amertner/cardcascade/CATALOGUE.md

# Card Cascade catalogue

Every Card Cascade there is, at release **8.0**: 26 designs, each in an
unsleeved and a sleeved version. This page is generated from the CAD
(`make_catalogue.py`), so the sizes and capacities are the ones the parts are
built to.

A Card Cascade is a 3D-printed **store-and-play** box for a card game. Closed,
it is a labelled box on a shelf. Open, its sliding card holders rise in a
staircase so that every pile shows its top card, ready to play, with the big
piles in front pockets. Each cascade is a complete Bambu Studio project: box
and pushers, lid with the game's logo, sliding holders, an optional token
holder, and slide-in labels as a separate project.

## Does one fit your game?

The cascades were designed for four card sizes, one family each. A cascade
fits a game it was never designed for when:

1. **The card is no bigger than the family's card.** The slots are cut for the
   card sizes below (the slot is 3 mm wider than the card, so a card up to
   about 1 mm wider still slides). Cards may be smaller; they just sit lower
   in the slot.
2. **The cards are no thicker.** Capacities are counted at the thickness
   below. Thicker cards mean fewer per slot, not a jam: a slot holding 10
   cards at 0.38 mm holds about 7 at 0.55 mm.
3. **The pile count fits the slots.** One pile per slot, a big pile per front
   pocket: pick a cascade with at least as many slots as you have piles.
4. **It fits your printer.** Every project is laid out for a named bed; a
   cascade for a 256 mm bed prints on anything larger.

## Families by card size

| Family | Unsleeved card, up to | Sleeved card, up to | Card thickness the capacities assume | Box height | Designed for | Files |
|---|---|---|---|---|---|---|
| **Dominion** | 60 x 89 mm | 62 x 92 mm | 0.38 mm unsleeved, 0.60 mm sleeved | 105 mm | Dominion and every expansion; any game with the same 59 x 91 mm card | [MakerWorld](https://makerworld.com/en/models/2957494-card-cascade-dominion-store-play-system) |
| **Food Chain Magnate** | 60 x 89 mm | 62 x 92 mm | 0.38 mm unsleeved, 0.60 mm sleeved | 105 mm | Food Chain Magnate and The Ketchup Mechanism; any game with a 58 x 88 mm card | [MakerWorld](https://makerworld.com/en/models/3053860-food-chain-magnate-card-cascade-system) |
| **Innovation** | 64 x 89 mm | 66 x 92 mm | 0.40 mm unsleeved, 0.65 mm sleeved | 105 mm | Innovation (Ultimate edition and the older ones); any game with a 63 x 88 mm card | [MakerWorld](https://makerworld.com/en/models/3192197-card-cascade-for-innovation-ultimate) |
| **Compile** | 65 x 89 mm | 67 x 92 mm | 0.40 mm unsleeved, 0.80 mm sleeved | 105 mm | Compile: Main 1 and its expansions; any game with a 65 x 92 mm card | [MakerWorld](https://makerworld.com/en/models/3042334-compile-main-aux-system-card-cascade) |

## Dominion

The original family, one cascade per expansion. Kingdom cards go ten to a sliding slot and the front pockets take the big piles (Copper, Curses, Estates). Some boxes merge two front pockets for player mats and every box takes a removable token holder.

| Cascade | Cards | Slots (across x deep) | Cards per slot (pocket / sliding) | Unsleeved: W x D x H mm | Model | Sleeved: W x D x H mm | Model | Printer | Made for | Print profile |
|---|---|---|---|---|---|---|---|---|---|---|
| **168 Card** | 168 | 3 x 5 | 16 / 10 | 208 x 43.6 x 107 | `S4.16.10.32-Un` | 214 x 55.9 x 107 | `S4.16.10.32-Sl` | 256 mm bed (Bambu P1/X1/A1 or similar) | Alchemy, Cornucopia, Guilds | [unsleeved](https://makerworld.com/en/models/2957494-card-cascade-dominion-store-play-system#profileId-3338100) / [sleeved](https://makerworld.com/en/models/2957494-card-cascade-dominion-store-play-system#profileId-3319634) |
| **202 Card (Mat)** | 202 | 4 x 5 | 21 / 10 | 271 x 45.5 x 107 | `M4.21.10.32-M-Un` | 279 x 58.9 x 107 | `M4.21.10.45-M-Sl` | 256 mm bed (Bambu P1/X1/A1 or similar) | Half of a mat expansion, with the mat slot (pairs with a 244 Card) | [unsleeved](https://makerworld.com/en/models/2957494-card-cascade-dominion-store-play-system#profileId-3408201) / [sleeved](https://makerworld.com/en/models/2957494-card-cascade-dominion-store-play-system#profileId-3408188) |
| **244 Card** | 244 | 4 x 5 | 21 / 10 | 271 x 45.5 x 107 | `M4.21.10.32-Un` | 279 x 58.9 x 107 | `M4.21.10.45-Sl` | 256 mm bed (Bambu P1/X1/A1 or similar) | Half of Adventures, Nocturne or Plunder on a 256 mm bed | [unsleeved](https://makerworld.com/en/models/2957494-card-cascade-dominion-store-play-system#profileId-3339013) / [sleeved](https://makerworld.com/en/models/2957494-card-cascade-dominion-store-play-system#profileId-3319882) |
| **246 Card** | 246 | 3 x 3 | 40 / 12/30 | 208 x 48.7 x 107 | `S2.40.12-30.32-Un` | 214 x 66.7 x 107 | `S2.40.12-30.45-Sl` | 256 mm bed (Bambu P1/X1/A1 or similar) | Just the bulky Base Set cards | [unsleeved](https://makerworld.com/en/models/2957494-card-cascade-dominion-store-play-system#profileId-3408409) / [sleeved](https://makerworld.com/en/models/2957494-card-cascade-dominion-store-play-system#profileId-3378738) |
| **290 Card (Mat)** | 290 | 4 x 7 | 21 / 10/12 | 271 x 58.7 x 107 | `M6.21.10-12.45-M-Un` | 279 x 76.9 x 107 | `M6.21.10-12.62-M-Sl` | 256 mm bed (Bambu P1/X1/A1 or similar) | Speculation, with a mat slot | [unsleeved](https://makerworld.com/en/models/2957494-card-cascade-dominion-store-play-system#profileId-3758638) / [sleeved](https://makerworld.com/en/models/2957494-card-cascade-dominion-store-play-system#profileId-3758631) |
| **300 Card** | 300 | 3 x 6 | 40 / 12 | 208 x 62.7 x 107 | `S5.40.12.45-Un` | 214 x 84.7 x 107 | `S5.40.12.62-Sl` | 256 mm bed (Bambu P1/X1/A1 or similar) | Half of the Base Set on a 256 mm bed | [unsleeved](https://makerworld.com/en/models/2957494-card-cascade-dominion-store-play-system#profileId-3338707) / [sleeved](https://makerworld.com/en/models/2957494-card-cascade-dominion-store-play-system#profileId-3338690) |
| **324 Card** | 324 | 4 x 7 | 21 / 10 | 271 x 57.9 x 107 | `M6.21.10.45-Un` | 279 x 75.7 x 107 | `M6.21.10.62-Sl` | 256 mm bed (Bambu P1/X1/A1 or similar) | Intrigue, Seaside, Prosperity, Hinterlands, Empires, Rising Sun | [unsleeved](https://makerworld.com/en/models/2957494-card-cascade-dominion-store-play-system#profileId-3338033) / [sleeved](https://makerworld.com/en/models/2957494-card-cascade-dominion-store-play-system#profileId-3319592) |
| **333 Card** | 333 | 3 x 10 | 21 / 10 | 208 x 76.5 x 107 | `S9.21.10.62-Un` | 214 x 100.9 x 107 | `S9.21.10.62-Sl` | 256 mm bed (Bambu P1/X1/A1 or similar) | A 324-size expansion in a narrower, deeper box for small printers | [unsleeved](https://makerworld.com/en/models/2957494-card-cascade-dominion-store-play-system#profileId-3431683) / [sleeved](https://makerworld.com/en/models/2957494-card-cascade-dominion-store-play-system#profileId-3431676) |
| **400 Card (Mat)** | 400 | 4 x 9 | 40 / 10 | 271 x 77.5 x 107 | `M8.40.10.62-M-Un` | 279 x 103.9 x 107 | `M8.40.10.62-M-Sl` | 256 mm bed unsleeved; 325 x 320 mm bed sleeved | Adventures, Renaissance, Menagerie, Allies | [unsleeved](https://makerworld.com/en/models/2957494-card-cascade-dominion-store-play-system#profileId-3339141) / [sleeved](https://makerworld.com/en/models/2957494-card-cascade-dominion-store-play-system#profileId-3319830) |
| **472 Card** | 472 | 4 x 3 | 60 / 18/40 | 271 x 62.4 x 107 | `M2.60.18-40.45-Un` | 279 x 88.3 x 107 | `M2.60.18-40.62-Sl` | 256 mm bed unsleeved; 325 x 320 mm bed sleeved | Base cards for six players | [unsleeved](https://makerworld.com/en/models/2957494-card-cascade-dominion-store-play-system#profileId-3460482) / [sleeved](https://makerworld.com/en/models/2957494-card-cascade-dominion-store-play-system#profileId-3460478) |
| **560 Card** | 560 | 5 x 7 | 40 / 12 | 334 x 69.7 x 107 | `L6.40.12.45-Un` | 344 x 94.3 x 107 | `L6.40.12.62-Sl` | 325 x 320 mm bed (Bambu H2 series or similar) | Base game | [unsleeved](https://makerworld.com/en/models/2957494-card-cascade-dominion-store-play-system#profileId-3337942) / [sleeved](https://makerworld.com/en/models/2957494-card-cascade-dominion-store-play-system#profileId-3314508) |
| **650 Card** | 650 | 5 x 9 | 50 / 10 | 334 x 81.3 x 107 | `L8.50.10.62-Un` | 344 x 109.9 x 107 | `L8.50.10.62-Sl` | 325 x 320 mm bed (Bambu H2 series or similar) | Dark Ages, Nocturne, Plunder | [unsleeved](https://makerworld.com/en/models/2957494-card-cascade-dominion-store-play-system#profileId-3337884) / [sleeved](https://makerworld.com/en/models/2957494-card-cascade-dominion-store-play-system#profileId-3319758) |

## Food Chain Magnate

Sized for FCM's employee cards: shallow slots (six cards) for the many small piles, and the Milestones box is a separate cascade. The slot is the same width as Dominion's, so any 58-60 mm card fits.

| Cascade | Cards | Slots (across x deep) | Cards per slot (pocket / sliding) | Unsleeved: W x D x H mm | Model | Sleeved: W x D x H mm | Model | Printer | Made for | Print profile |
|---|---|---|---|---|---|---|---|---|---|---|
| **144 Card (Milestones 1)** | 144 | 4 x 6 | 6 / 6 | 271 x 38.4 x 107 | `M5.6.6.20-Un` | 279 x 46.3 x 107 | `M5.6.6.32-Sl` | 256 mm bed (Bambu P1/X1/A1 or similar) | Milestones | [unsleeved](https://makerworld.com/en/models/3053860-food-chain-magnate-card-cascade-system#profileId-3595209) / [sleeved](https://makerworld.com/en/models/3053860-food-chain-magnate-card-cascade-system#profileId-3595208) |
| **180 Card (Occ 2)** | 180 | 5 x 4 | 18 / 6 | 334 x 33.6 x 107 | `L3.18.6.20-Un` | 344 x 41.5 x 107 | `L3.18.6.20-Sl` | 325 x 320 mm bed (Bambu H2 series or similar) | Occupations 2/2 | [unsleeved](https://makerworld.com/en/models/3053860-food-chain-magnate-card-cascade-system#profileId-3435829) / [sleeved](https://makerworld.com/en/models/3053860-food-chain-magnate-card-cascade-system#profileId-3435831) |
| **264 Card (Occ 1)** | 264 | 4 x 5 | 18 / 12 | 271 x 47.4 x 107 | `M4.18.12.32-Un` | 279 x 61.9 x 107 | `M4.18.12.45-Sl` | 256 mm bed (Bambu P1/X1/A1 or similar) | Occupations 1/2 | [unsleeved](https://makerworld.com/en/models/3053860-food-chain-magnate-card-cascade-system#profileId-3435810) / [sleeved](https://makerworld.com/en/models/3053860-food-chain-magnate-card-cascade-system#profileId-3435819) |
| **198 Card (Alt)** | 198 | 3 x 5 | 18 / 12 | 208 x 47.4 x 107 | `S4.18.12.32-Un` | 214 x 61.9 x 107 | `S4.18.12.45-Sl` | 256 mm bed (Bambu P1/X1/A1 or similar) | Occupations 3 | [unsleeved](https://makerworld.com/en/models/3053860-food-chain-magnate-card-cascade-system#profileId-3618240) / [sleeved](https://makerworld.com/en/models/3053860-food-chain-magnate-card-cascade-system#profileId-3580884) |

## Innovation

Ten or fifteen cards to a slot, one age per column. The Ultimate edition's six expansions split across several cascades in three different ways, and the Single Mini is a narrow box for one expansion that fits a 180 mm bed.

| Cascade | Cards | Slots (across x deep) | Cards per slot (pocket / sliding) | Unsleeved: W x D x H mm | Model | Sleeved: W x D x H mm | Model | Printer | Made for | Print profile |
|---|---|---|---|---|---|---|---|---|---|---|
| **3 Ages 5 Expansions** | 270 | 3 x 6 | 15 / 15 | 220 x 60.7 x 107 | `S5.15.15.45-Un` | 226 x 83.2 x 107 | `S5.15.15.62-Sl` | 256 mm bed (Bambu P1/X1/A1 or similar) | Ultimate edition across four boxes, three ages per box | [unsleeved](https://makerworld.com/en/models/3192197-card-cascade-for-innovation-ultimate#profileId-3611650) / [sleeved](https://makerworld.com/en/models/3192197-card-cascade-for-innovation-ultimate#profileId-3611649) |
| **4 Ages 5 Expansions** | 360 | 4 x 6 | 15 / 15 | 287 x 60.7 x 107 | `M5.15.15.45-Un` | 295 x 83.2 x 107 | `M5.15.15.62-Sl` | 256 mm bed unsleeved; 325 x 320 mm bed sleeved | Ultimate edition across three boxes, four ages per box | [unsleeved](https://makerworld.com/en/models/3192197-card-cascade-for-innovation-ultimate#profileId-3611651) / [sleeved](https://makerworld.com/en/models/3192197-card-cascade-for-innovation-ultimate#profileId-3611512) |
| **Single Set** | 135 | 3 x 4 | 15 / 10 | 220 x 37.9 x 107 | `S3.15.10.20-Un` | 226 x 49.2 x 107 | `S3.15.10.32-Sl` | 256 mm bed (Bambu P1/X1/A1 or similar) | The base set or one expansion | [unsleeved](https://makerworld.com/en/models/3192197-card-cascade-for-innovation-ultimate#profileId-3618751) / [sleeved](https://makerworld.com/en/models/3192197-card-cascade-for-innovation-ultimate#profileId-3618752) |
| **Single Mini** | 130 | 2 x 6 | 15 / 10 | 157 x 50.7 x 107 | `XS5.15.10.32-Un` | 157 x 67.0 x 107 | `XS5.15.10.45-Sl` | 180 mm bed (Bambu A1 mini or similar) | One expansion on a 180 mm bed; two boxes per project, used as a pair | [unsleeved](https://makerworld.com/en/models/3192197-card-cascade-for-innovation-ultimate#profileId-3637548) / [sleeved](https://makerworld.com/en/models/3192197-card-cascade-for-innovation-ultimate#profileId-3637543) |
| **3 Later Ages 5 Expansions** | 180 | 3 x 6 | 10 / 10 | 220 x 48.7 x 107 | `S5.10.10.32-Un` | 226 x 63.7 x 107 | `S5.10.10.45-Sl` | 256 mm bed (Bambu P1/X1/A1 or similar) | Ultimate edition across four boxes, ages 2-10 only (ten cards per slot) | [unsleeved](https://makerworld.com/en/models/3192197-card-cascade-for-innovation-ultimate#profileId-3670764) / [sleeved](https://makerworld.com/en/models/3192197-card-cascade-for-innovation-ultimate#profileId-3670763) |
| **4 Later Ages 5 Expansions** | 240 | 4 x 6 | 10 / 10 | 287 x 48.7 x 107 | `M5.10.10.32-Un` | 295 x 63.7 x 107 | `M5.10.10.45-Sl` | 256 mm bed (Bambu P1/X1/A1 or similar) | Ultimate edition across three boxes, ages 2-10 only (ten cards per slot) | [unsleeved](https://makerworld.com/en/models/3192197-card-cascade-for-innovation-ultimate#profileId-3670754) / [sleeved](https://makerworld.com/en/models/3192197-card-cascade-for-innovation-ultimate#profileId-3670745) |
| **Three Expansions** | 408 | 4 x 9 | 16 / 10/16 | 287 x 72.7 x 107 | `M8.16.10-16.45-Un` | 287 x 98.2 x 107 | `M8.16.10-16.62-Sl` | 256 mm bed unsleeved; 325 x 320 mm bed sleeved | Ultimate edition in two boxes that lie flat in the game box | [unsleeved](https://makerworld.com/en/models/3192197-card-cascade-for-innovation-ultimate#profileId-3758404) / [sleeved](https://makerworld.com/en/models/3192197-card-cascade-for-innovation-ultimate#profileId-3758401) |

## Compile

The widest slot in the system and the shallowest: seven cards per slot, one protocol per slot. Ships with a second box without label holders on its last plate.

| Cascade | Cards | Slots (across x deep) | Cards per slot (pocket / sliding) | Unsleeved: W x D x H mm | Model | Sleeved: W x D x H mm | Model | Printer | Made for | Print profile |
|---|---|---|---|---|---|---|---|---|---|---|
| **105 Card** | 105 | 3 x 5 | 7 / 7 | 223 x 36.3 x 107 | `S4.7.7.20-Un` | 229 x 50.3 x 107 | `S4.7.7.32-Sl` | 256 mm bed (Bambu P1/X1/A1 or similar) | Main and 1 extension | [unsleeved](https://makerworld.com/en/models/3042334-compile-main-aux-system-card-cascade#profileId-3445231) / [sleeved](https://makerworld.com/en/models/3042334-compile-main-aux-system-card-cascade#profileId-3445229) |
| **126 Card** | 126 | 3 x 6 | 7 / 7 | 223 x 41.5 x 107 | `S5.7.7.20-Un` | 229 x 58.3 x 107 | `S5.7.7.45-Sl` | 256 mm bed (Bambu P1/X1/A1 or similar) | Main 2, Aux 1 and 2 | [unsleeved](https://makerworld.com/en/models/3042334-compile-main-aux-system-card-cascade#profileId-3421380) / [sleeved](https://makerworld.com/en/models/3042334-compile-main-aux-system-card-cascade#profileId-3421257) |
| **210 Card** | 210 | 5 x 6 | 7 / 7 | 359 x 41.5 x 107 | `L5.7.7.20-Un` | 369 x 58.3 x 107 | `L5.7.7.45-Sl` | 325 x 320 mm bed (Bambu H2 series or similar) | 10 sets, all sets | [unsleeved](https://makerworld.com/en/models/3042334-compile-main-aux-system-card-cascade#profileId-3445251) / [sleeved](https://makerworld.com/en/models/3042334-compile-main-aux-system-card-cascade#profileId-3445246) |

## Dominion: which cascade for which expansion

Every Dominion expansion has a cascade, or a pair of cascades on a printer with
a 256 mm bed. Sleeved cards are thicker, so more sets split on a standard
printer.

### Unsleeved

| Expansion | Large printer | Standard printer |
|---|---|---|
| Base Set | 560 Card | 2 x 300 Card |
| Intrigue | 324 Card | 324 Card |
| Seaside | 324 Card | 324 Card |
| Alchemy | 168 Card | 168 Card |
| Prosperity | 324 Card | 324 Card |
| Cornucopia | 168 Card | 168 Card |
| Hinterlands | 324 Card | 324 Card |
| Dark Ages | 650 Card | 324 Card + 168 Card |
| Guilds | 168 Card | 168 Card |
| Adventures | 400 Card (Mat) | 400 Card (Mat) |
| Empires | 324 Card | 324 Card |
| Nocturne | 650 Card | 2 x 244 Card |
| Renaissance | 400 Card (Mat) | 400 Card (Mat) |
| Menagerie | 400 Card (Mat) | 400 Card (Mat) |
| Allies | 400 Card (Mat) | 400 Card (Mat) |
| Plunder | 650 Card | 324 Card + 244 Card |
| Rising Sun | 324 Card | 324 Card |

### Sleeved

| Expansion | Large printer | Standard printer |
|---|---|---|
| Base Set | 560 Card | 2 x 300 Card |
| Intrigue | 324 Card | 324 Card |
| Seaside | 324 Card | 324 Card |
| Alchemy | 168 Card | 168 Card |
| Prosperity | 324 Card | 324 Card |
| Cornucopia | 168 Card | 168 Card |
| Hinterlands | 324 Card | 324 Card |
| Dark Ages | 650 Card | 324 Card + 168 Card |
| Guilds | 168 Card | 168 Card |
| Adventures | 400 Card (Mat) | 202 Card (Mat) + 244 Card |
| Empires | 324 Card | 324 Card |
| Nocturne | 650 Card | 2 x 244 Card |
| Renaissance | 400 Card (Mat) | 202 Card (Mat) + 244 Card |
| Menagerie | 400 Card (Mat) | 202 Card (Mat) + 244 Card |
| Allies | 400 Card (Mat) | 202 Card (Mat) + 244 Card |
| Plunder | 650 Card | 324 Card + 244 Card |
| Rising Sun | 324 Card | 324 Card |

The Base Set has 60 Copper, and a front pocket takes 40: split the Copper
across two pockets. The 12-card sliding slots of the Base Set cascades are
for Duchy and Province (12 each) and for the 24 Estates across two slots.
Randomiser cards fit in every cascade.

## Reading a model code

`L8.50.10.62-Sl` says everything about a cascade:

| Part | Meaning |
|---|---|
| `L` | Width in slots across: `XS` 2, `S` 3, `M` 4, `L` 5 |
| `8` | Sliding card holders (rows behind the front pockets) |
| `50` | Cards per front pocket |
| `10` | Cards per sliding slot; `12-30` when the first row behind the pockets is deeper |
| `62` | Width of the side label, mm |
| `-M` | Two front pockets merged for player mats |
| `Sl` / `Un` | Sleeved or unsleeved cards |
| `86-` | A height-class prefix: the box is 86 mm tall instead of 105 |

The same code is on every part, engraved in the box floor and on the lid, so
boxes, lids, holders and pushers always match.

All the listings: the [Card Cascades collection](https://makerworld.com/en/collections/33559137-card-cascades) on
MakerWorld. Questions, requests for another game, and prints:
[r/cardcascade](https://www.reddit.com/r/cardcascade/). Source and CAD: [https://github.com/amertner/cardcascade](https://github.com/amertner/cardcascade).
