amertner/cardcascade/outreach/catalogue-reddit.md

# Will Card Cascade work with your game? Here’s how to check

I originally designed Card Cascade for Dominion and then expanded it to other games. There are now **52 configurations**, and many of those work just as well for games they were not designed for.

A Card Cascade is a free, 3D-printed store-and-play box: Open it and the card holders slide up into a staircase, keeping every card pile organised and visible. Collapse it back down and close it so it fits nicely on the shelf and stacks well. You can see the per-game [Card Cascade collection on MakerWorld](https://makerworld.com/en/collections/33559137-card-cascades) and a catalogue for matching with other games below.

To work out whether Card Cascade can be used for your game, you need to check three things:

1. **Card width.** The existing Cascades fit cards up to 60, 62, 64, 65, 66 or 67 mm wide, including sleeves if you use those. Narrower cards fit too, they just have a little more side-to-side play.
2. **Number and size of piles.** The catalogue shows how many front pockets and sliding slots each Cascade has, plus the depth available for each stack. The front pockets don't move up and down and sometimes are deeper than the sliding ones to accommodate bigger card sets.
3. **Card thickness.** The card counts are based on the cards each Cascade was designed for. Measure ten of your own cards together and the catalogue tells you how many will fit (see “Working out the needed slot depth” below).

Every Cascade takes cards that are **81 to 95.5 mm tall**, including sleeves. Shorter cards probably sit too low in the slot to be able to grip them. The Cascades were originally designed around cards that were 88–92 mm tall without sleeves.

On MakerWorld, most Cascades have a **“sleeved”** and an **“unsleeved”** variant. For other games, they simply represent different slot widths and depths. Use whichever dimensions fit your cards.

If none of the 52 configurations works, reply with your **game name, card width and height, the thickness of ten cards, and the number and size of the piles**. The design is parametric, so if a new configuration would be useful to several people, I’m happy to add it.

What game would *you* use Card Cascade for?

## How to read the catalogue

There is a table for each maximum card width. Start with the first heading your card fits under, then look for a row with enough slots and stack depth for the game. Some games may need multiple Cascades to fit all of the cards.

“Slots across x deep” gives the **number of pockets across** and the number of rows from front to back. The first row is the front pockets; the remaining rows are sliding slots. Outside dimensions are for the closed Cascade. The height is the same for every row in a table and is given above it. “Design thickness” is the thickness of ten of the cards each Cascade was designed around, and the capacity in brackets is how many of those cards it holds.

For example, if your game has 20 different sets of cards that are 62 mm wide, one of the "4 x 5" Cascade profiles could be right for you.

### Working out the needed slot depth

Each configuration has a **Front Pocket Depth** and a **Sliding Slot Depth**. To turn a depth into cards, measure ten of your cards together with a ruler or caliper (in sleeves, if you use them). Then use:

    cards per slot = slot depth in mm x 10 / thickness of ten cards in mm

Round down. For example, the Dominion 324 Card configuration under 62 mm has a 12.6 mm pocket, designed for cards that measure 6.0 mm per ten, so it holds 21. Cards measuring 7.5 mm per ten would fit 16 in the same pocket (12.6 x 10 / 7.5 = 16.8).

A stack a few tenths of a millimetre over may still fit because there is clearance in front for lifting it, but I wouldn’t rely on more than that.

### Printer sizes

The “3D Printer bed width / model” column gives the bed size the project is laid out for and the Bambu range that has it. “256/P1” prints on a Bambu P1, X1 or A1, or any other printer with a 256 mm bed. “325/H2” needs an H2-series printer or a bed of at least 325 x 320 mm. “180/A1 mini” fits the A1 mini’s 180 mm bed. A project laid out for a smaller bed will also print on a larger one.

### How to customize the print

The print profiles include a lid that contains the original game's logo, but also includes a lid without a logo. You can print the blank lid and add a sticker/label, or you can modify it before printing.

Most Cascades also have room for a front and a side label, and there are blank labels available for you to download, add some text to, and print.

Everything else is the same as for the standard games: You will need a box, 2 pushers, and the right combination of front, rear and default sliders to make up the whole Cascade.

## Complete configuration catalogue

### Cards up to 60 mm wide

The slot is 63 mm; designed for Dominion, Food Chain Magnate. All Cascades are 107 mm tall.

| Slots across x deep | Front pocket depth/mm | Sliding slot depth/mm | Closed W × D (mm) | 3D Printer bed width / model | Design thickness: mm/10 cards (capacity) | Cascade download link |
|---|---|---|---|---|---|---|
| 3 x 3 | 15.2 | 4.6 (11.4 first row) | 208 x 48.7 | 256/P1 | 3.8 (246 cards) | [Dominion 246 Card](https://makerworld.com/en/models/2957494-card-cascade-dominion-store-play-system#profileId-3408409) |
| 4 x 3 | 22.8 | 6.9 (15.2 first row) | 271 x 62.4 | 256/P1 | 3.8 (472 cards) | [Dominion 472 Card](https://makerworld.com/en/models/2957494-card-cascade-dominion-store-play-system#profileId-3460482) |
| 3 x 5 | 6.1 | 3.8 | 208 x 43.6 | 256/P1 | 3.8 (168 cards) | [Dominion 168 Card](https://makerworld.com/en/models/2957494-card-cascade-dominion-store-play-system#profileId-3338100) |
| 3 x 5 | 6.9 | 4.6 | 208 x 47.4 | 256/P1 | 3.8 (198 cards) | [Food Chain Magnate 198 Card (Alt)](https://makerworld.com/en/models/3053860-food-chain-magnate-card-cascade-system#profileId-3618240) |
| 3 x 6 | 15.2 | 4.6 | 208 x 62.7 | 256/P1 | 3.8 (300 cards) | [Dominion 300 Card](https://makerworld.com/en/models/2957494-card-cascade-dominion-store-play-system#profileId-3338707) |
| 5 x 4 | 6.9 | 2.3 | 334 x 33.6 | 325/H2 | 3.8 (180 cards) | [Food Chain Magnate 180 Card (Occ 2)](https://makerworld.com/en/models/3053860-food-chain-magnate-card-cascade-system#profileId-3435829) |
| 4 x 5 | 6.9 | 4.6 | 271 x 47.4 | 256/P1 | 3.8 (264 cards) | [Food Chain Magnate 264 Card (Occ 1)](https://makerworld.com/en/models/3053860-food-chain-magnate-card-cascade-system#profileId-3435810) |
| 4 x 5 | 8.0 | 3.8 | 271 x 45.5 | 256/P1 | 3.8 (202 cards) | [Dominion 202 Card (Mat)](https://makerworld.com/en/models/2957494-card-cascade-dominion-store-play-system#profileId-3408201) |
| 4 x 5 | 8.0 | 3.8 | 271 x 45.5 | 256/P1 | 3.8 (244 cards) | [Dominion 244 Card](https://makerworld.com/en/models/2957494-card-cascade-dominion-store-play-system#profileId-3339013) |
| 4 x 6 | 2.3 | 2.3 | 271 x 38.4 | 256/P1 | 3.8 (144 cards) | [Food Chain Magnate 144 Card (Milestones 1)](https://makerworld.com/en/models/3053860-food-chain-magnate-card-cascade-system#profileId-3595209) |
| 4 x 7 | 8.0 | 3.8 (4.6 first row) | 271 x 58.7 | 256/P1 | 3.8 (290 cards) | [Dominion 290 Card (Mat)](https://makerworld.com/en/models/2957494-card-cascade-dominion-store-play-system#profileId-3758638) |
| 4 x 7 | 8.0 | 3.8 | 271 x 57.9 | 256/P1 | 3.8 (324 cards) | [Dominion 324 Card](https://makerworld.com/en/models/2957494-card-cascade-dominion-store-play-system#profileId-3338033) |
| 3 x 10 | 8.0 | 3.8 | 208 x 76.5 | 256/P1 | 3.8 (333 cards) | [Dominion 333 Card](https://makerworld.com/en/models/2957494-card-cascade-dominion-store-play-system#profileId-3431683) |
| 5 x 7 | 15.2 | 4.6 | 334 x 69.7 | 325/H2 | 3.8 (560 cards) | [Dominion 560 Card](https://makerworld.com/en/models/2957494-card-cascade-dominion-store-play-system#profileId-3337942) |
| 4 x 9 | 15.2 | 3.8 | 271 x 77.5 | 256/P1 | 3.8 (400 cards) | [Dominion 400 Card (Mat)](https://makerworld.com/en/models/2957494-card-cascade-dominion-store-play-system#profileId-3339141) |
| 5 x 9 | 19.0 | 3.8 | 334 x 81.3 | 325/H2 | 3.8 (650 cards) | [Dominion 650 Card](https://makerworld.com/en/models/2957494-card-cascade-dominion-store-play-system#profileId-3337884) |

### Cards up to 62 mm wide

The slot is 65 mm; designed for Dominion, Food Chain Magnate. All Cascades are 107 mm tall.

| Slots across x deep | Front pocket depth/mm | Sliding slot depth/mm | Closed W × D (mm) | 3D Printer bed width / model | Design thickness: mm/10 cards (capacity) | Cascade download link |
|---|---|---|---|---|---|---|
| 3 x 3 | 24.0 | 7.2 (18.0 first row) | 214 x 66.7 | 256/P1 | 6.0 (246 cards) | [Dominion 246 Card](https://makerworld.com/en/models/2957494-card-cascade-dominion-store-play-system#profileId-3378738) |
| 4 x 3 | 36.0 | 10.8 (24.0 first row) | 279 x 88.3 | 325/H2 | 6.0 (472 cards) | [Dominion 472 Card](https://makerworld.com/en/models/2957494-card-cascade-dominion-store-play-system#profileId-3460478) |
| 3 x 5 | 9.6 | 6.0 | 214 x 55.9 | 256/P1 | 6.0 (168 cards) | [Dominion 168 Card](https://makerworld.com/en/models/2957494-card-cascade-dominion-store-play-system#profileId-3319634) |
| 3 x 5 | 10.8 | 7.2 | 214 x 61.9 | 256/P1 | 6.0 (198 cards) | [Food Chain Magnate 198 Card (Alt)](https://makerworld.com/en/models/3053860-food-chain-magnate-card-cascade-system#profileId-3580884) |
| 3 x 6 | 24.0 | 7.2 | 214 x 84.7 | 256/P1 | 6.0 (300 cards) | [Dominion 300 Card](https://makerworld.com/en/models/2957494-card-cascade-dominion-store-play-system#profileId-3338690) |
| 5 x 4 | 10.8 | 3.6 | 344 x 41.5 | 325/H2 | 6.0 (180 cards) | [Food Chain Magnate 180 Card (Occ 2)](https://makerworld.com/en/models/3053860-food-chain-magnate-card-cascade-system#profileId-3435831) |
| 4 x 5 | 10.8 | 7.2 | 279 x 61.9 | 256/P1 | 6.0 (264 cards) | [Food Chain Magnate 264 Card (Occ 1)](https://makerworld.com/en/models/3053860-food-chain-magnate-card-cascade-system#profileId-3435819) |
| 4 x 5 | 12.6 | 6.0 | 279 x 58.9 | 256/P1 | 6.0 (202 cards) | [Dominion 202 Card (Mat)](https://makerworld.com/en/models/2957494-card-cascade-dominion-store-play-system#profileId-3408188) |
| 4 x 5 | 12.6 | 6.0 | 279 x 58.9 | 256/P1 | 6.0 (244 cards) | [Dominion 244 Card](https://makerworld.com/en/models/2957494-card-cascade-dominion-store-play-system#profileId-3319882) |
| 4 x 6 | 3.6 | 3.6 | 279 x 46.3 | 256/P1 | 6.0 (144 cards) | [Food Chain Magnate 144 Card (Milestones 1)](https://makerworld.com/en/models/3053860-food-chain-magnate-card-cascade-system#profileId-3595208) |
| 4 x 7 | 12.6 | 6.0 (7.2 first row) | 279 x 76.9 | 256/P1 | 6.0 (290 cards) | [Dominion 290 Card (Mat)](https://makerworld.com/en/models/2957494-card-cascade-dominion-store-play-system#profileId-3758631) |
| 4 x 7 | 12.6 | 6.0 | 279 x 75.7 | 256/P1 | 6.0 (324 cards) | [Dominion 324 Card](https://makerworld.com/en/models/2957494-card-cascade-dominion-store-play-system#profileId-3319592) |
| 3 x 10 | 12.6 | 6.0 | 214 x 100.9 | 256/P1 | 6.0 (333 cards) | [Dominion 333 Card](https://makerworld.com/en/models/2957494-card-cascade-dominion-store-play-system#profileId-3431676) |
| 5 x 7 | 24.0 | 7.2 | 344 x 94.3 | 325/H2 | 6.0 (560 cards) | [Dominion 560 Card](https://makerworld.com/en/models/2957494-card-cascade-dominion-store-play-system#profileId-3314508) |
| 4 x 9 | 24.0 | 6.0 | 279 x 103.9 | 325/H2 | 6.0 (400 cards) | [Dominion 400 Card (Mat)](https://makerworld.com/en/models/2957494-card-cascade-dominion-store-play-system#profileId-3319830) |
| 5 x 9 | 30.0 | 6.0 | 344 x 109.9 | 325/H2 | 6.0 (650 cards) | [Dominion 650 Card](https://makerworld.com/en/models/2957494-card-cascade-dominion-store-play-system#profileId-3319758) |

### Cards up to 64 mm wide

The slot is 67 mm; designed for Innovation. All Cascades are 107 mm tall.

| Slots across x deep | Front pocket depth/mm | Sliding slot depth/mm | Closed W × D (mm) | 3D Printer bed width / model | Design thickness: mm/10 cards (capacity) | Cascade download link |
|---|---|---|---|---|---|---|
| 3 x 4 | 6.0 | 4.0 | 220 x 37.9 | 256/P1 | 4.0 (135 cards) | [Innovation Single Set](https://makerworld.com/en/models/3192197-card-cascade-for-innovation-ultimate#profileId-3618751) |
| 3 x 6 | 4.0 | 4.0 | 220 x 48.7 | 256/P1 | 4.0 (180 cards) | [Innovation 3 Later Ages 5 Expansions](https://makerworld.com/en/models/3192197-card-cascade-for-innovation-ultimate#profileId-3670764) |
| 3 x 6 | 6.0 | 6.0 | 220 x 60.7 | 256/P1 | 4.0 (270 cards) | [Innovation 3 Ages 5 Expansions](https://makerworld.com/en/models/3192197-card-cascade-for-innovation-ultimate#profileId-3611650) |
| 4 x 6 | 4.0 | 4.0 | 287 x 48.7 | 256/P1 | 4.0 (240 cards) | [Innovation 4 Later Ages 5 Expansions](https://makerworld.com/en/models/3192197-card-cascade-for-innovation-ultimate#profileId-3670754) |
| 4 x 6 | 6.0 | 6.0 | 287 x 60.7 | 256/P1 | 4.0 (360 cards) | [Innovation 4 Ages 5 Expansions](https://makerworld.com/en/models/3192197-card-cascade-for-innovation-ultimate#profileId-3611651) |
| 4 x 9 | 6.4 | 4.0 (6.4 first row) | 287 x 72.7 | 256/P1 | 4.0 (408 cards) | [Innovation Three Expansions](https://makerworld.com/en/models/3192197-card-cascade-for-innovation-ultimate#profileId-3758404) |
| 4 x 9 | 10.4 | 6.5 (10.4 first row) | 287 x 98.2 | 325/H2 | 6.5 (408 cards) | [Innovation Three Expansions](https://makerworld.com/en/models/3192197-card-cascade-for-innovation-ultimate#profileId-3758401) |

### Cards up to 65 mm wide

The slot is 68 mm; designed for Compile. All Cascades are 107 mm tall.

| Slots across x deep | Front pocket depth/mm | Sliding slot depth/mm | Closed W × D (mm) | 3D Printer bed width / model | Design thickness: mm/10 cards (capacity) | Cascade download link |
|---|---|---|---|---|---|---|
| 3 x 5 | 2.8 | 2.8 | 223 x 36.3 | 256/P1 | 4.0 (105 cards) | [Compile 105 Card](https://makerworld.com/en/models/3042334-compile-main-aux-system-card-cascade#profileId-3445231) |
| 3 x 6 | 2.8 | 2.8 | 223 x 41.5 | 256/P1 | 4.0 (126 cards) | [Compile 126 Card](https://makerworld.com/en/models/3042334-compile-main-aux-system-card-cascade#profileId-3421380) |
| 5 x 6 | 2.8 | 2.8 | 359 x 41.5 | 325/H2 | 4.0 (210 cards) | [Compile 210 Card](https://makerworld.com/en/models/3042334-compile-main-aux-system-card-cascade#profileId-3445251) |

### Cards up to 66 mm wide

The slot is 69 mm; designed for Innovation. All Cascades are 107 mm tall.

| Slots across x deep | Front pocket depth/mm | Sliding slot depth/mm | Closed W × D (mm) | 3D Printer bed width / model | Design thickness: mm/10 cards (capacity) | Cascade download link |
|---|---|---|---|---|---|---|
| 2 x 6 | 6.0 | 4.0 | 157 x 50.7 | 180/A1 mini | 4.0 (130 cards) | [Innovation Single Mini](https://makerworld.com/en/models/3192197-card-cascade-for-innovation-ultimate#profileId-3637548) |
| 3 x 4 | 9.8 | 6.5 | 226 x 49.2 | 256/P1 | 6.5 (135 cards) | [Innovation Single Set](https://makerworld.com/en/models/3192197-card-cascade-for-innovation-ultimate#profileId-3618752) |
| 2 x 6 | 9.8 | 6.5 | 157 x 67.0 | 180/A1 mini | 6.5 (130 cards) | [Innovation Single Mini](https://makerworld.com/en/models/3192197-card-cascade-for-innovation-ultimate#profileId-3637543) |
| 3 x 6 | 6.5 | 6.5 | 226 x 63.7 | 256/P1 | 6.5 (180 cards) | [Innovation 3 Later Ages 5 Expansions](https://makerworld.com/en/models/3192197-card-cascade-for-innovation-ultimate#profileId-3670763) |
| 3 x 6 | 9.8 | 9.8 | 226 x 83.2 | 256/P1 | 6.5 (270 cards) | [Innovation 3 Ages 5 Expansions](https://makerworld.com/en/models/3192197-card-cascade-for-innovation-ultimate#profileId-3611649) |
| 4 x 6 | 6.5 | 6.5 | 295 x 63.7 | 256/P1 | 6.5 (240 cards) | [Innovation 4 Later Ages 5 Expansions](https://makerworld.com/en/models/3192197-card-cascade-for-innovation-ultimate#profileId-3670745) |
| 4 x 6 | 9.8 | 9.8 | 295 x 83.2 | 325/H2 | 6.5 (360 cards) | [Innovation 4 Ages 5 Expansions](https://makerworld.com/en/models/3192197-card-cascade-for-innovation-ultimate#profileId-3611512) |

### Cards up to 67 mm wide

The slot is 70 mm; designed for Compile. All Cascades are 107 mm tall.

| Slots across x deep | Front pocket depth/mm | Sliding slot depth/mm | Closed W × D (mm) | 3D Printer bed width / model | Design thickness: mm/10 cards (capacity) | Cascade download link |
|---|---|---|---|---|---|---|
| 3 x 5 | 5.6 | 5.6 | 229 x 50.3 | 256/P1 | 8.0 (105 cards) | [Compile 105 Card](https://makerworld.com/en/models/3042334-compile-main-aux-system-card-cascade#profileId-3445229) |
| 3 x 6 | 5.6 | 5.6 | 229 x 58.3 | 256/P1 | 8.0 (126 cards) | [Compile 126 Card](https://makerworld.com/en/models/3042334-compile-main-aux-system-card-cascade#profileId-3421257) |
| 5 x 6 | 5.6 | 5.6 | 369 x 58.3 | 325/H2 | 8.0 (210 cards) | [Compile 210 Card](https://makerworld.com/en/models/3042334-compile-main-aux-system-card-cascade#profileId-3445246) |
