amertner/cardcascade/Cascade Sizes.docx

## Cascade Sizes

Just 8 different Cascade sizes cover all Dominion Expansions. Depending on what printer you have, you'll need to print a maximum of 6 different ones. In addition, some boxes that can be used if you don't organise your expansions by set will be added over time. This document describes Card Cascade v6.0, which adds standardised slide-in labels to every box.

Card Cascade | Used by | Large printer | Standard printer
168 Card | Alchemy, Cornucopia, Guilds, Dark Ages 2/2 | ✓ | ✓
244 Card | Adventures x2, Nocturne x2, Plunder 2/2 | | ✓
300 Card | Base Set across 2 boxes | | ✓
324 Card | Intrigue, Seaside, Prosperity, Hinterlands, Empires, Rising Sun, Dark Ages 1/2, Plunder 1/2 | ✓ | ✓
400 Card | Adventures, Renaissance, Menagerie, Allies | ✓ | ✓ (Unsleeved)
560 Card | Base Set | ✓
650 Card | Dark Ages, Nocturne, Plunder | ✓
246 Card | Just the bulky cards from the Base set | ✓ | ✓

## Choosing the right Cascades

Card Cascade is available in versions for both sleeved and unsleeved cards. Both versions hold the same number of cards, but the sleeved versions are physically larger to accommodate the thicker and wider cards.

If your printer has a standard 256 × 256 mm build area (for example a Bambu Lab P1S or X1C), the Base Set and some larger expansions are split across two Cascades instead.

If your printer has a larger build area of at least 325 × 320 mm (for example a Bambu Lab H2S, H2D or H2C), every Dominion expansion fits in a single Cascade.

Cascades are identified by their maximum card capacity (for example 324 Card or 650 Card). The exact model number is shown in brackets.

### Unsleeved cards

Unsleeved, all but the Base set and the largest expansions fit in a single Cascade:

Expansion | Larger printer | Standard printer
Base Set | 560 Card (L6.40.12.45-Un) | 2 × 300 Card (S5.40.12.45-Un)
Intrigue | 324 Card (M6.21.10.45-Un) | 324 Card (M6.21.10.45-Un)
Seaside | 324 Card (M6.21.10.45-Un) | 324 Card (M6.21.10.45-Un)
Alchemy | 168 Card (S4.16.10.32-Un) | 168 Card (S4.16.10.32-Un)
Prosperity | 324 Card (M6.21.10.45-Un) | 324 Card (M6.21.10.45-Un)
Cornucopia | 168 Card (S4.16.10.32-Un) | 168 Card (S4.16.10.32-Un)
Hinterlands | 324 Card (M6.21.10.45-Un) | 324 Card (M6.21.10.45-Un)
Dark Ages | 650 Card (L8.50.10.62-Un) | 324 + 168 Card (M6.21.10.45-Un + S4.16.10.32-Un)
Guilds | 168 Card (S4.16.10.32-Un) | 168 Card (S4.16.10.32-Un)
Adventures | 400 Card (M8.40.10.62-M-Un) | 400 Card (M8.40.10.62-M-Un)
Empires | 324 Card (M6.21.10.45-Un) | 324 Card (M6.21.10.45-Un)
Nocturne | 650 Card (L8.50.10.62-Un) | 2 × 244 Card (M4.21.10.32-Un)
Renaissance | 400 Card (M8.40.10.62-M-Un) | 400 Card (M8.40.10.62-M-Un)
Menagerie | 400 Card (M8.40.10.62-M-Un) | 400 Card (M8.40.10.62-M-Un)
Allies | 400 Card (M8.40.10.62-M-Un) | 400 Card (M8.40.10.62-M-Un)
Plunder | 650 Card (L8.50.10.62-Un) | 324 + 244 Card (M6.21.10.45-Un + M4.21.10.32-Un)
Rising Sun | 324 Card (M6.21.10.45-Un) | 324 Card (M6.21.10.45-Un)
Arcana | TBD | TBD

### Sleeved cards

The sleeved Cascades are physically larger to accommodate the thicker and wider cards, so more sets need to be split across two Cascades if you have a standard printer:

Expansion | Larger printer | Standard printer
Base Set | 560 Card (L6.40.12.62-Sl) | 2 × 300 Card (S5.40.12.62-Sl)
Intrigue | 324 Card (M6.21.10.62-Sl) | 324 Card (M6.21.10.62-Sl)
Seaside | 324 Card (M6.21.10.62-Sl) | 324 Card (M6.21.10.62-Sl)
Alchemy | 168 Card (S4.16.10.32-Sl) | 168 Card (S4.16.10.32-Sl)
Prosperity | 324 Card (M6.21.10.62-Sl) | 324 Card (M6.21.10.62-Sl)
Cornucopia | 168 Card (S4.16.10.32-Sl) | 168 Card (S4.16.10.32-Sl)
Hinterlands | 324 Card (M6.21.10.62-Sl) | 324 Card (M6.21.10.62-Sl)
Dark Ages | 650 Card (L8.50.10.62-Sl) | 324 + 168 Card (M6.21.10.62-Sl + S4.16.10.32-Sl)
Guilds | 168 Card (S4.16.10.32-Sl) | 168 Card (S4.16.10.32-Sl)
Adventures | 400 Card (M8.40.10.62-M-Sl) | 202 + 244 Card (M4.21.10.45-M-Sl + M4.21.10.45-Sl)
Empires | 324 Card (M6.21.10.62-Sl) | 324 Card (M6.21.10.62-Sl)
Nocturne | 650 Card (L8.50.10.62-Sl) | 2 × 244 Card (M4.21.10.45-Sl)
Renaissance | 400 Card (M8.40.10.62-M-Sl) | 202 + 244 Card (M4.21.10.45-M-Sl + M4.21.10.45-Sl)
Menagerie | 400 Card (M8.40.10.62-M-Sl) | 202 + 244 Card (M4.21.10.45-M-Sl + M4.21.10.45-Sl)
Allies | 400 Card (M8.40.10.62-M-Sl) | 202 + 244 Card (M4.21.10.45-M-Sl + M4.21.10.45-Sl)
Plunder | 650 Card (L8.50.10.62-Sl) | 324 + 244 Card (M6.21.10.62-Sl + M4.21.10.45-Sl)
Rising Sun | 324 Card (M6.21.10.62-Sl) | 324 Card (M6.21.10.62-Sl)
Arcana | TBD | TBD

### A note on the base set

There are 60 Copper, 40 Silver and 30 Gold in the base set, and the Cascade only makes room for 40 cards in the front pocket. You therefore need split the Copper across two pockets.

If you're printing the single-Cascade version, note that the card sliders have room for 12 cards each rather than the standard 10. This is to allow you to store Duchy and Province cards (12 each) in sliders, and to store the 24 Estate cards across two sliding slots.

### A note on Randomisers

There is room for the Randomizer cards in every Cascade. Personally I prefer to keep them unsleeved, as they undergo much less wear than the Kingdom cards and are less likely to be mixed into the game accidentally. Sleeved Randomizers should also fit, although I haven’t tested this.

### A note on Mats and Tokens

Some expansions include player mats and/or tokens. To accommodate this, some of the designs merge the two rightmost front pockets so they can be used for player mats. For all of the designs, I have included a removable token holder that can hold up to two types of token.

Renaissance is an interesting example as it includes both. Therefore, the 400-box design includes a half-depth token holder so you can slide the player mats and a half-depth token holder into the large right hand slot and have it all fit beautifully.

### A note on Labels

Each box has room for a slide-in label in front and on the side. The front label is the same size for all boxes, which makes it nice and easy.

As of v6.0, side labels come in a small number of standard widths – 32, 45 and 62 mm for Dominion – and every box takes one of these standard sizes. The label width is part of the box’s model number (the fourth number), so for example an M6.21.10.45-Un box takes the 45 mm side label.

Labels are available as a separate print profile for each expansion, named after the set (for example “Seaside Labels”). Each profile contains ready-to-print plates: labels for the single-Cascade version (unsleeved and sleeved), labels for the split two-Cascade versions where those exist, and a plate of spares. Every plate name spells out the set, the sleeving and the exact box model it fits, so simply print the plate that matches your box. The labels print in two colours – the base plate in one filament, the raised name and logo in another – with the filament assignments already set up in the profile.

v6.0 is backwards compatible with v5.1: the boxes have the same external dimensions and take the same lids, sliding card holders, pushers and token holders. There is no need to reprint anything you have already printed – blank side labels in the original v5.1 sizes (Small, Medium and Large boxes) remain available in the Blank Labels profile, so existing boxes can be labelled just as before. If you would like the new standard-width labels, simply reprint the box.

## Card Cascade model numbers

Every Cascade has a unique model designation like L8.50.10.62-Sl. This is what it means:

- L = Large width, i.e. 5 horizontal card slots. Medium is 4, Small is 3.
- 8 = Eight sliding card holders.
- 50 = Capacity of each front pocket
- 10 = Capacity of each holder slot, normally 10 for Kingdom cards.
- 62 = Width of the side label in mm.
  - If the capacity is variable (the first slot can be different), it is shown with an additional -30, as in the 246 Card box (S2.40.12-30).
- Sl = Sleeved cards (Un = Unsleeved)
- -M = When two front slots are merged to hold Player Mats instead of cards.

The same designation is used consistently throughout the system so that boxes, lids, pushers, holders and accessories can always be matched correctly.

Cascades are also identified by their maximum card capacity (for example 168 Cards or 650 Cards) to make them easier to distinguish at a glance. You will typically not fill them to capacity, as the front slots are calibrated to hold the biggest number needed, even if other card types have fewer cards.

## Printing Card Cascade

Each Cascade is supplied as a complete 3MF project with organized build plates:

1. Box and required pushers
2. Lid with Dominion logo
3. Sliding card holders
4. Optional token holder (Only needed for a few sets)

The plates are pre-arranged for printing and include colour changes where appropriate for logos. Labels are printed separately from the matching label profile – see “A note on Labels” above.

### Colour the sets differently

If possible, use a different colour lid for each set, and use that same colour on the labels. This makes each set visually distinct.

## Assembly

Print the required parts, then do the following:

1. Insert the front and side labels, making sure they are snug so they don't fall out.
2. Insert the sliding card holders in the box
3. Hang the pushers so they fall into their storage compartment at the back of the box
4. Add the cards to the box

Enjoy!
