amertner/cardcascade/cascades/Compile/Compile 105 Card Sleeved (S4.7.7.32-Sl).png

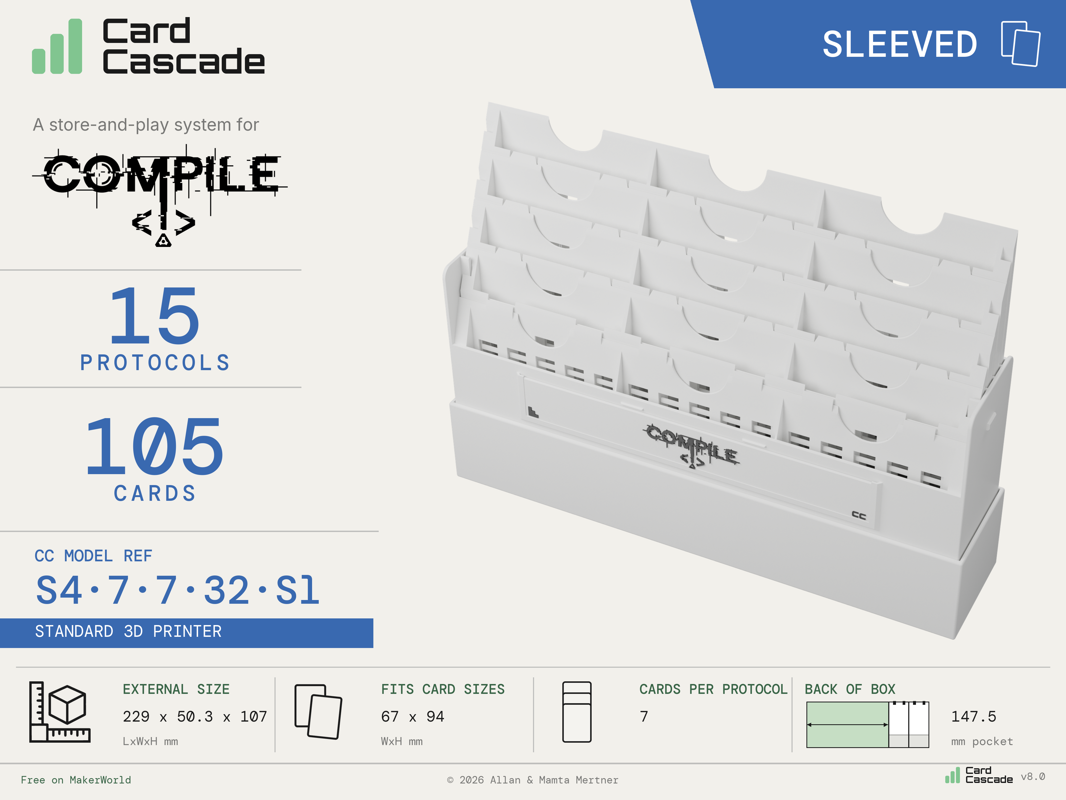
cascades/Compile/Compile 105 Card Sleeved (S4.7.7.32-Sl).png
