amertner/cardcascade/cascades/Compile/Compile 126 Card Sleeved (S5.7.7.45-Sl).png

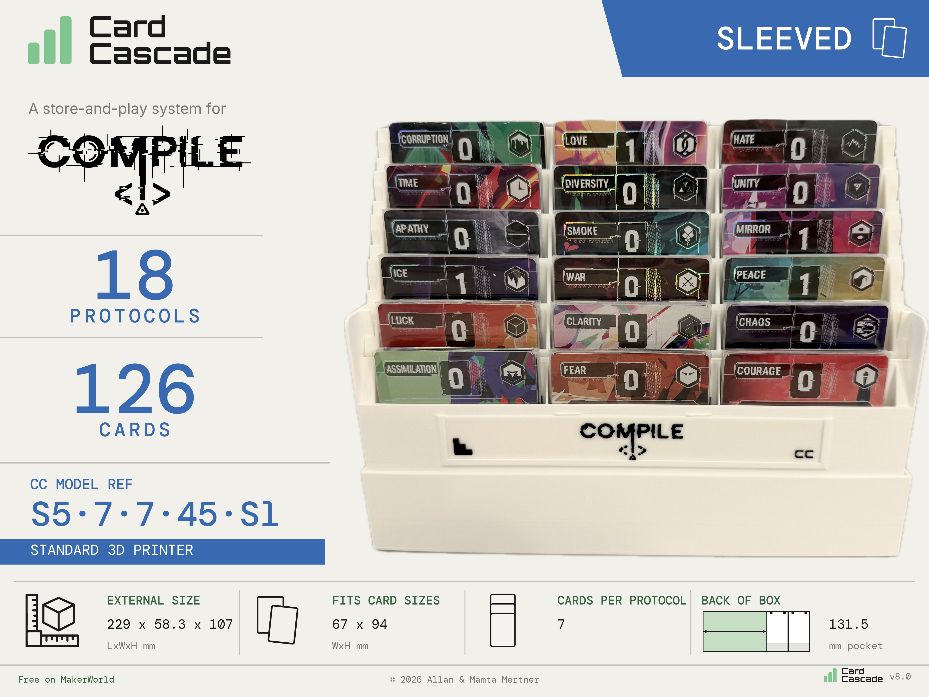
cascades/Compile/Compile 126 Card Sleeved (S5.7.7.45-Sl).png
