amertner/cardcascade/cascades/Compile/Compile 210 Card Sleeved (L5.7.7.45-Sl).png

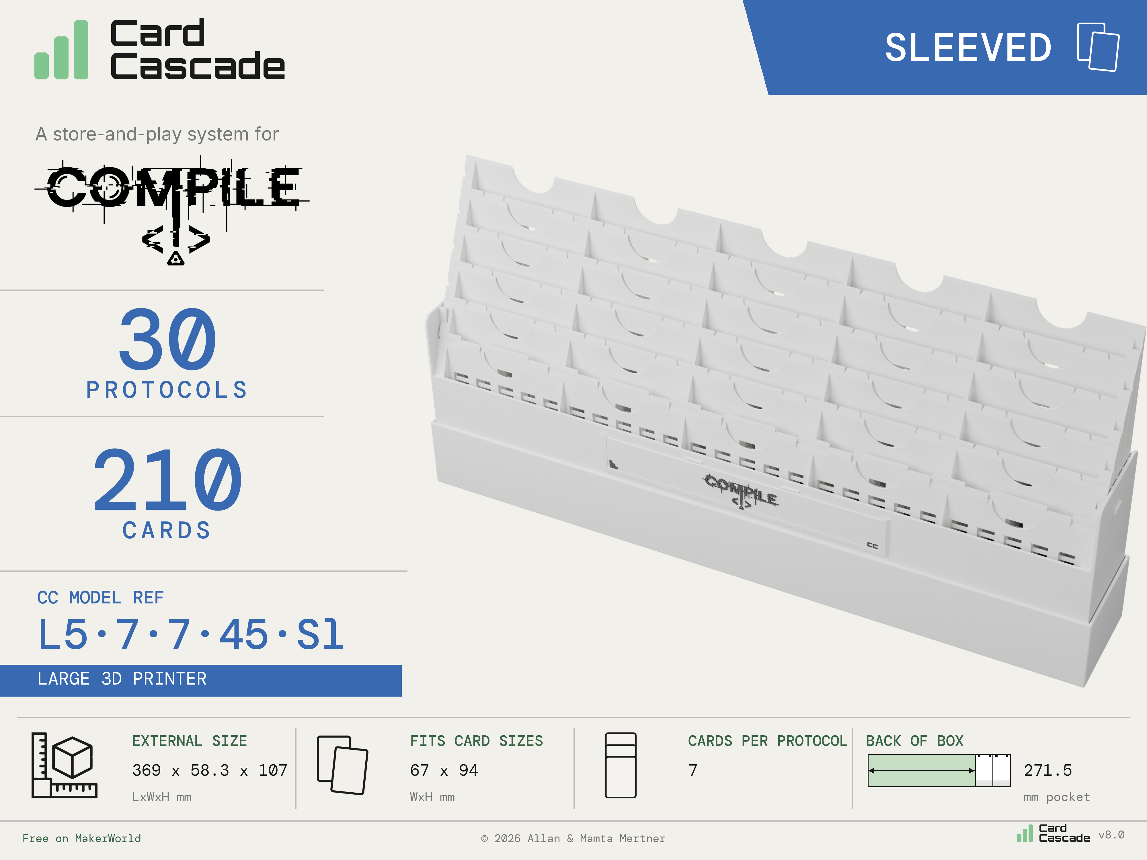
cascades/Compile/Compile 210 Card Sleeved (L5.7.7.45-Sl).png
