amertner/cardcascade/cascades/Compile/Compile Hero Landscape.png

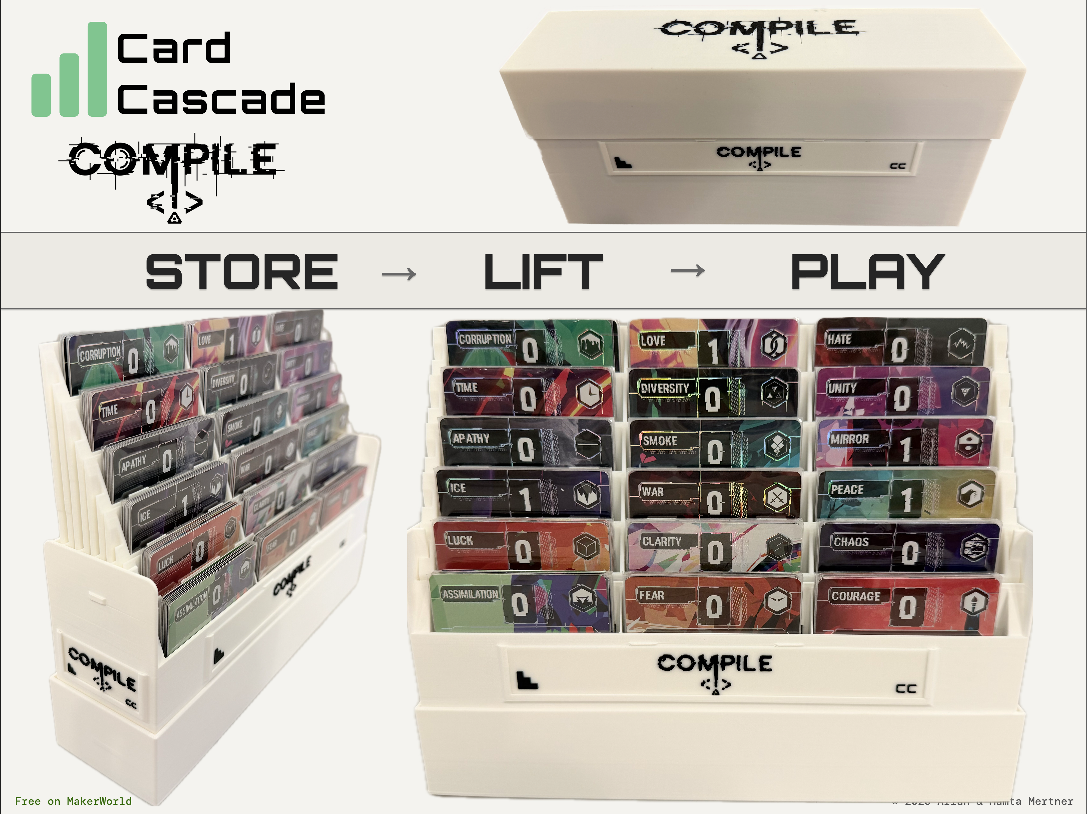
cascades/Compile/Compile Hero Landscape.png
