amertner/cardcascade/cascades/Compile/Compile Hero Portrait.png

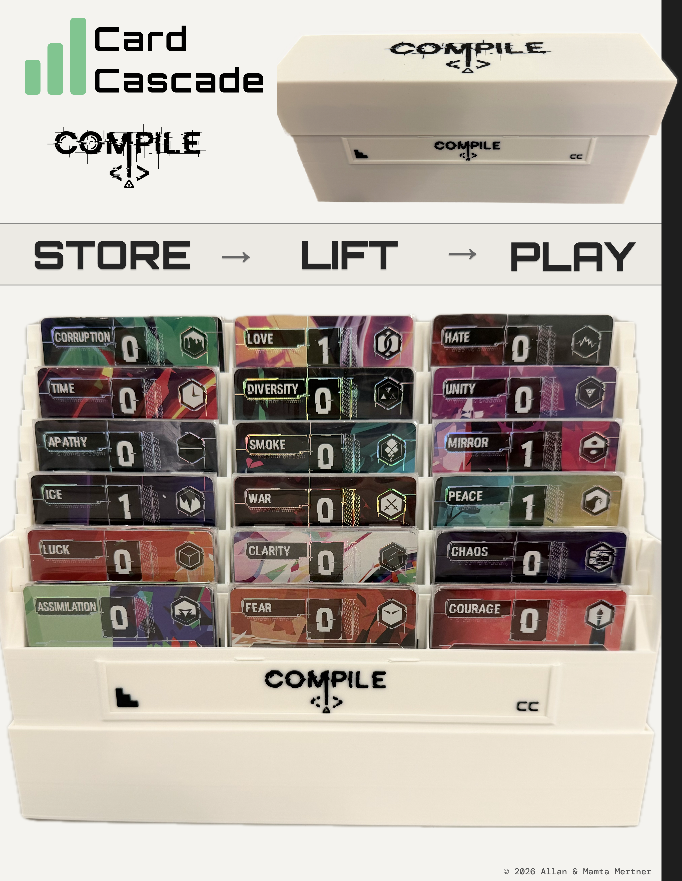
cascades/Compile/Compile Hero Portrait.png
