amertner/cardcascade/cascades/Compile/labels/Compile Labels.png

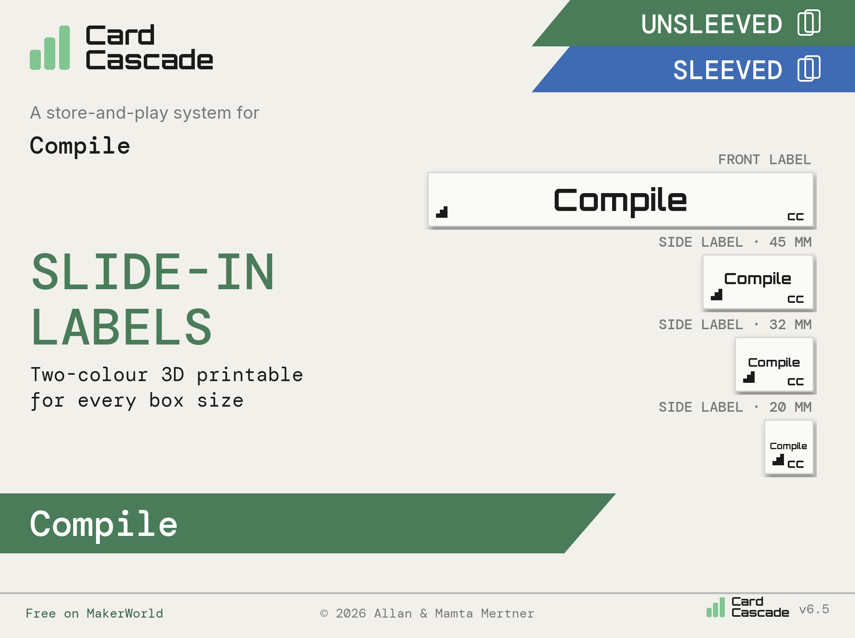
cascades/Compile/labels/Compile Labels.png
