amertner/cardcascade/cascades/Compile/Pictures/IMG_1465.jpeg

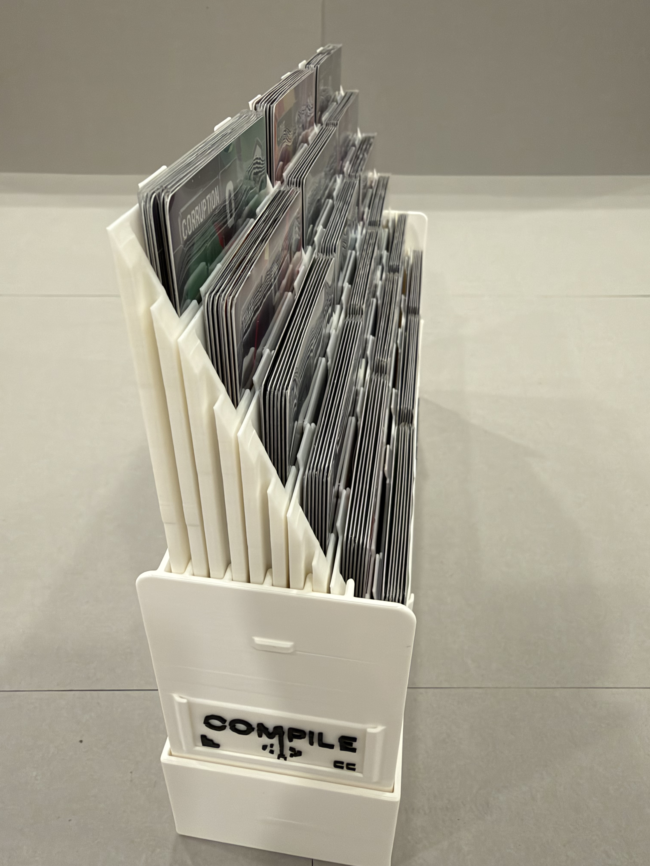
cascades/Compile/Pictures/IMG_1465.jpeg
