amertner/cardcascade/cascades/Compile/Pictures/IMG_1466.jpeg

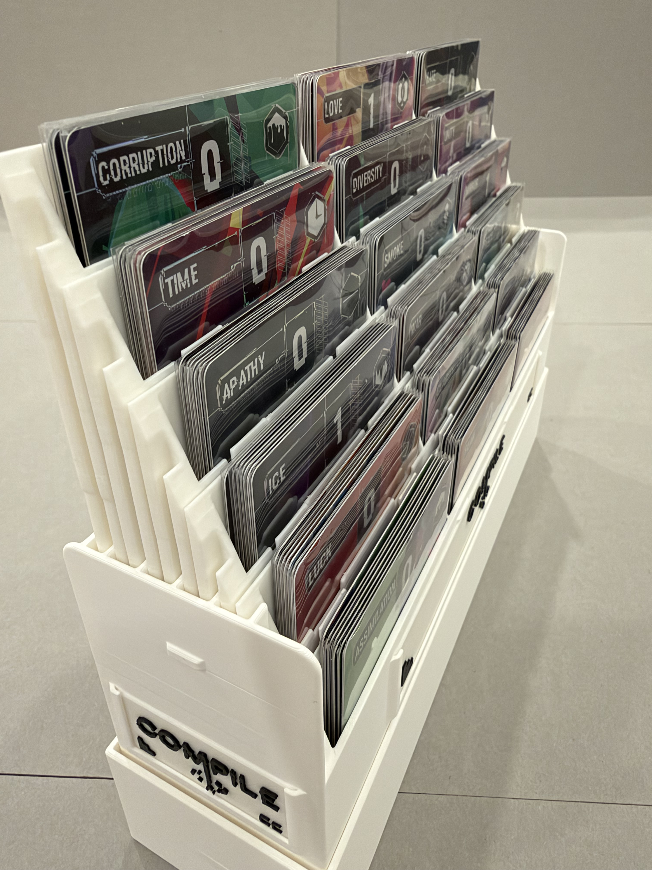
cascades/Compile/Pictures/IMG_1466.jpeg
