amertner/cardcascade/cascades/Compile/Pictures/IMG_1467.jpeg

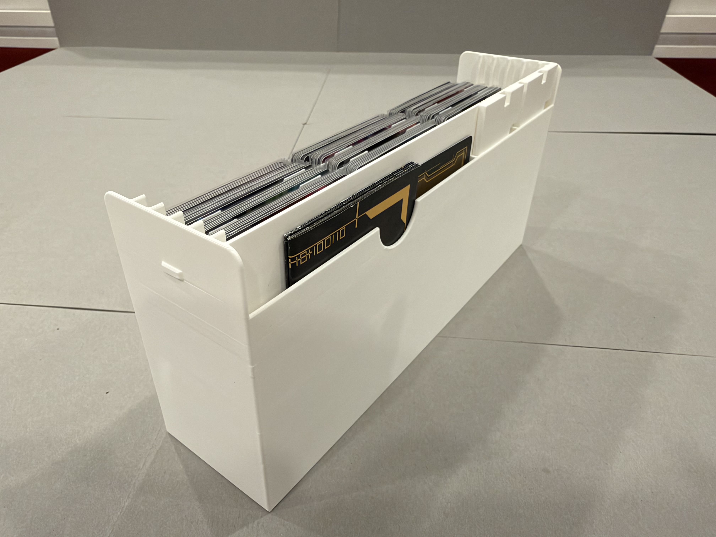
cascades/Compile/Pictures/IMG_1467.jpeg
