amertner/cardcascade/cascades/Compile/Pictures/IMG_1468.jpeg

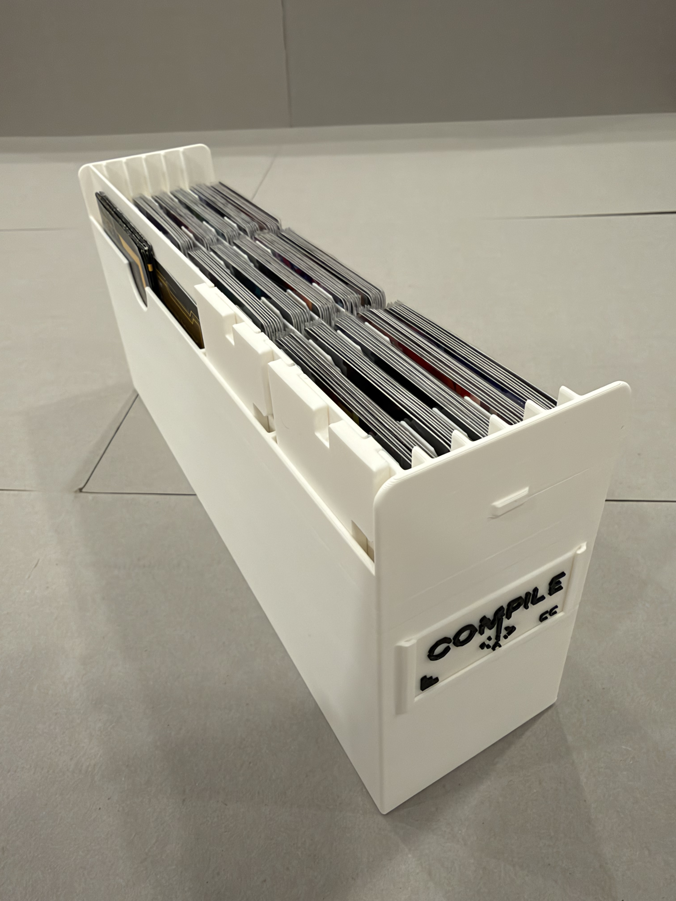
cascades/Compile/Pictures/IMG_1468.jpeg
