amertner/cardcascade/cascades/Compile/Pictures/IMG_1482.PNG

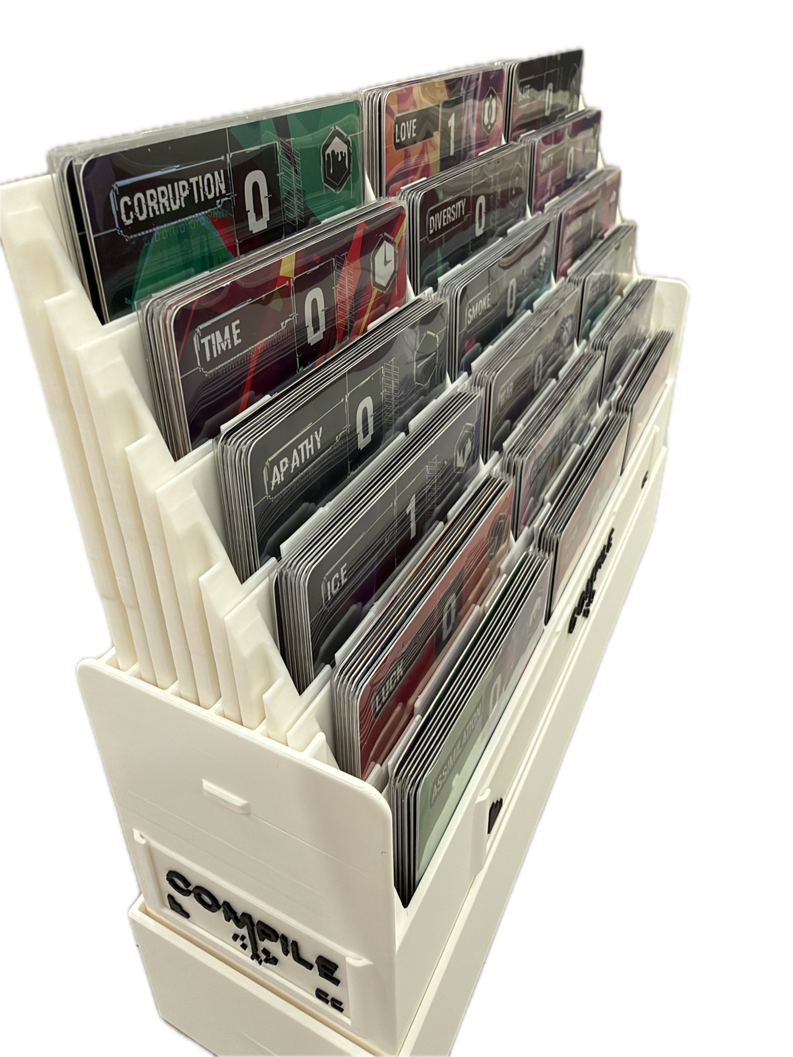
cascades/Compile/Pictures/IMG_1482.PNG
