amertner/cardcascade/cascades/Compile/Pictures/IMG_1572.jpeg

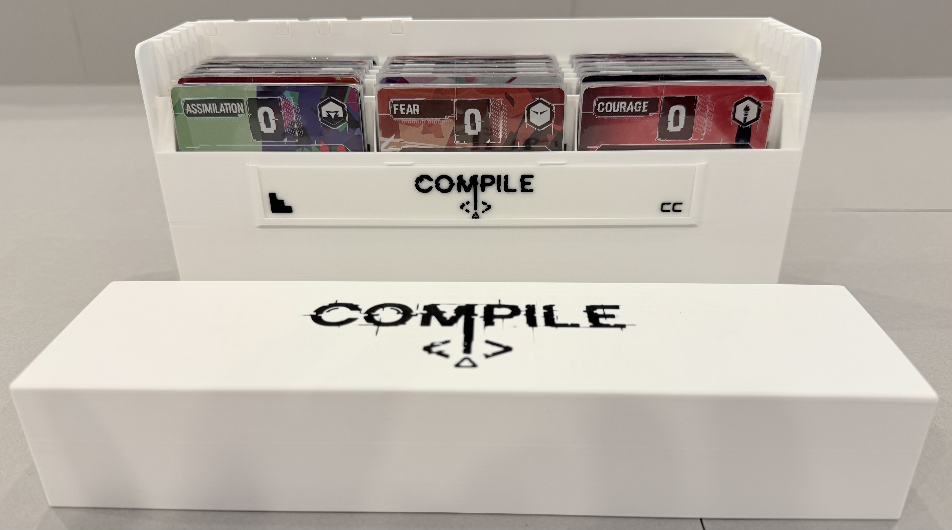
cascades/Compile/Pictures/IMG_1572.jpeg
