amertner/cardcascade/cascades/Compile/Pictures/IMG_1573.jpeg

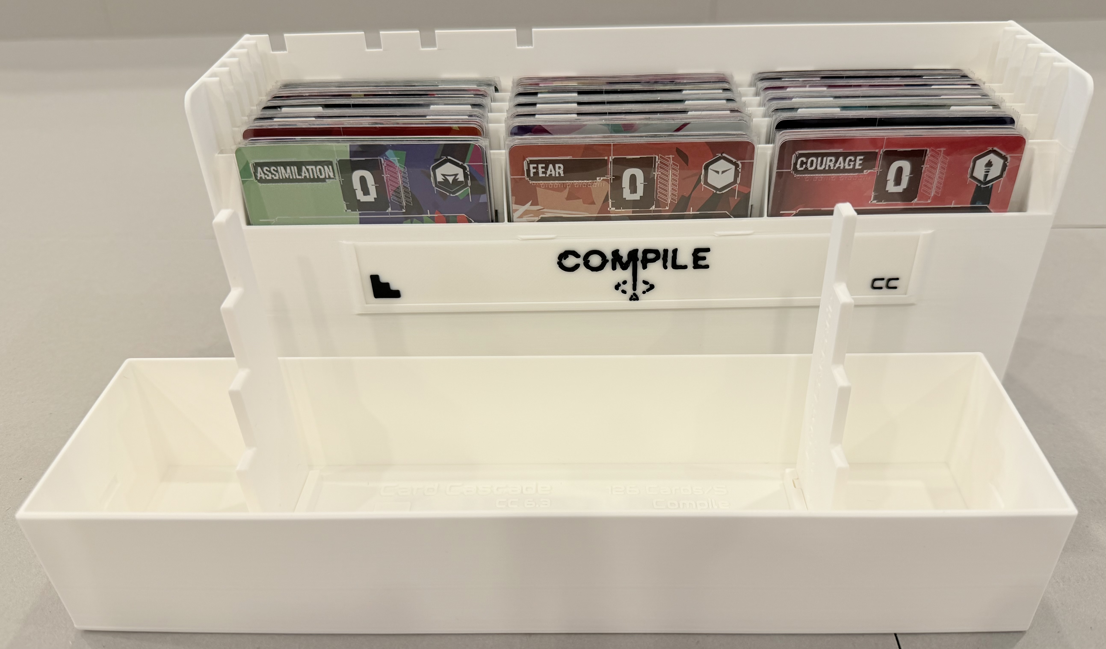
cascades/Compile/Pictures/IMG_1573.jpeg
