amertner/cardcascade/cascades/Compile/Pictures/IMG_1574.jpeg

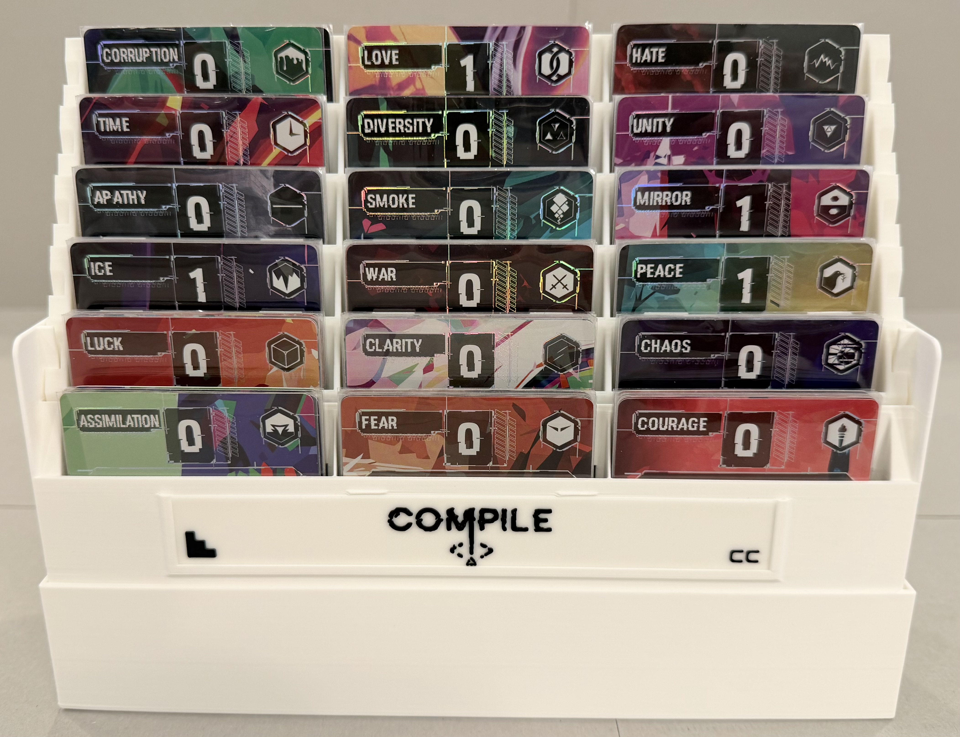
cascades/Compile/Pictures/IMG_1574.jpeg
