amertner/cardcascade/cascades/Compile/Pictures/IMG_1576.jpeg

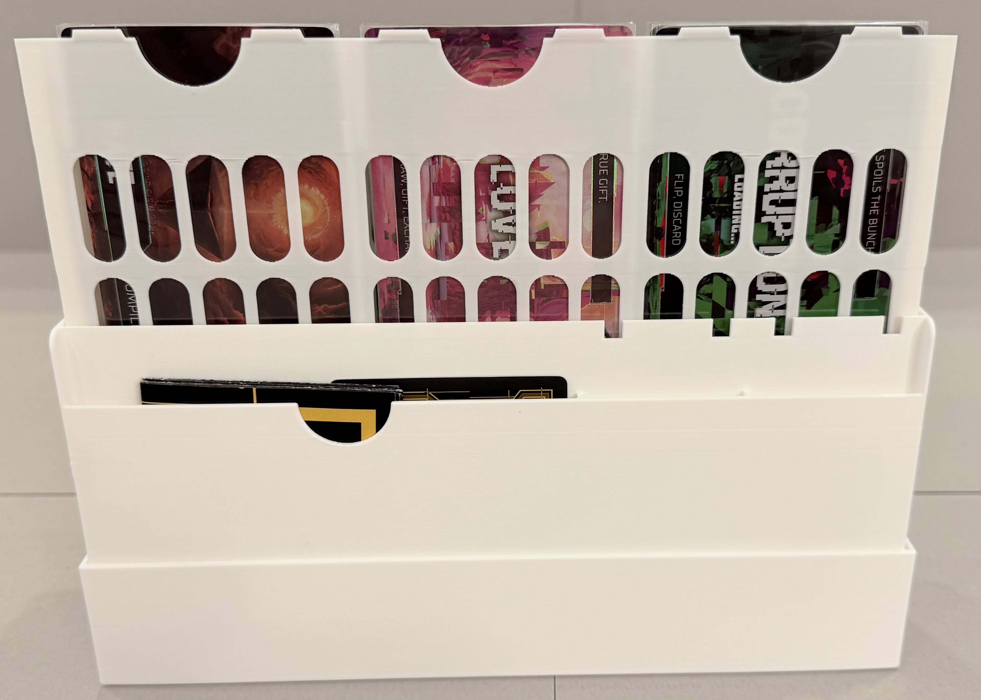
cascades/Compile/Pictures/IMG_1576.jpeg
