amertner/cardcascade/cascades/Dominion/Dominion 168 Card Sleeved (S4.16.10.32-Sl).png

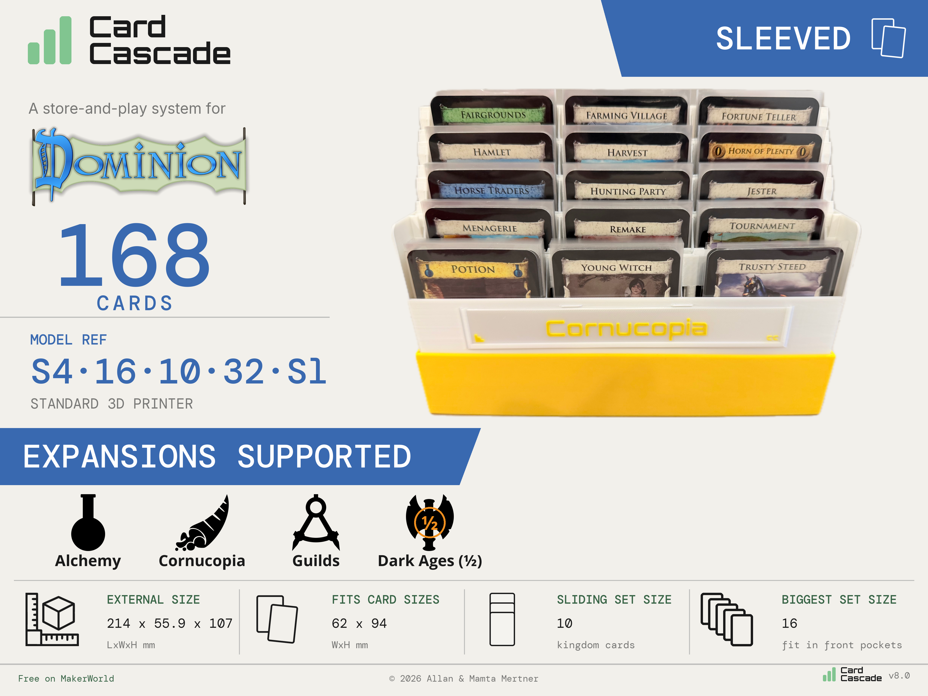
cascades/Dominion/Dominion 168 Card Sleeved (S4.16.10.32-Sl).png
