amertner/cardcascade/cascades/Dominion/Dominion 202 Card (Mat) Sleeved (M4.21.10.45-Sl).png

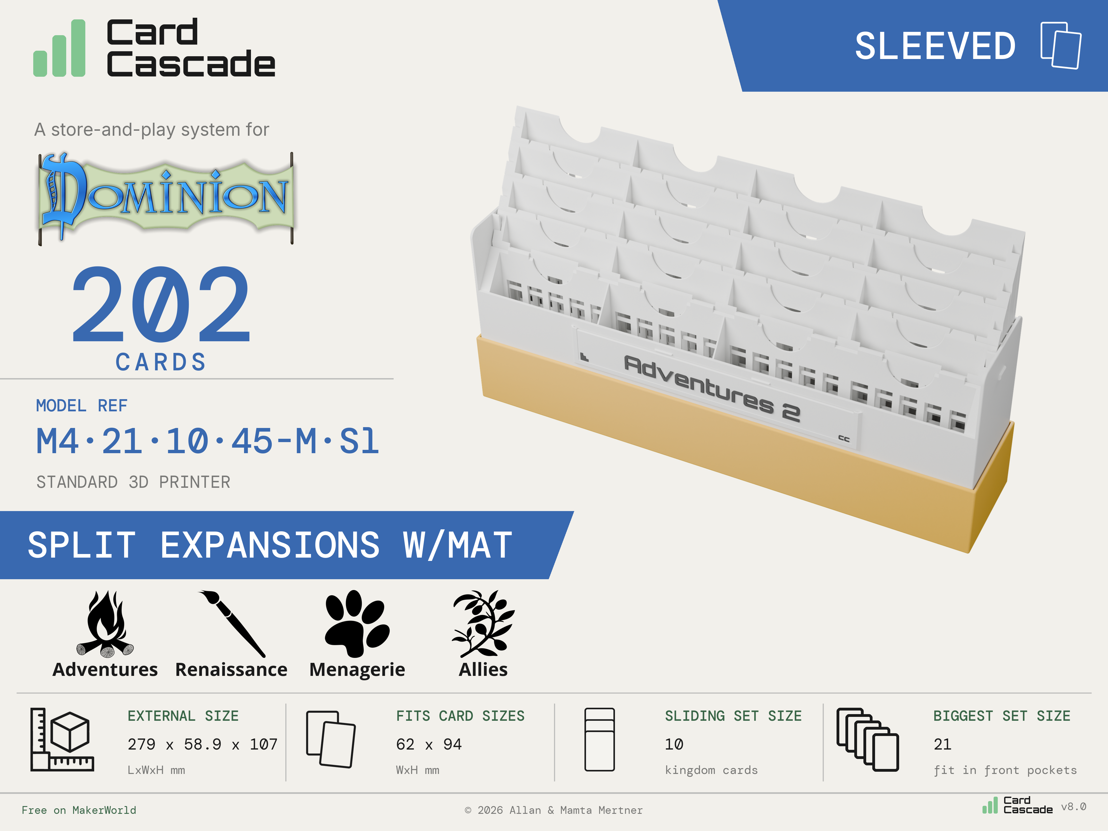
cascades/Dominion/Dominion 202 Card (Mat) Sleeved (M4.21.10.45-Sl).png
