amertner/cardcascade/cascades/Dominion/Dominion 244 Card Sleeved (M4.21.10.45-Sl).png

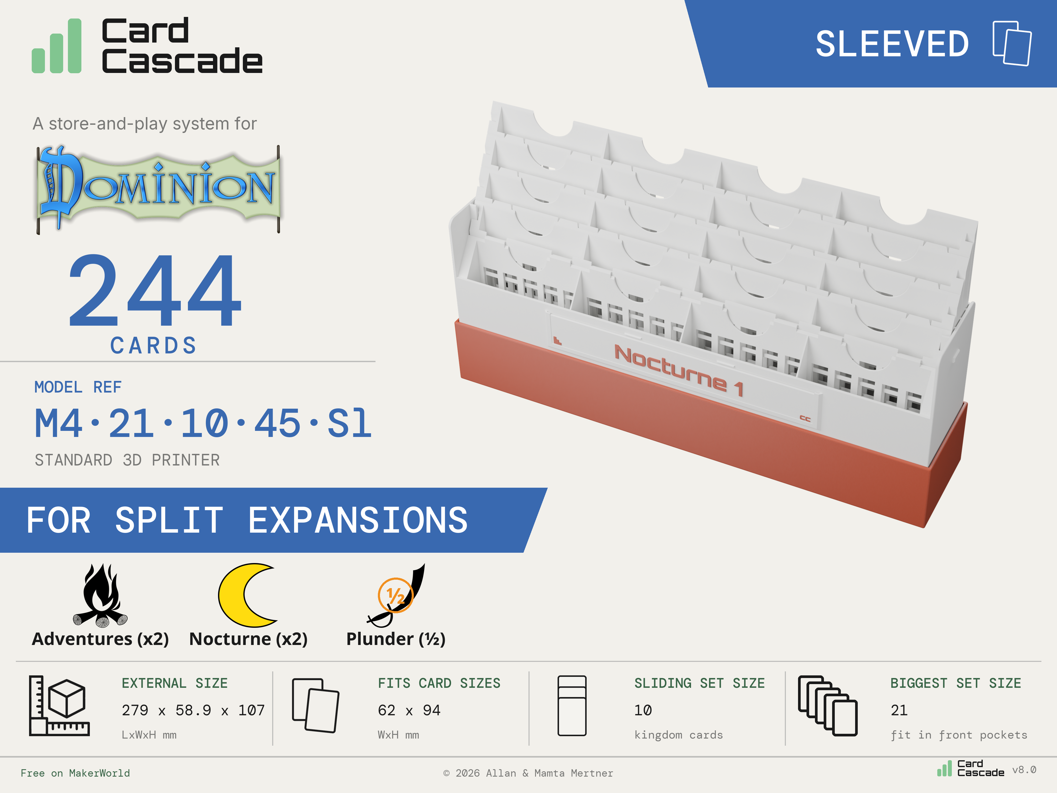
cascades/Dominion/Dominion 244 Card Sleeved (M4.21.10.45-Sl).png
