amertner/cardcascade/cascades/Dominion/Dominion 246 Card Sleeved (S2.40.12-30.45-Sl).png

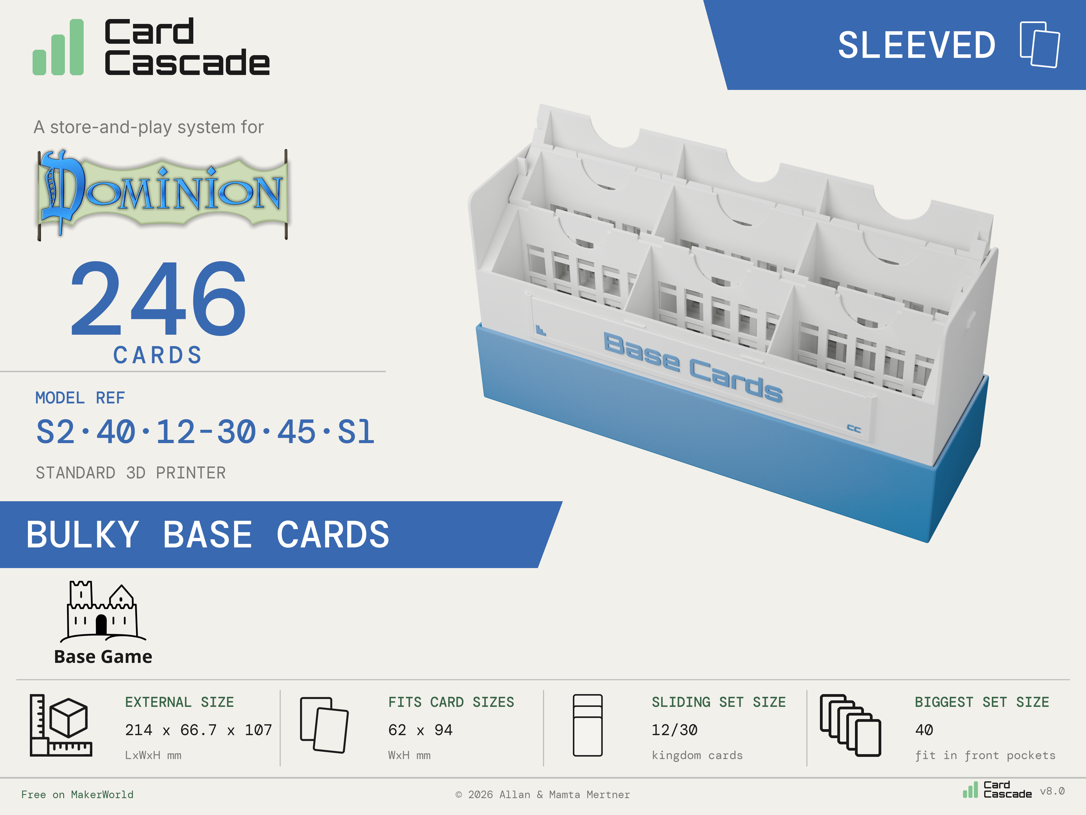
cascades/Dominion/Dominion 246 Card Sleeved (S2.40.12-30.45-Sl).png
