amertner/cardcascade/cascades/Dominion/Dominion 290 Card (Mat) Sleeved (M6.21.10-12.0-Sl).png

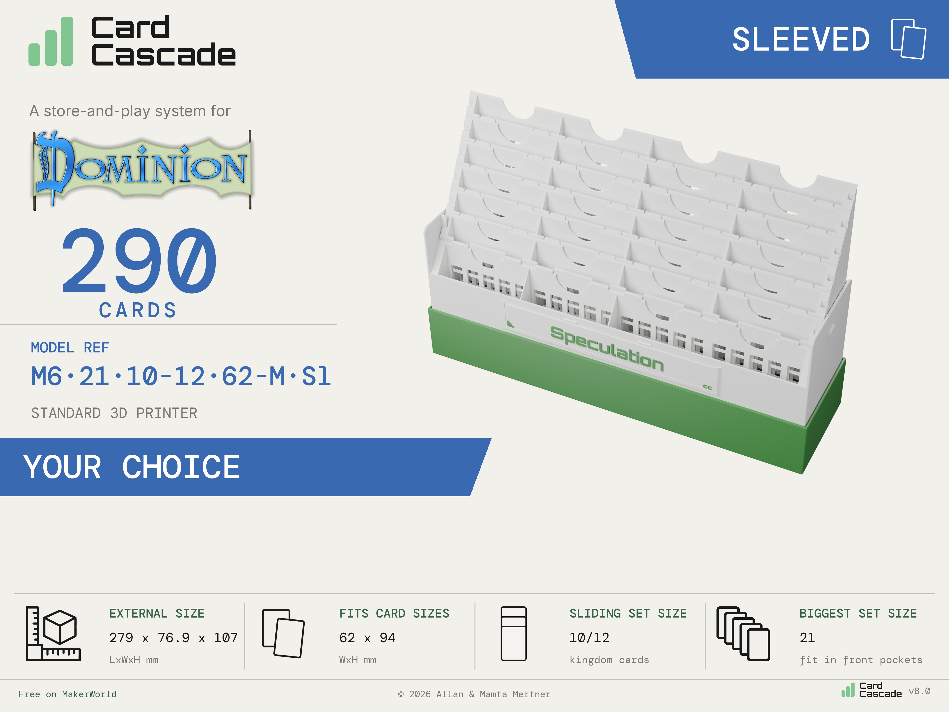
cascades/Dominion/Dominion 290 Card (Mat) Sleeved (M6.21.10-12.0-Sl).png
