amertner/cardcascade/cascades/Dominion/Dominion 300 Card Sleeved (S5.40.12.62-Sl).png

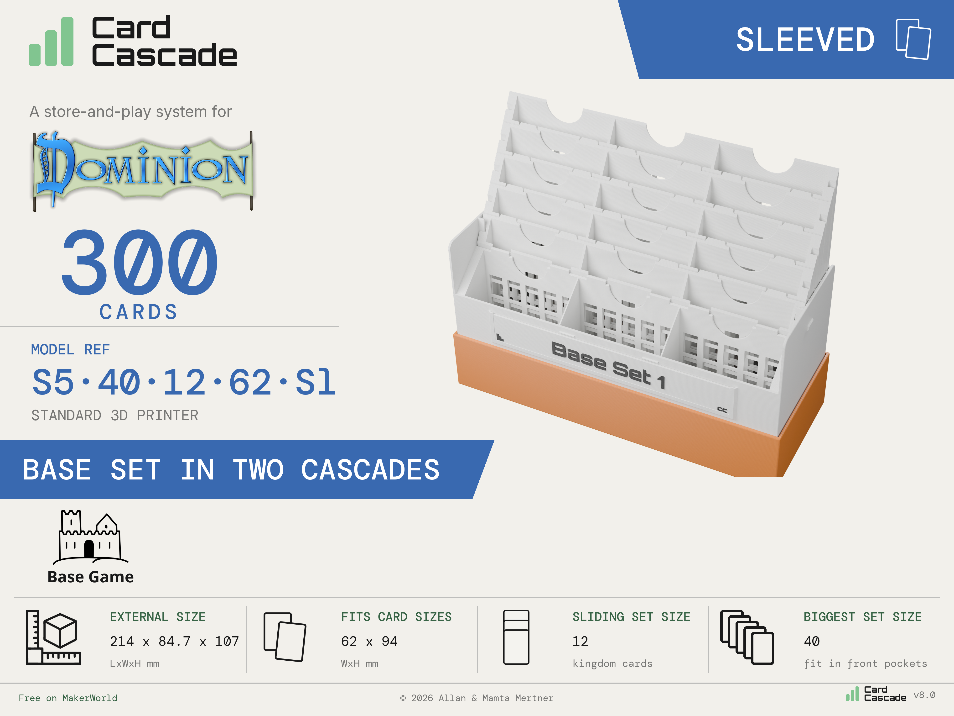
cascades/Dominion/Dominion 300 Card Sleeved (S5.40.12.62-Sl).png
