amertner/cardcascade/cascades/Dominion/Dominion 324 Card Sleeved (M6.21.10.62-Sl).png

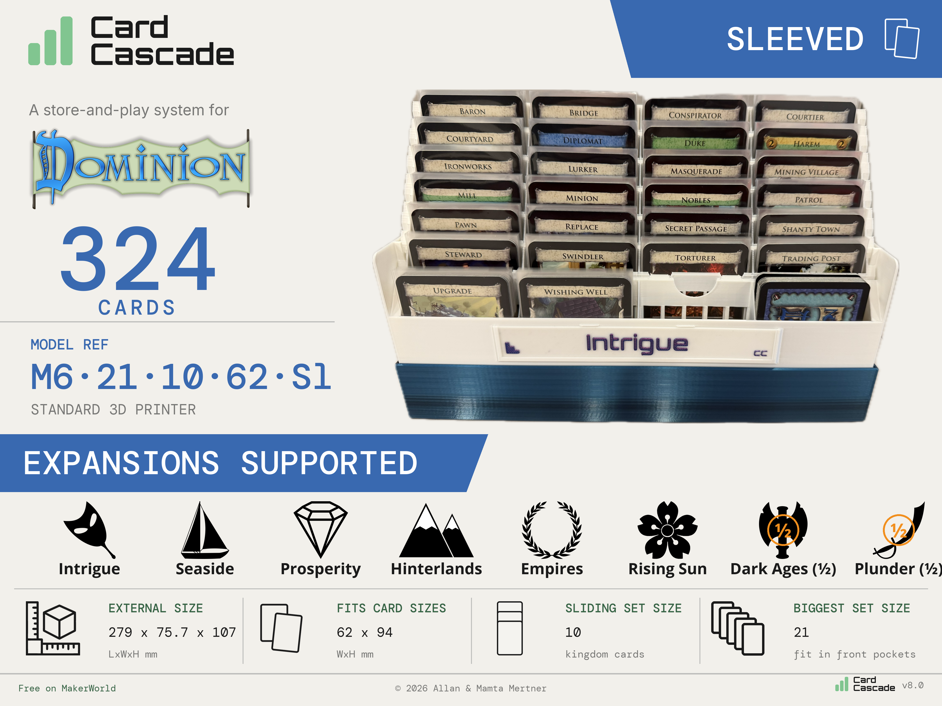
cascades/Dominion/Dominion 324 Card Sleeved (M6.21.10.62-Sl).png
