amertner/cardcascade/cascades/Dominion/Dominion 324 Card Unsleeved (M6.21.10.45-Un).png

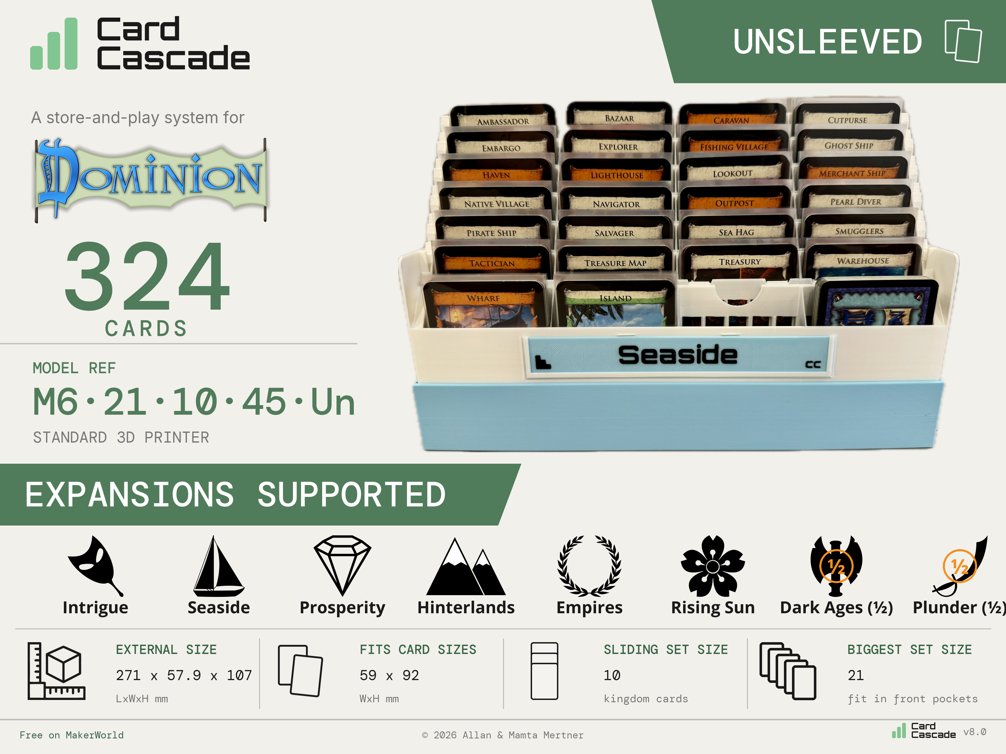
cascades/Dominion/Dominion 324 Card Unsleeved (M6.21.10.45-Un).png
