amertner/cardcascade/cascades/Dominion/Dominion 333 Card Sleeved (S9.21.10.62-Sl).png

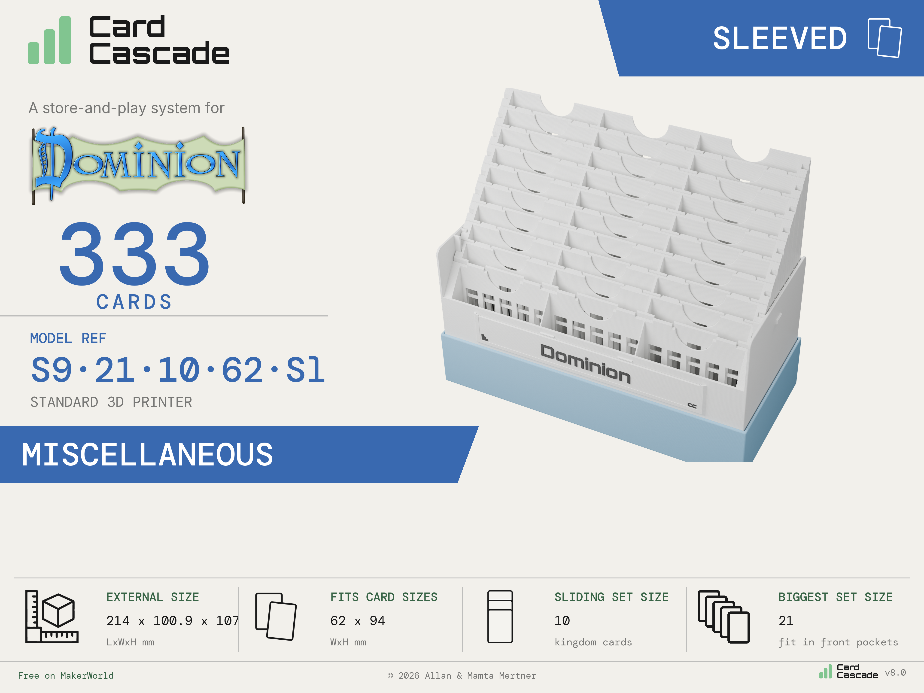
cascades/Dominion/Dominion 333 Card Sleeved (S9.21.10.62-Sl).png
