amertner/cardcascade/cascades/Dominion/Dominion 400 Card (Mat) Sleeved (M8.40.10.62-Sl).png

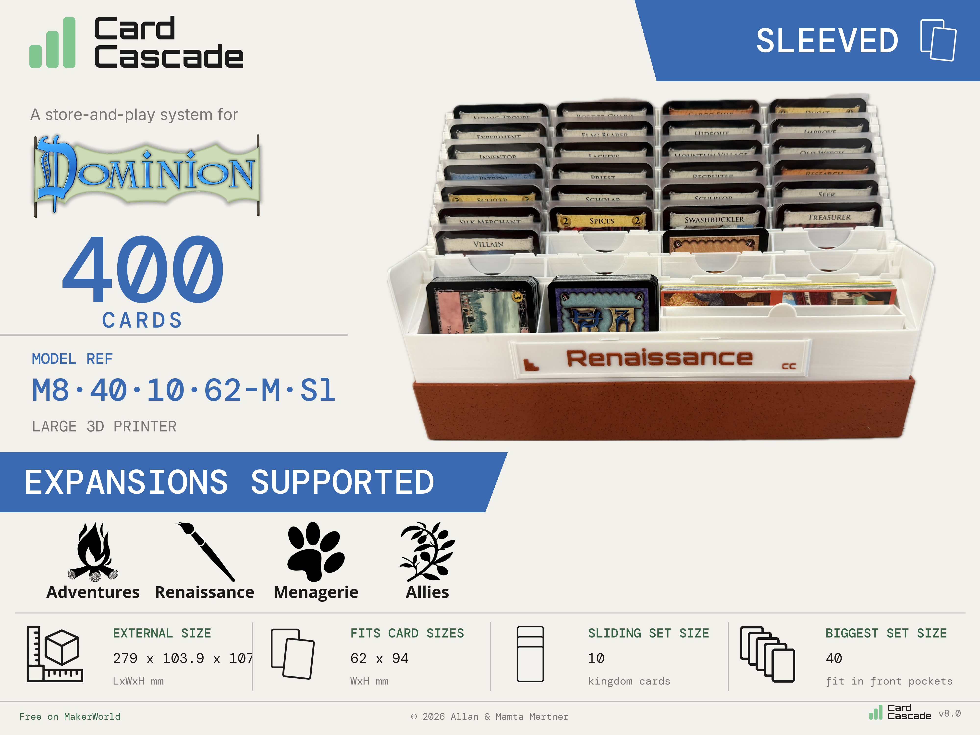
cascades/Dominion/Dominion 400 Card (Mat) Sleeved (M8.40.10.62-Sl).png
