amertner/cardcascade/cascades/Dominion/Dominion 472 Card Sleeved (M2.60.18-40.62-Sl).png

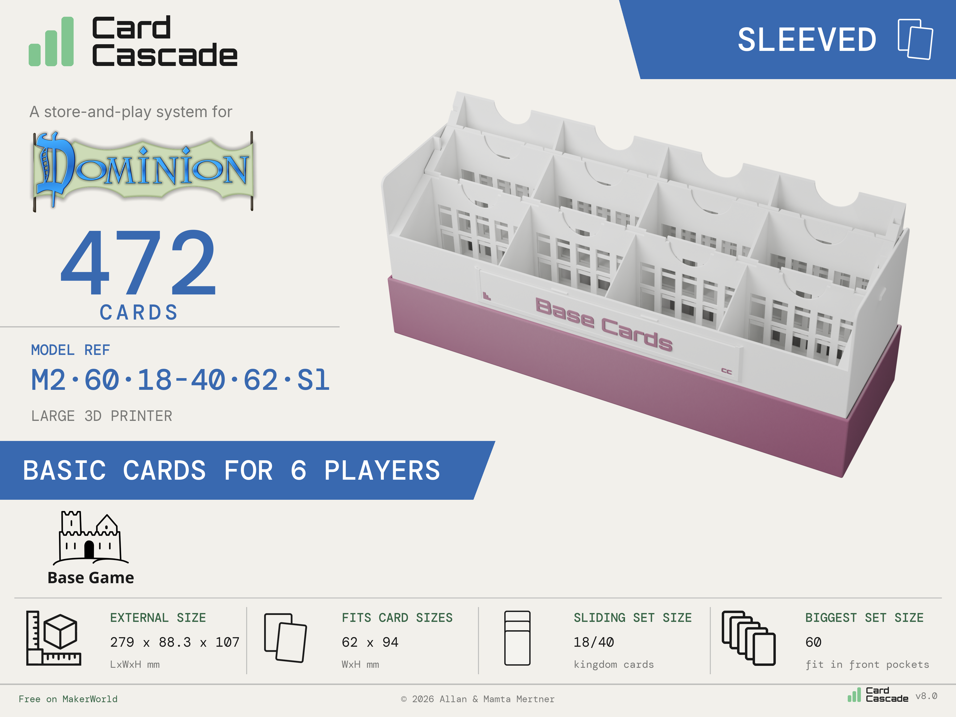
cascades/Dominion/Dominion 472 Card Sleeved (M2.60.18-40.62-Sl).png
