amertner/cardcascade/cascades/Dominion/Dominion 472 Card Unsleeved (M2.60.18-40.45-Un).png

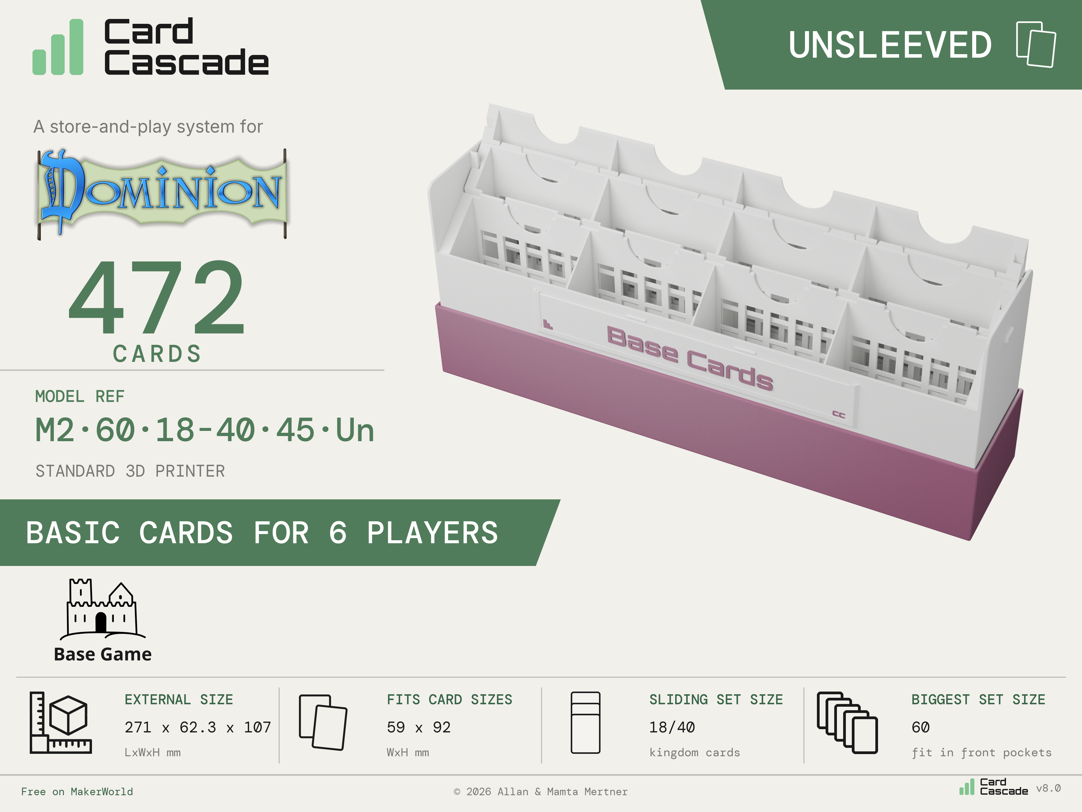
cascades/Dominion/Dominion 472 Card Unsleeved (M2.60.18-40.45-Un).png
