amertner/cardcascade/cascades/Dominion/Dominion 560 Card Unsleeved (L6.40.12.45-Un).png

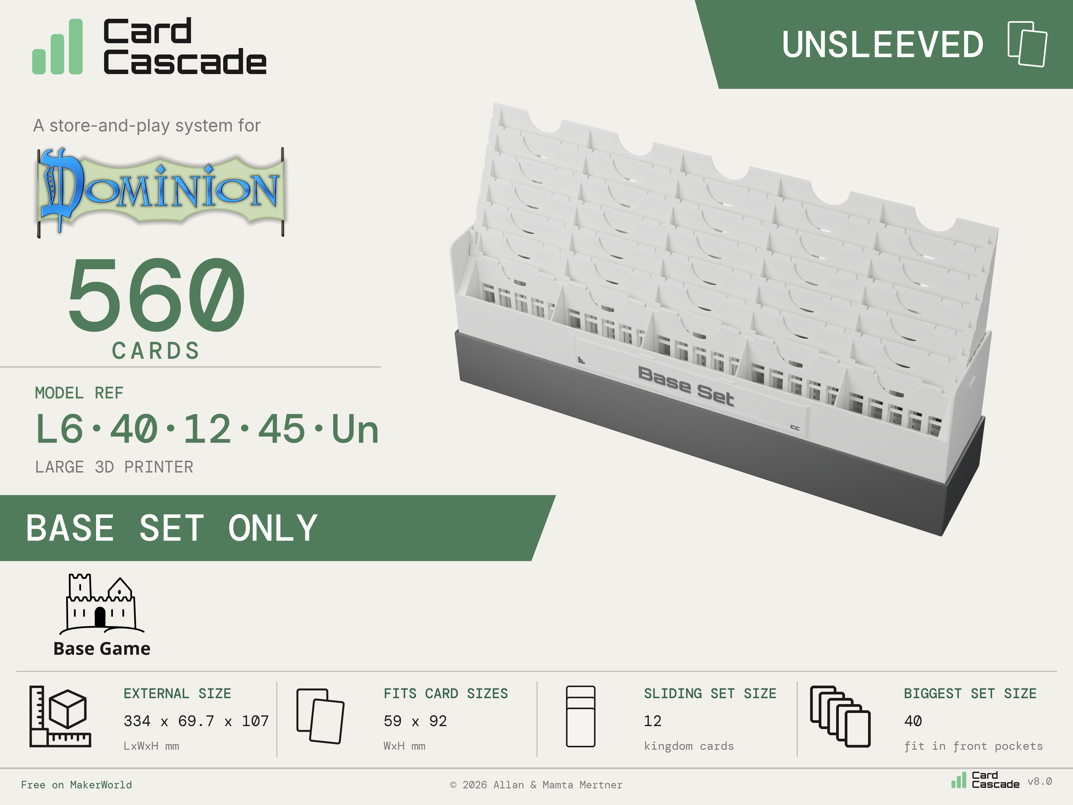
cascades/Dominion/Dominion 560 Card Unsleeved (L6.40.12.45-Un).png
