amertner/cardcascade/cascades/Dominion/Dominion 650 Card Sleeved (L8.50.10.62-Sl).png

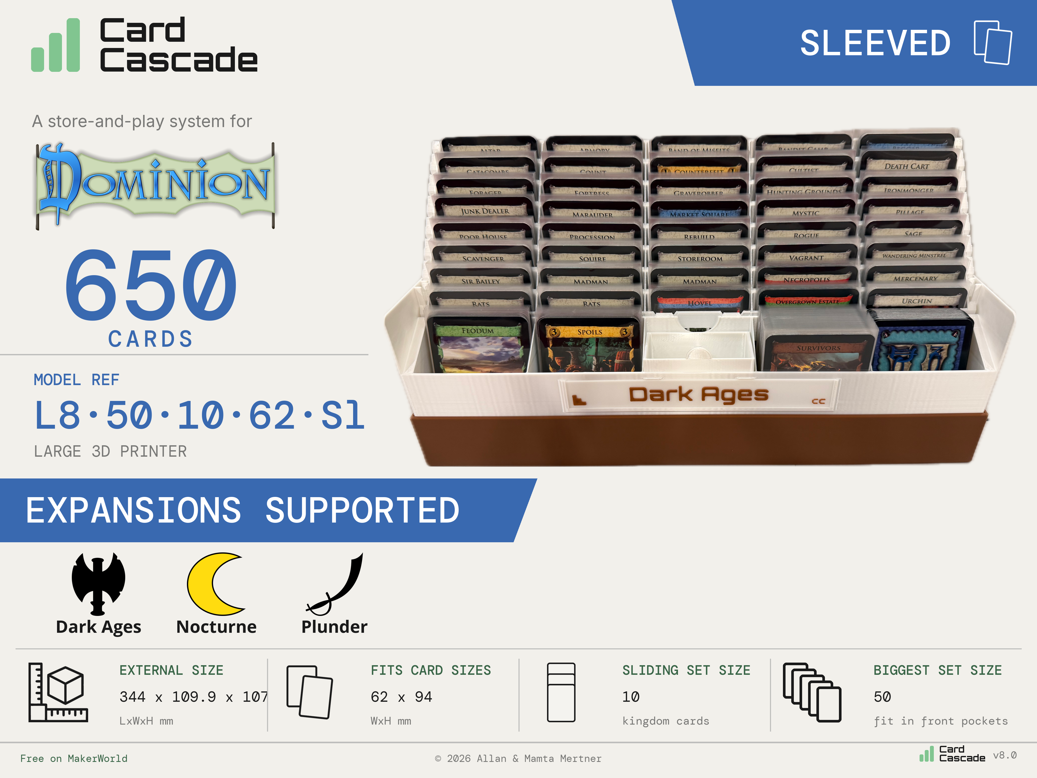
cascades/Dominion/Dominion 650 Card Sleeved (L8.50.10.62-Sl).png
