amertner/cardcascade/cascades/Dominion/labels/Adventures Labels.png

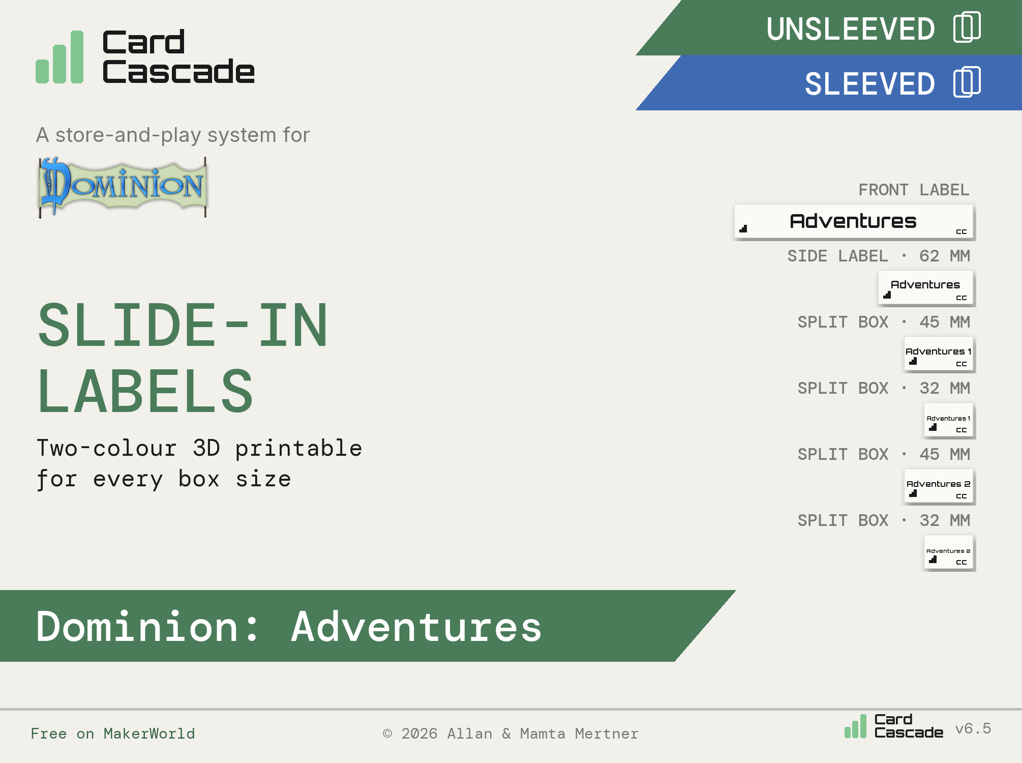
cascades/Dominion/labels/Adventures Labels.png
