amertner/cardcascade/cascades/Dominion/labels/Alchemy Labels.png

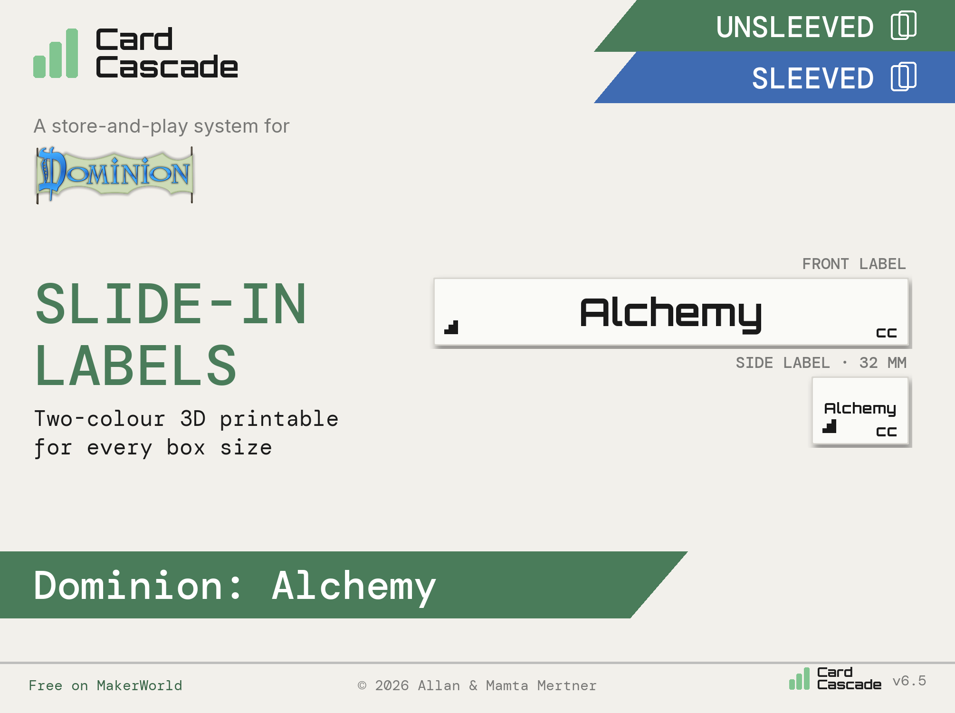
cascades/Dominion/labels/Alchemy Labels.png
