amertner/cardcascade/cascades/Dominion/labels/Blank Labels.png

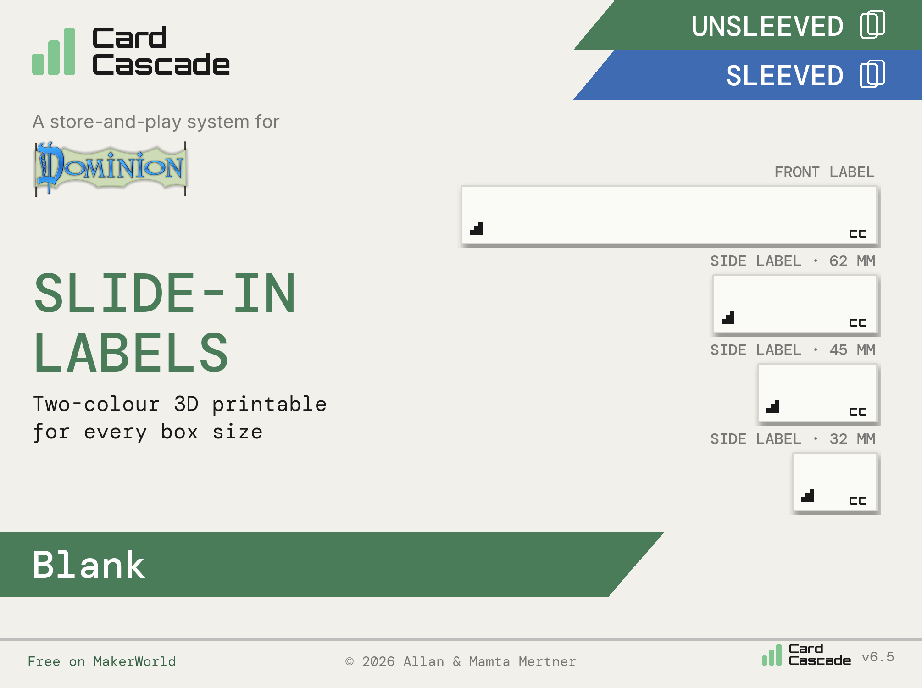
cascades/Dominion/labels/Blank Labels.png
