amertner/cardcascade/cascades/Dominion/labels/Bulky Base Cards Labels.png

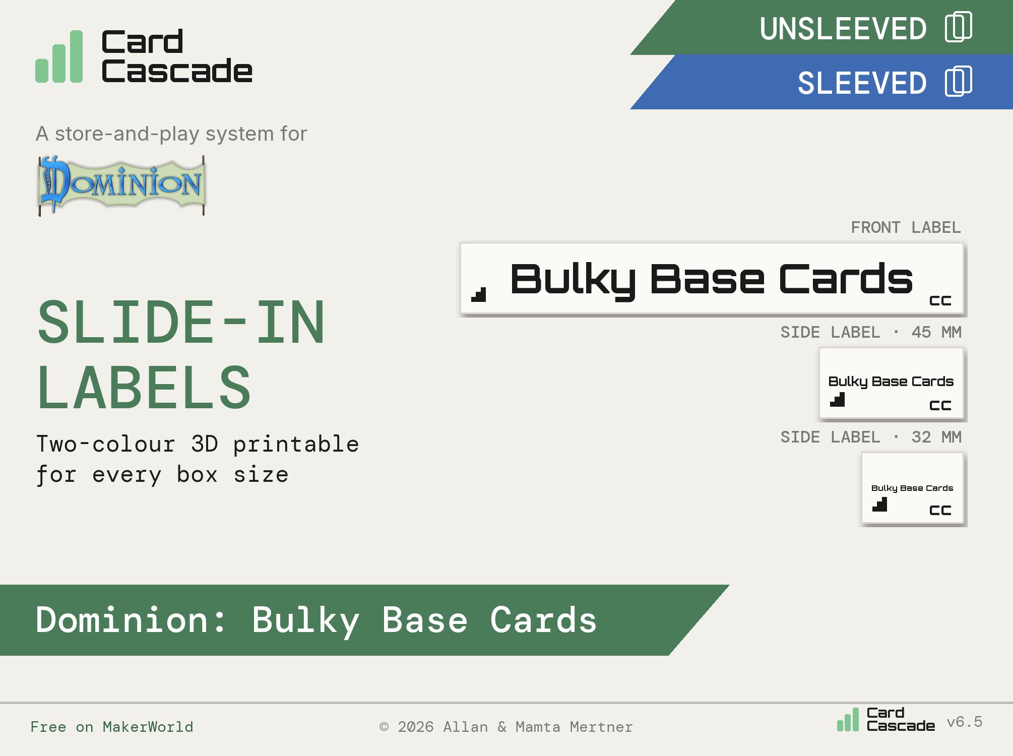
cascades/Dominion/labels/Bulky Base Cards Labels.png
