amertner/cardcascade/cascades/Dominion/labels/Empires Labels.png

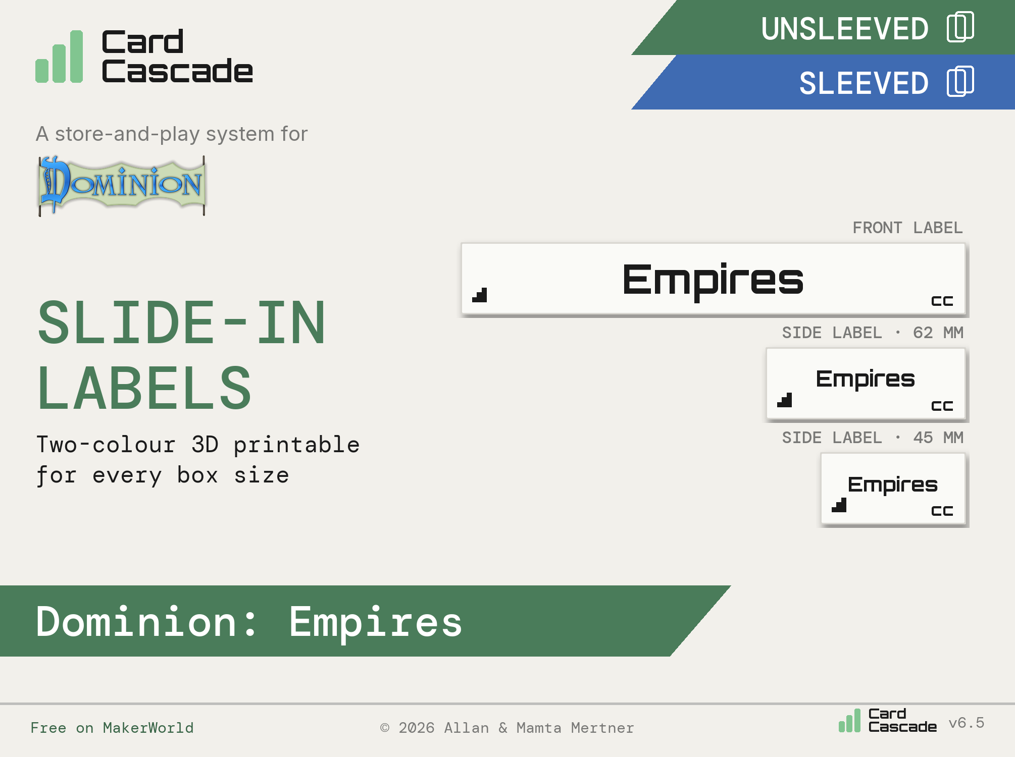
cascades/Dominion/labels/Empires Labels.png
