amertner/cardcascade/cascades/Dominion/labels/Hinterlands Labels.png

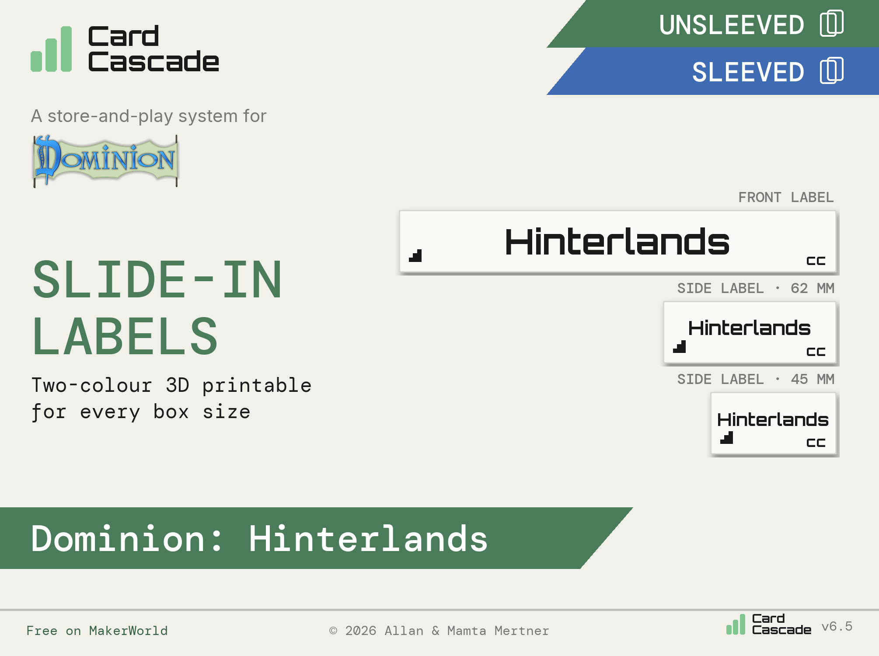
cascades/Dominion/labels/Hinterlands Labels.png
