amertner/cardcascade/cascades/Dominion/Pictures/400 Card (Mat) empty.png

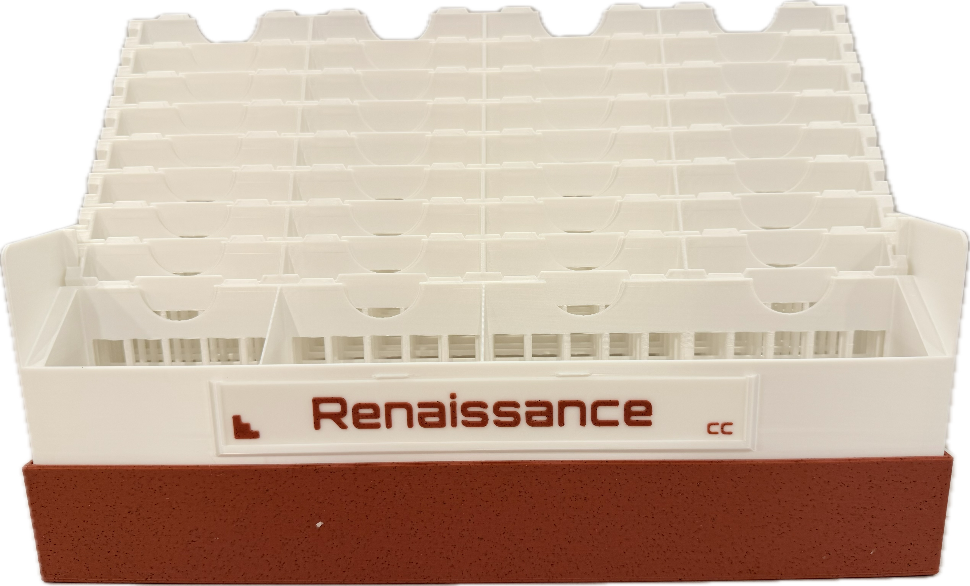
cascades/Dominion/Pictures/400 Card (Mat) empty.png
