amertner/cardcascade/cascades/Dominion/Pictures/IMG_1490.jpeg

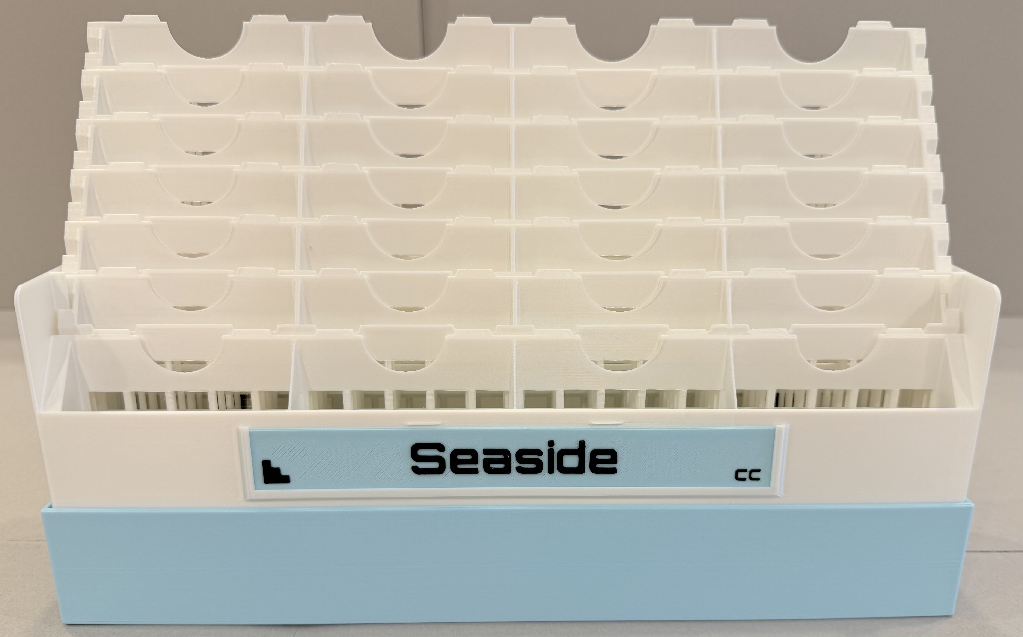
cascades/Dominion/Pictures/IMG_1490.jpeg
