amertner/cardcascade/cascades/Dominion/Pictures/IMG_1491.jpeg

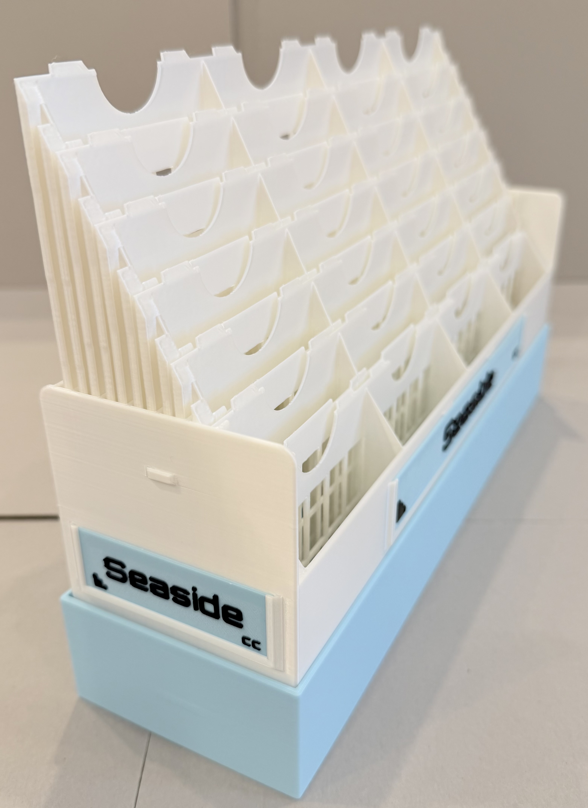
cascades/Dominion/Pictures/IMG_1491.jpeg
