amertner/cardcascade/cascades/Dominion/Pictures/IMG_1493.jpeg

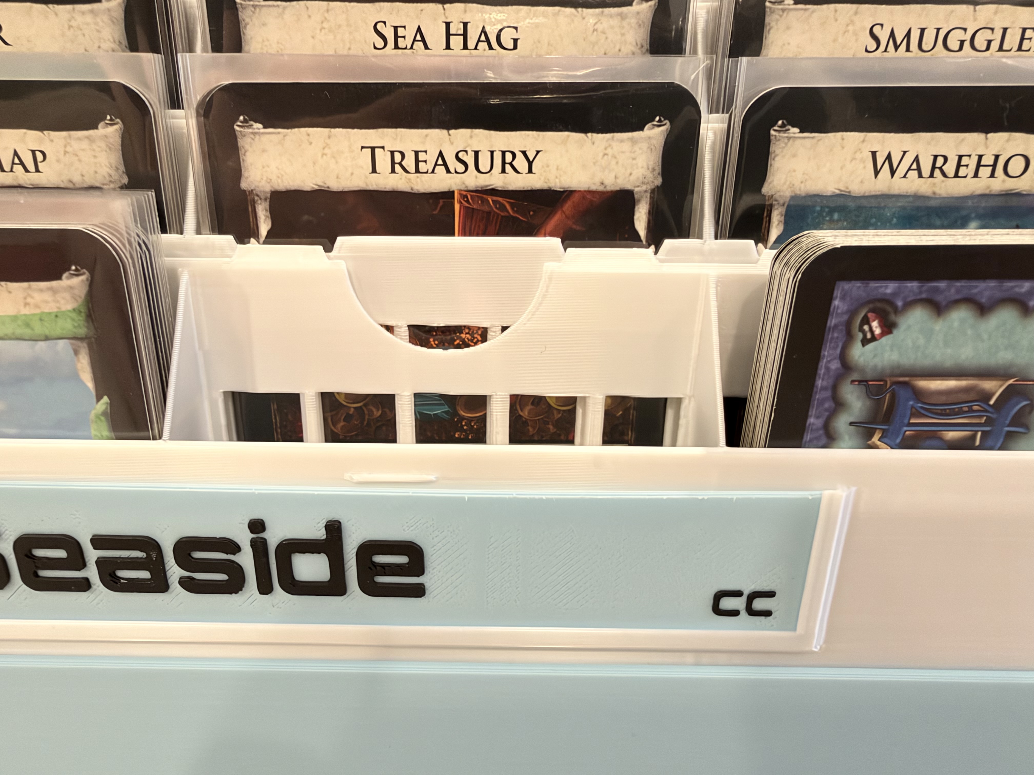
cascades/Dominion/Pictures/IMG_1493.jpeg
