amertner/cardcascade/cascades/Dominion/Pictures/IMG_1497.jpeg

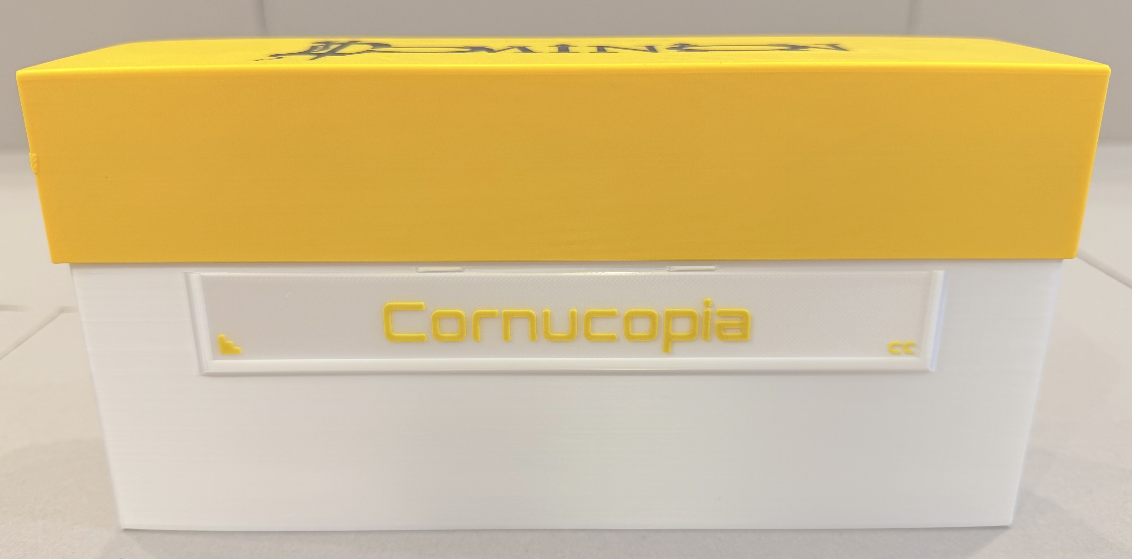
cascades/Dominion/Pictures/IMG_1497.jpeg
