amertner/cardcascade/cascades/Dominion/Pictures/IMG_1499.jpeg

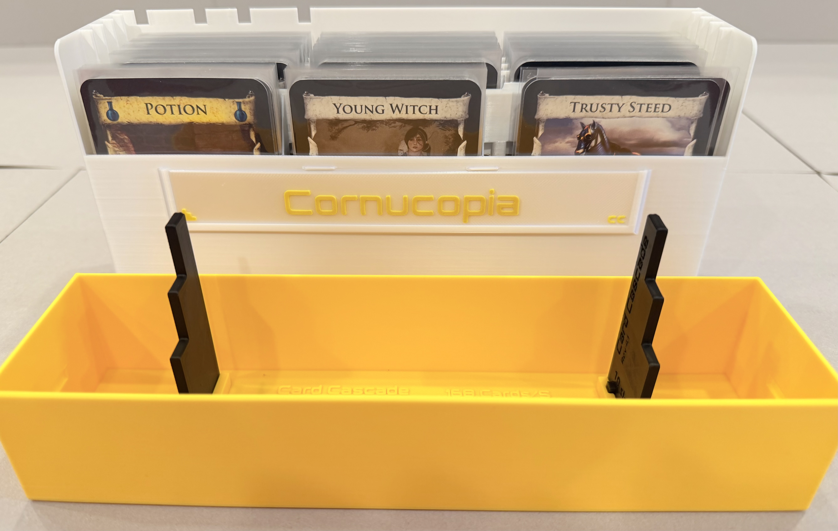
cascades/Dominion/Pictures/IMG_1499.jpeg
