amertner/cardcascade/cascades/Dominion/Pictures/IMG_1501.jpeg

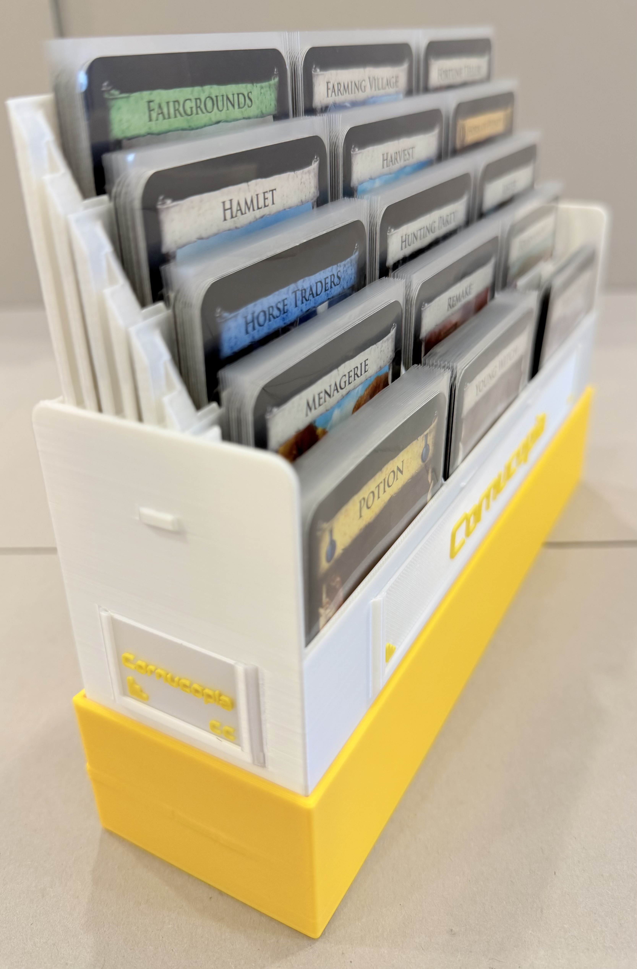
cascades/Dominion/Pictures/IMG_1501.jpeg
