amertner/cardcascade/cascades/FCM/FCM Alt S (198 Card S4-18-12-45-Sl).png

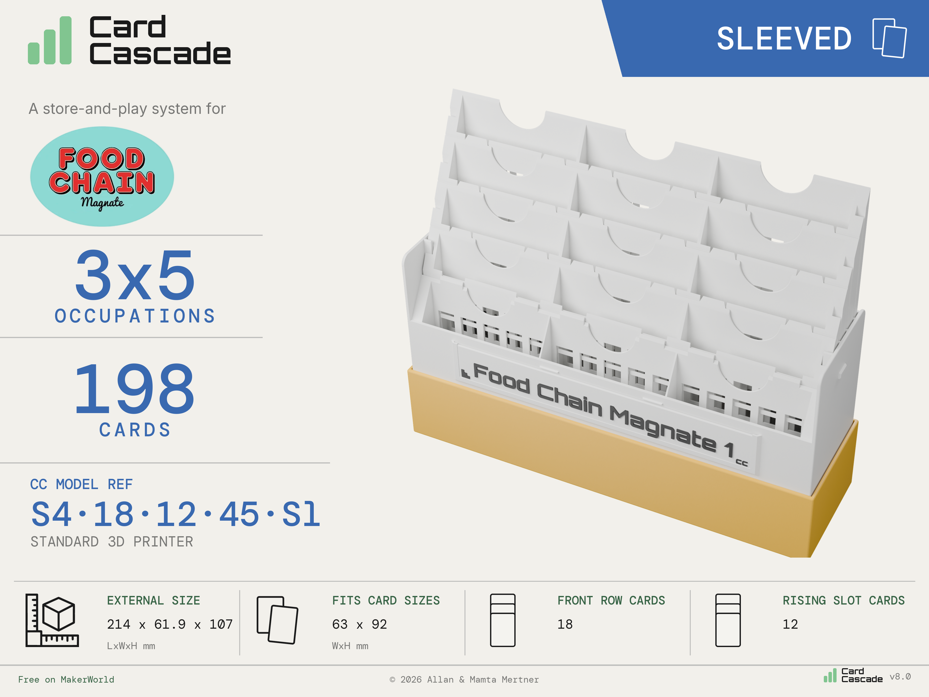
cascades/FCM/FCM Alt S (198 Card S4-18-12-45-Sl).png
