amertner/cardcascade/cascades/FCM/FCM Alt U (198 Card S4-18-12-32-Un).png

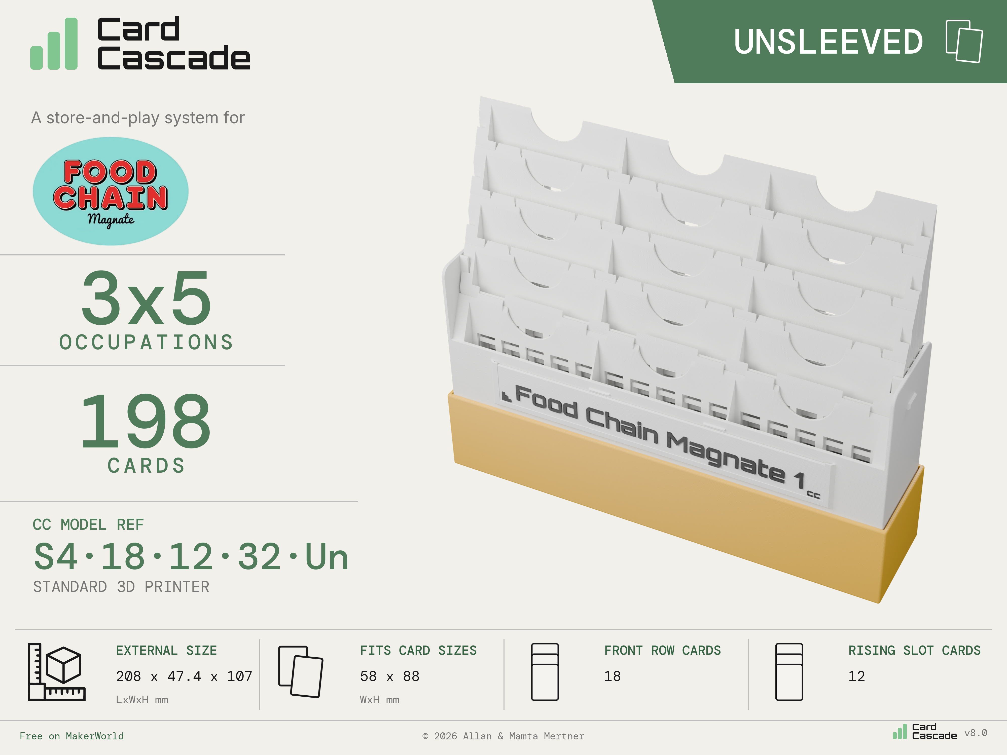
cascades/FCM/FCM Alt U (198 Card S4-18-12-32-Un).png
