amertner/cardcascade/cascades/FCM/FCM Milestones 1S (144 Card M5-6-6-32-Sl).png

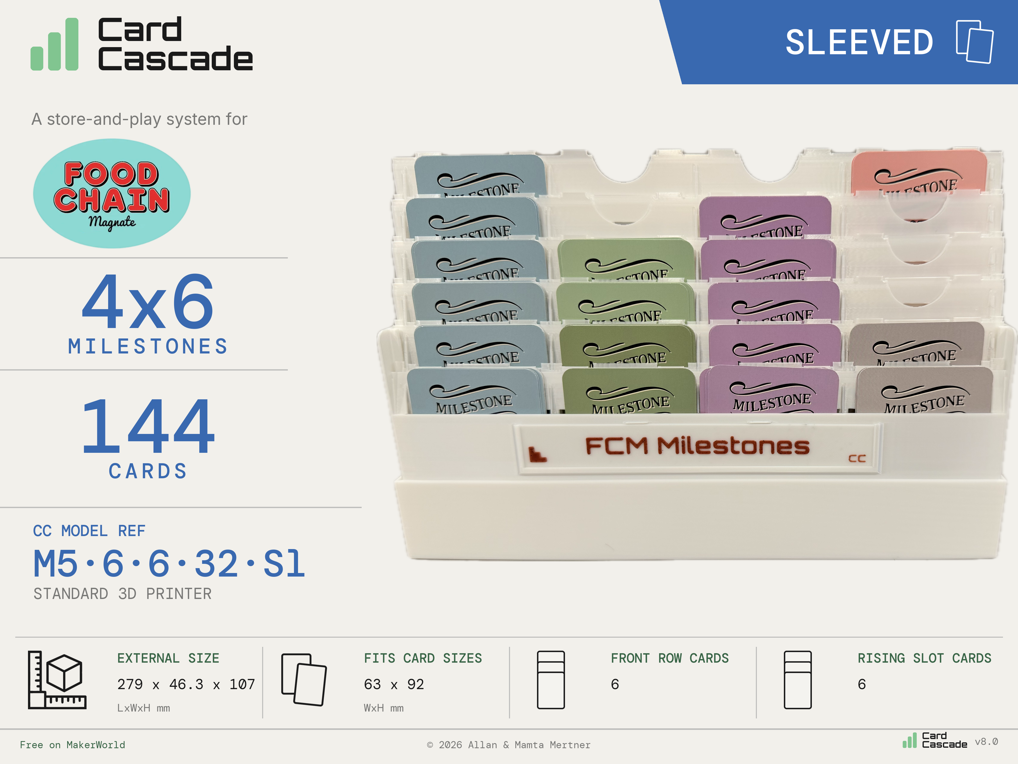
cascades/FCM/FCM Milestones 1S (144 Card M5-6-6-32-Sl).png
