amertner/cardcascade/cascades/FCM/FCM Occ 1S (264 Card M4-18-12-45-Sl).png

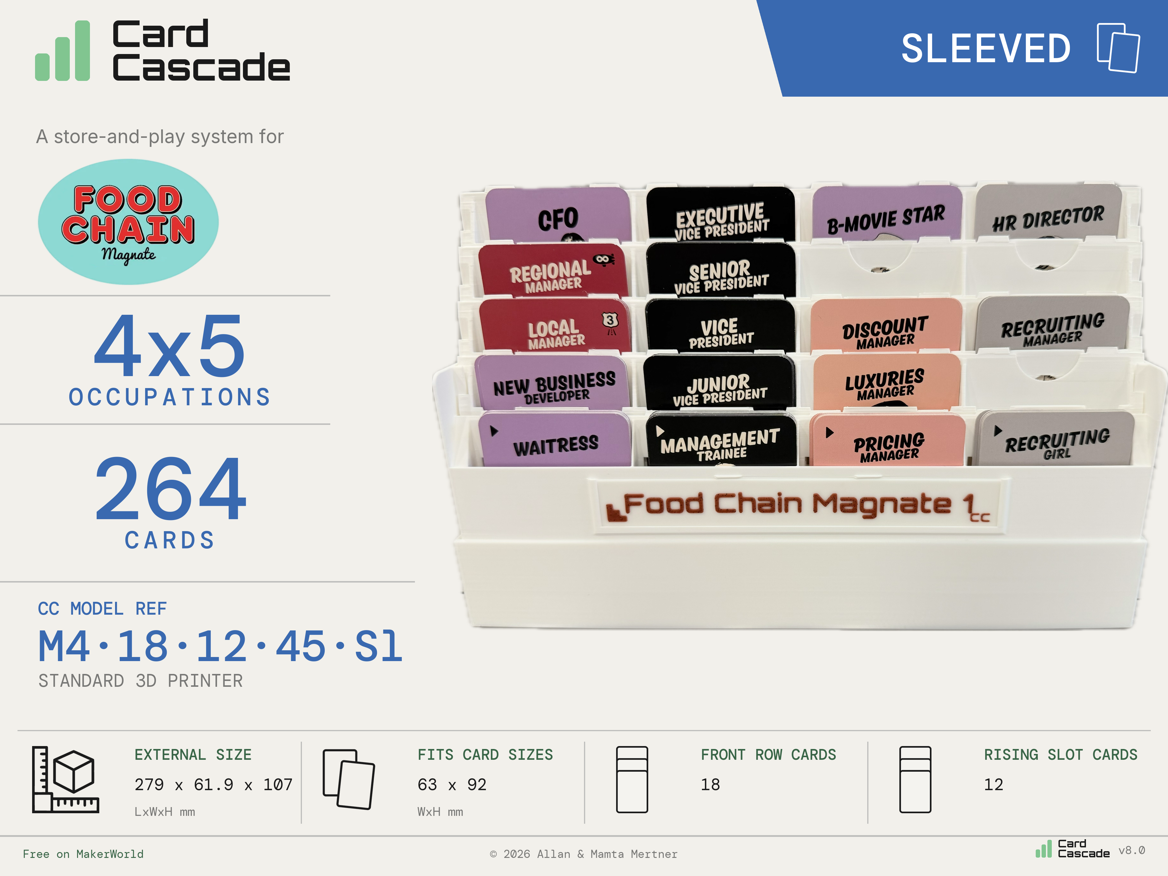
cascades/FCM/FCM Occ 1S (264 Card M4-18-12-45-Sl).png
