amertner/cardcascade/cascades/FCM/FCM Occ 1U (264 Card M4-18-12-32-Un).png

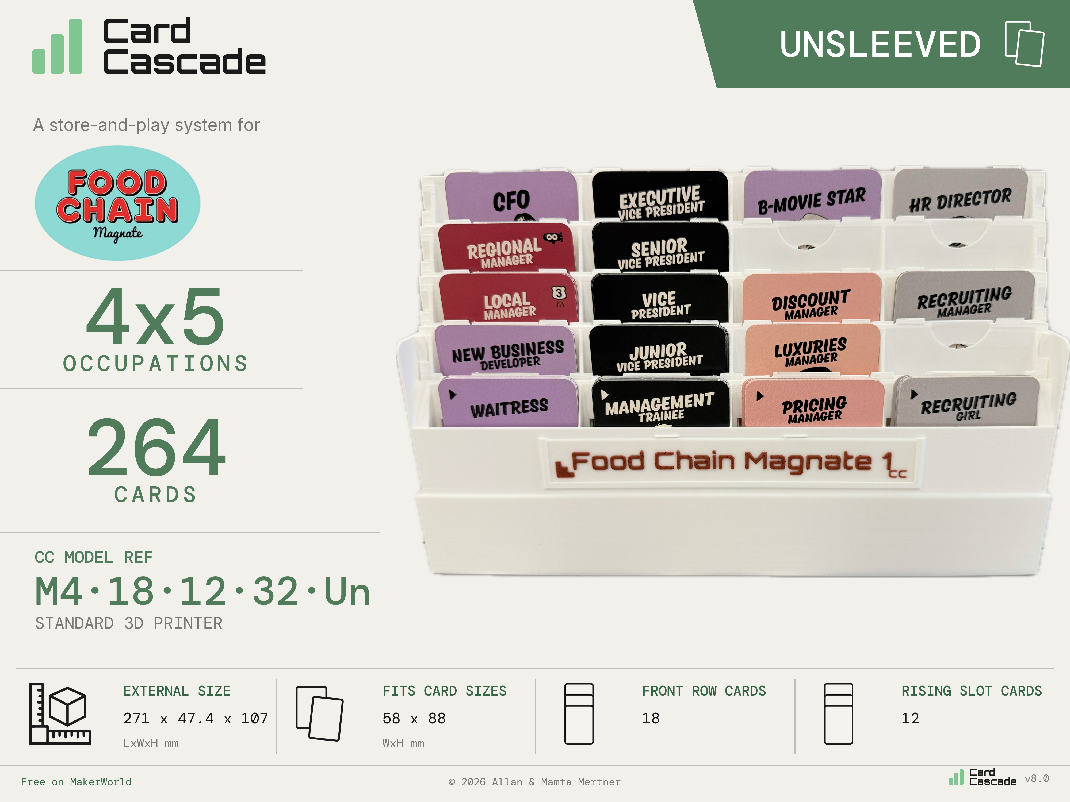
cascades/FCM/FCM Occ 1U (264 Card M4-18-12-32-Un).png
