amertner/cardcascade/cascades/FCM/FCM Occ 2S (180 Card L3-18-6-20-Sl).png

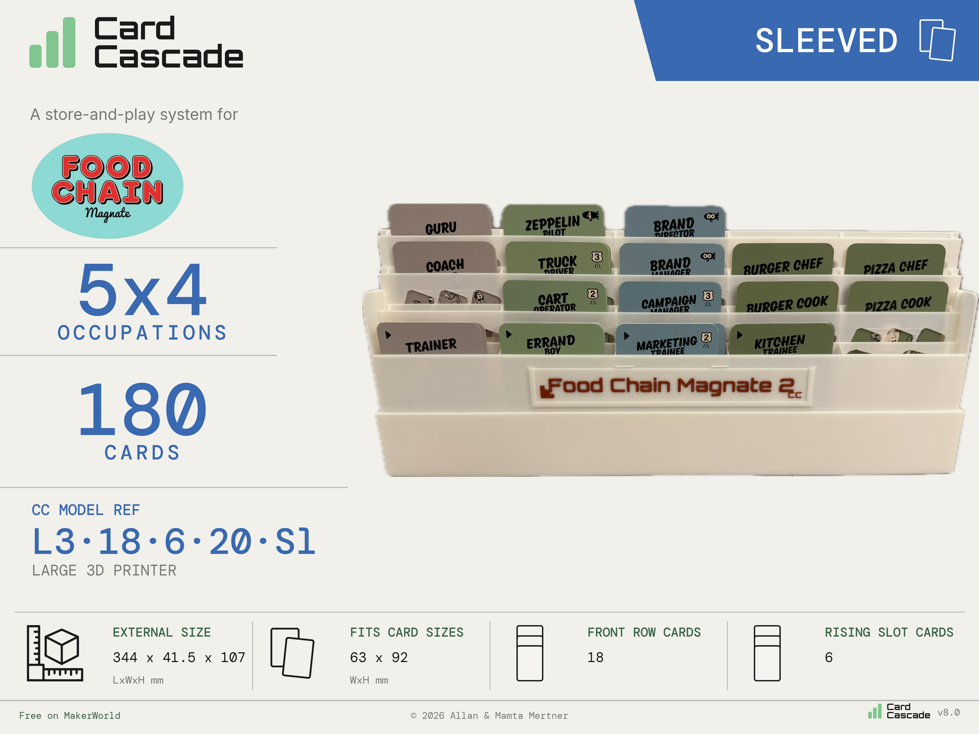
cascades/FCM/FCM Occ 2S (180 Card L3-18-6-20-Sl).png
