amertner/cardcascade/cascades/FCM/labels/Milestones Labels.png

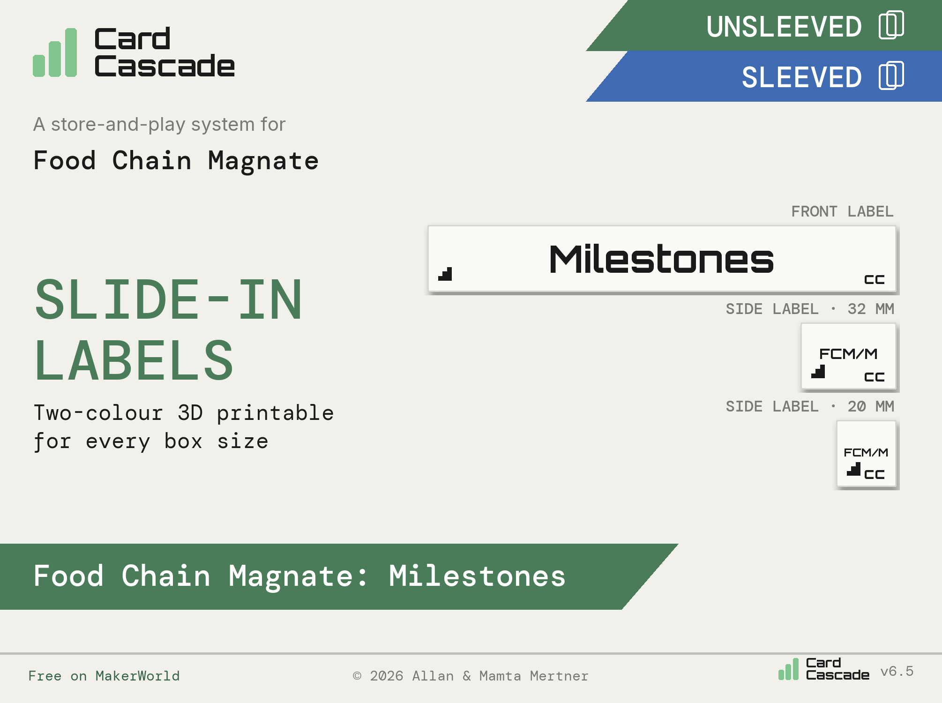
cascades/FCM/labels/Milestones Labels.png
