amertner/cardcascade/cascades/FCM/labels/Occupations Labels.png

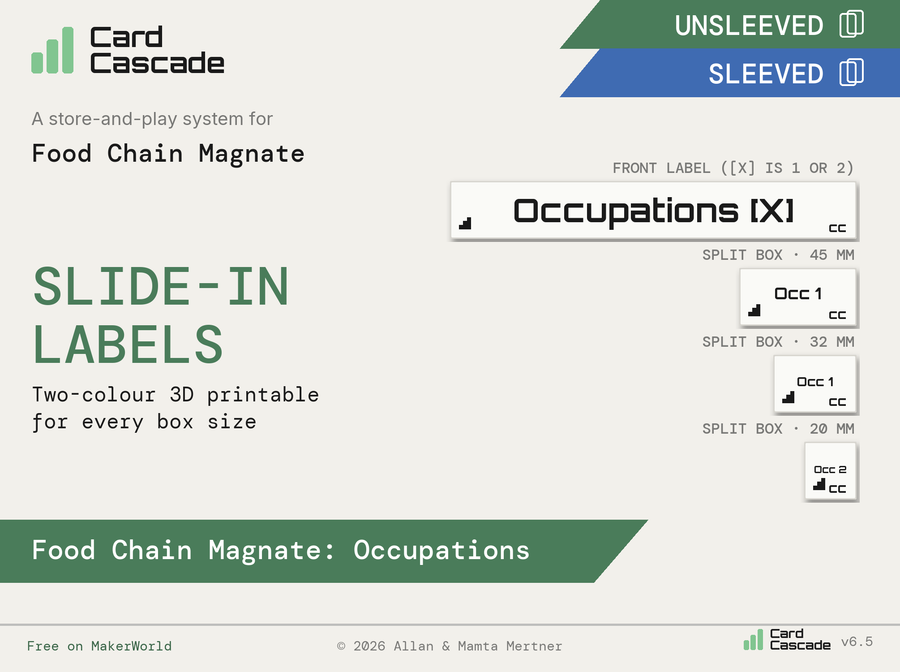
cascades/FCM/labels/Occupations Labels.png
