amertner/cardcascade/cascades/FCM/Pictures/IMG_1568.jpeg

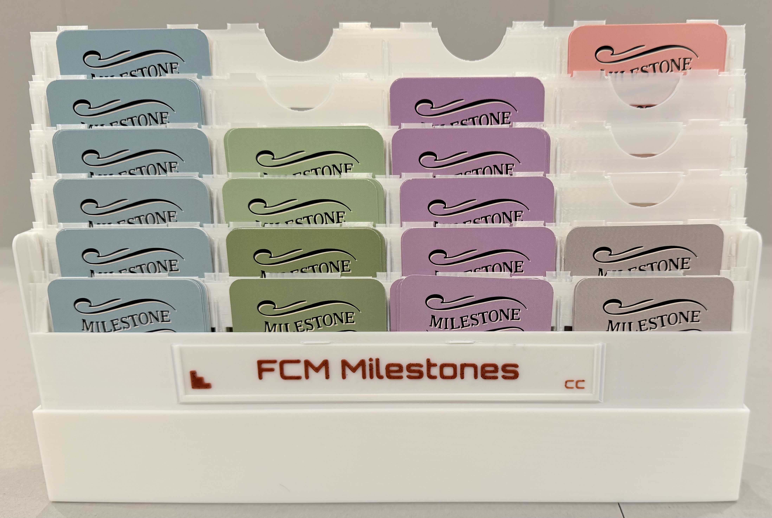
cascades/FCM/Pictures/IMG_1568.jpeg
