amertner/cardcascade/cascades/FCM/Pictures/IMG_1570.jpeg

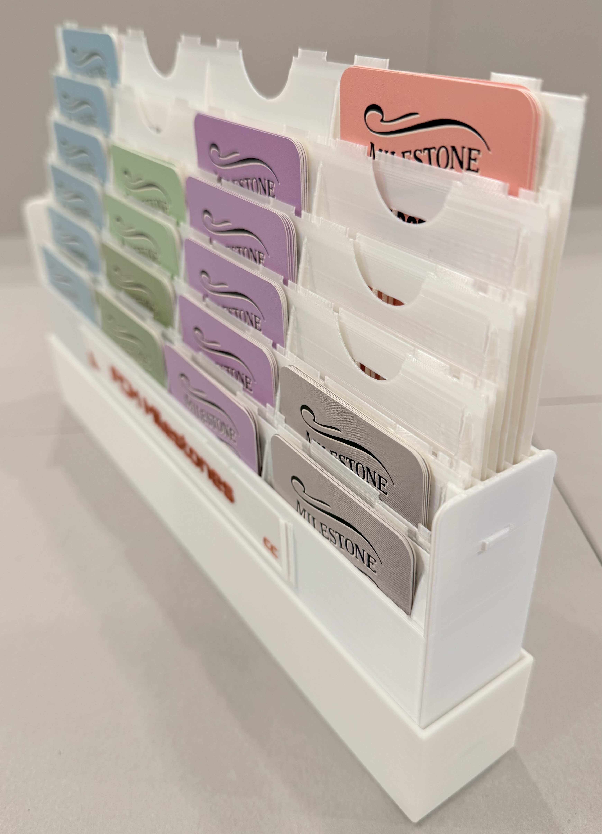
cascades/FCM/Pictures/IMG_1570.jpeg
