amertner/cardcascade/cascades/FCM/Pictures/IMG_1571.jpeg

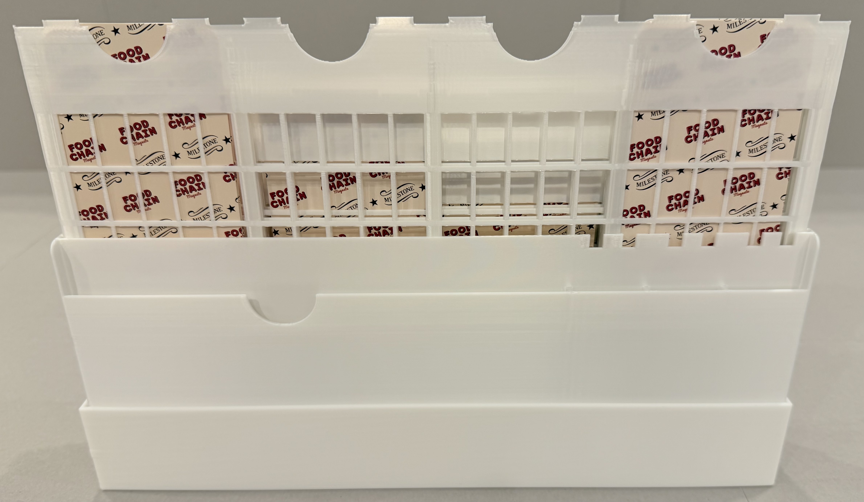
cascades/FCM/Pictures/IMG_1571.jpeg
