amertner/cardcascade/cascades/Innovation/Innovation 3 Ages 5 Expansions Sleeved (S5.15.15.62-Sl).png

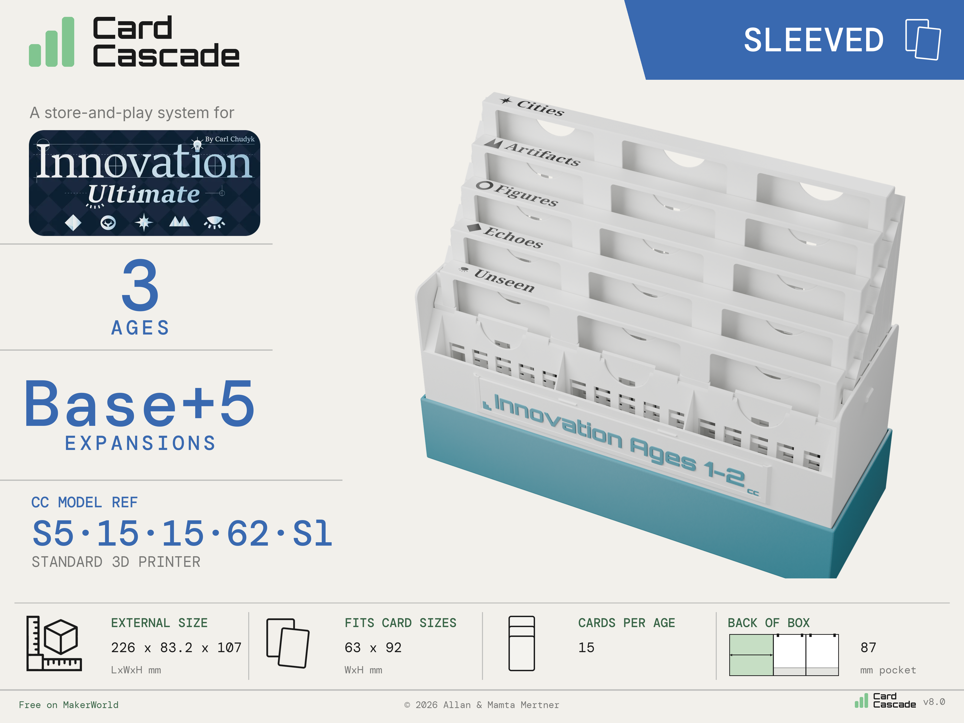
cascades/Innovation/Innovation 3 Ages 5 Expansions Sleeved (S5.15.15.62-Sl).png
