amertner/cardcascade/cascades/Innovation/Innovation 3 Ages 5 Expansions Unsleeved (S5.15.15.45-Un).png

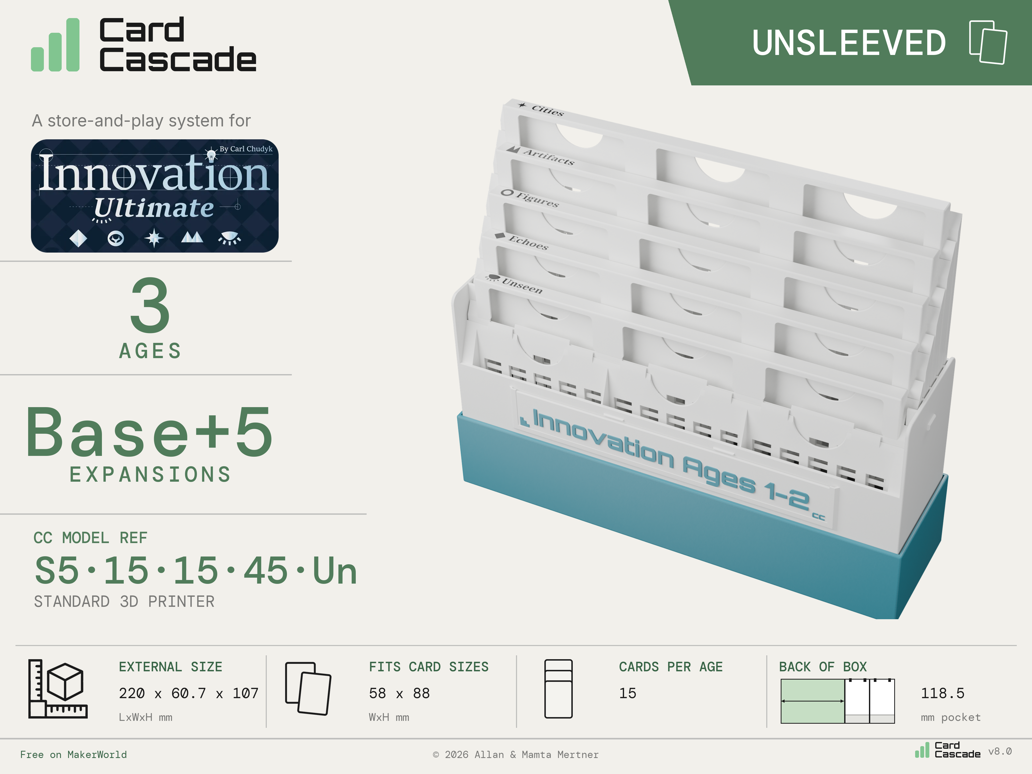
cascades/Innovation/Innovation 3 Ages 5 Expansions Unsleeved (S5.15.15.45-Un).png
