amertner/cardcascade/cascades/Innovation/Innovation 3 Later Ages 5 Expansions Sleeved (S5.10.10.45-Sl).png

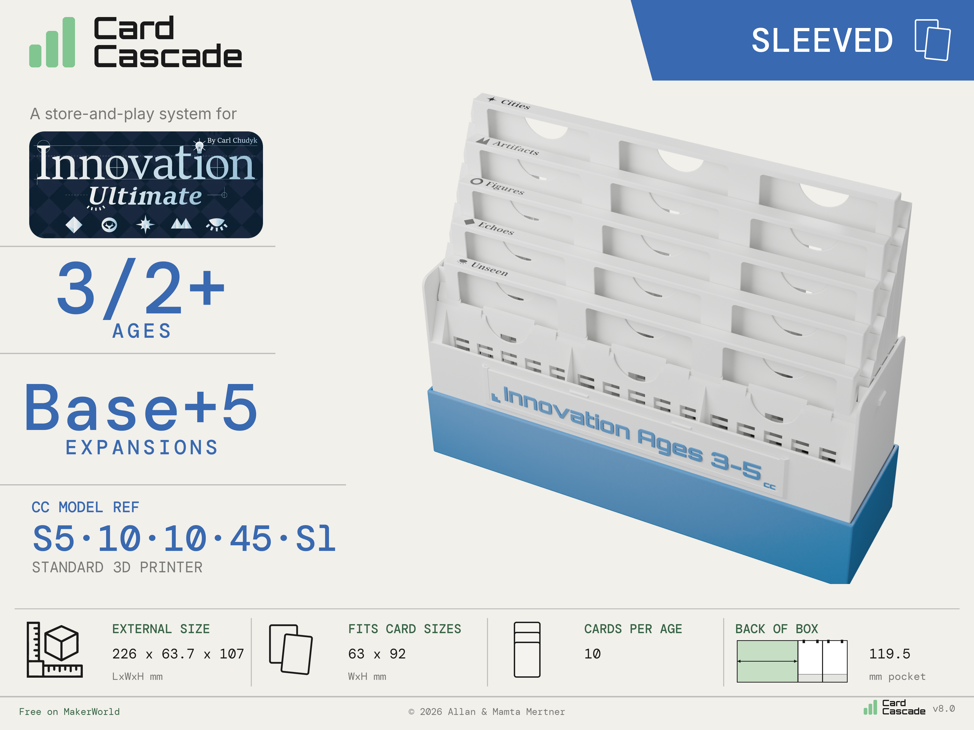
cascades/Innovation/Innovation 3 Later Ages 5 Expansions Sleeved (S5.10.10.45-Sl).png
