amertner/cardcascade/cascades/Innovation/Innovation 4 Ages 5 Expansions Sleeved (M5.15.15.62-Sl).png

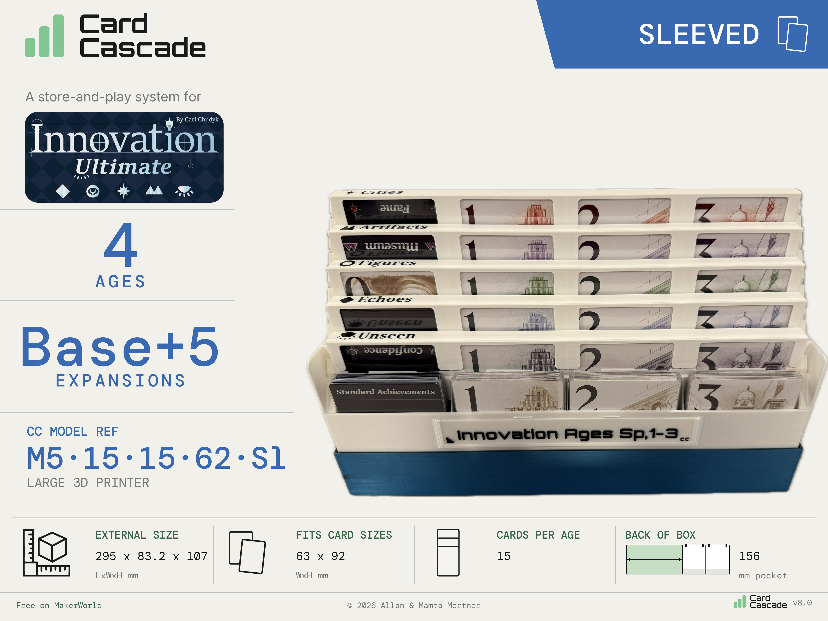
cascades/Innovation/Innovation 4 Ages 5 Expansions Sleeved (M5.15.15.62-Sl).png
