amertner/cardcascade/cascades/Innovation/Innovation 4 Later Ages 5 Expansions Sleeved (M5.10.10.45-Sl).png

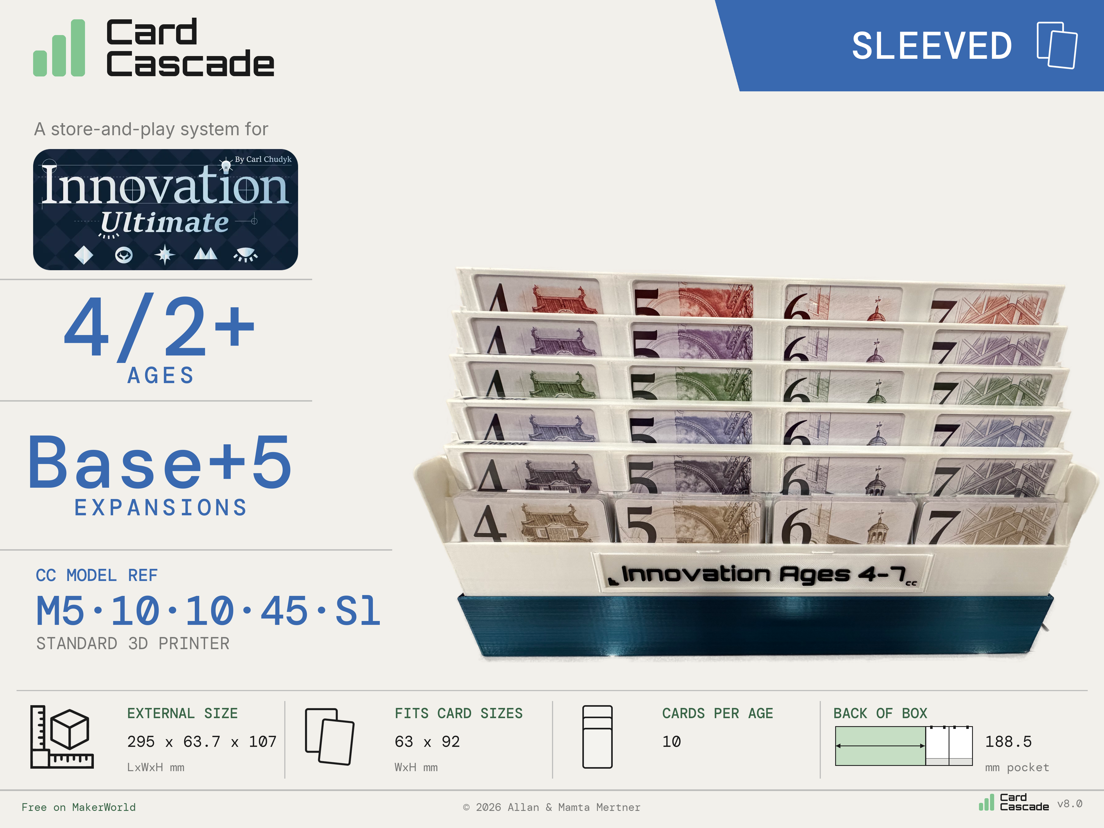
cascades/Innovation/Innovation 4 Later Ages 5 Expansions Sleeved (M5.10.10.45-Sl).png
