amertner/cardcascade/cascades/Innovation/Innovation Cascade.gif

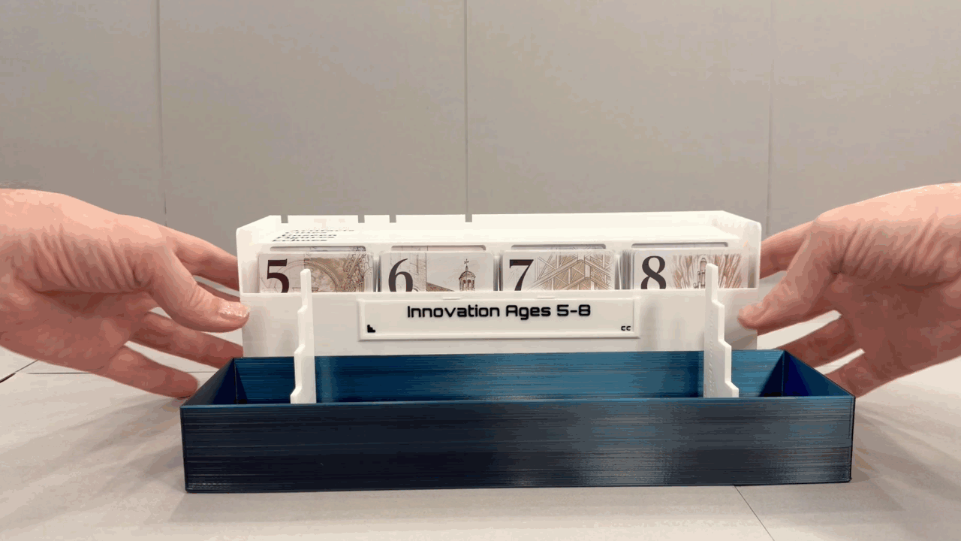
cascades/Innovation/Innovation Cascade.gif
