amertner/cardcascade/cascades/Innovation/Innovation Single Mini Sleeved (XS5.15.10.45-Sl).png

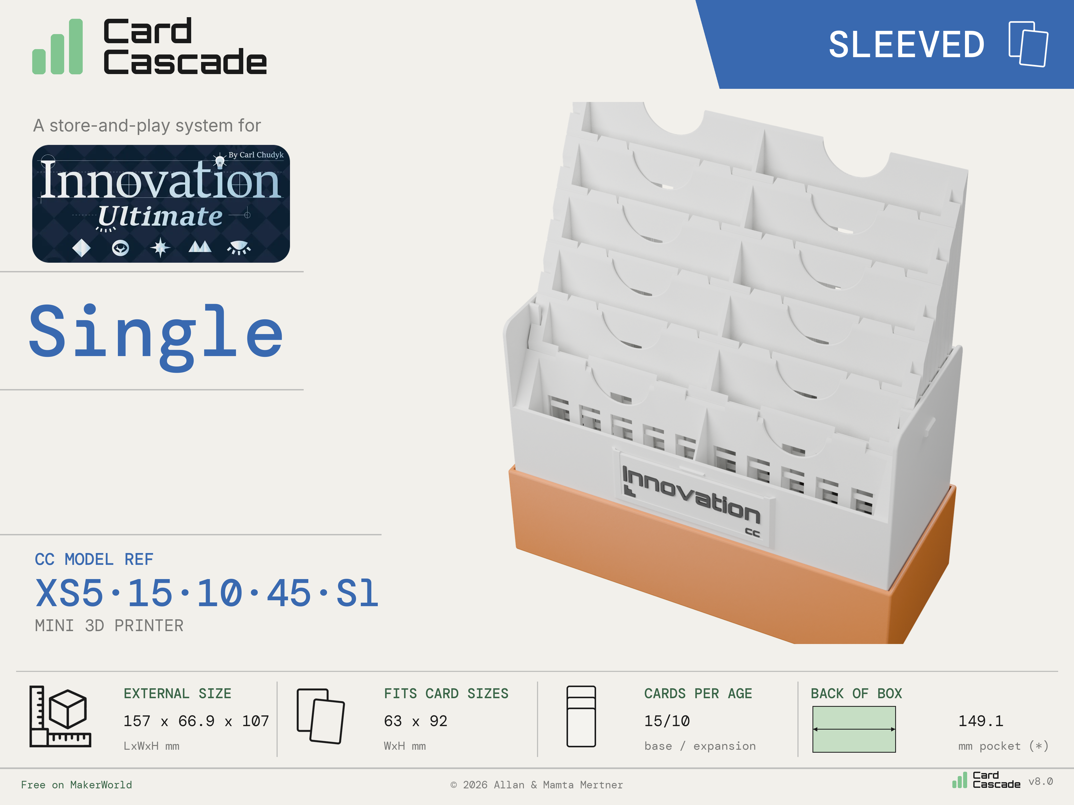
cascades/Innovation/Innovation Single Mini Sleeved (XS5.15.10.45-Sl).png
