amertner/cardcascade/cascades/Innovation/Innovation Single Mini Unsleeved (XS5.15.10.32-Un).png

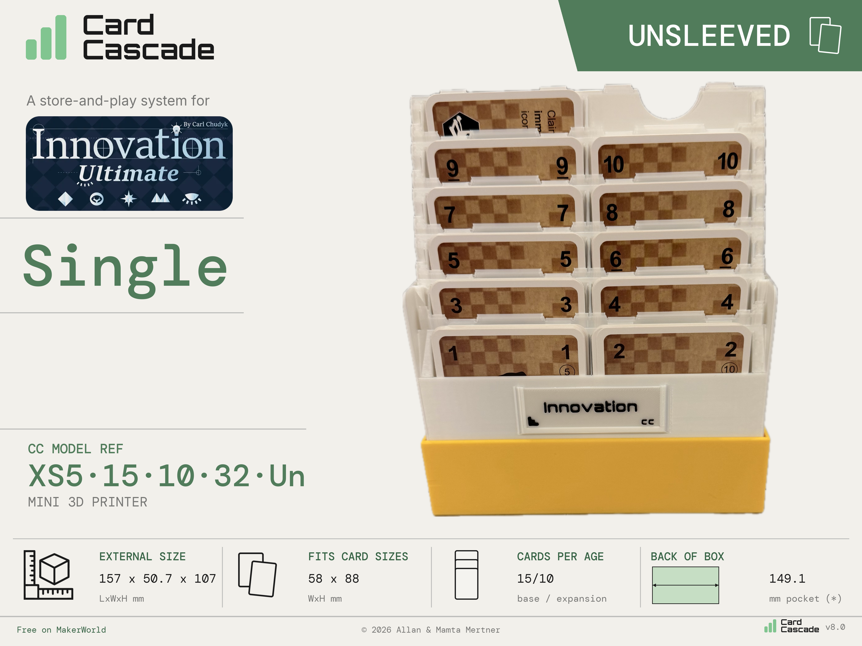
cascades/Innovation/Innovation Single Mini Unsleeved (XS5.15.10.32-Un).png
