amertner/cardcascade/cascades/Innovation/Innovation Single Set Sleeved (S3.15.10.32-Sl).png

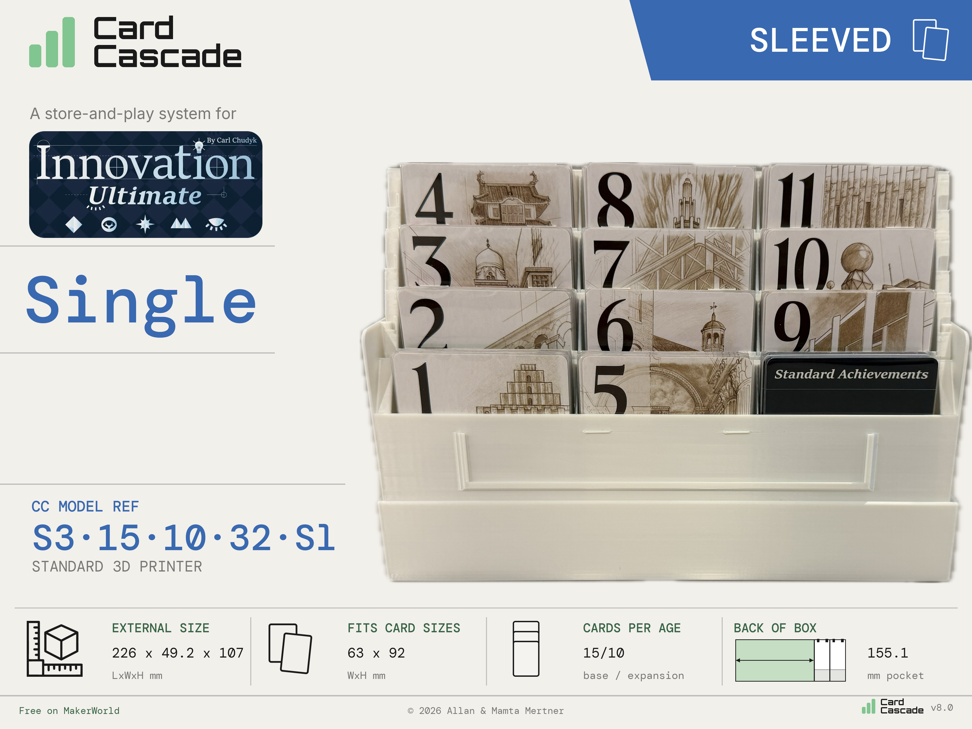
cascades/Innovation/Innovation Single Set Sleeved (S3.15.10.32-Sl).png
