amertner/cardcascade/cascades/Innovation/Innovation Three Expansions Sleeved (M8.16.10-16.62-Sl).png

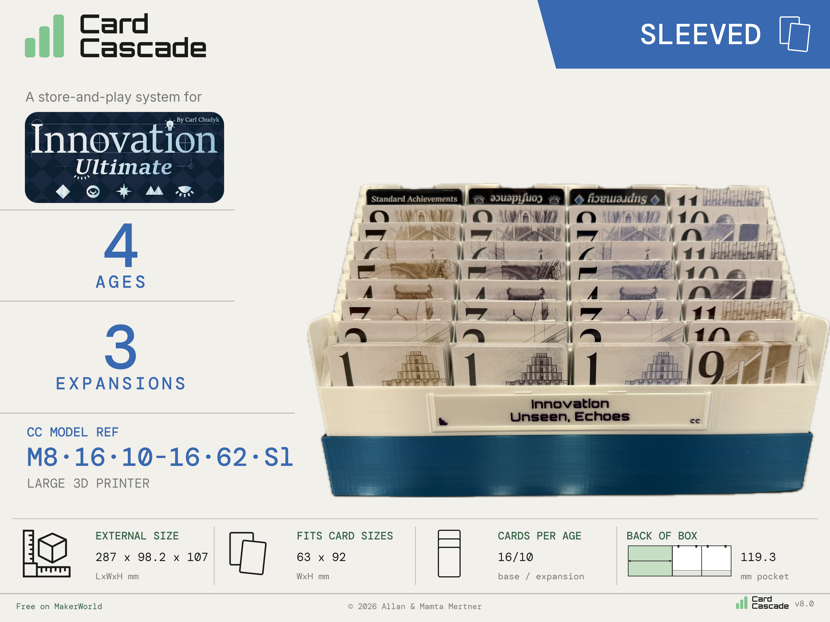
cascades/Innovation/Innovation Three Expansions Sleeved (M8.16.10-16.62-Sl).png
