amertner/cardcascade/cascades/Innovation/IU Hero Landscape.png

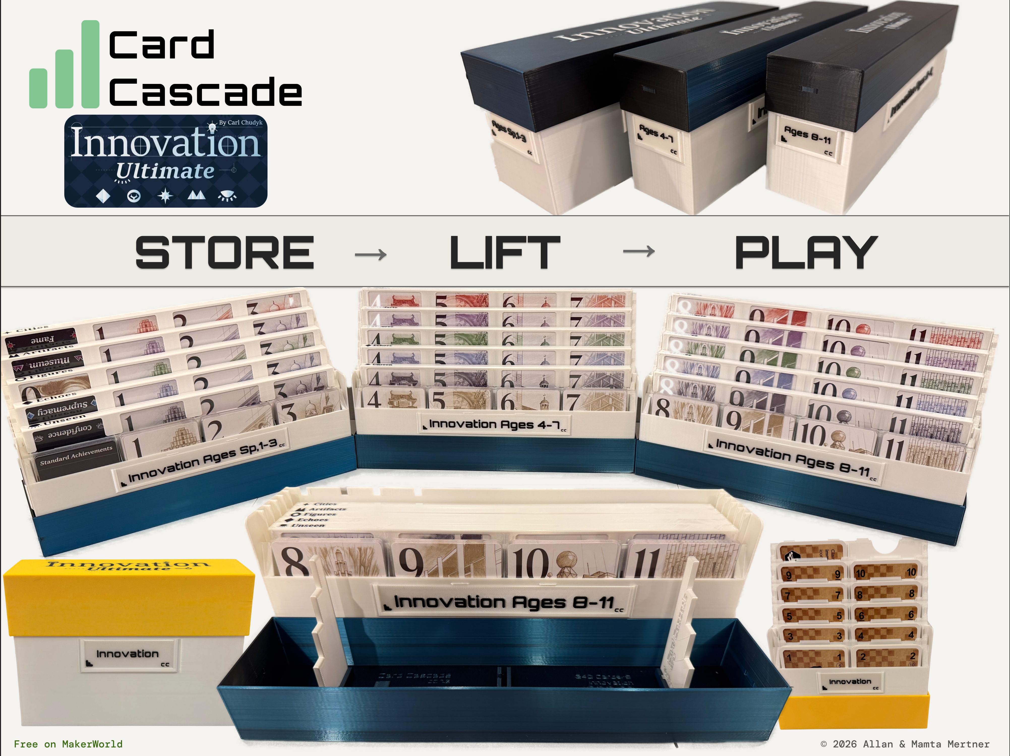
cascades/Innovation/IU Hero Landscape.png
