amertner/cardcascade/cascades/Innovation/IU Hero Portrait.png

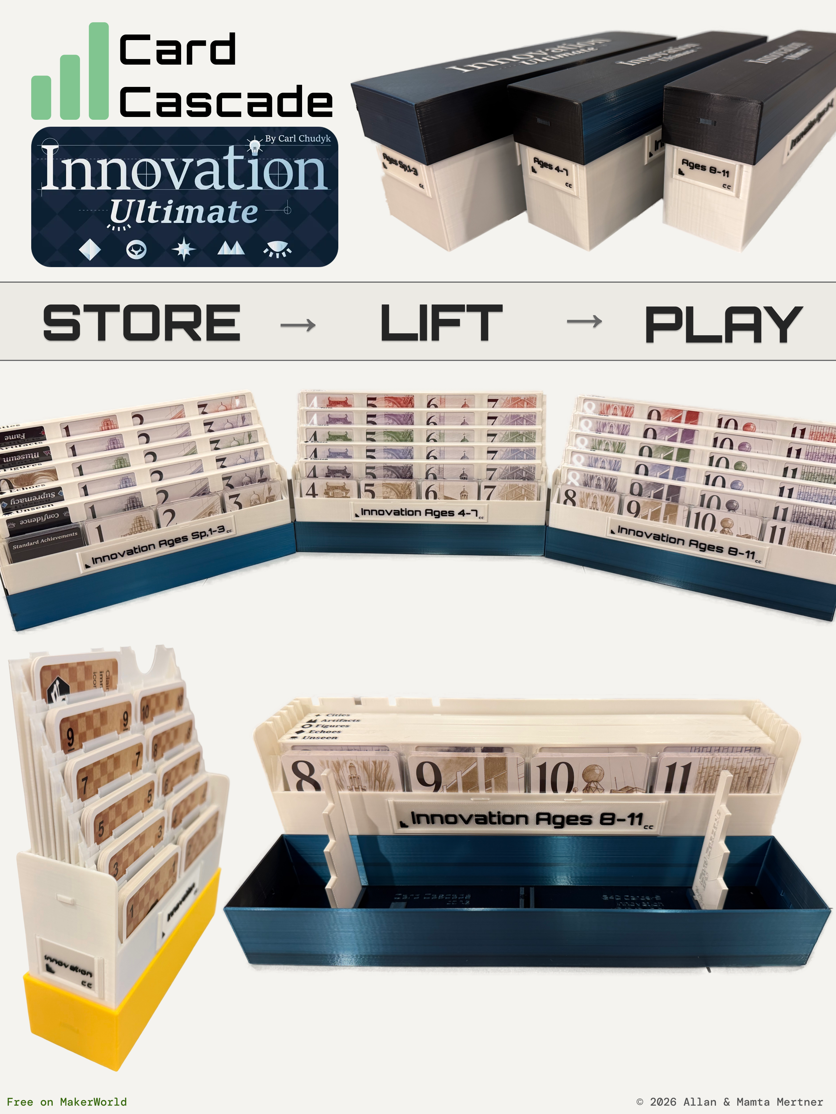
cascades/Innovation/IU Hero Portrait.png
