amertner/cardcascade/cascades/Innovation/labels/Innovation 3-Age Cascades Labels.png

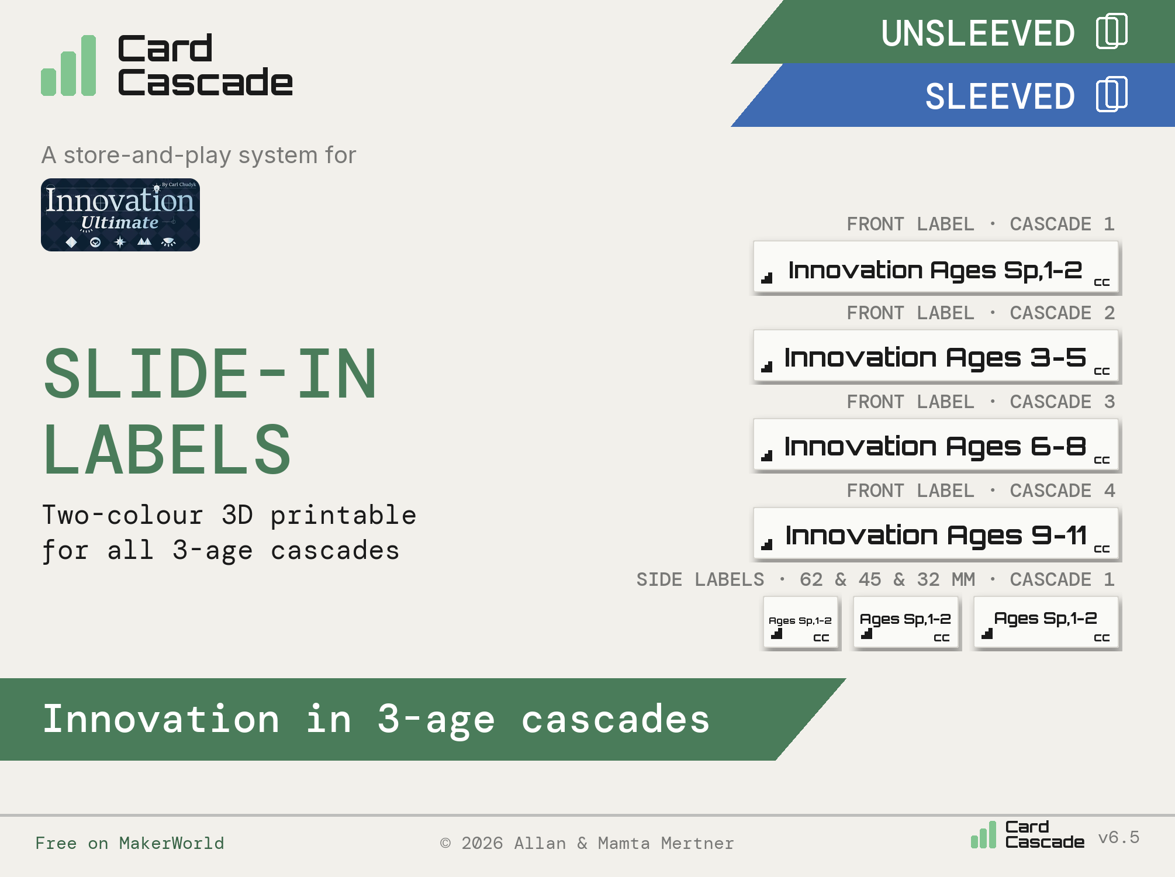
cascades/Innovation/labels/Innovation 3-Age Cascades Labels.png
