amertner/cardcascade/cascades/Innovation/labels/Innovation 3-Expansion Cascades Labels.png

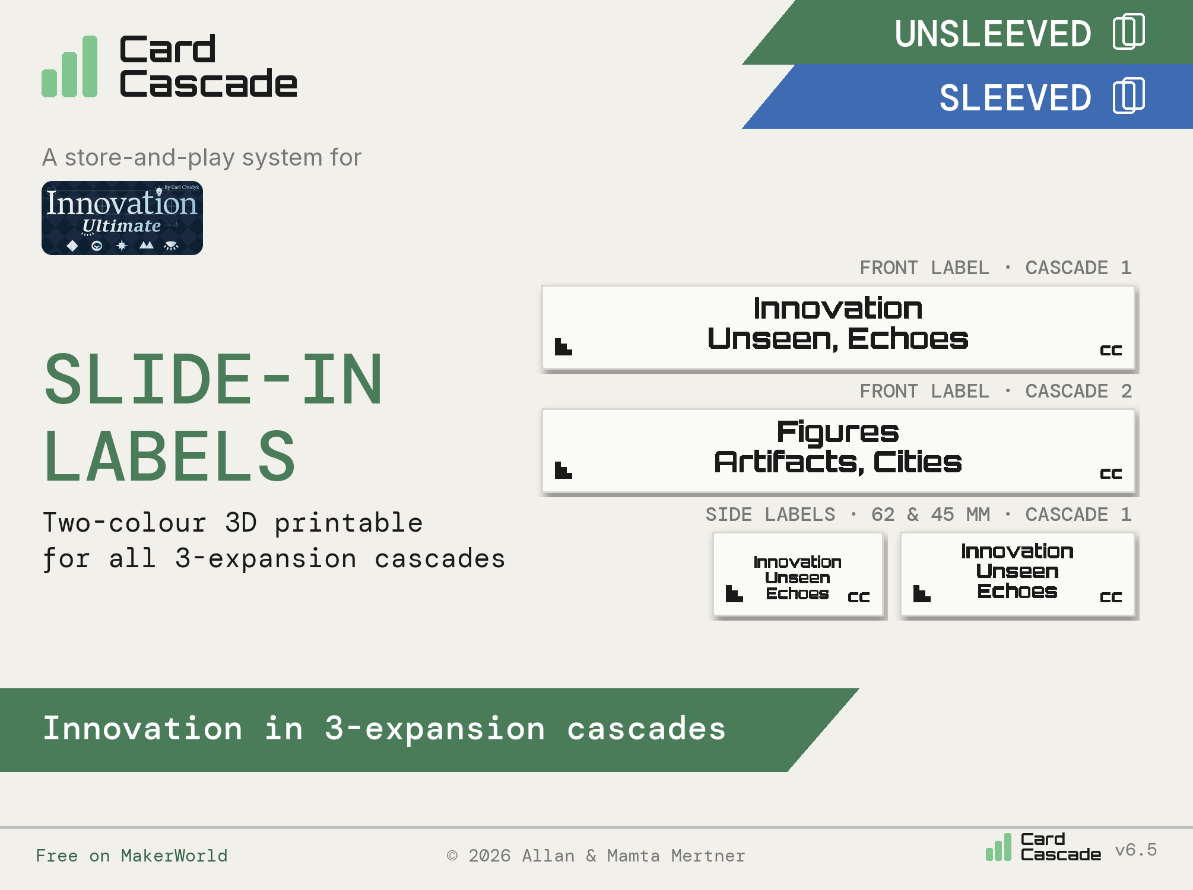
cascades/Innovation/labels/Innovation 3-Expansion Cascades Labels.png
