amertner/cardcascade/cascades/Innovation/labels/Single Set Labels.png

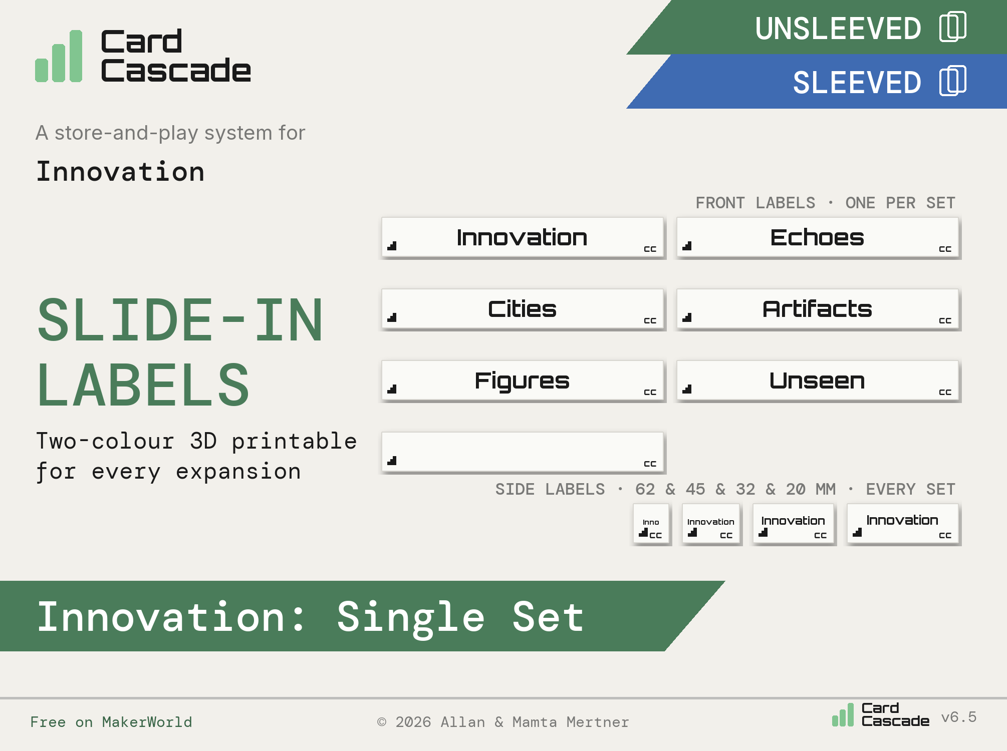
cascades/Innovation/labels/Single Set Labels.png
