amertner/cardcascade/cascades/Innovation/Photos/3 Cascaded display.png

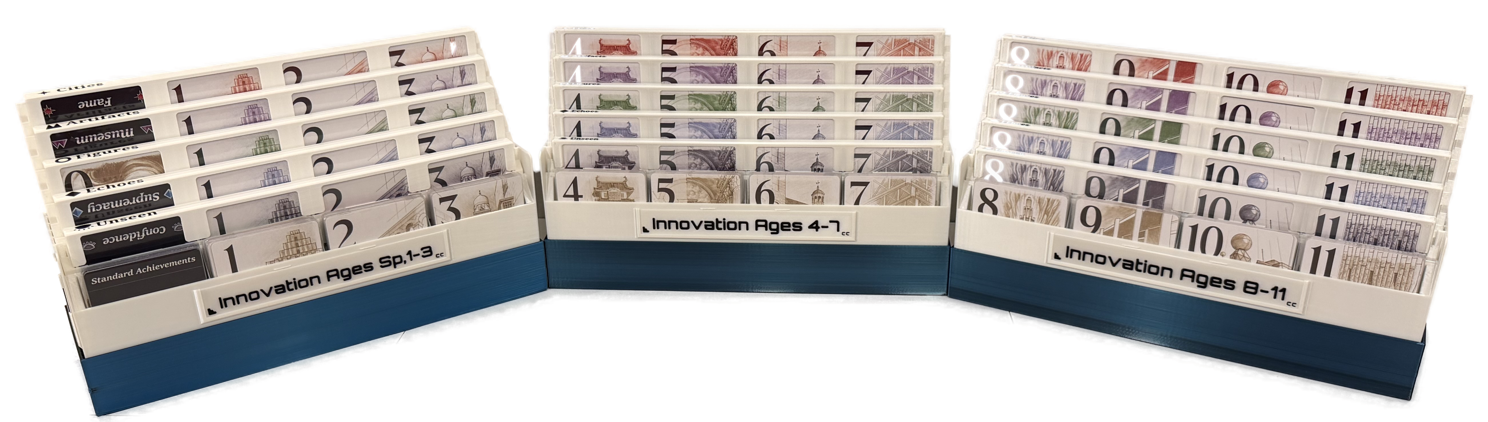
cascades/Innovation/Photos/3 Cascaded display.png
