amertner/cardcascade/cascades/Innovation/Photos/3 Closed Boxes.jpeg

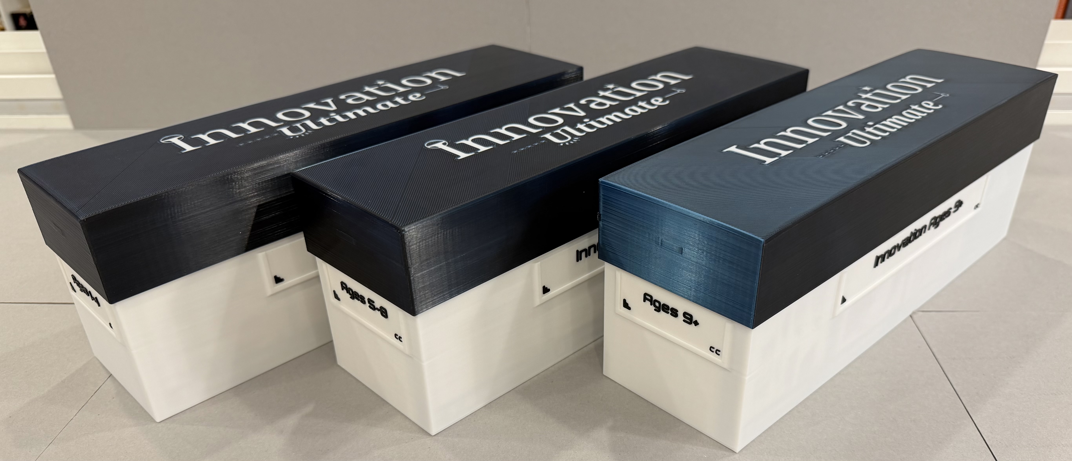
cascades/Innovation/Photos/3 Closed Boxes.jpeg
