amertner/cardcascade/cascades/Innovation/Photos/3 Open but uncascaded boxes.jpeg

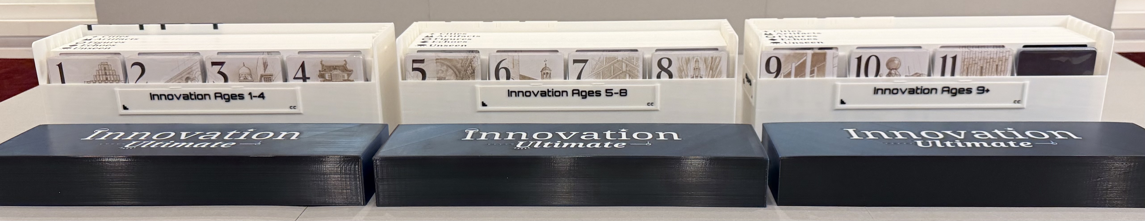
cascades/Innovation/Photos/3 Open but uncascaded boxes.jpeg
