amertner/cardcascade/cascades/Innovation/Photos/3 Open Cascades.jpeg

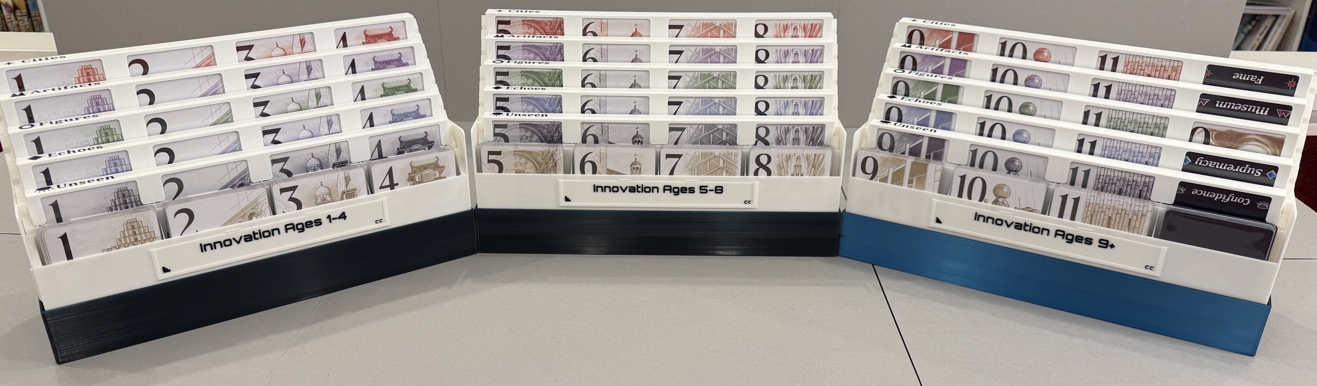
cascades/Innovation/Photos/3 Open Cascades.jpeg
