amertner/cardcascade/cascades/Innovation/Photos/All toppers.jpeg

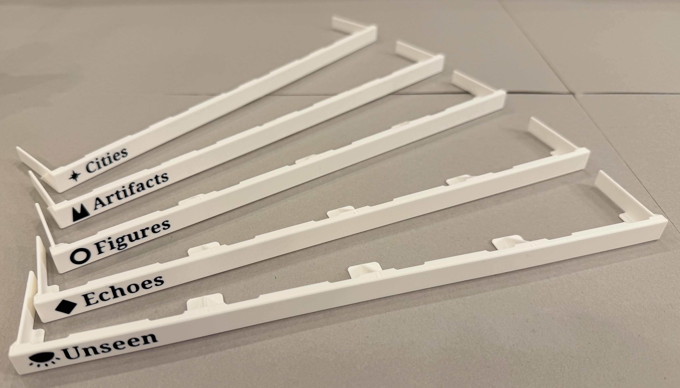
cascades/Innovation/Photos/All toppers.jpeg
