amertner/cardcascade/cascades/Innovation/Photos/Cascaded with Echoes topper removed.jpeg

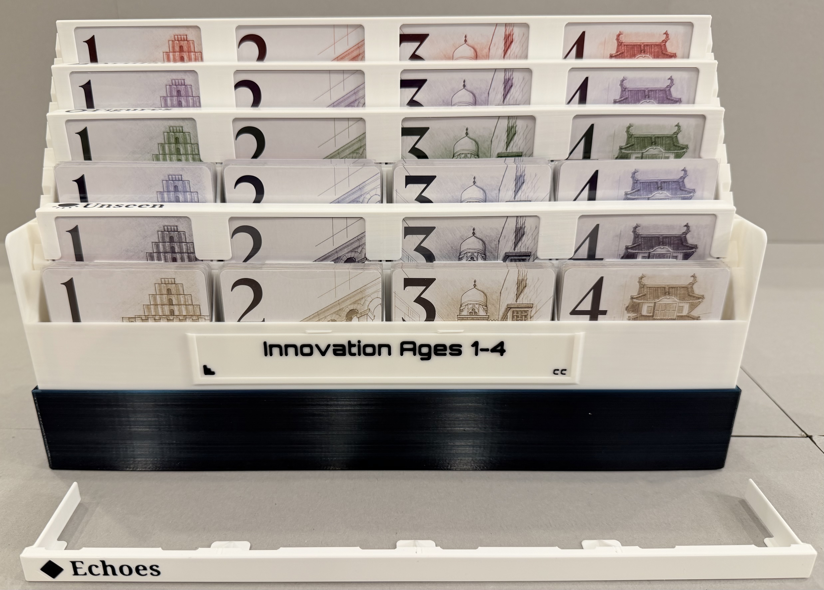
cascades/Innovation/Photos/Cascaded with Echoes topper removed.jpeg
