amertner/cardcascade/cascades/Innovation/Photos/Closeup top down of inno 1-4.jpeg

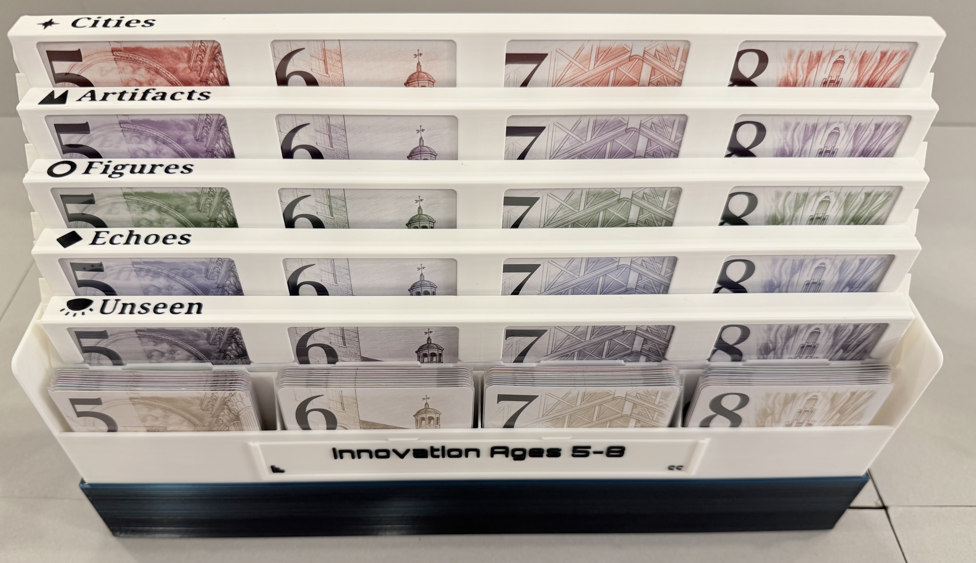
cascades/Innovation/Photos/Closeup top down of inno 1-4.jpeg
