amertner/cardcascade/cascades/Innovation/Photos/IMG_1413.png

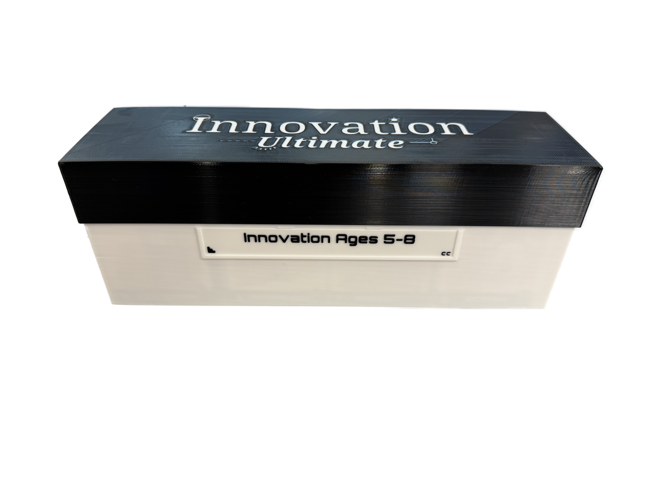
cascades/Innovation/Photos/IMG_1413.png
