amertner/cardcascade/cascades/Innovation/Photos/IU Box 1 Open Uncascaded.png

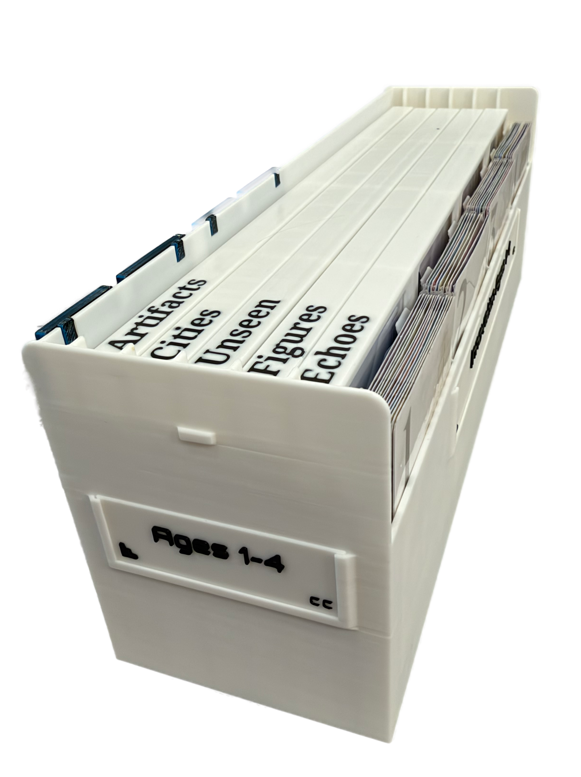
cascades/Innovation/Photos/IU Box 1 Open Uncascaded.png
