amertner/cardcascade/cascades/Innovation/Photos/IU Closed Top Angle.png

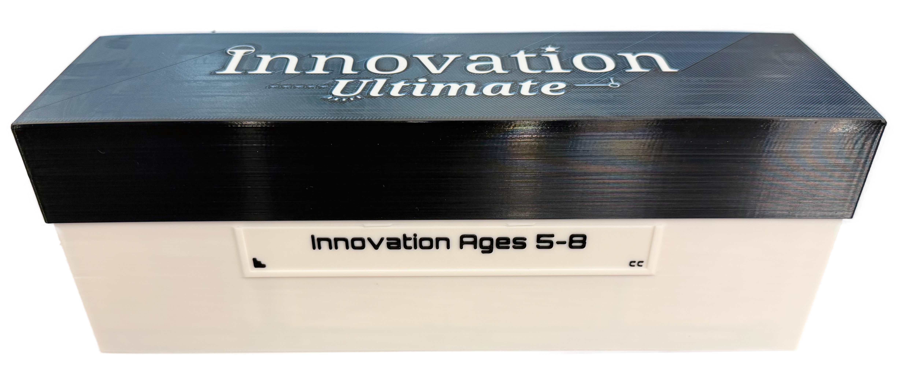
cascades/Innovation/Photos/IU Closed Top Angle.png
