amertner/cardcascade/cascades/Innovation/Photos/Single/Back.jpeg

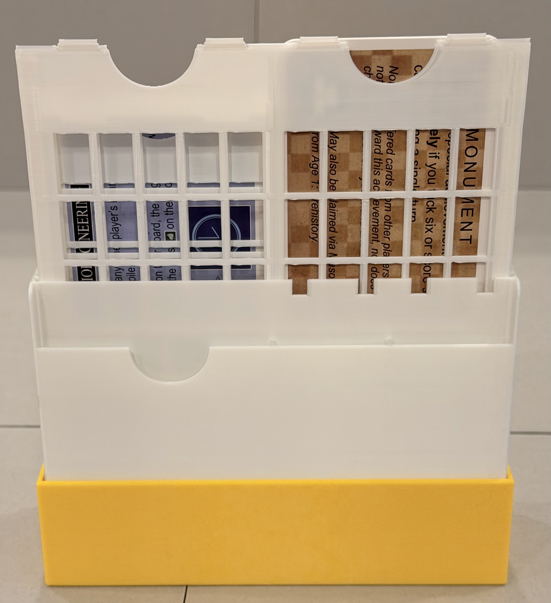
cascades/Innovation/Photos/Single/Back.jpeg
