amertner/cardcascade/cascades/Innovation/Photos/Single/Box closed.jpeg

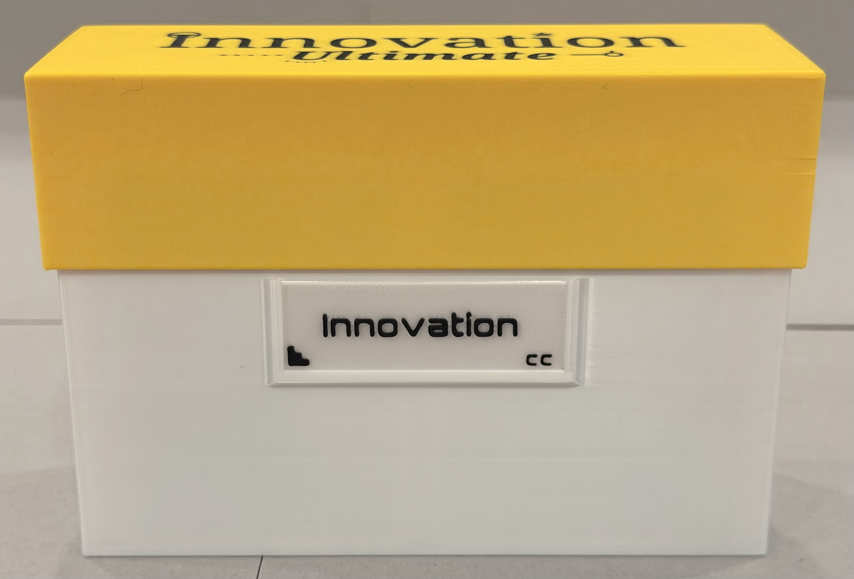
cascades/Innovation/Photos/Single/Box closed.jpeg
