amertner/cardcascade/cascades/Innovation/Photos/Single/Front angle cascaded.jpeg

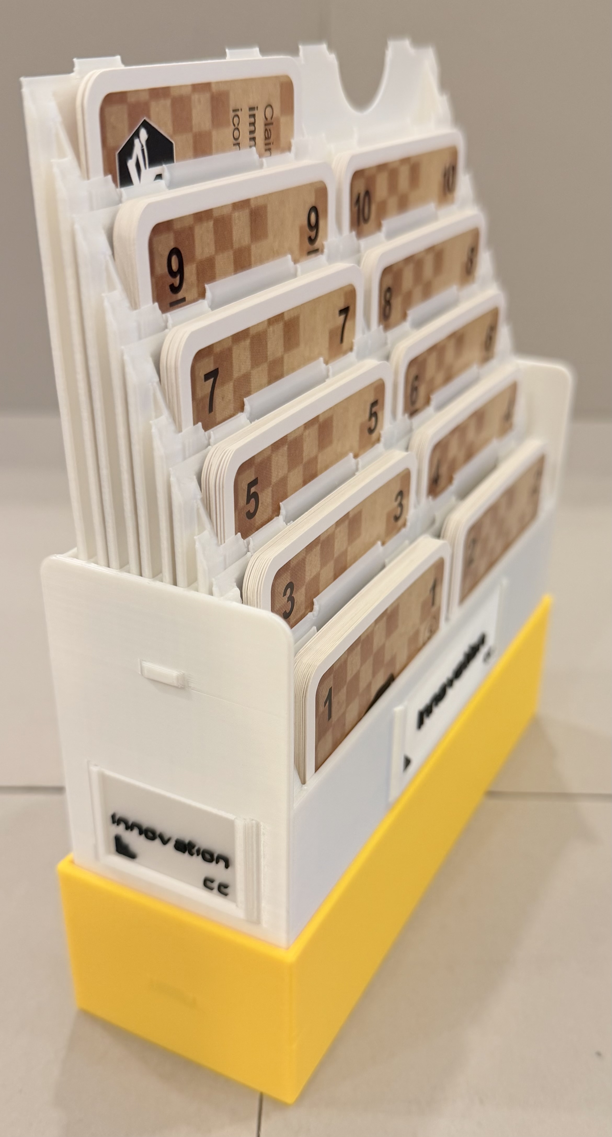
cascades/Innovation/Photos/Single/Front angle cascaded.jpeg
