amertner/cardcascade/cascades/Innovation/Photos/Single/Front Cascaded.jpeg

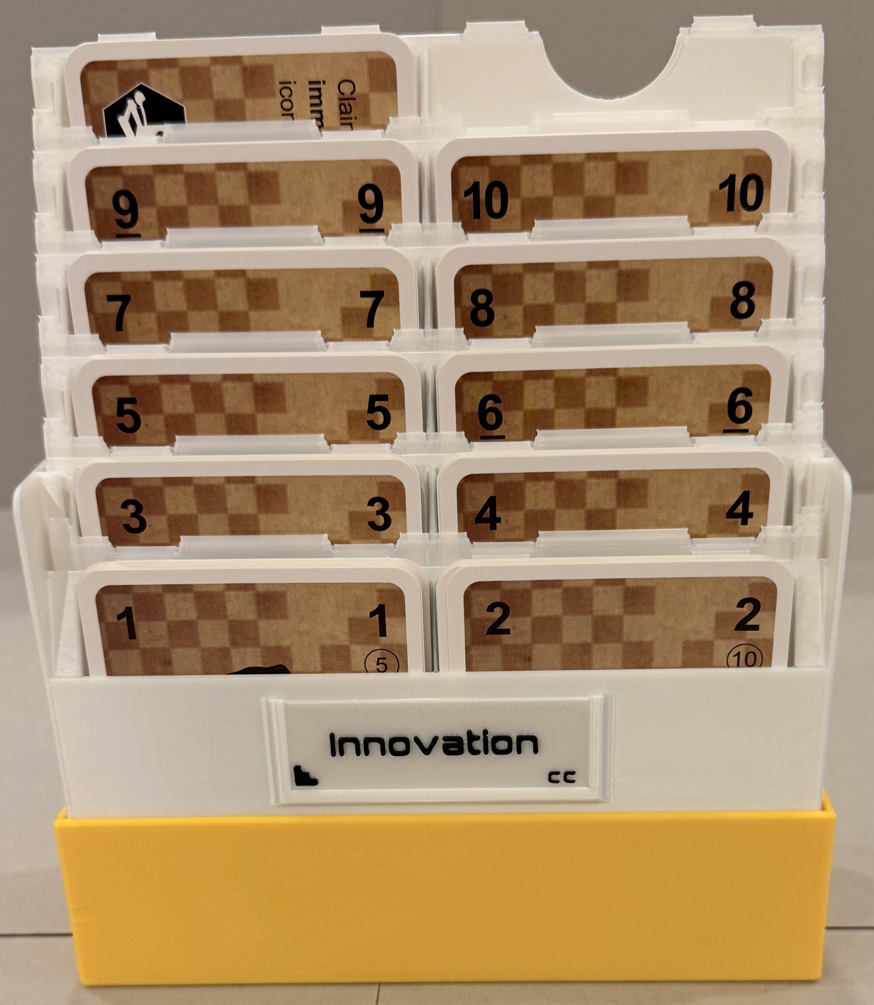
cascades/Innovation/Photos/Single/Front Cascaded.jpeg
