amertner/cardcascade/cascades/Innovation/Photos/Single/Side.jpeg

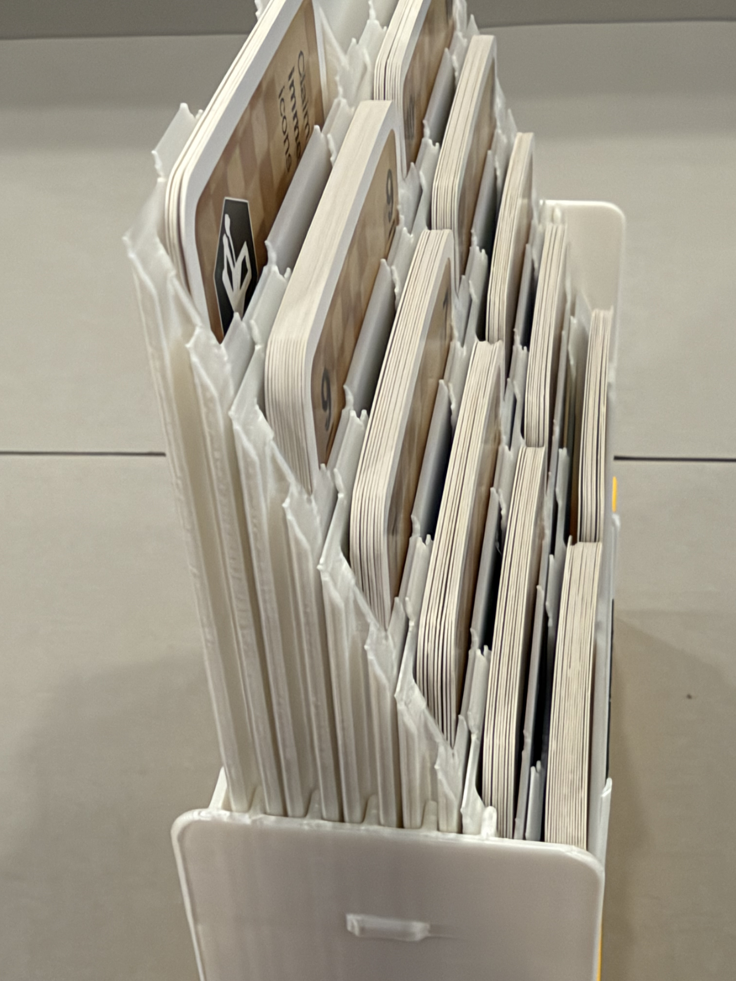
cascades/Innovation/Photos/Single/Side.jpeg
