amertner/cardcascade/cascades/Innovation/Photos/v7/3 Cascaded angled.png

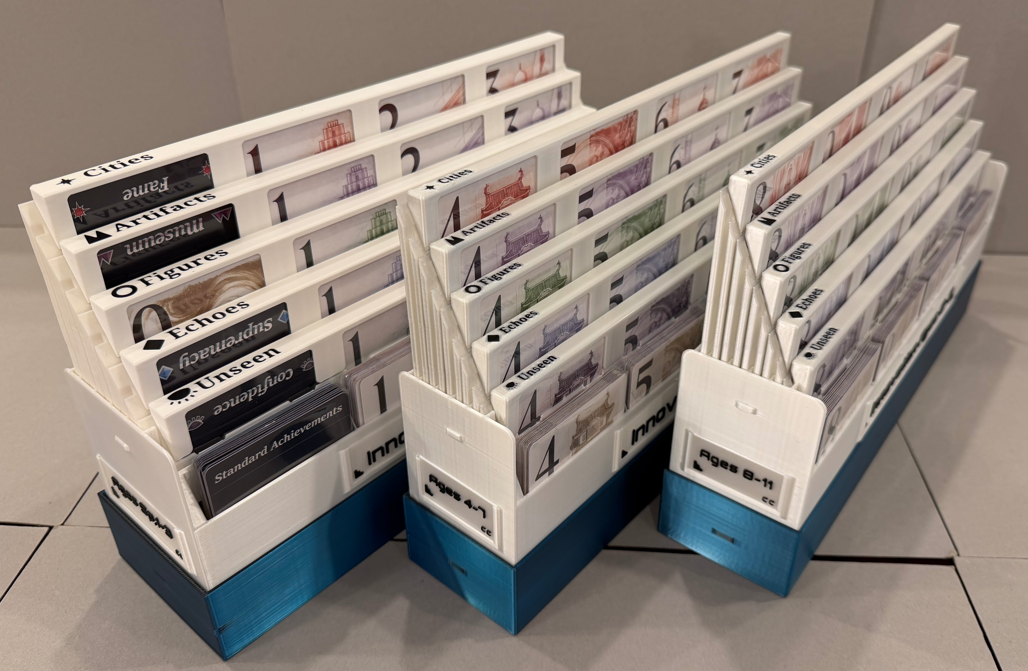
cascades/Innovation/Photos/v7/3 Cascaded angled.png
