amertner/cardcascade/cascades/Innovation/Photos/v7/3 Closed angled.png

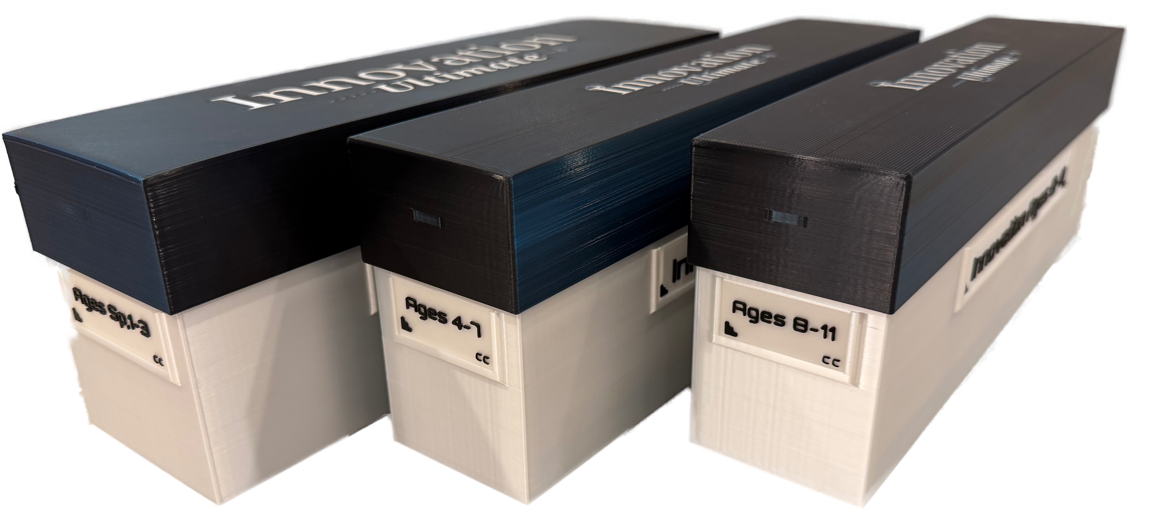
cascades/Innovation/Photos/v7/3 Closed angled.png
