amertner/cardcascade/cascades/Innovation/Photos/v7/Age 4-8 angled top Cascaded.png

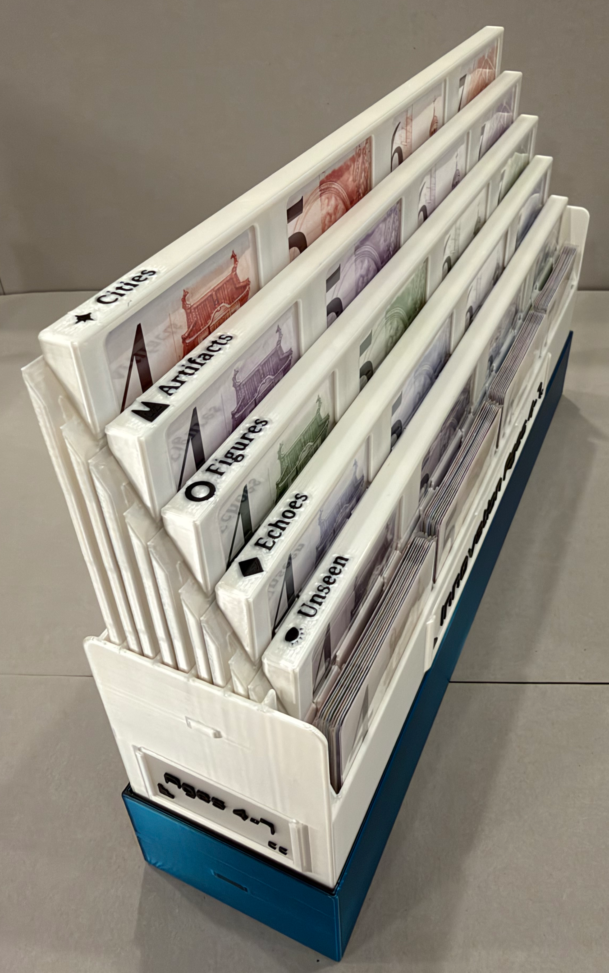
cascades/Innovation/Photos/v7/Age 4-8 angled top Cascaded.png
