amertner/cardcascade/cascades/Innovation/Photos/v7/Age 8-11 opened angled front.png

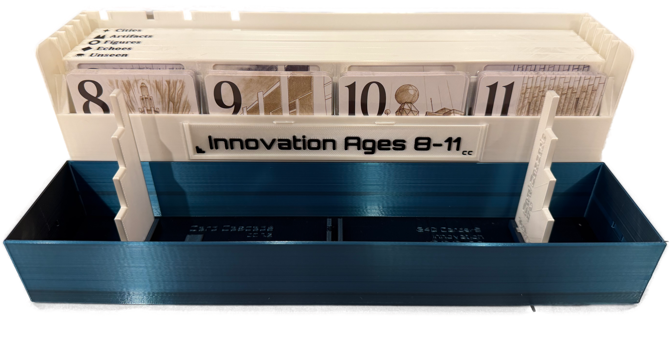
cascades/Innovation/Photos/v7/Age 8-11 opened angled front.png
