amertner/cardcascade/cascades/Innovation/Photos/v7/Age 8-11 opened top.png

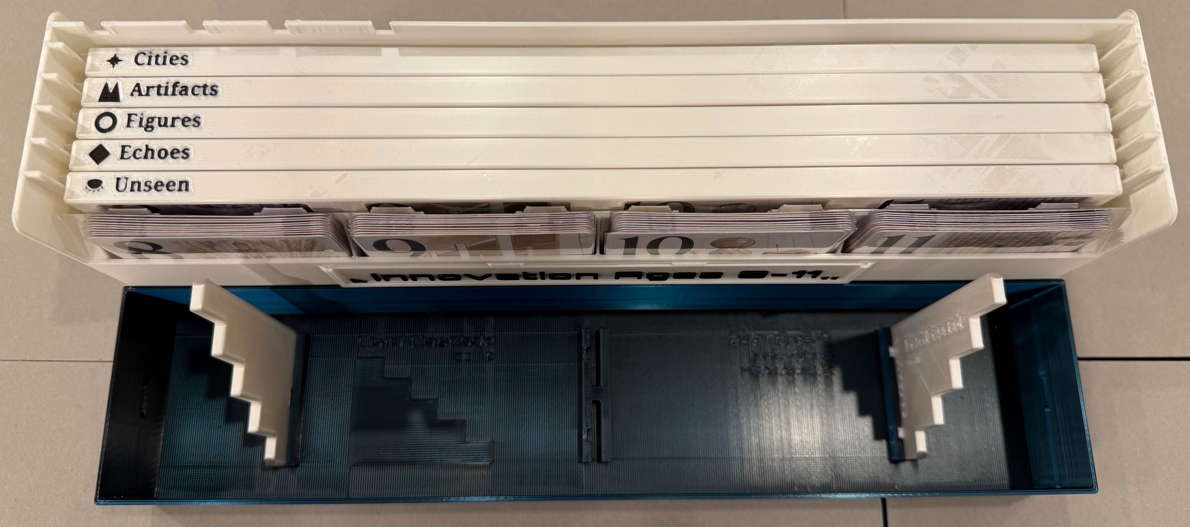
cascades/Innovation/Photos/v7/Age 8-11 opened top.png
