amertner/cardcascade/cascades/Innovation/Photos/v7/Box 1 angled top Cascaded.png

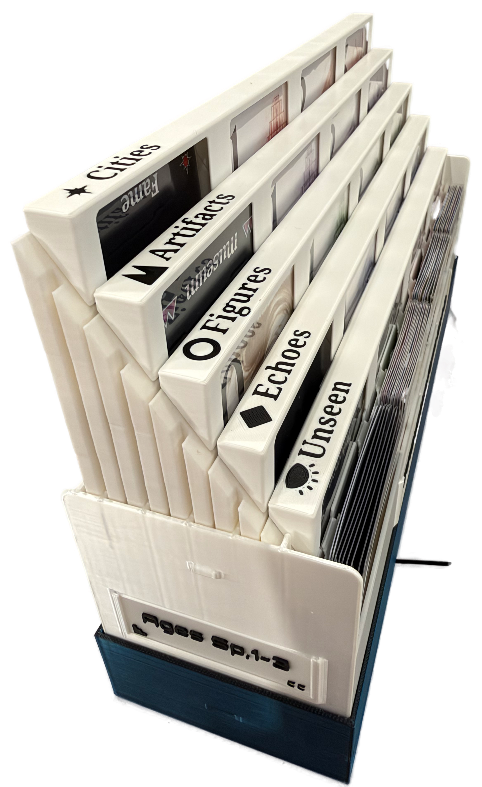
cascades/Innovation/Photos/v7/Box 1 angled top Cascaded.png
