amertner/cardcascade/cascades/Innovation/Photos/v7/Ready to play.png

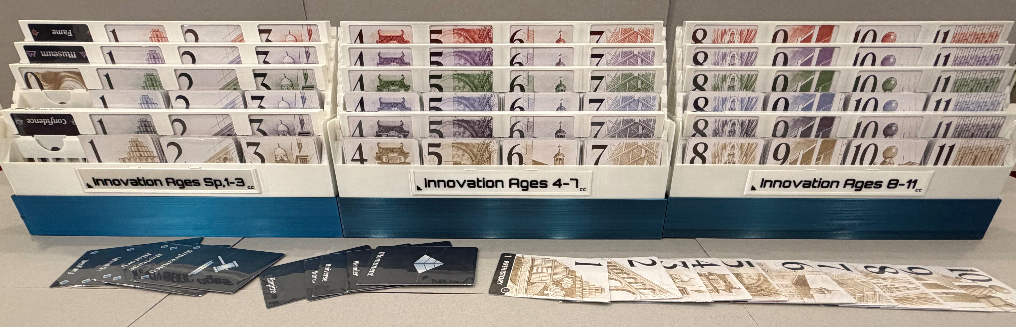
cascades/Innovation/Photos/v7/Ready to play.png
