amertner/cardcascade/cascades/MiniCards/labels/Blank Labels.png

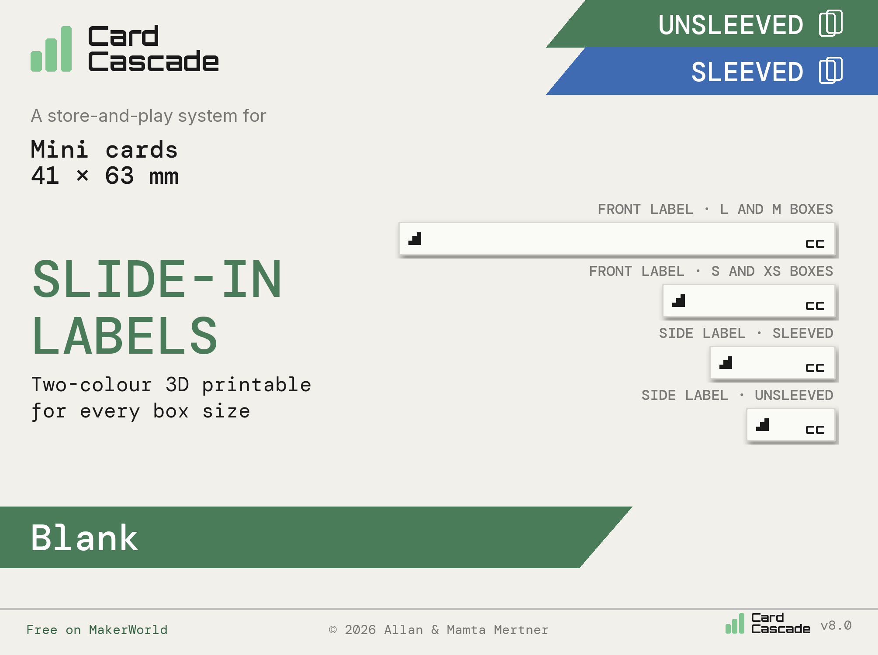
cascades/MiniCards/labels/Blank Labels.png
