amertner/cardcascade/cascades/MiniCards/Mini Cards 120 Card Sleeved (86-XS5.10.10.45-Sl).png

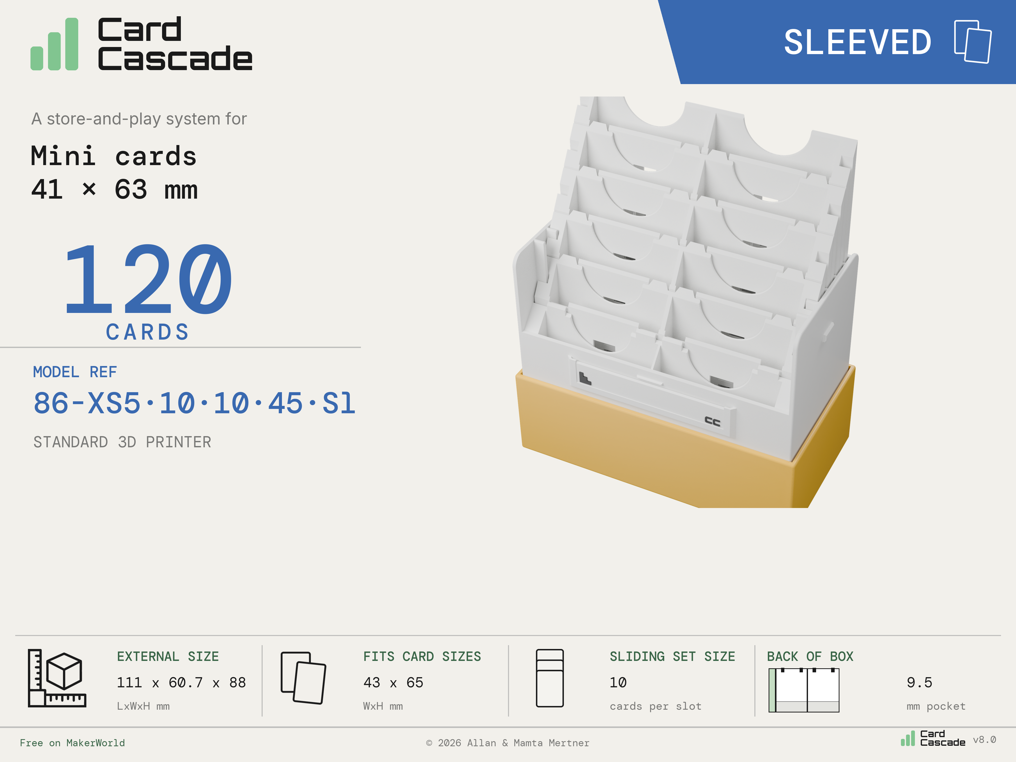
cascades/MiniCards/Mini Cards 120 Card Sleeved (86-XS5.10.10.45-Sl).png
