amertner/cardcascade/cascades/MiniCards/Mini Cards 216 Card Unsleeved (86-S5.12.12.32-Un).png

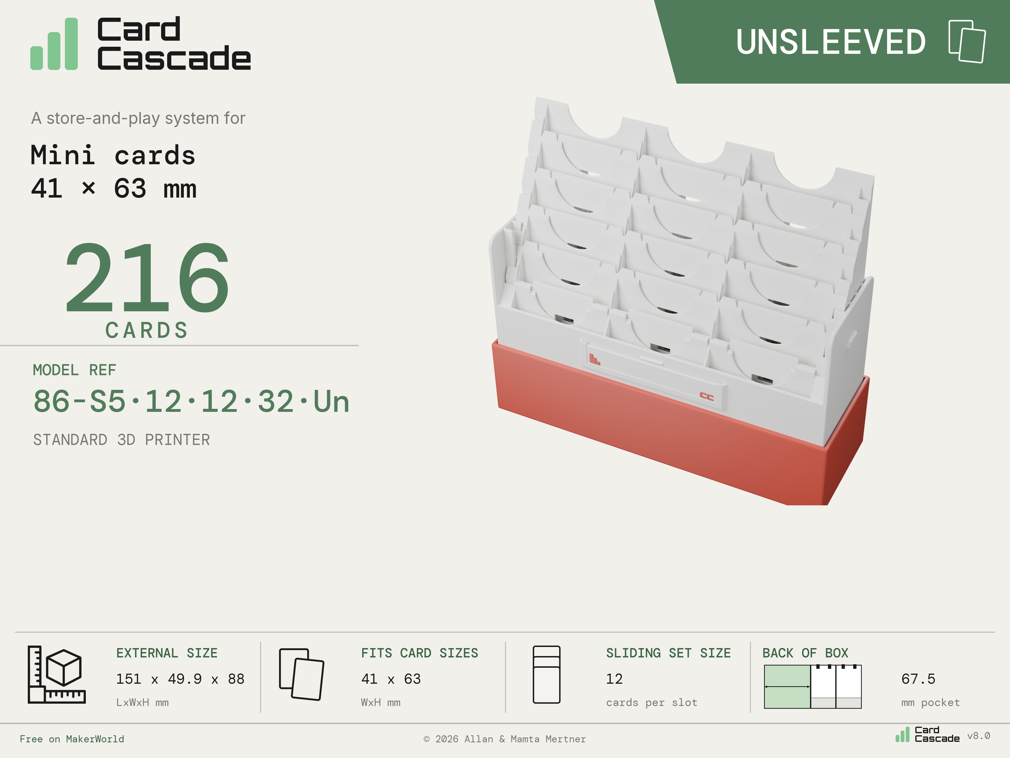
cascades/MiniCards/Mini Cards 216 Card Unsleeved (86-S5.12.12.32-Un).png
