amertner/cardcascade/cascades/MiniCards/Mini Cards 288 Card Sleeved (86-M5.12.12.45-Sl).png

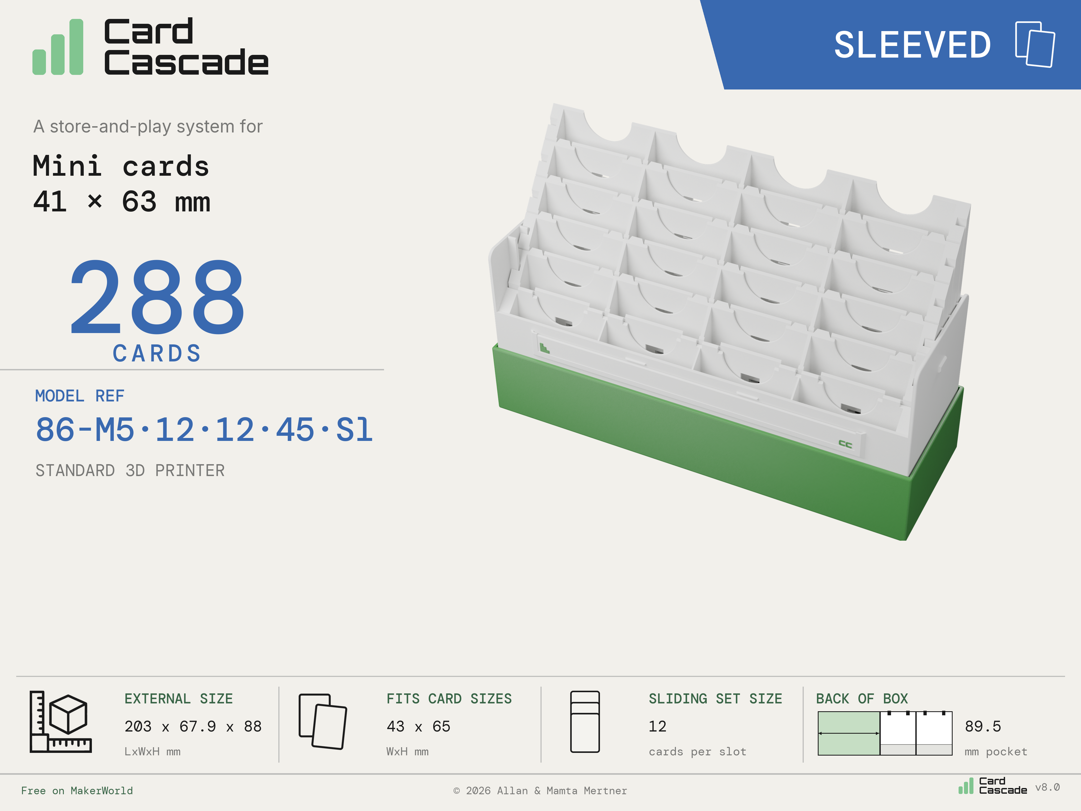
cascades/MiniCards/Mini Cards 288 Card Sleeved (86-M5.12.12.45-Sl).png
