amertner/cardcascade/cascades/MiniCards/Mini Cards 350 Card Sleeved (86-L6.10.10.45-Sl).png

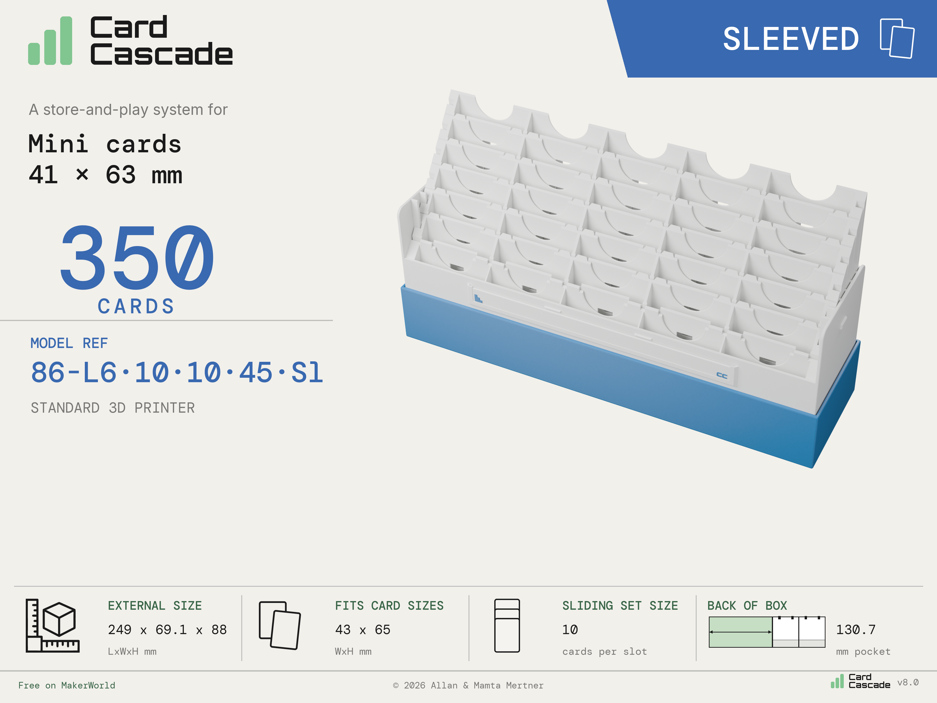
cascades/MiniCards/Mini Cards 350 Card Sleeved (86-L6.10.10.45-Sl).png
