amertner/cardcascade/cascades/Photos/IMG_1410.jpeg

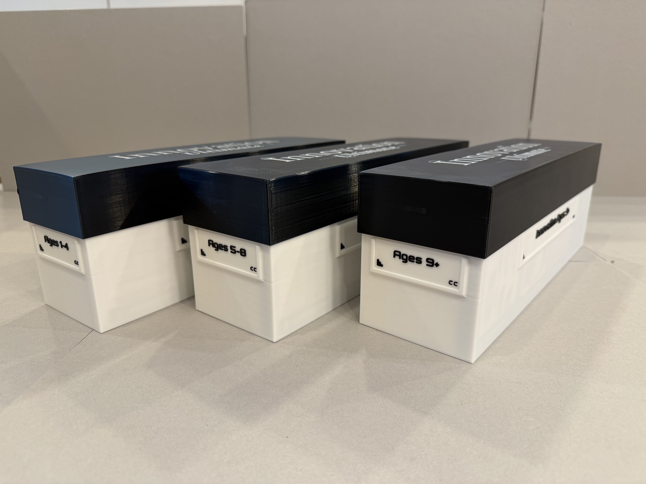
cascades/Photos/IMG_1410.jpeg
