amertner/cardcascade/cascades/Photos/IMG_1411.jpeg

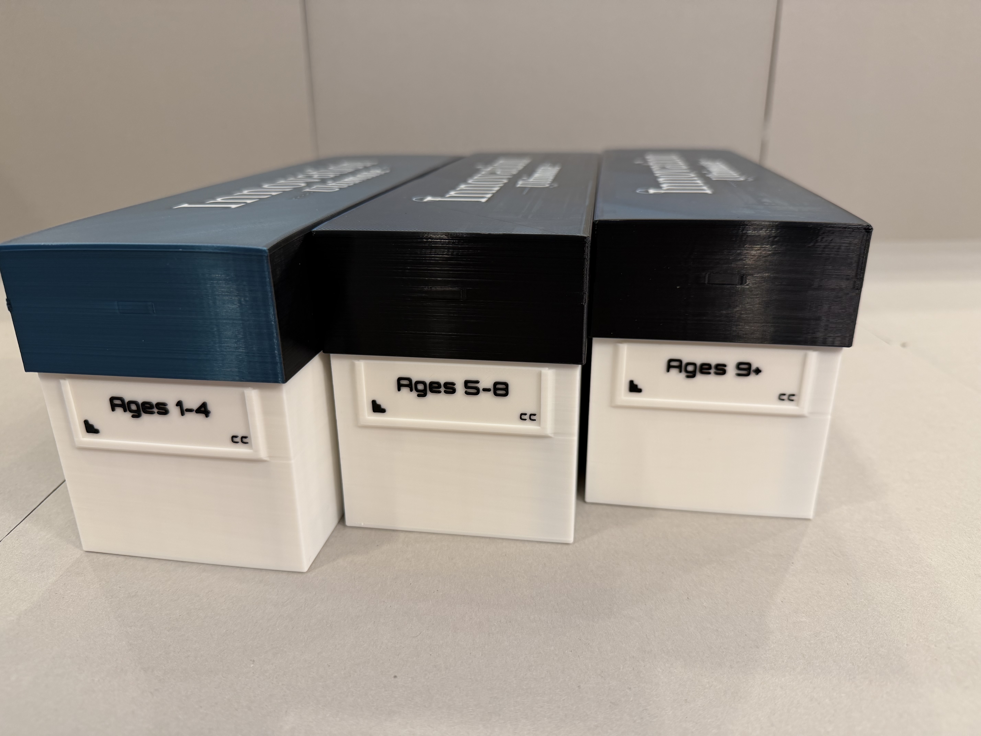
cascades/Photos/IMG_1411.jpeg
