amertner/cardcascade/cascades/Photos/IMG_1412.jpeg

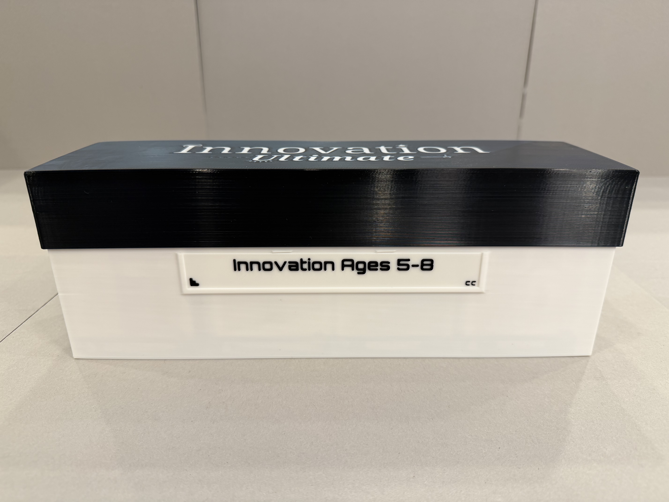
cascades/Photos/IMG_1412.jpeg
