amertner/cardcascade/cascades/Photos/IMG_1413.jpeg

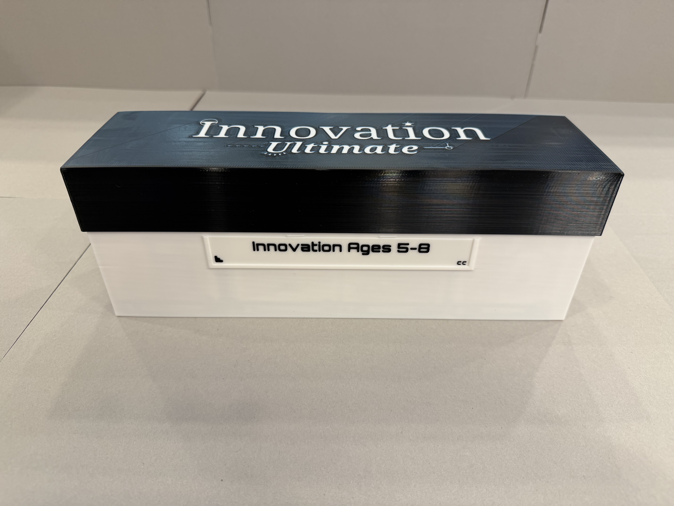
cascades/Photos/IMG_1413.jpeg
