amertner/cardcascade/cascades/Photos/IMG_1414.jpeg

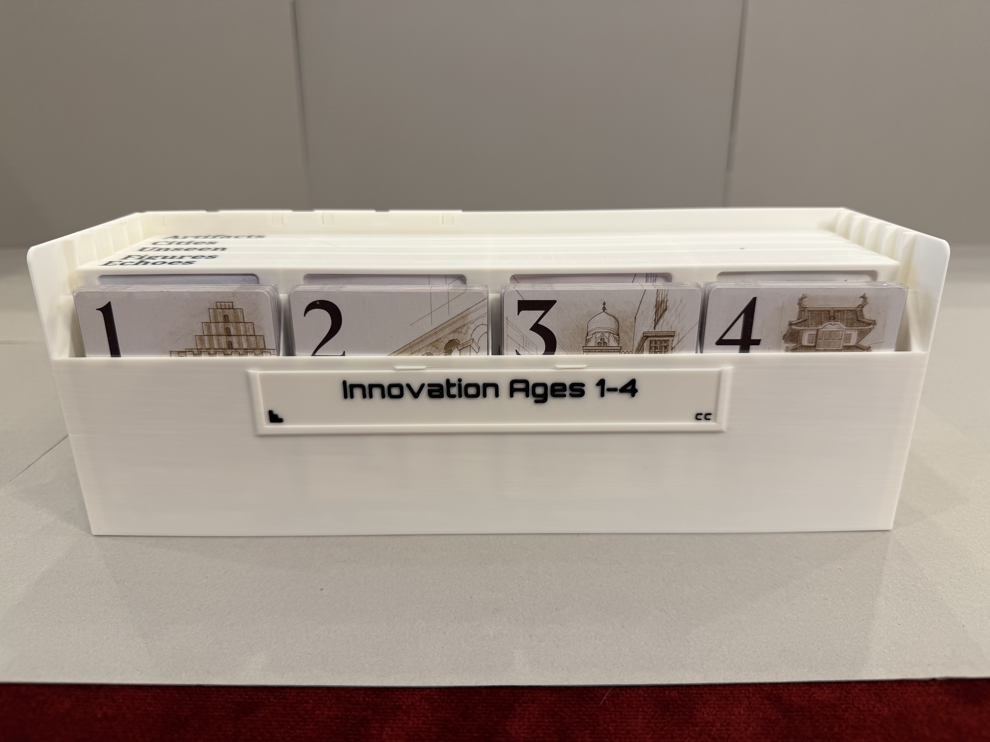
cascades/Photos/IMG_1414.jpeg
