amertner/cardcascade/cascades/Photos/IMG_1415.jpeg

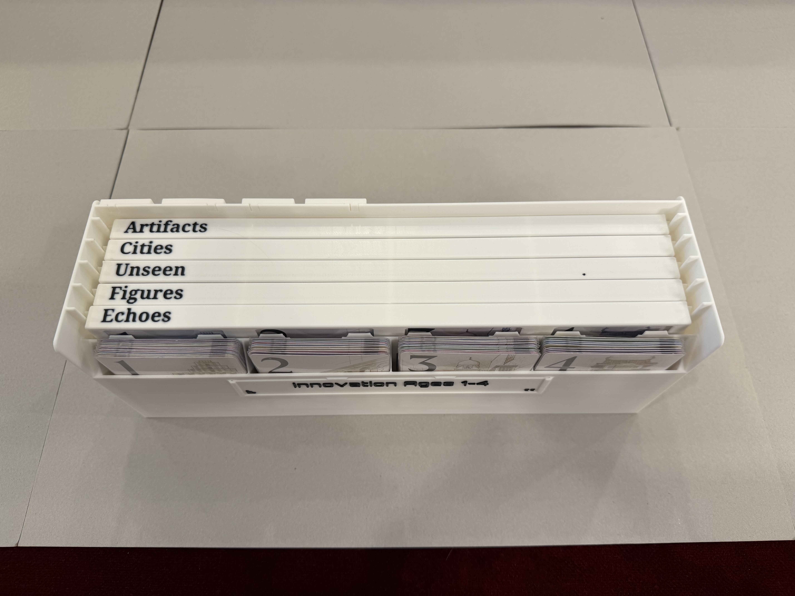
cascades/Photos/IMG_1415.jpeg
