amertner/cardcascade/cascades/Photos/IMG_1416.jpeg

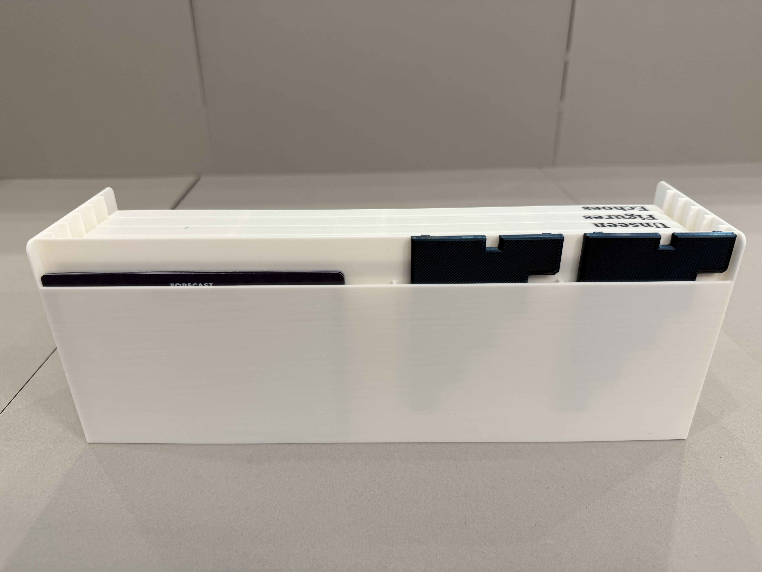
cascades/Photos/IMG_1416.jpeg
