amertner/cardcascade/cascades/Photos/IMG_1417.jpeg

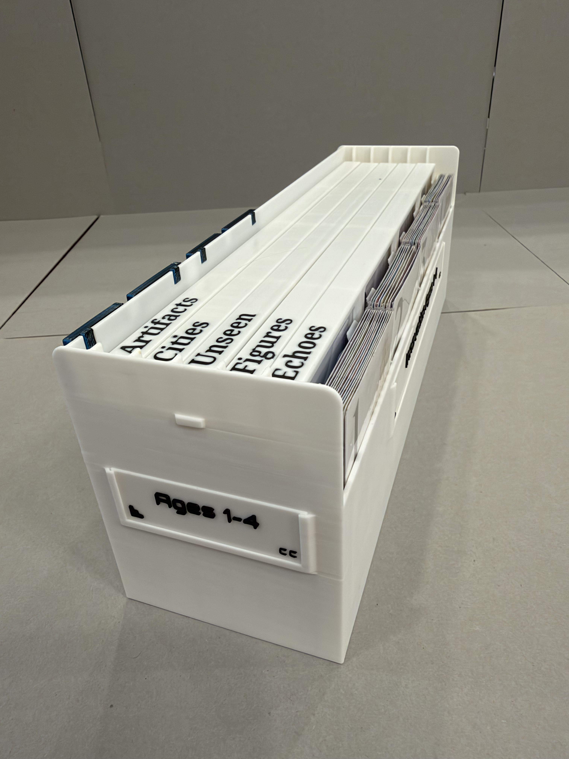
cascades/Photos/IMG_1417.jpeg
