amertner/cardcascade/cascades/Photos/IMG_1418.jpeg

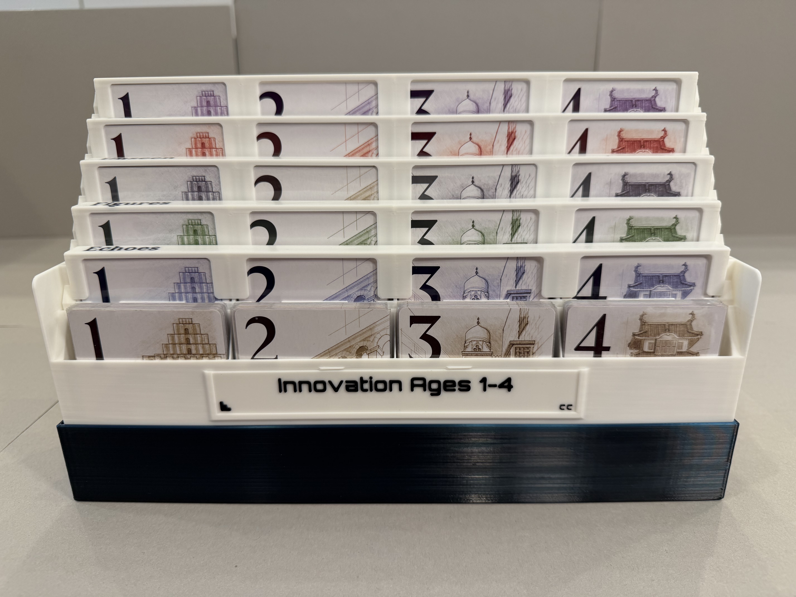
cascades/Photos/IMG_1418.jpeg
