amertner/cardcascade/cascades/Photos/IMG_1419.jpeg

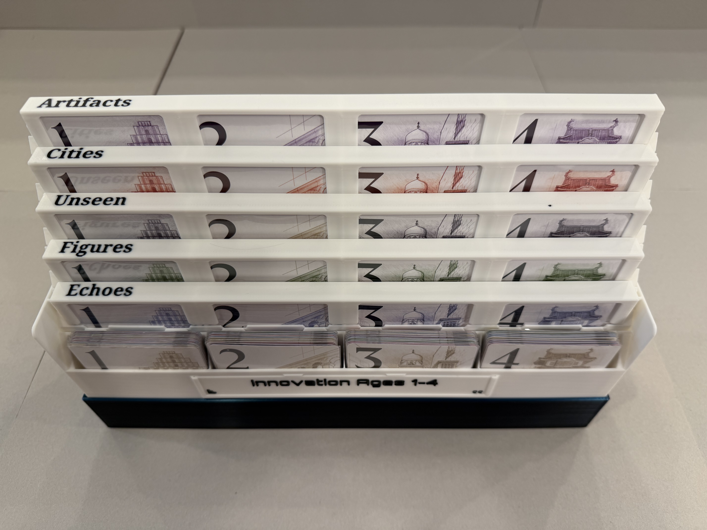
cascades/Photos/IMG_1419.jpeg
