amertner/cardcascade/cascades/Photos/IMG_1420.jpeg

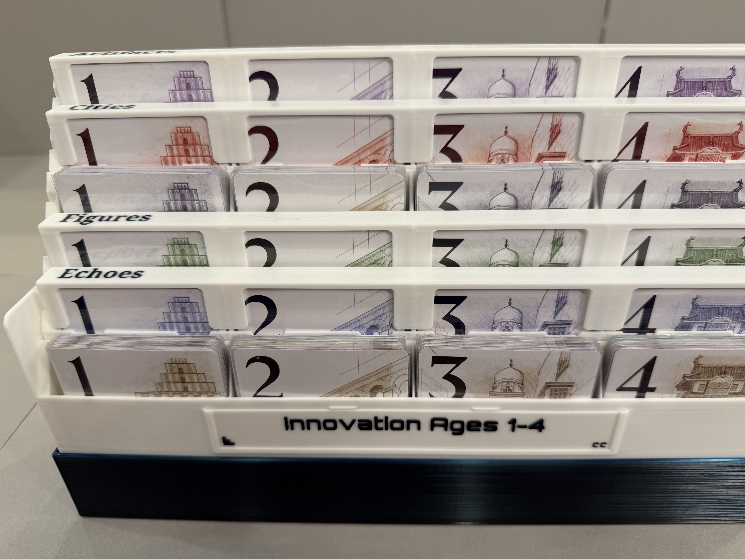
cascades/Photos/IMG_1420.jpeg
