amertner/cardcascade/cascades/Photos/IMG_1421.jpeg

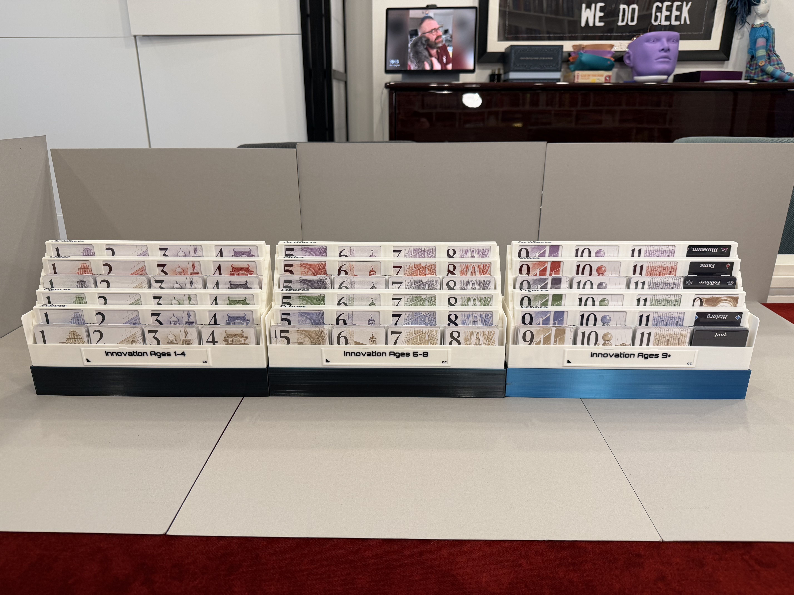
cascades/Photos/IMG_1421.jpeg
