amertner/cardcascade/cascades/Photos/IMG_1423.jpeg

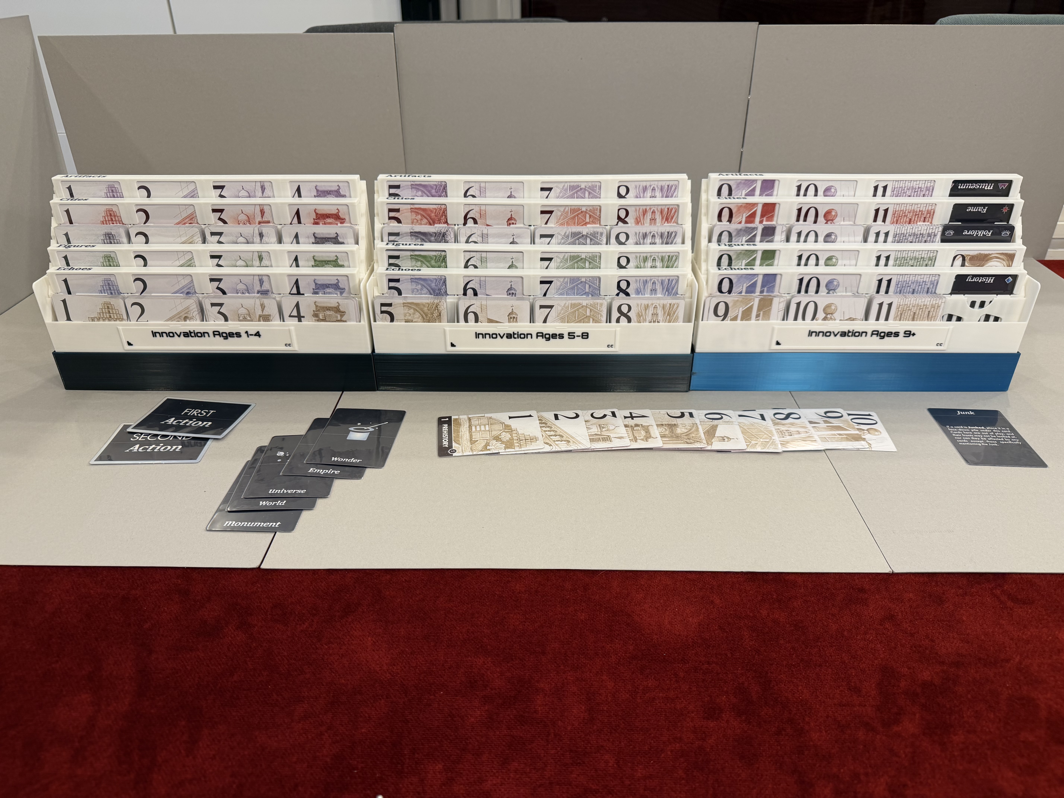
cascades/Photos/IMG_1423.jpeg
