amertner/cardcascade/cascades/Photos/IMG_1424.jpeg

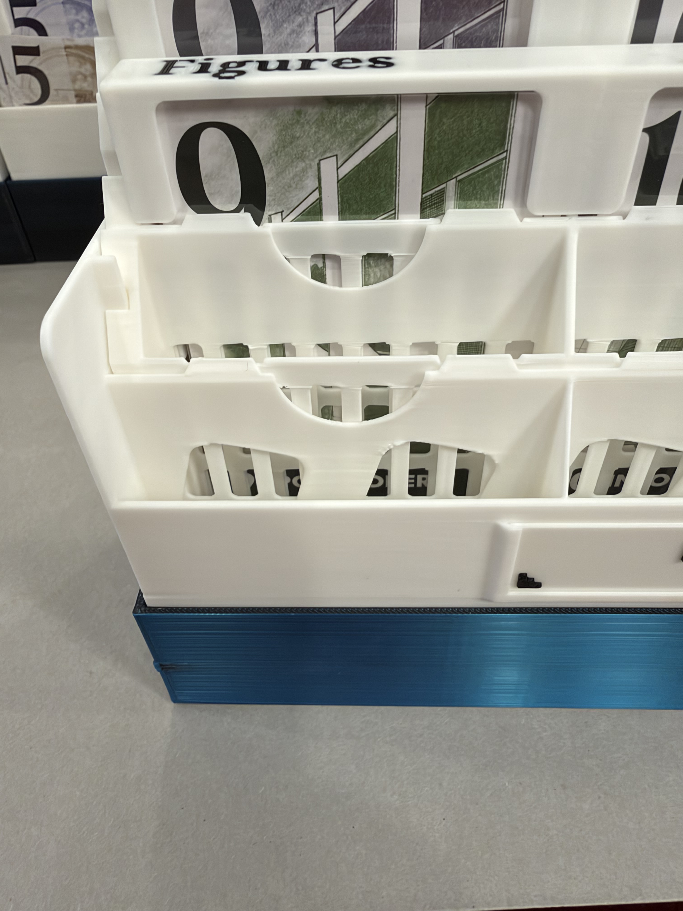
cascades/Photos/IMG_1424.jpeg
