amertner/cardcascade/cascades/Photos/IMG_1425.jpeg

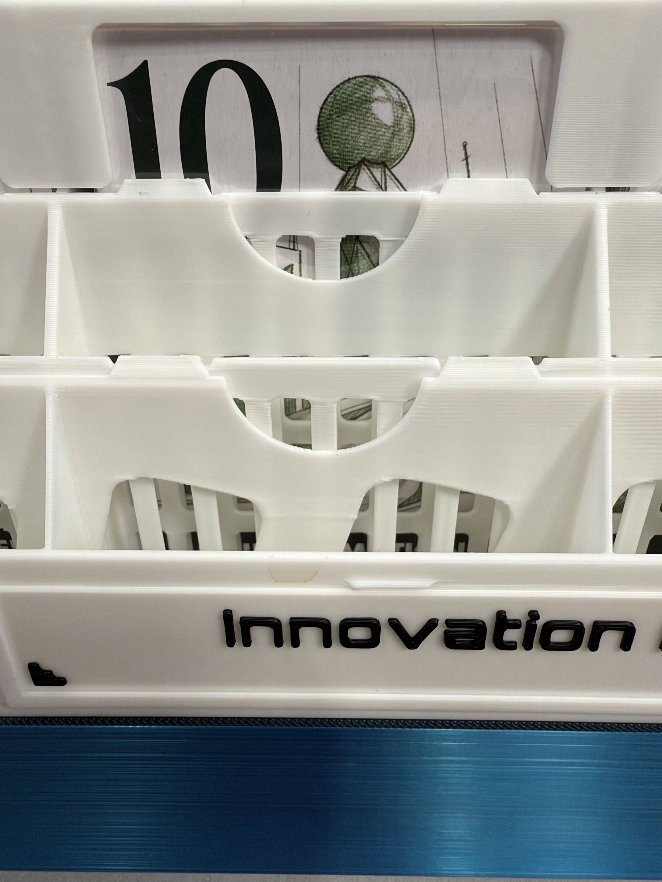
cascades/Photos/IMG_1425.jpeg
