amertner/cardcascade/cascades/Photos/IMG_1426.jpeg

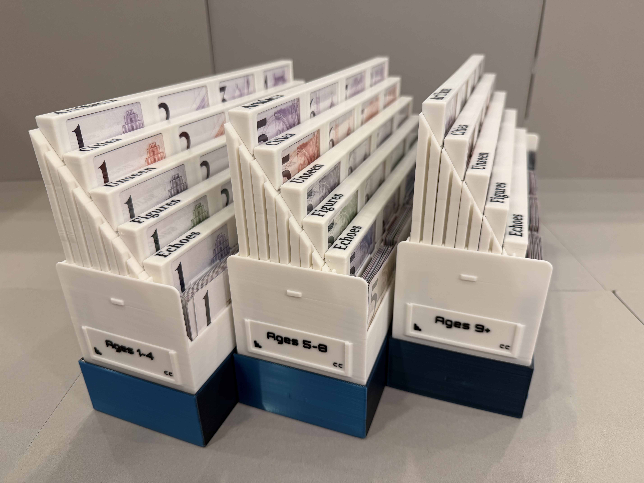
cascades/Photos/IMG_1426.jpeg
