amertner/cardcascade/cascades/Photos/IMG_1427.jpeg

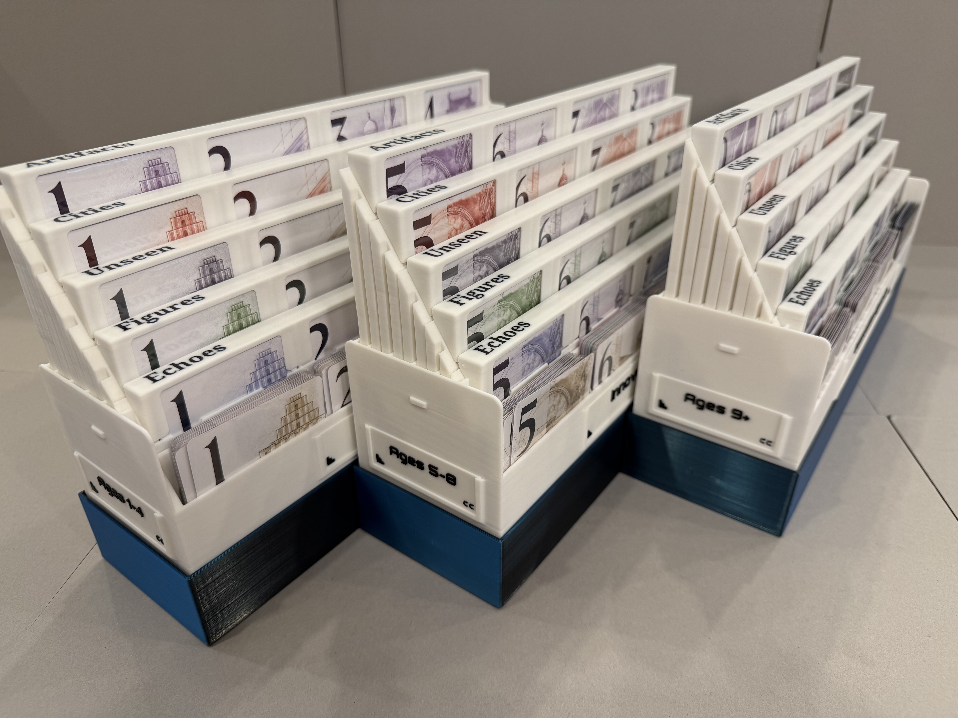
cascades/Photos/IMG_1427.jpeg
