amertner/cardcascade/cascades/Photos/IMG_1428.jpeg

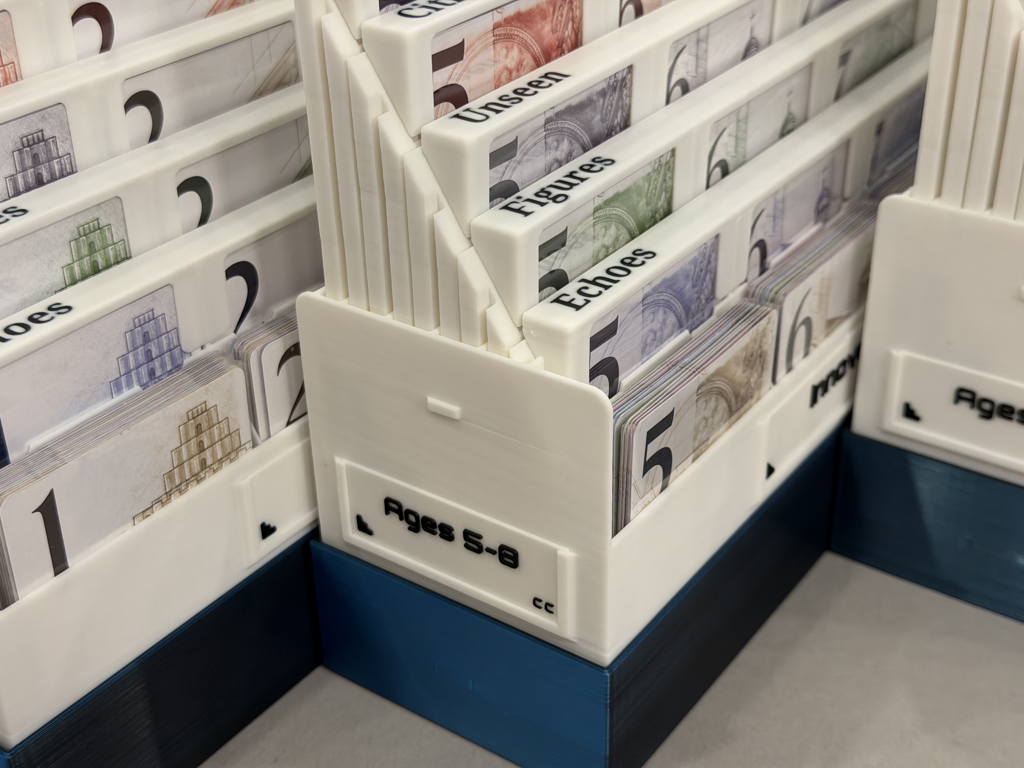
cascades/Photos/IMG_1428.jpeg
