amertner/cardcascade/photos/Compile/126 Card.png

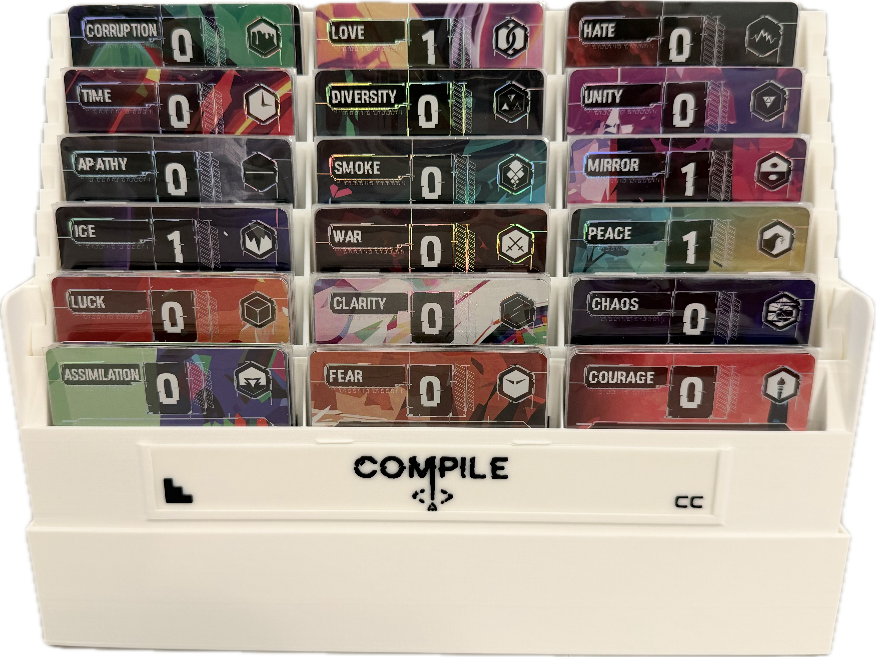
photos/Compile/126 Card.png
