amertner/cardcascade/photos/Dominion/168 Card.png

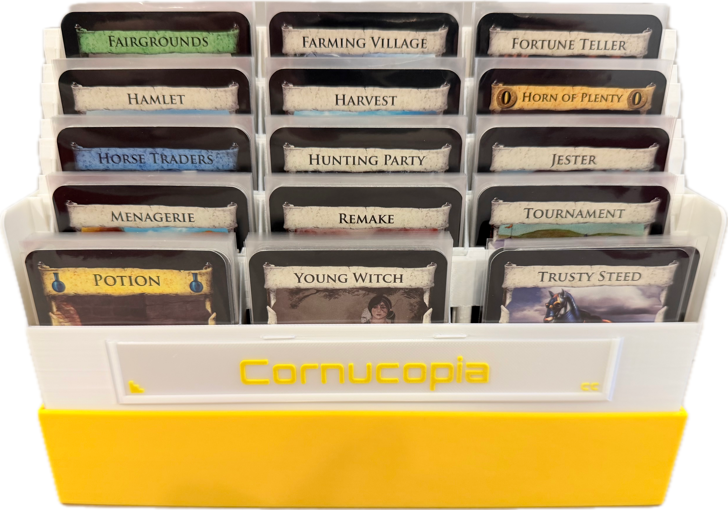
photos/Dominion/168 Card.png
