amertner/cardcascade/photos/Dominion/324 Card Sleeved.png

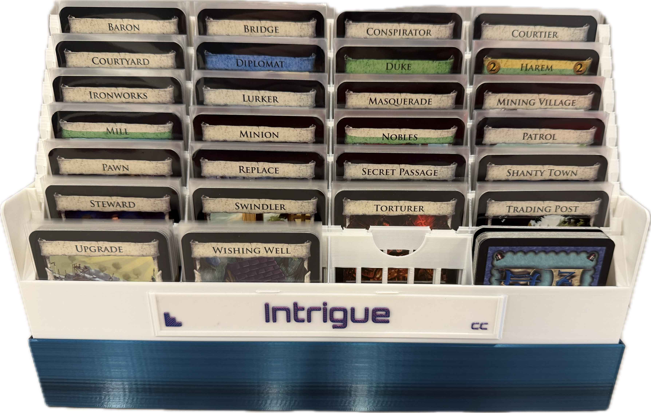
photos/Dominion/324 Card Sleeved.png
