amertner/cardcascade/photos/Dominion/324 Card.png

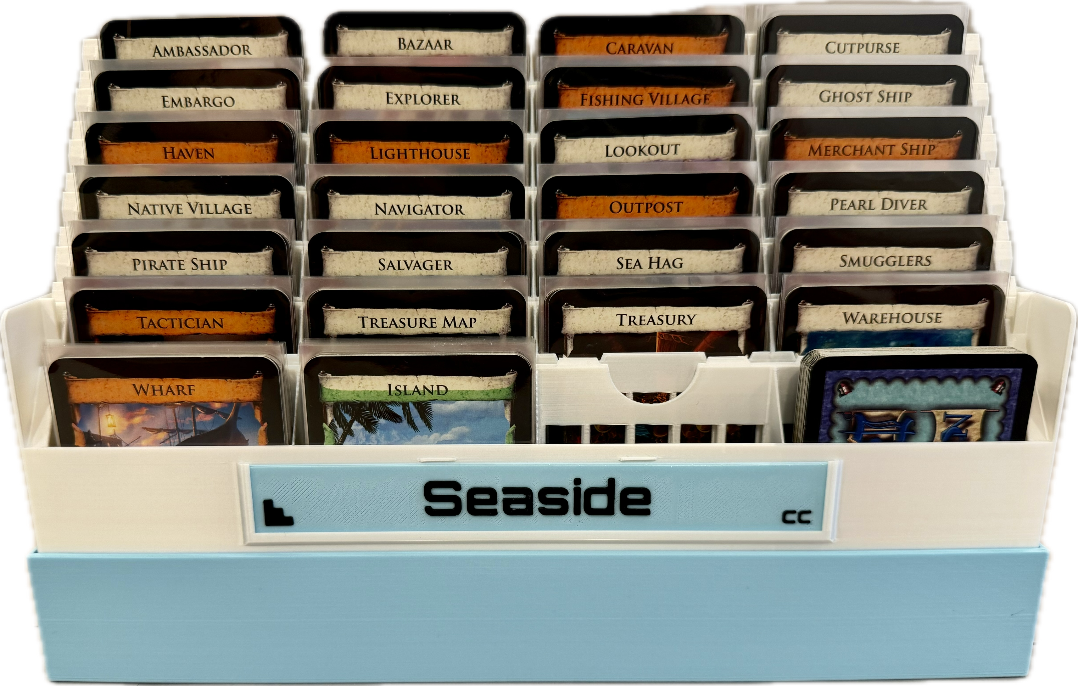
photos/Dominion/324 Card.png
