amertner/cardcascade/photos/Dominion/400 Card (Mat).png

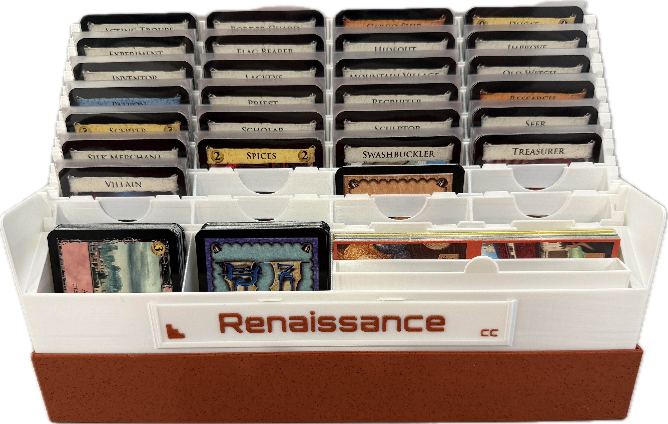
photos/Dominion/400 Card (Mat).png
