amertner/cardcascade/photos/Dominion/650 Card.png

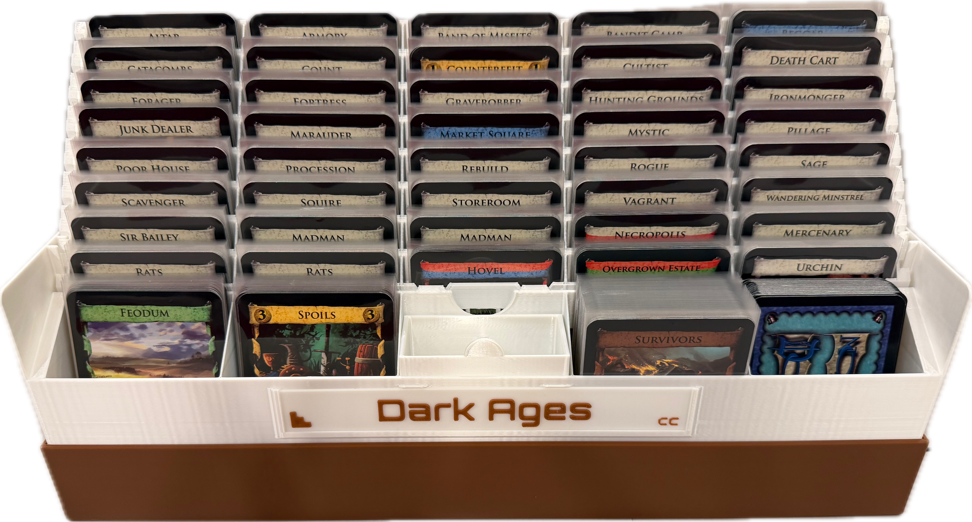
photos/Dominion/650 Card.png
