amertner/cardcascade/photos/FCM/Milestones 1.png

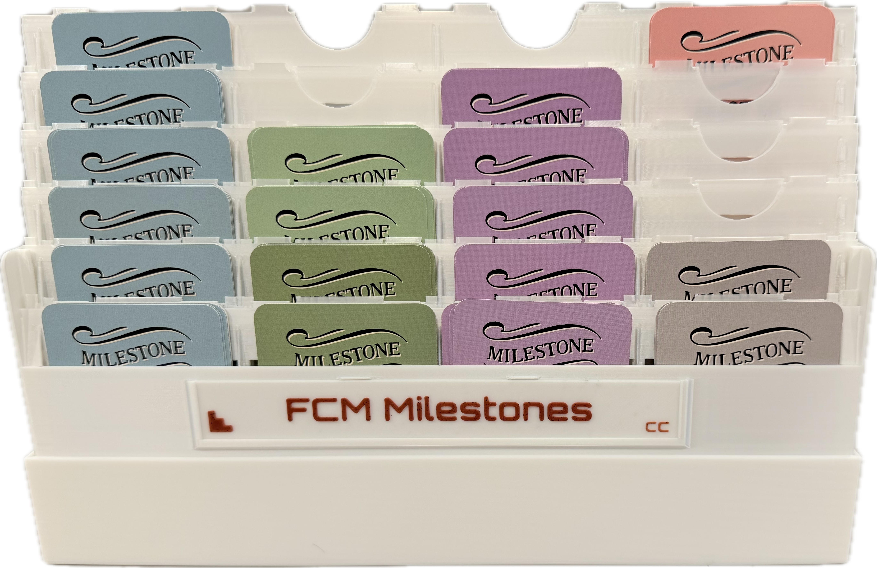
photos/FCM/Milestones 1.png
