amertner/cardcascade/photos/FCM/Occ 1.png

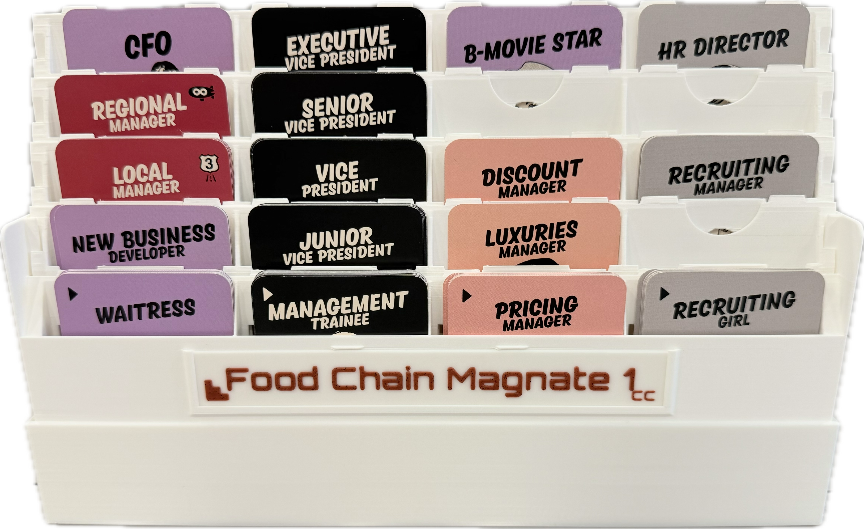
photos/FCM/Occ 1.png
