amertner/cardcascade/photos/FCM/Occ 2.png

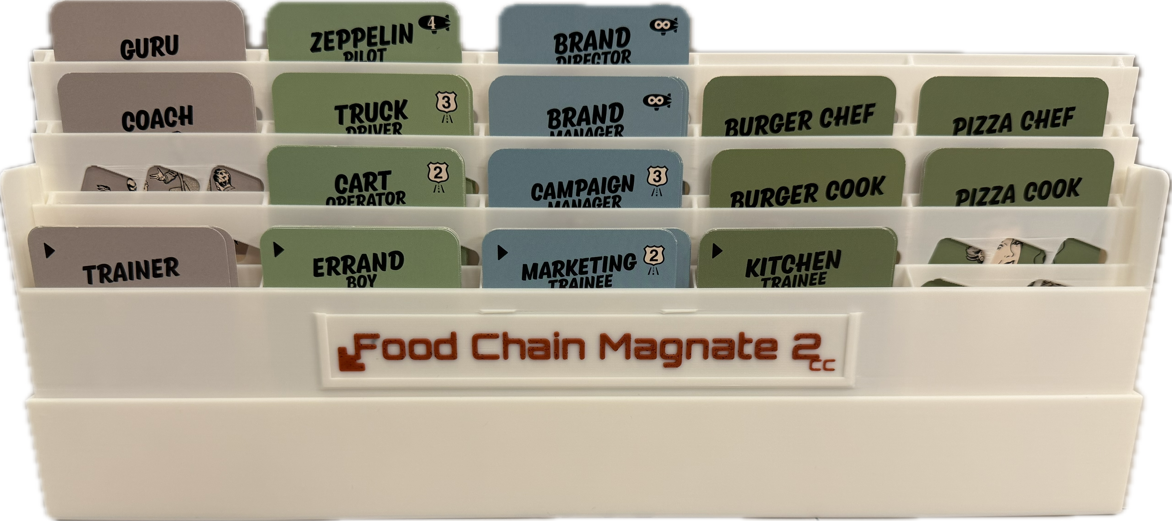
photos/FCM/Occ 2.png
