amertner/cardcascade/photos/Innovation/4 Ages 5 Expansions.png

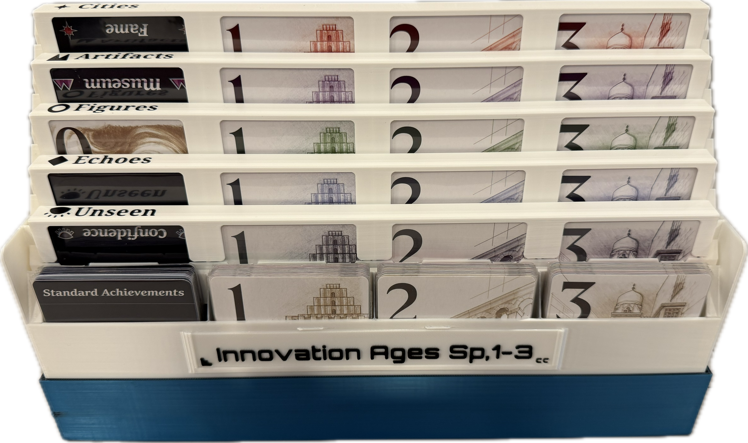
photos/Innovation/4 Ages 5 Expansions.png
