amertner/cardcascade/photos/Innovation/4 Later Ages 5 Expansions.png

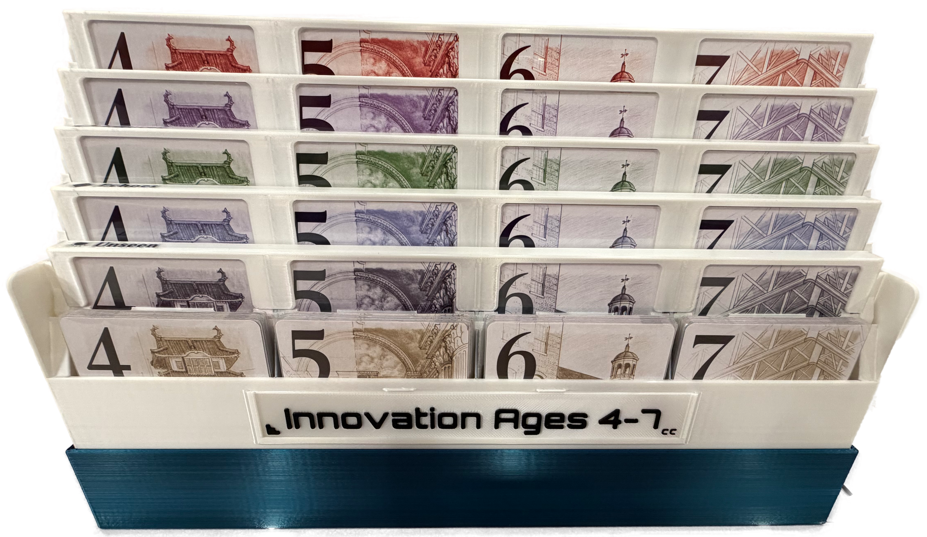
photos/Innovation/4 Later Ages 5 Expansions.png
