amertner/cardcascade/photos/Innovation/Single Mini Unsleeved.png

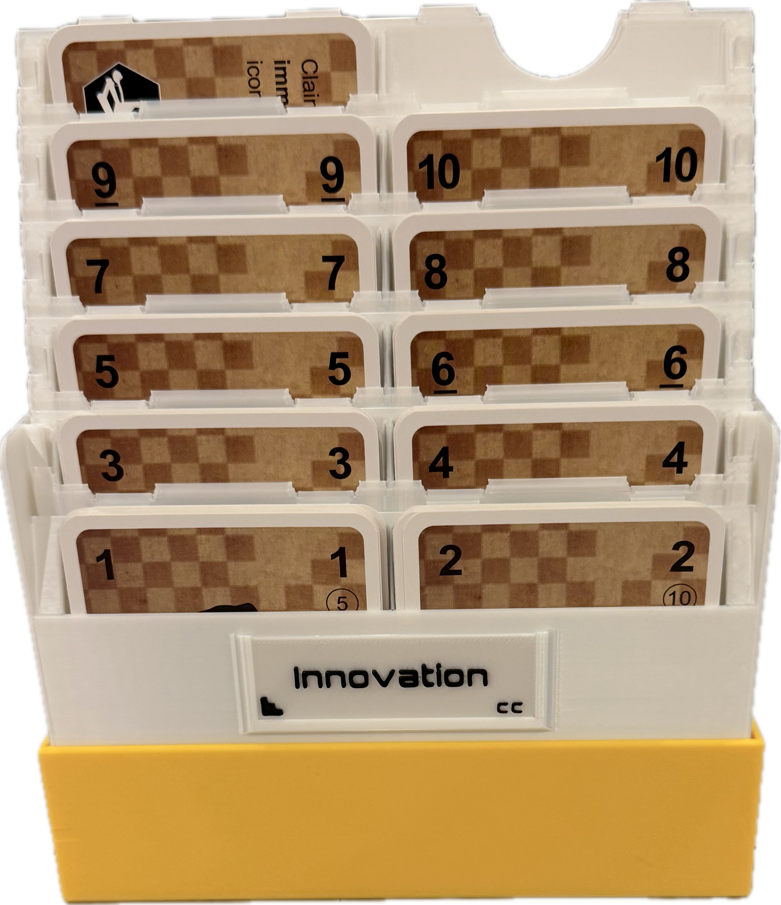
photos/Innovation/Single Mini Unsleeved.png
