amertner/cardcascade/photos/Innovation/Single Set.png

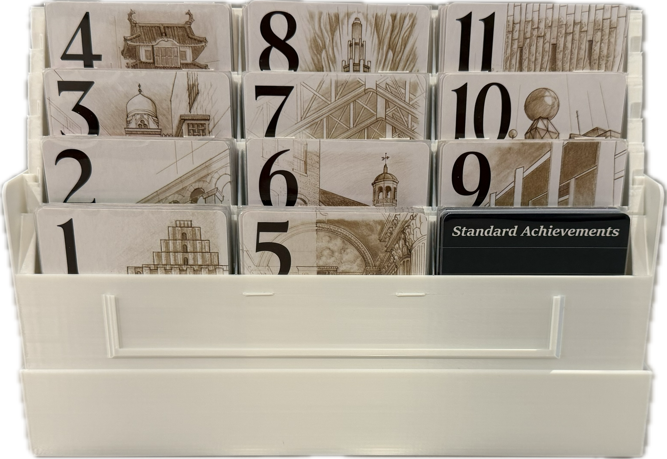
photos/Innovation/Single Set.png
