amertner/cardcascade/photos/Innovation/Three Expansions.png

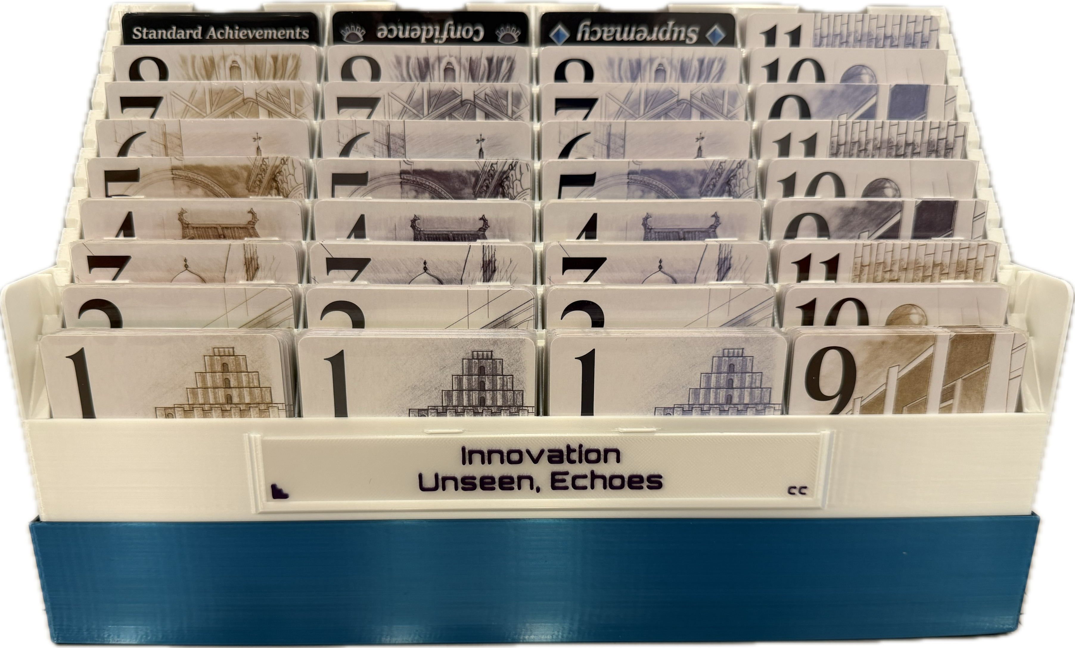
photos/Innovation/Three Expansions.png
