amertner/cardcascade/individual/Dominion/_raw/Assembly M6.21.10.62-Sl.3mf

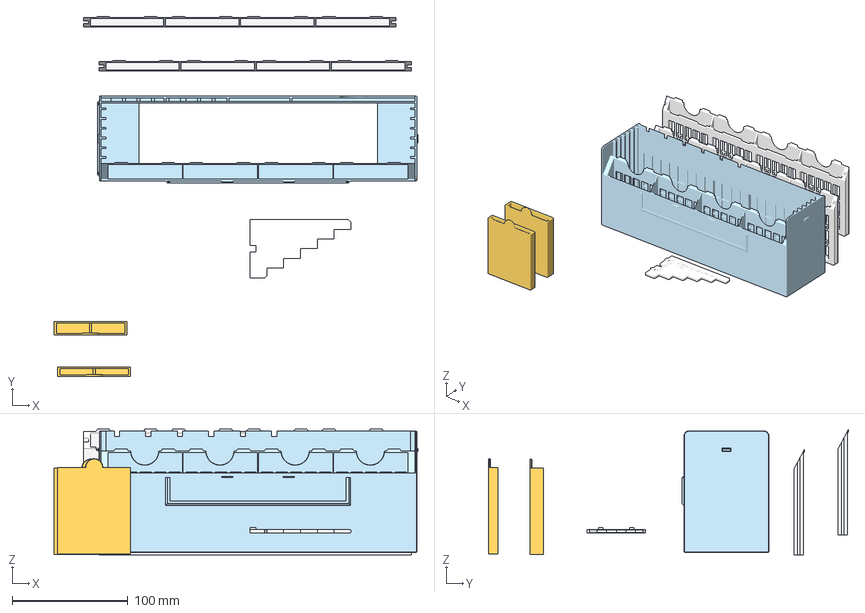
[picture p151: CAD file, 2026-09-05]
individual/Dominion/_raw/Assembly M6.21.10.62-Sl.3mf
314.4 x 311.1 x 108.5 mm
