amertner/cardcascade/individual/Innovation/_raw/Assembly M5.15.15.62-Sl.3mf

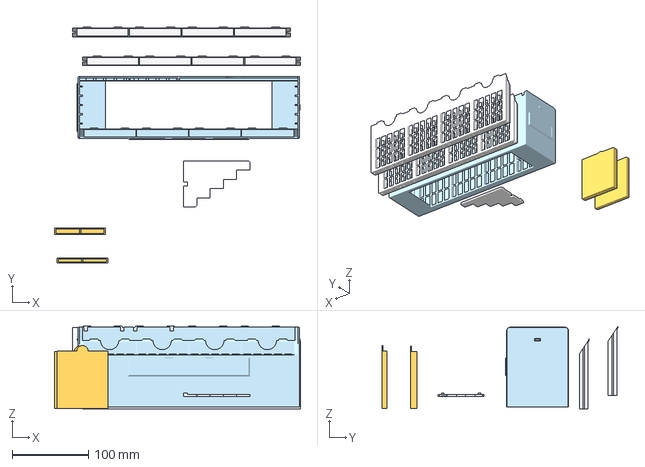
[picture p152: CAD file, 2026-09-03]
individual/Innovation/_raw/Assembly M5.15.15.62-Sl.3mf
322.8 x 309.8 x 108.4 mm
