amertner/cardcascade/individual/Dominion/_raw/Assembly M6.21.10.45-Un.3mf

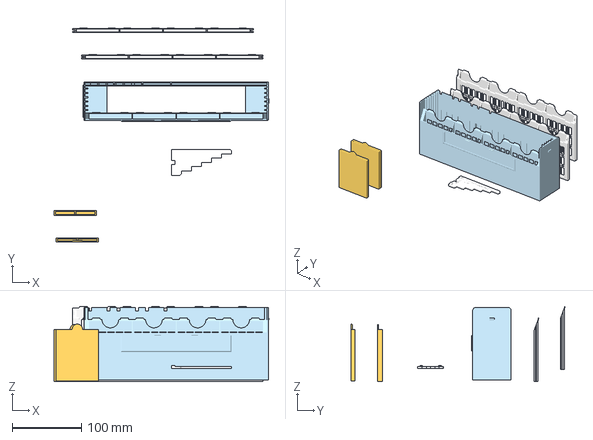
[picture p153: CAD file, 2026-09-05]
individual/Dominion/_raw/Assembly M6.21.10.45-Un.3mf
310.4 x 308.5 x 108.6 mm
