amertner/cardcascade/individual/FCM/_raw/Assembly L3.18.6.20-Sl.3mf

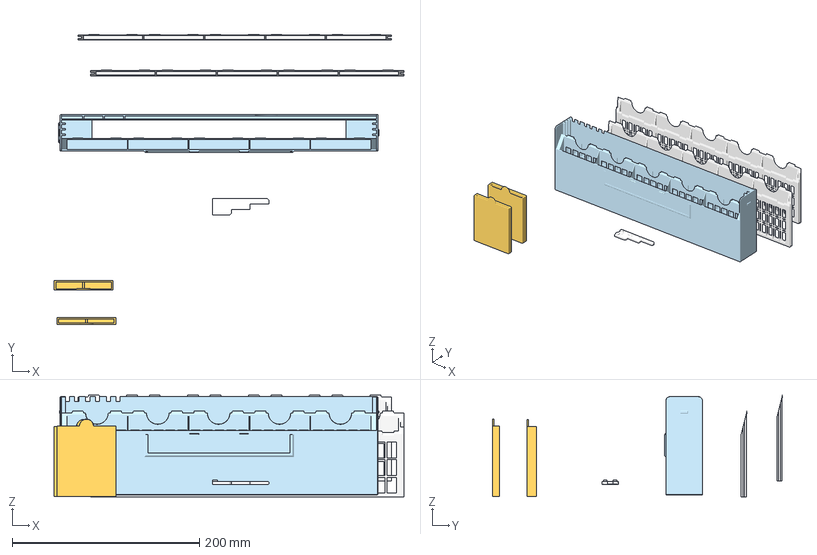
[picture p154: CAD file, 2026-08-31]
individual/FCM/_raw/Assembly L3.18.6.20-Sl.3mf
373.8 x 309.7 x 108.7 mm
