amertner/cardcascade/individual/Dominion/_raw/Assembly L6.40.12.62-Sl.3mf

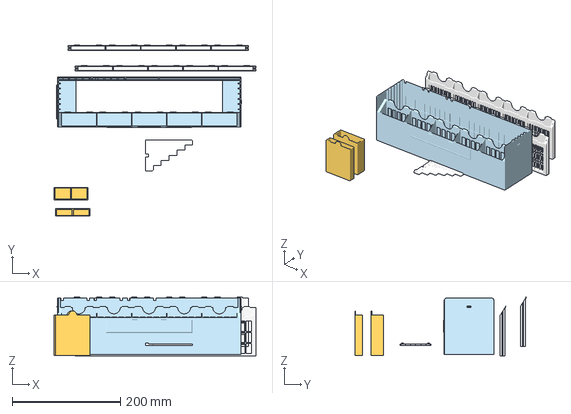
[picture p155: CAD file, 2026-09-03]
individual/Dominion/_raw/Assembly L6.40.12.62-Sl.3mf
373.8 x 316.9 x 108.4 mm
