amertner/cardcascade/individual/FCM/_raw/Assembly M5.6.6.20-Un.3mf

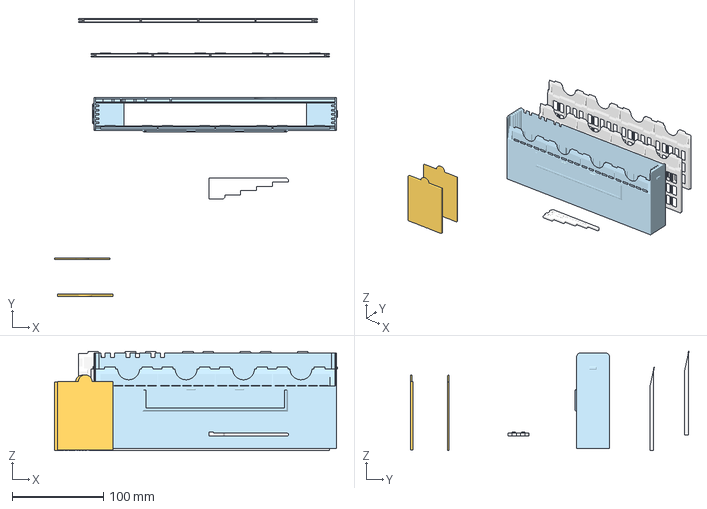
[picture p156: CAD file, 2026-08-31]
individual/FCM/_raw/Assembly M5.6.6.20-Un.3mf
310.4 x 305.4 x 108.7 mm
