amertner/cardcascade/individual/Innovation/_raw/Assembly S5.15.15.62-Sl.3mf

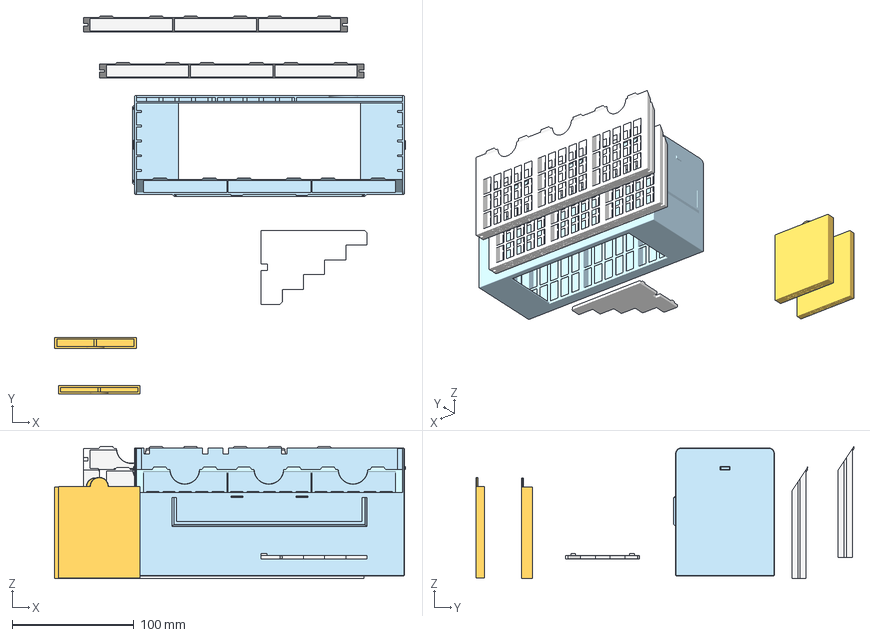
[picture p157: CAD file, 2026-09-03]
individual/Innovation/_raw/Assembly S5.15.15.62-Sl.3mf
287.9 x 309.8 x 108.4 mm
