amertner/cardcascade/individual/Compile/_raw/Assembly S5.7.7.45-Sl.3mf

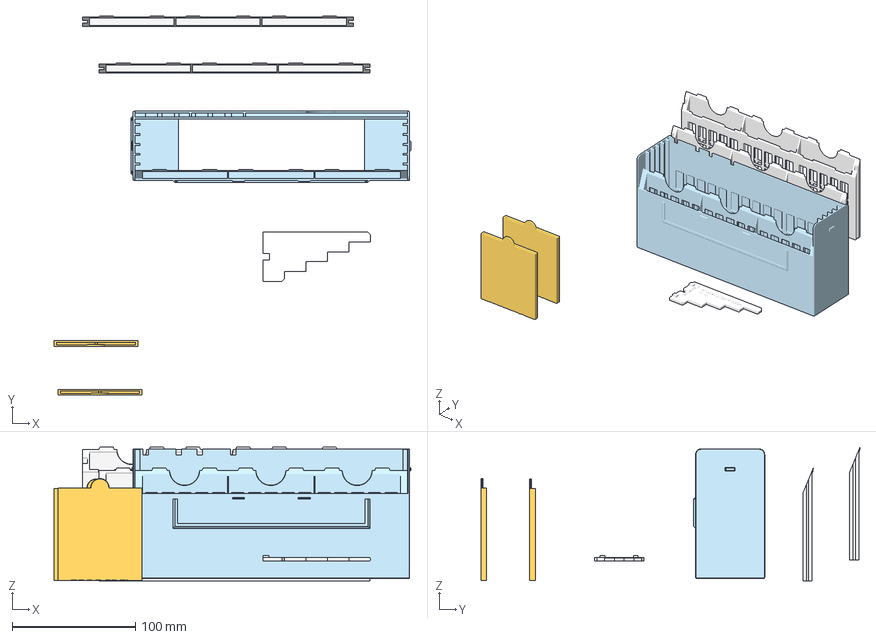
[picture p158: CAD file, 2026-08-31]
individual/Compile/_raw/Assembly S5.7.7.45-Sl.3mf
289.4 x 307.4 x 108.6 mm
