amertner/cardcascade/individual/Dominion/_raw/Assembly M2.60.18-40.62-Sl.3mf

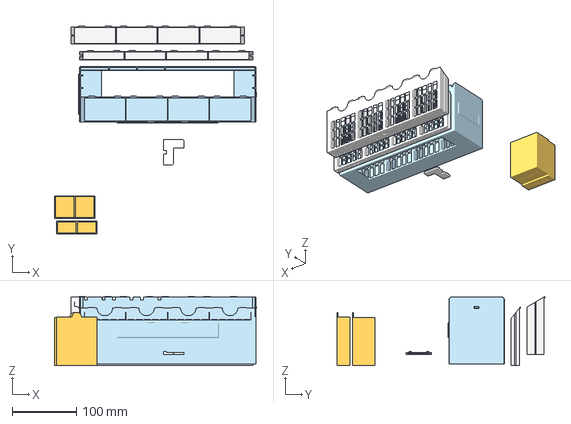
[picture p159: CAD file, 2026-09-03]
individual/Dominion/_raw/Assembly M2.60.18-40.62-Sl.3mf
314.4 x 323.6 x 107.7 mm
