amertner/cardcascade/individual/FCM/_raw/Assembly L3.18.6.20-Un.3mf

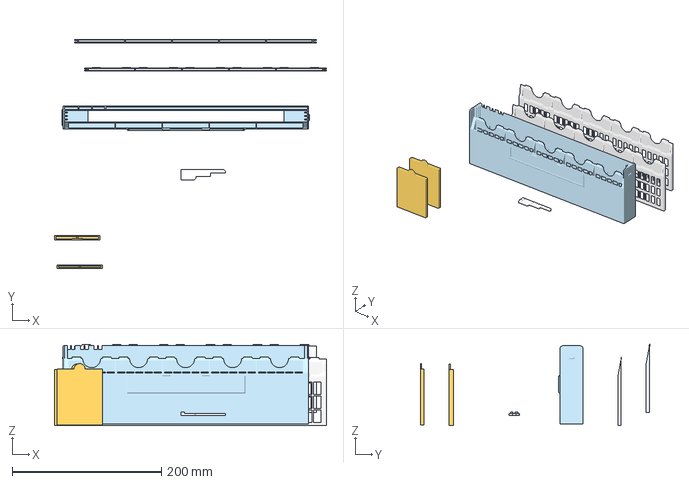
[picture p160: CAD file, 2026-08-31]
individual/FCM/_raw/Assembly L3.18.6.20-Un.3mf
364.8 x 307.6 x 108.7 mm
