amertner/cardcascade/individual/Compile/_raw/Assembly S5.7.7.20-Un.3mf

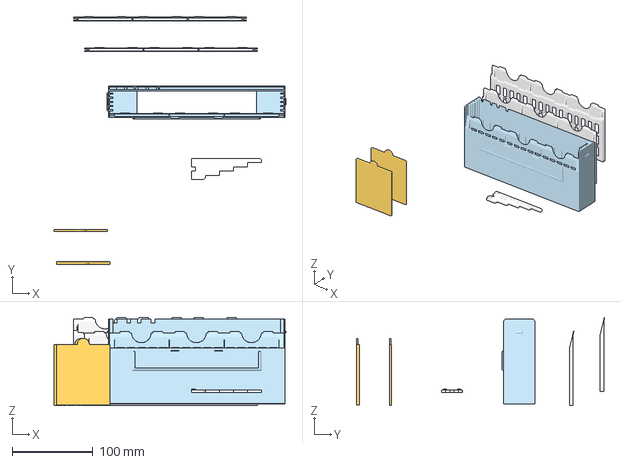
[picture p161: CAD file, 2026-08-31]
individual/Compile/_raw/Assembly S5.7.7.20-Un.3mf
286.4 x 305.7 x 108.7 mm
