amertner/cardcascade/individual/Dominion/_raw/Assembly M8.40.10.62-Sl merged.3mf

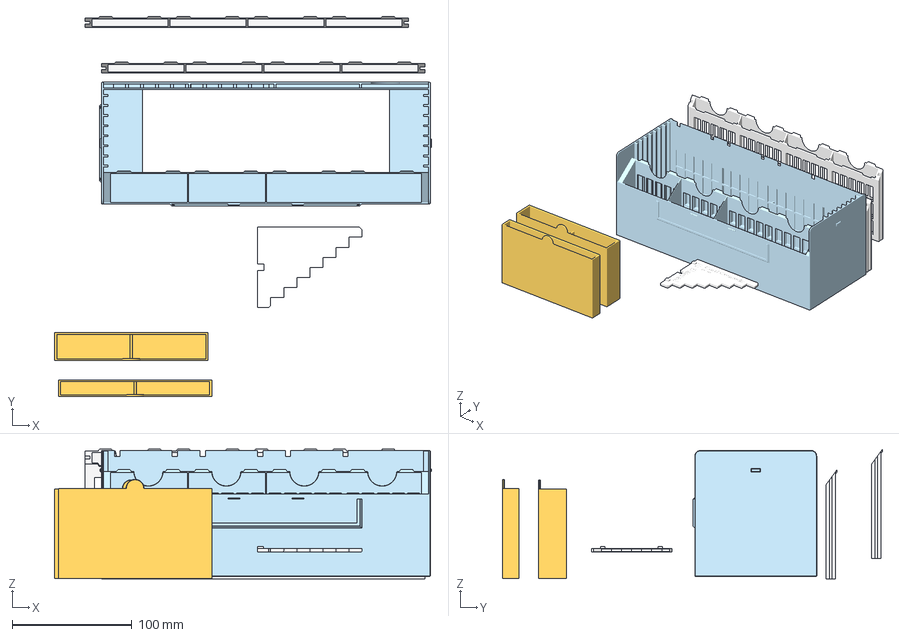
[picture p162: CAD file, 2026-09-03]
individual/Dominion/_raw/Assembly M8.40.10.62-Sl merged.3mf
314.4 x 317.0 x 108.3 mm
