amertner/cardcascade/individual/Dominion/_raw/Assembly M2.60.18-40.45-Un.3mf

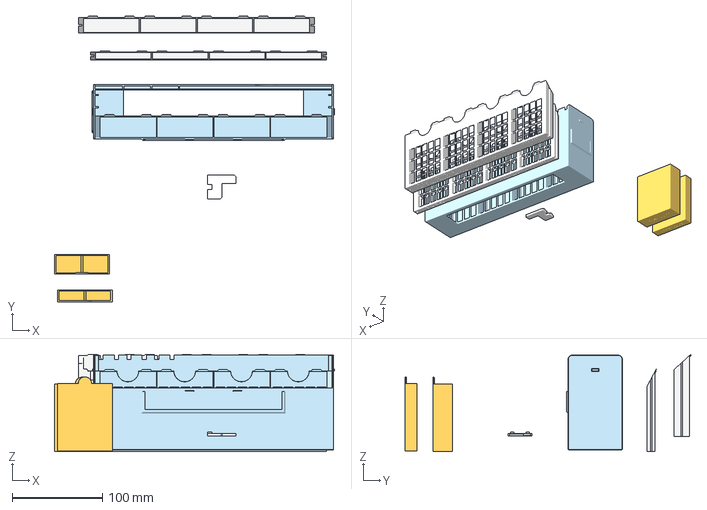
[picture p163: CAD file, 2026-09-03]
individual/Dominion/_raw/Assembly M2.60.18-40.45-Un.3mf
310.4 x 316.7 x 108.1 mm
