amertner/cardcascade/individual/Dominion/_raw/Assembly M8.40.10.62-Un merged.3mf

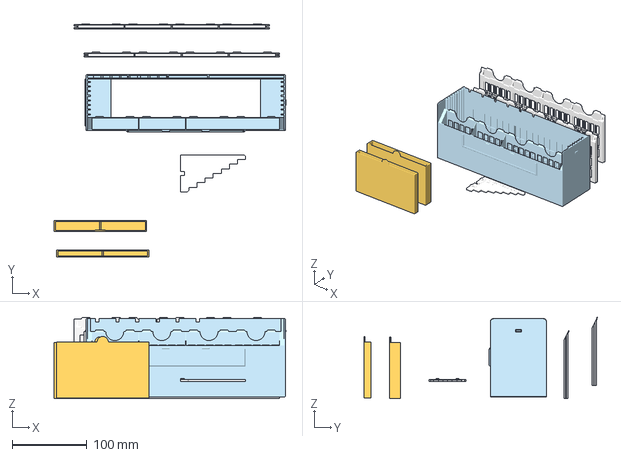
[picture p164: CAD file, 2026-09-03]
individual/Dominion/_raw/Assembly M8.40.10.62-Un merged.3mf
310.4 x 312.3 x 108.5 mm
