amertner/cardcascade/individual/Dominion/_raw/Assembly S9.21.10.62-Un.3mf

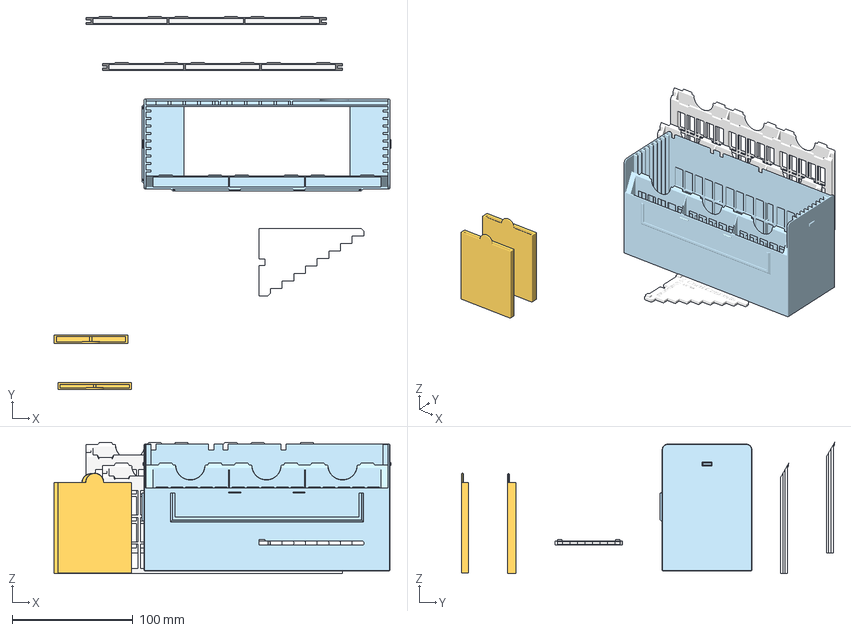
[picture p165: CAD file, 2026-09-03]
individual/Dominion/_raw/Assembly S9.21.10.62-Un.3mf
278.9 x 308.8 x 108.5 mm
