amertner/cardcascade/individual/Innovation/_raw/Assembly XS5.15.10.45-Sl.3mf

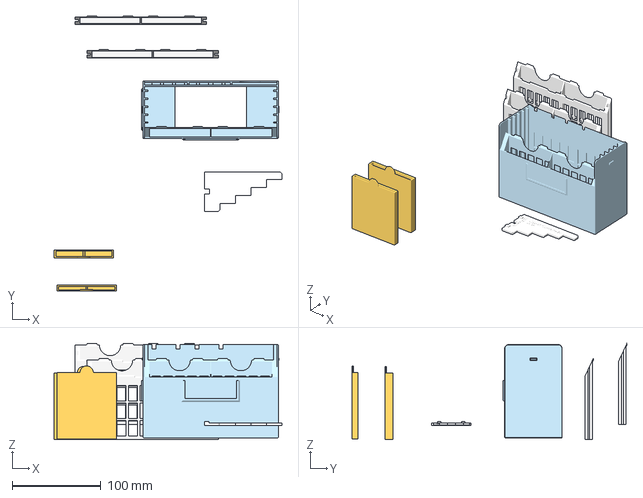
[picture p166: CAD file, 2026-08-31]
individual/Innovation/_raw/Assembly XS5.15.10.45-Sl.3mf
256.5 x 309.6 x 108.5 mm
