amertner/cardcascade/individual/Dominion/_raw/Assembly L8.50.10.62-Sl.3mf

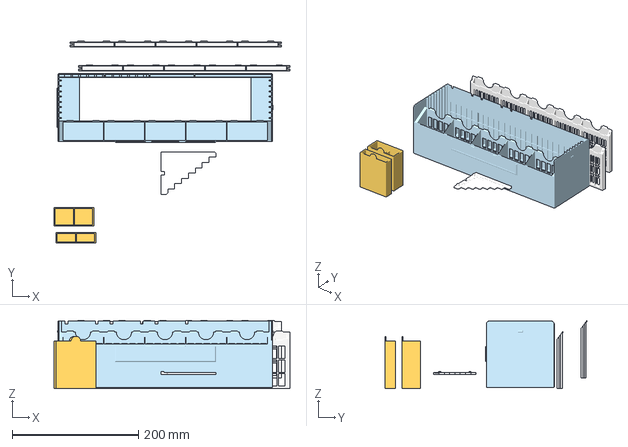
[picture p167: CAD file, 2026-09-03]
individual/Dominion/_raw/Assembly L8.50.10.62-Sl.3mf
373.8 x 320.0 x 108.3 mm
