amertner/cardcascade/individual/Dominion/_raw/Assembly S5.40.12.62-Sl.3mf

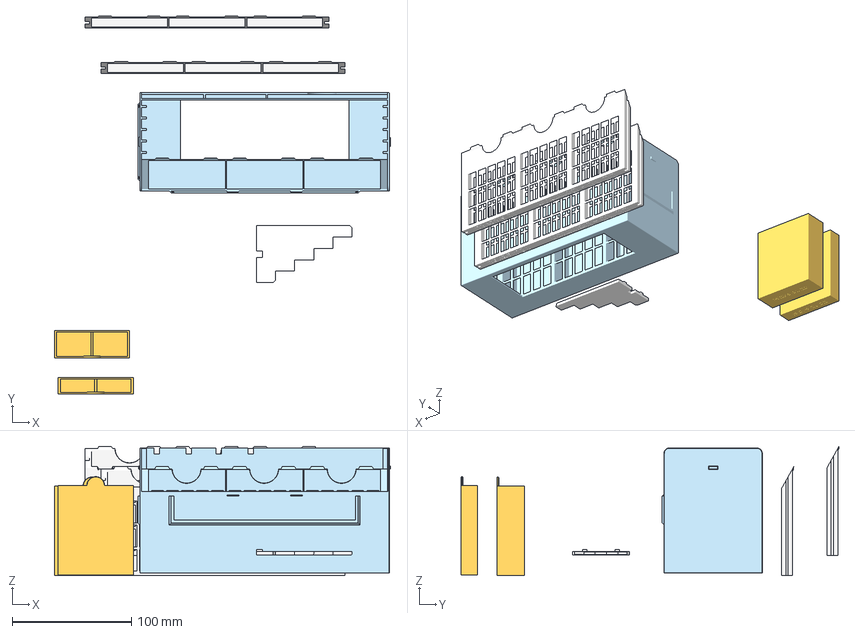
[picture p168: CAD file, 2026-09-03]
individual/Dominion/_raw/Assembly S5.40.12.62-Sl.3mf
281.9 x 316.8 x 108.5 mm
