amertner/cardcascade/individual/Innovation/_raw/Assembly M5.10.10.45-Sl.3mf

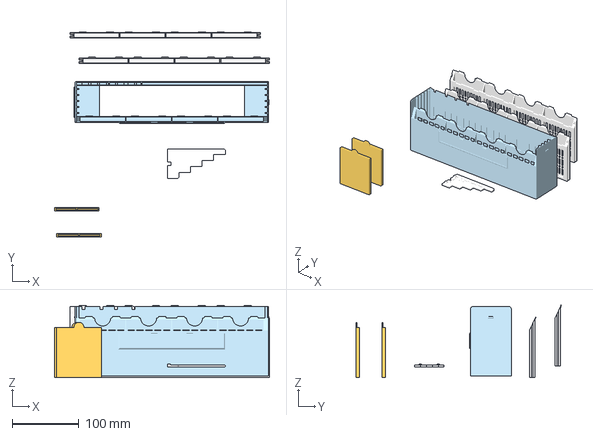
[picture p169: CAD file, 2026-08-31]
individual/Innovation/_raw/Assembly M5.10.10.45-Sl.3mf
322.8 x 307.9 x 108.5 mm
