amertner/cardcascade/individual/Dominion/_raw/Assembly L6.40.12.45-Un.3mf

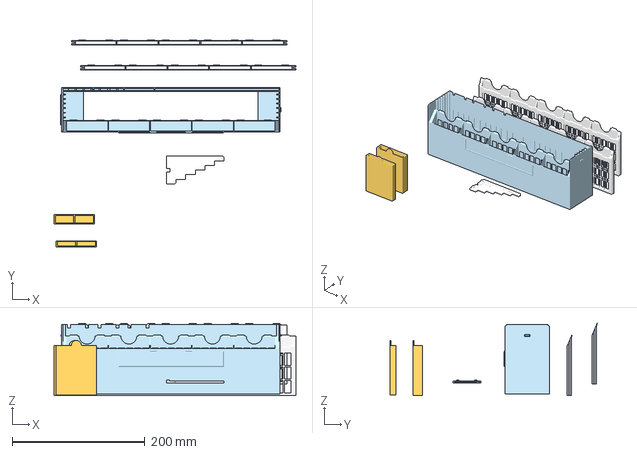
[picture p170: CAD file, 2026-09-03]
individual/Dominion/_raw/Assembly L6.40.12.45-Un.3mf
364.8 x 312.2 x 108.6 mm
