amertner/cardcascade/individual/Dominion/_raw/Assembly L8.50.10.62-Un.3mf

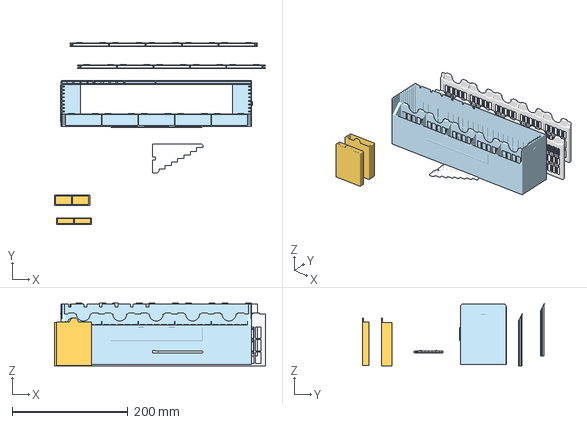
[picture p171: CAD file, 2026-09-03]
individual/Dominion/_raw/Assembly L8.50.10.62-Un.3mf
364.8 x 314.2 x 108.5 mm
