amertner/cardcascade/individual/Dominion/_raw/Assembly S9.21.10.62-Sl.3mf

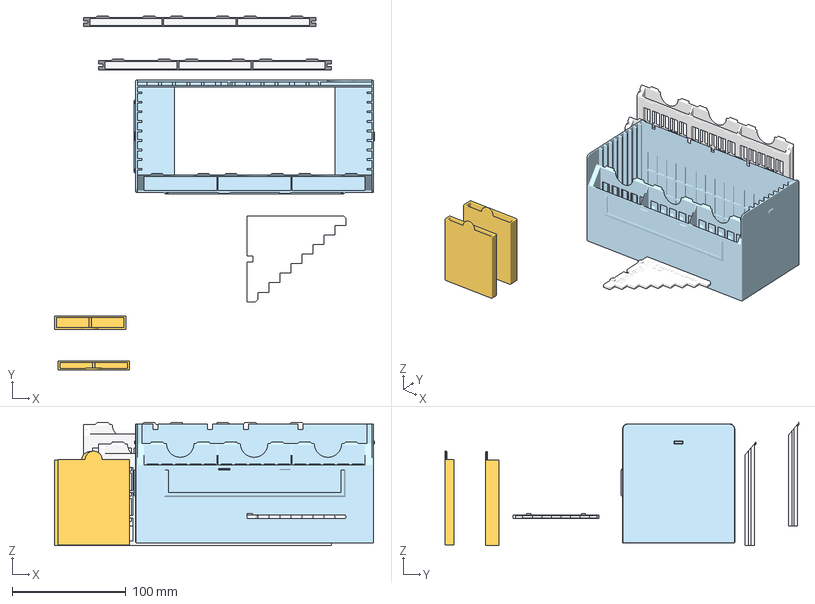
[picture p172: CAD file, 2026-09-03]
individual/Dominion/_raw/Assembly S9.21.10.62-Sl.3mf
281.9 x 311.4 x 108.3 mm
