amertner/cardcascade/individual/Dominion/_raw/Assembly M4.21.10.45-Sl.3mf

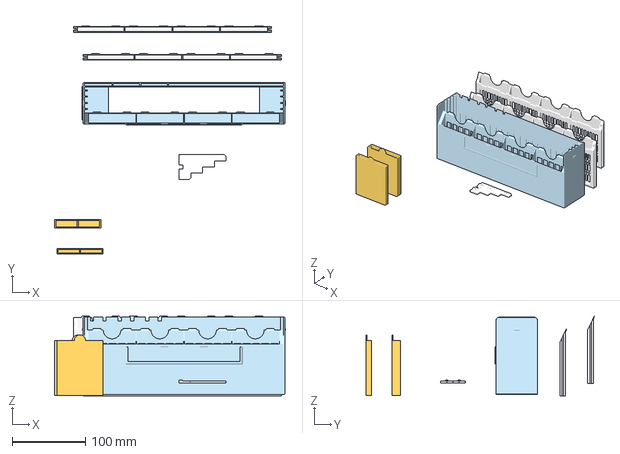
[picture p173: CAD file, 2026-09-02]
individual/Dominion/_raw/Assembly M4.21.10.45-Sl.3mf
314.4 x 311.0 x 108.5 mm
