amertner/cardcascade/individual/Dominion/_raw/Assembly M4.21.10.45-Un merged.3mf

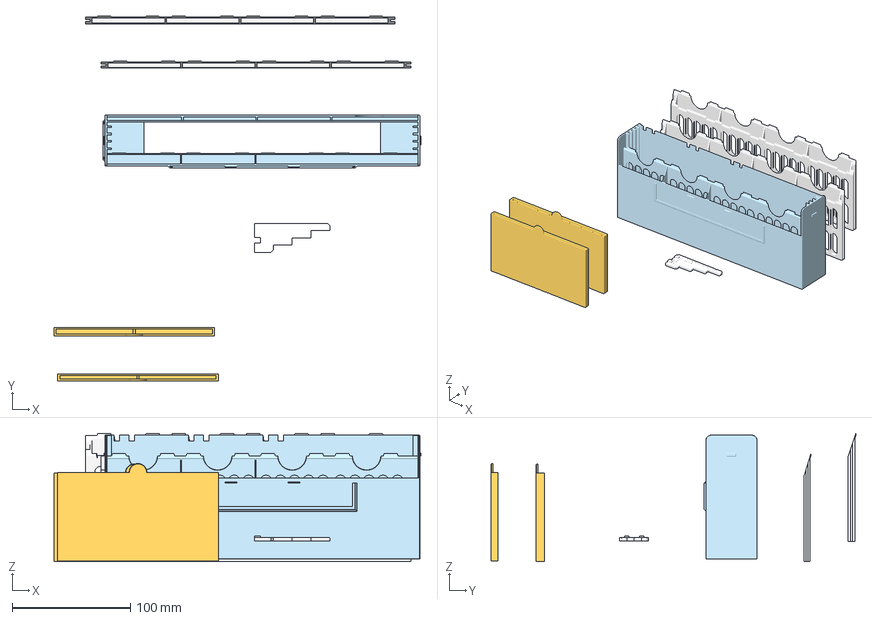
[picture p175: CAD file, 2026-08-09]
individual/Dominion/_raw/Assembly M4.21.10.45-Un merged.3mf
310.4 x 308.5 x 108.6 mm
