amertner/cardcascade/_templates/innovation_h2c.3mf

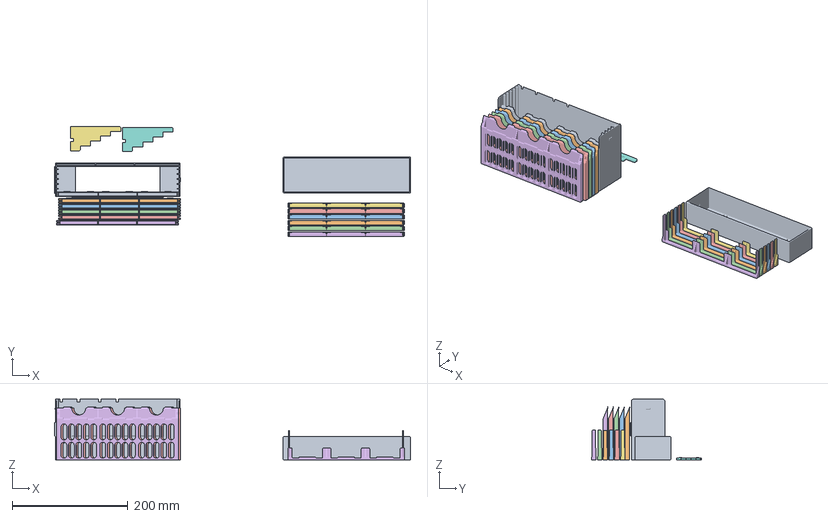
[picture p176: CAD file, 2026-08-06]
_templates/innovation_h2c.3mf
614.9 x 190.1 x 105.0 mm
Holder x 5
Pusher x 2
Lid 270U
Topper
Topper Echoes S-Un
Topper Artifacts S-Un
Topper Cities S-Un
Topper Figures S-Un
Topper Unseen S-Un
