amertner/cardcascade/cascades/Colours/Mamta Box 1.3mf

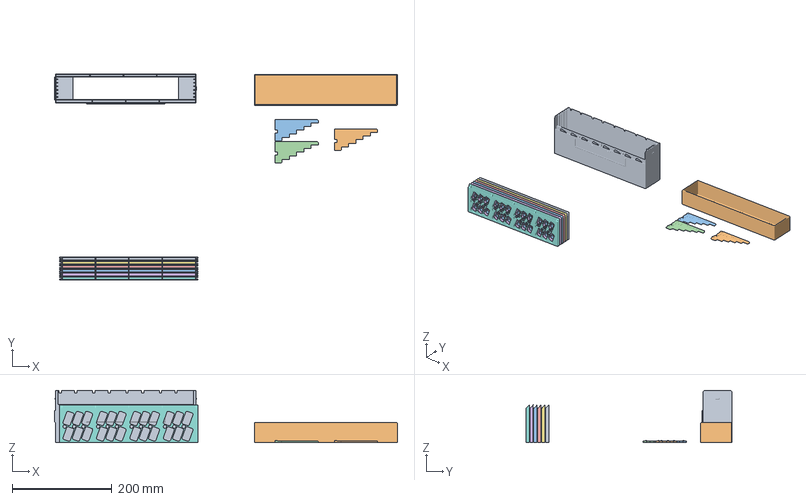
[picture p177: CAD file, 2026-07-15]
cascades/Colours/Mamta Box 1.3mf
687.4 x 413.1 x 105.0 mm
Lid (1)
Holder x 6
Pusher x 3
