amertner/cardcascade/cascades/Compile/Compile 105 Card Unsleeved (S4.7.7.20-Un).3mf

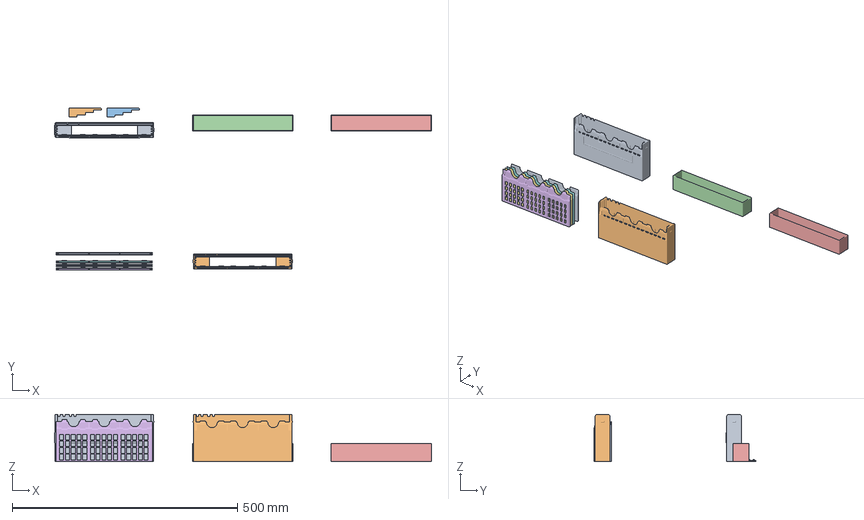
[picture p178: CAD file, 2026-09-14]
cascades/Compile/Compile 105 Card Unsleeved (S4.7.7.20-Un).3mf
836.3 x 360.1 x 105.0 mm
Pusher x 2
Lid 105U
Lid 105U Unmarked
Holder x 3
RearHolder
PlainBox
