amertner/cardcascade/cascades/Compile/labels/Compile Logo Labels.3mf

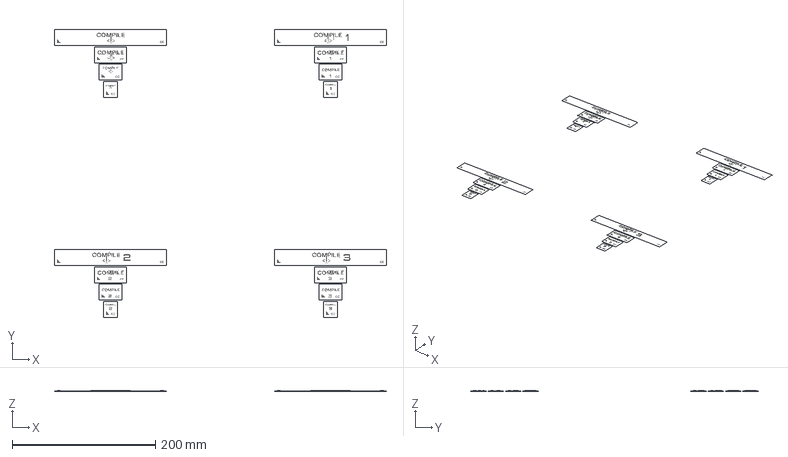
[picture p179: CAD file, 2026-08-16]
cascades/Compile/labels/Compile Logo Labels.3mf
463.6 x 402.0 x 1.20 mm
Logo_156.4mm
Logo_45mm
Logo_32mm
Logo_20mm
Logo_1_156.4mm
Logo_1_45mm
Logo_1_32mm
Logo_1_20mm
Logo_2_156.4mm
Logo_2_45mm
Logo_2_32mm
Logo_2_20mm
Logo_3_156.4mm
Logo_3_45mm
Logo_3_32mm
Logo_3_20mm
