amertner/cardcascade/cascades/Dominion/Dominion 472 Card Sleeved (M2.60.18-40.62-Sl).3mf

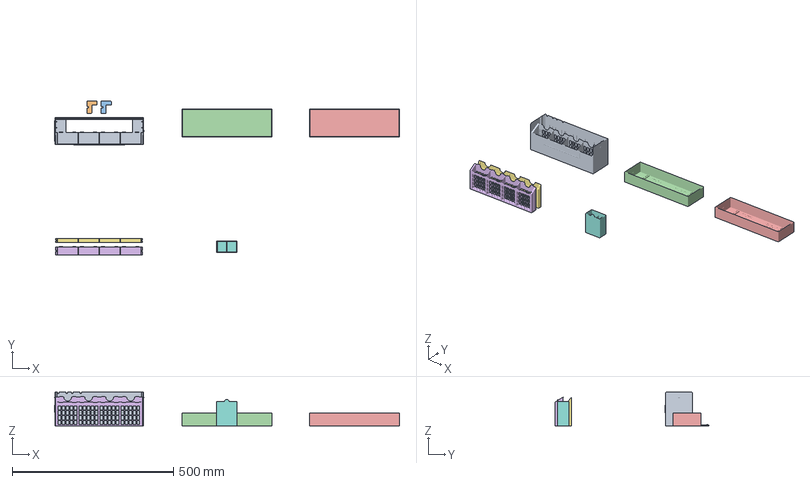
[picture p180: CAD file, 2026-09-14]
cascades/Dominion/Dominion 472 Card Sleeved (M2.60.18-40.62-Sl).3mf
1069.9 x 479.0 x 105.0 mm
Pusher x 2
Lid 472S
Lid 472S Unmarked
FirstHolder
RearHolder
TokenHolder
