amertner/cardcascade/cascades/Dominion/labels/Allies Labels.3mf

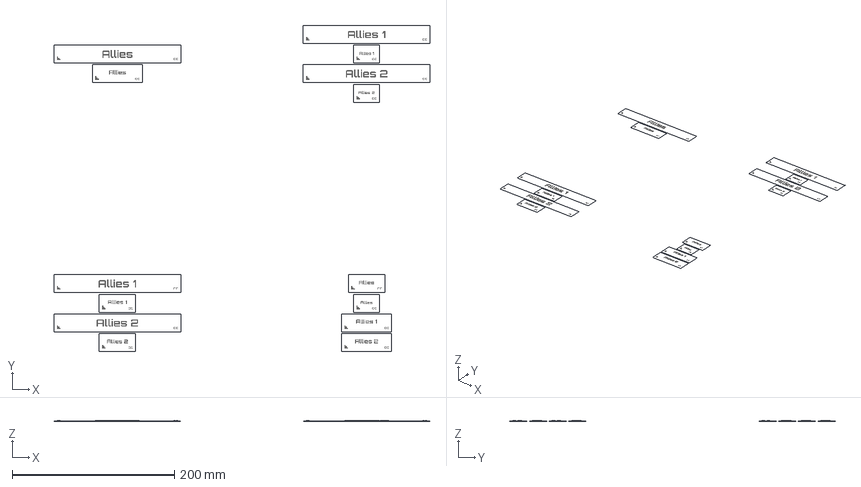
[picture p181: CAD file, 2026-08-16]
cascades/Dominion/labels/Allies Labels.3mf
463.6 x 402.0 x 1.20 mm
Allies_156.4mm
Allies_62mm
Allies_1_156.4mm x 2
Allies_1_32mm
Allies_2_156.4mm x 2
Allies_2_32mm
Allies_1_45mm
Allies_2_45mm
Allies_45mm
Allies_32mm
Allies_1_62mm
Allies_2_62mm
