amertner/cardcascade/cascades/FCM/FCM Alt S (198 Card S4-18-12-45-Sl).3mf

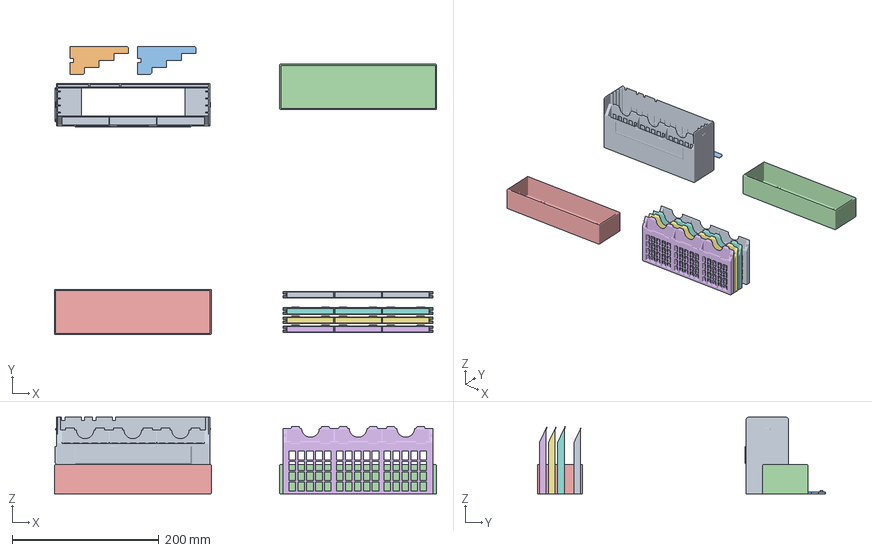
[picture p182: CAD file, 2026-09-14]
cascades/FCM/FCM Alt S (198 Card S4-18-12-45-Sl).3mf
521.1 x 393.3 x 105.0 mm
Pusher x 2
Lid 198S
Lid 198S Unmarked
Holder x 3
RearHolder
