amertner/cardcascade/cascades/FCM/labels/Milestones Labels.3mf

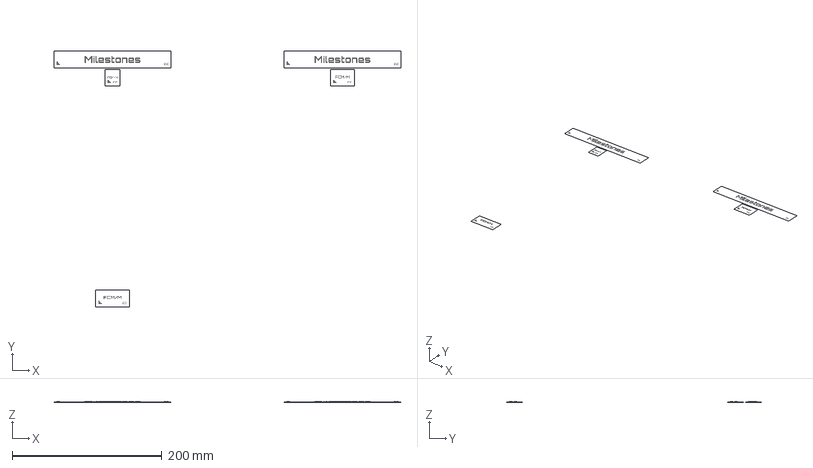
[picture p183: CAD file, 2026-08-16]
cascades/FCM/labels/Milestones Labels.3mf
463.6 x 341.5 x 1.20 mm
Milestones_156.4mm x 2
FCM_M_20mm
FCM_M_32mm
FCM_M_45mm
