amertner/cardcascade/cascades/Innovation/Innovation 4 Ages 5 Expansions Unsleeved (M5.15.15.45-Un).3mf

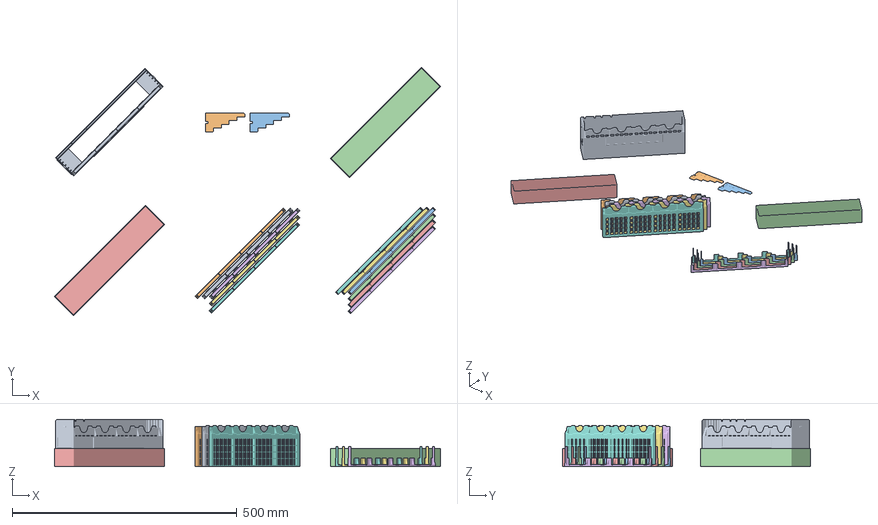
[picture p184: CAD file, 2026-09-14]
cascades/Innovation/Innovation 4 Ages 5 Expansions Unsleeved (M5.15.15.45-Un).3mf
859.4 x 552.2 x 105.0 mm
Pusher x 2
Lid 360U
Lid 360U Unmarked
Holder x 4
RearHolder
Topper Blank
Topper Artifacts
Topper Cities
Topper Echoes
Topper Figures
Topper Unseen
