amertner/cardcascade/cascades/Innovation/labels/Innovation 3-Expansion Cascades Labels.3mf

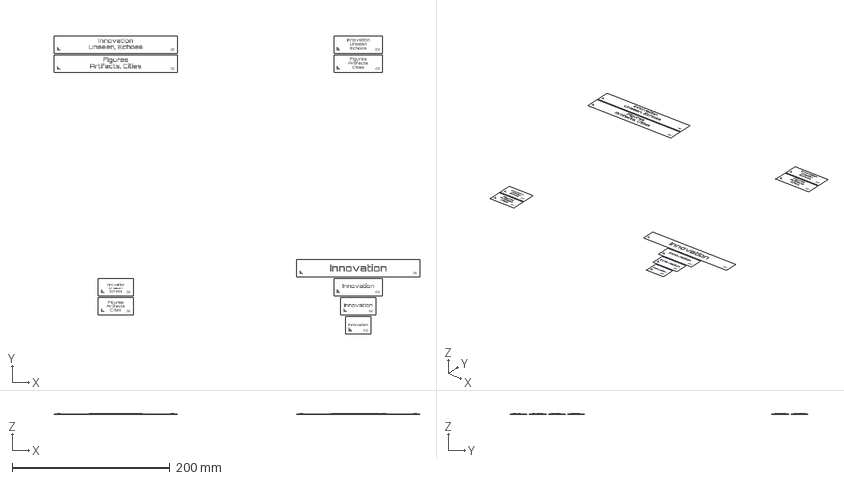
[picture p185: CAD file, 2026-09-13]
cascades/Innovation/labels/Innovation 3-Expansion Cascades Labels.3mf
463.6 x 377.8 x 1.20 mm
Innovation___Unseen__Echoes_156.4mm
Figures___Artifacts__Cities_156.4mm
Innovation___Unseen___Echoes_62mm
Figures___Artifacts___Cities_62mm
Innovation___Unseen___Echoes_45mm
Figures___Artifacts___Cities_45mm
Innovation_156.4mm
Innovation_62mm
Innovation_45mm
Innovation_32mm
