amertner/cardcascade/cascades/MiniCards/labels/Blank Labels.3mf

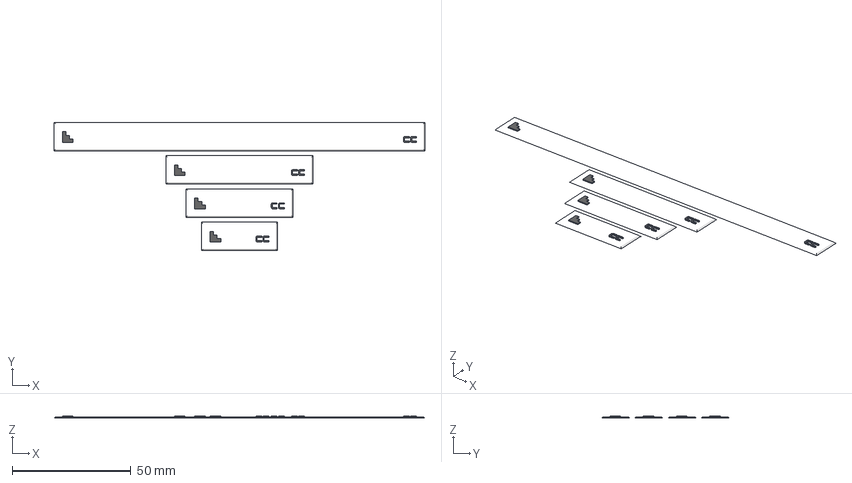
[picture p186: CAD file, 2026-09-22]
cascades/MiniCards/labels/Blank Labels.3mf
156.4 x 54.0 x 1.00 mm
Blank_156.4mm
Blank_62mm
Blank_45mm
Blank_32mm
