amertner/cardcascade/cascades/MiniCards/Mini Cards 350 Card Unsleeved (86-L6.10.10.32-Un).3mf

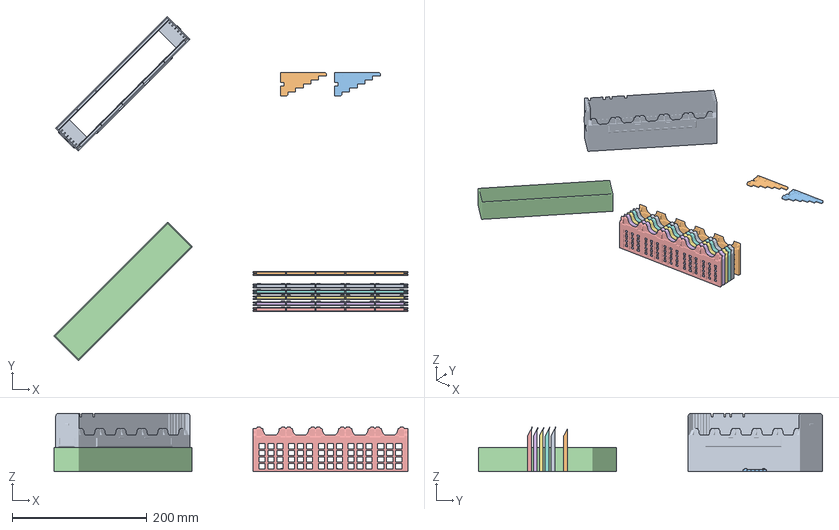
[picture p187: CAD file, 2026-09-22]
cascades/MiniCards/Mini Cards 350 Card Unsleeved (86-L6.10.10.32-Un).3mf
524.4 x 509.8 x 86.0 mm
Pusher x 2
Lid 350U Unmarked
Holder x 5
RearHolder
