amertner/cardcascade/individual/Compile/Lid L5.7.7.45-Sl.3mf

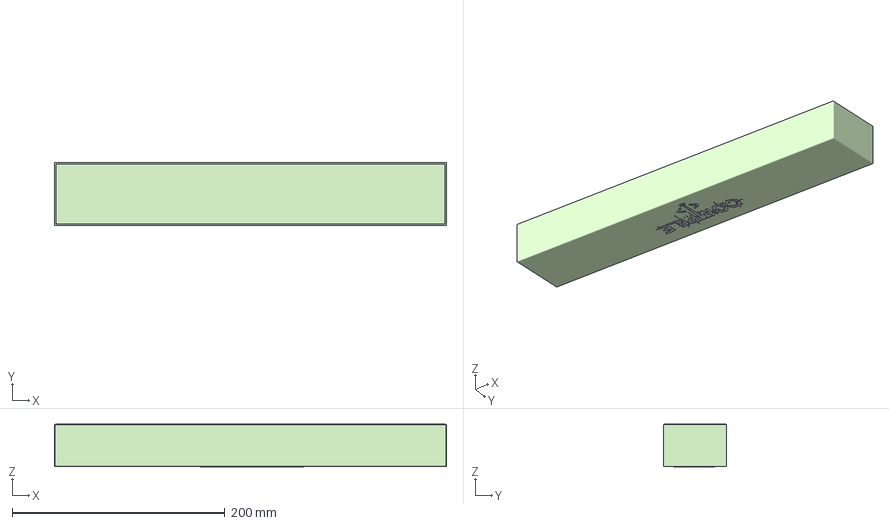
[picture p188: CAD file, 2026-09-05]
individual/Compile/Lid L5.7.7.45-Sl.3mf
368.9 x 59.7 x 40.0 mm
Lid
