amertner/cardcascade/individual/Dominion/Pusher 2x12-Un.3mf

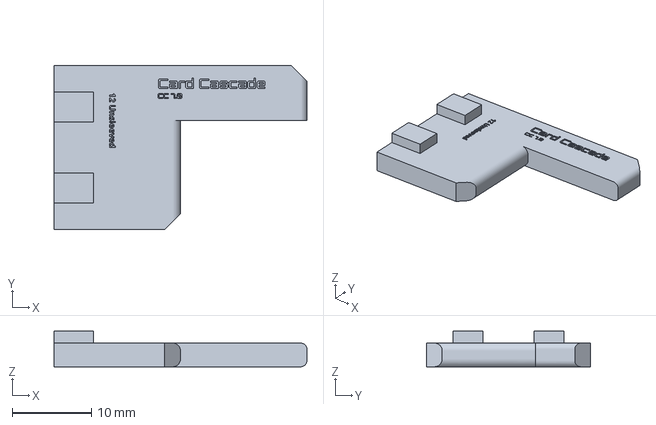
[picture p189: CAD file, 2026-09-05]
individual/Dominion/Pusher 2x12-Un.3mf
32.0 x 20.8 x 4.50 mm
