amertner/cardcascade/individual/FCM/Box S4.18.12.32-Un.3mf

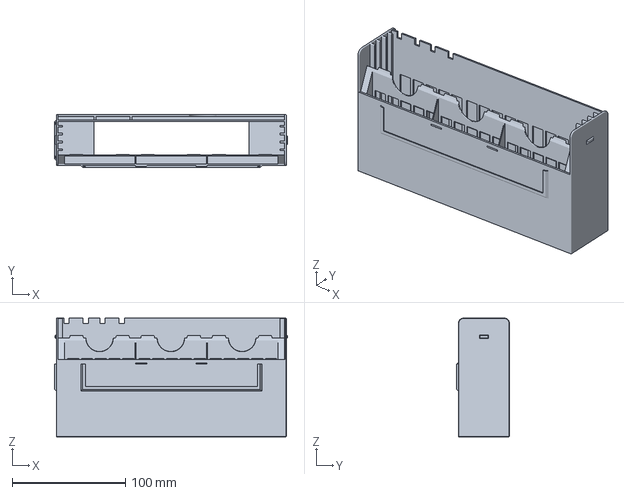
[picture p190: CAD file, 2026-09-05]
individual/FCM/Box S4.18.12.32-Un.3mf
205.9 x 46.8 x 105.0 mm
