amertner/cardcascade/individual/Innovation/Box XS5.15.10.32-Un.3mf

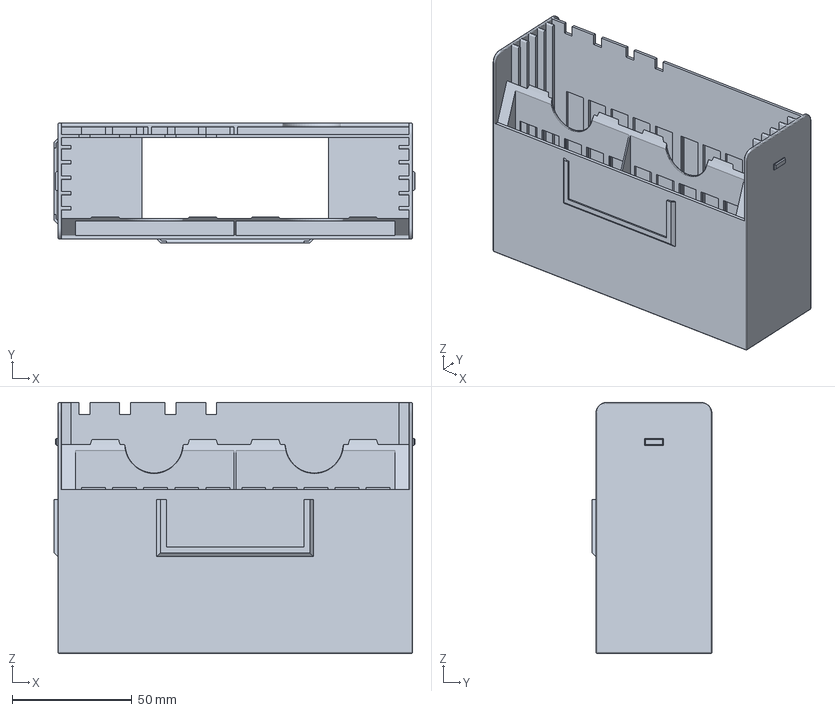
[picture p191: CAD file, 2026-09-03]
individual/Innovation/Box XS5.15.10.32-Un.3mf
150.9 x 50.1 x 105.0 mm
