amertner/cardcascade/logos/Compile/lid_logo.dxf

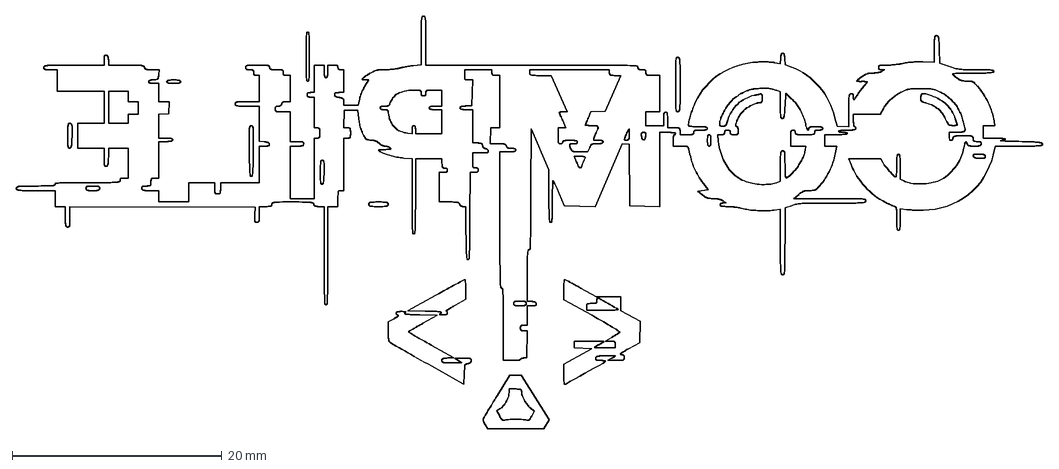
[picture p192: CAD file, 2026-09-02]
logos/Compile/lid_logo.dxf
97.8 x 39.3 mm
