amertner/cardcascade/logos/Dominion/lid_logo.dxf

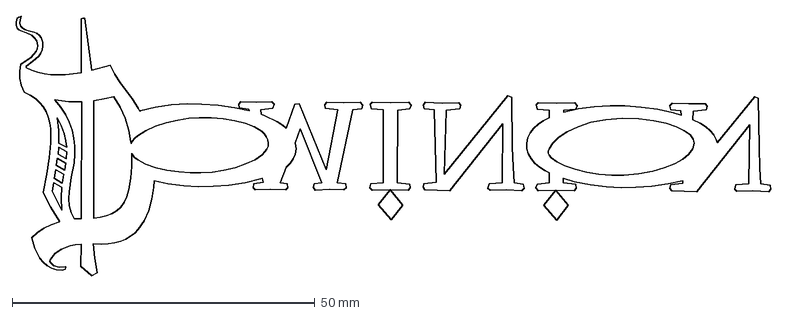
[picture p193: CAD file, 2026-09-02]
logos/Dominion/lid_logo.dxf
124.7 x 42.9 mm
