amertner/cardcascade/logos/FCM/lid_logo.dxf

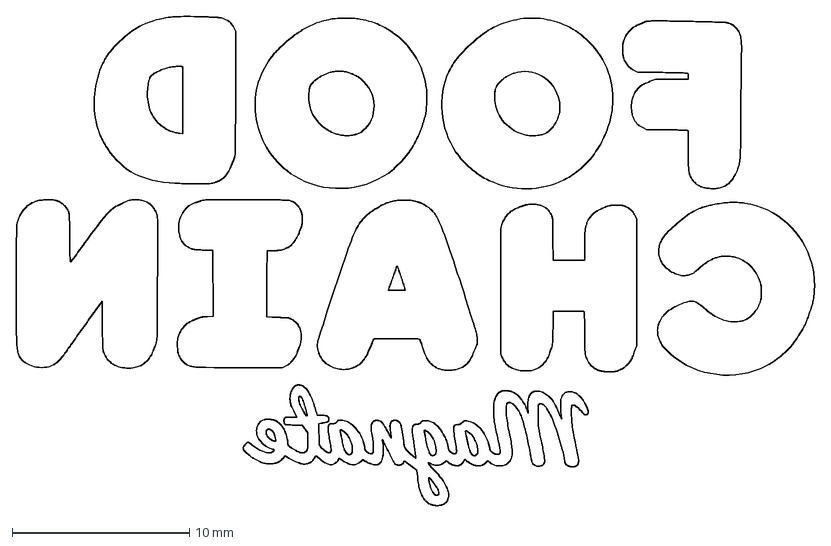
[picture p194: CAD file, 2026-09-02]
logos/FCM/lid_logo.dxf
45.0 x 27.6 mm
