amertner/cardcascade/logos/Innovation/lid_logo_plain_big.dxf

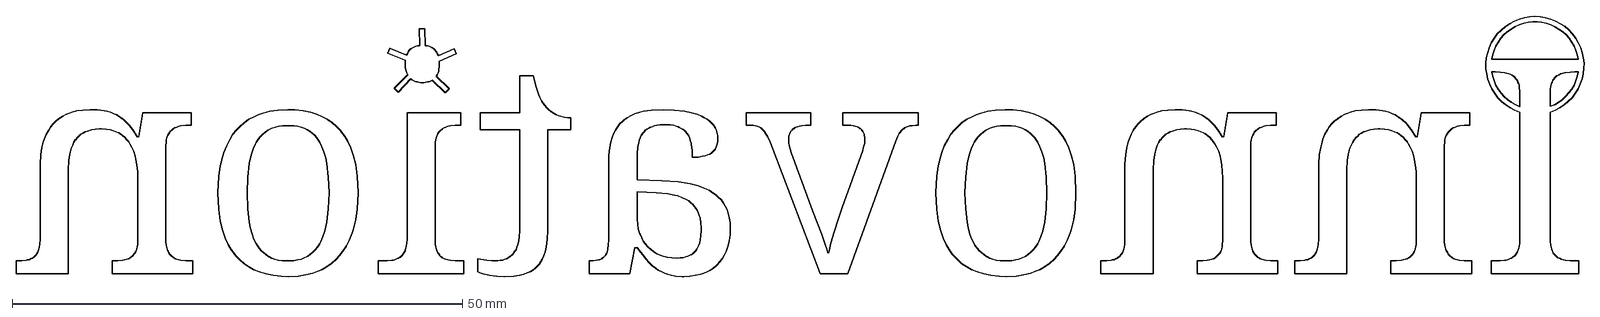
[picture p195: CAD file, 2026-09-02]
logos/Innovation/lid_logo_plain_big.dxf
174.1 x 28.9 mm
