amertner/cardcascade/logos/Innovation/sketch/Logo Flourishes.dxf

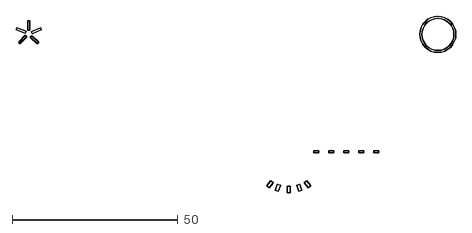
[picture p196: CAD file, 2026-09-04]
logos/Innovation/sketch/Logo Flourishes.dxf
132.8 x 53.2
