amertner/cardcascade/spec/reference/shipped-7.0/Compile/Compile 210 Card Unsleeved (L5.7.7.20-Un).3mf

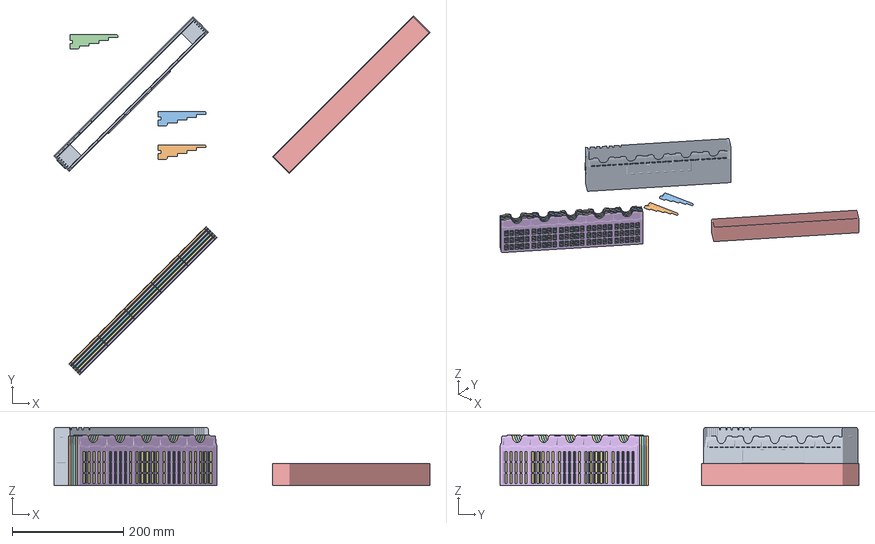
[picture p197: CAD file, 2026-09-05]
spec/reference/shipped-7.0/Compile/Compile 210 Card Unsleeved (L5.7.7.20-Un).3mf
676.9 x 646.3 x 105.0 mm
Pusher x 3
Lid 210U
Holder x 5
