amertner/cardcascade/spec/reference/shipped-7.0/Dominion/Dominion 246 Card Unsleeved (S2.40.12-30.32-Un).3mf

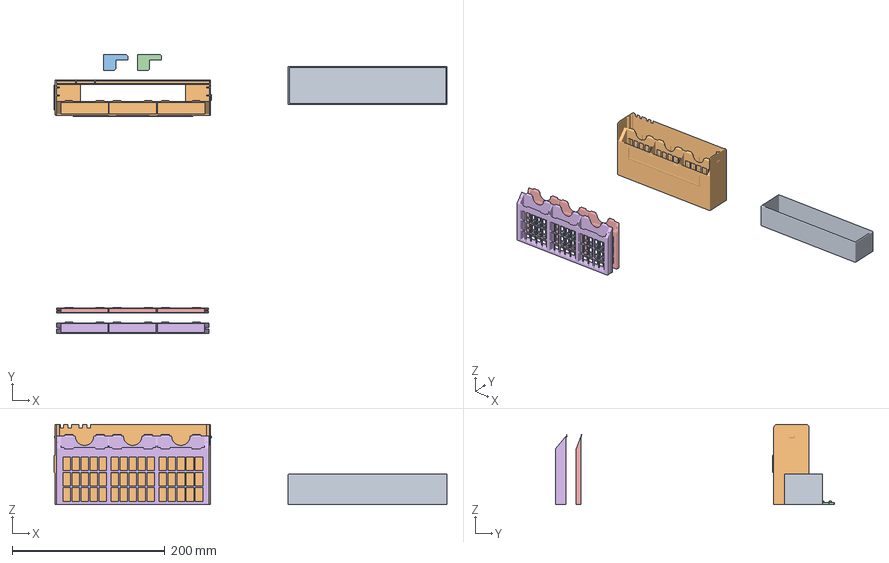
[picture p198: CAD file, 2026-09-05]
spec/reference/shipped-7.0/Dominion/Dominion 246 Card Unsleeved (S2.40.12-30.32-Un).3mf
514.1 x 364.4 x 105.0 mm
Lid 246U
Pusher x 2
Holder
FirstHolder
