amertner/cardcascade/spec/reference/shipped-7.0/FCM/FCM Alt S (198 Card S4-18-12-45-Sl).3mf

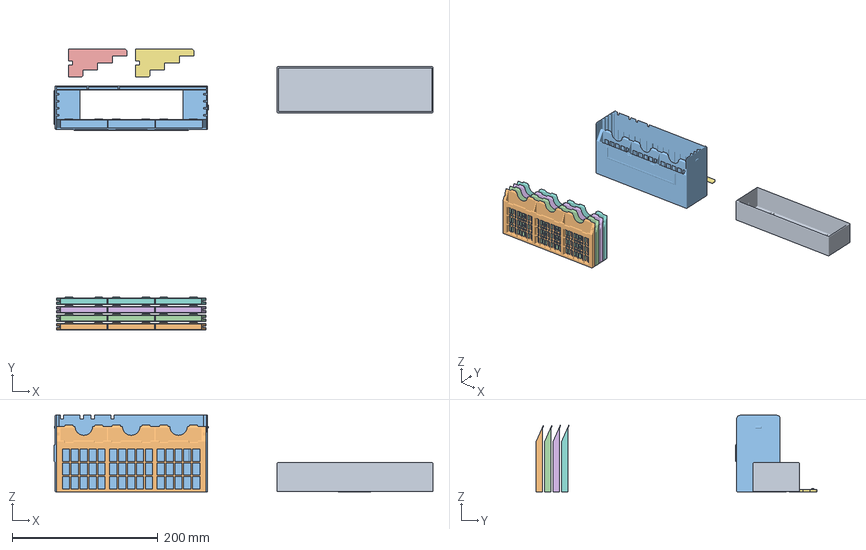
[picture p199: CAD file, 2026-09-05]
spec/reference/shipped-7.0/FCM/FCM Alt S (198 Card S4-18-12-45-Sl).3mf
520.1 x 385.5 x 105.0 mm
Lid 198S
Holder x 4
Pusher x 2
