amertner/cardcascade/spec/reference/shipped-7.0/Innovation/Innovation 4 Ages 5 Expansions Sleeved (M5.15.15.62-Sl).3mf

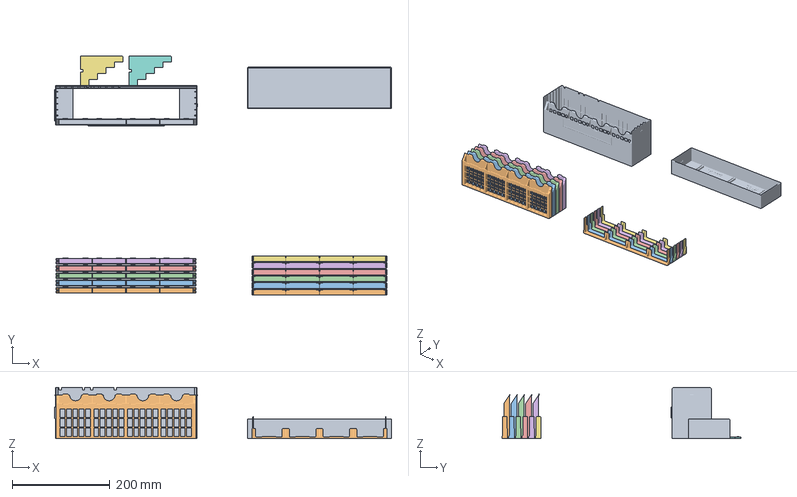
[picture p200: CAD file, 2026-09-03]
spec/reference/shipped-7.0/Innovation/Innovation 4 Ages 5 Expansions Sleeved (M5.15.15.62-Sl).3mf
689.9 x 489.9 x 105.0 mm
Holder x 5
Pusher x 2
Lid 360S
Topper
Topper Echoes S-Un
Topper Artifacts S-Un
Topper Cities S-Un
Topper Figures S-Un
Topper Unseen S-Un
