amertner/cardcascade/cascades/Compile/Compile 210 Card Unsleeved (L5.7.7.20-Un).3mf

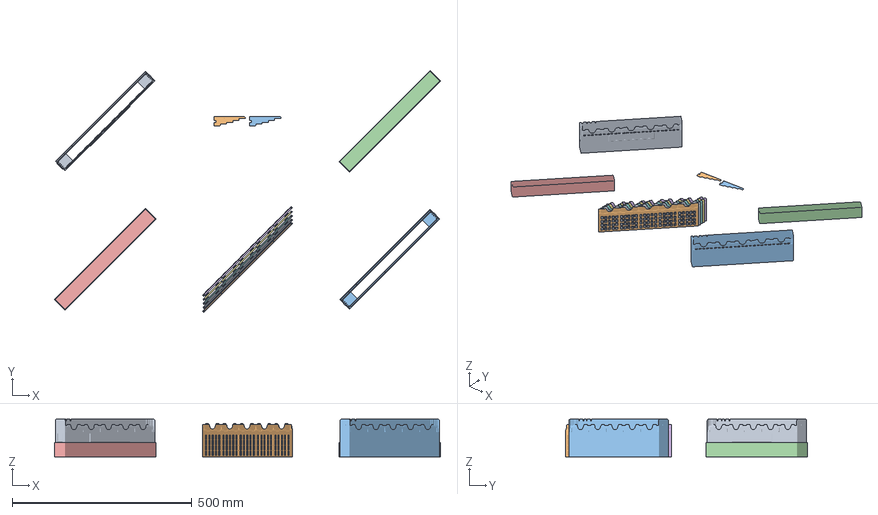
[picture p202: CAD file, 2026-09-14]
cascades/Compile/Compile 210 Card Unsleeved (L5.7.7.20-Un).3mf
1074.3 x 672.9 x 105.0 mm
Pusher x 2
Lid 210U
Lid 210U Unmarked
Holder x 4
RearHolder
PlainBox
