amertner/cardcascade/cascades/Compile/labels/Compile Labels.3mf

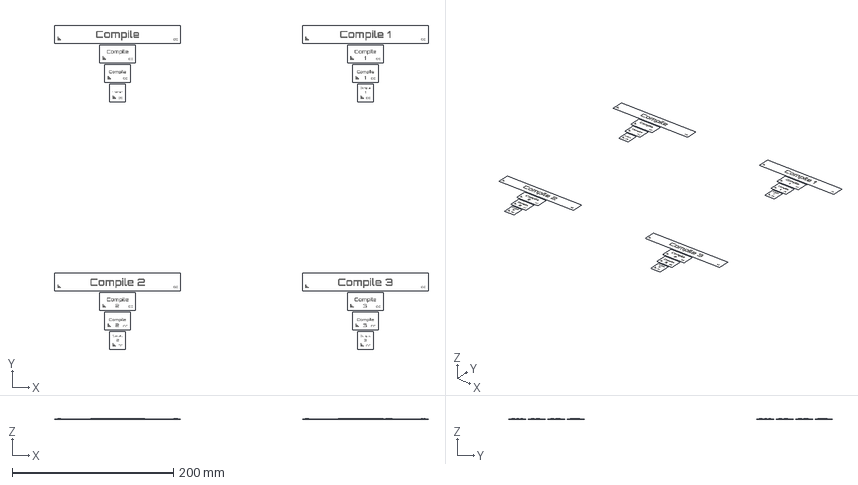
[picture p203: CAD file, 2026-08-16]
cascades/Compile/labels/Compile Labels.3mf
463.6 x 402.0 x 1.20 mm
Compile_156.4mm
Compile_45mm
Compile_32mm
Compile_20mm
Compile_1_156.4mm
Compile_1_45mm
Compile_1_32mm
Compile_1_20mm
Compile_2_156.4mm
Compile_2_45mm
Compile_2_32mm
Compile_2_20mm
Compile_3_156.4mm
Compile_3_45mm
Compile_3_32mm
Compile_3_20mm
