amertner/cardcascade/cascades/Dominion/Dominion 400 Card (Mat) Sleeved (M8.40.10.62-Sl).3mf

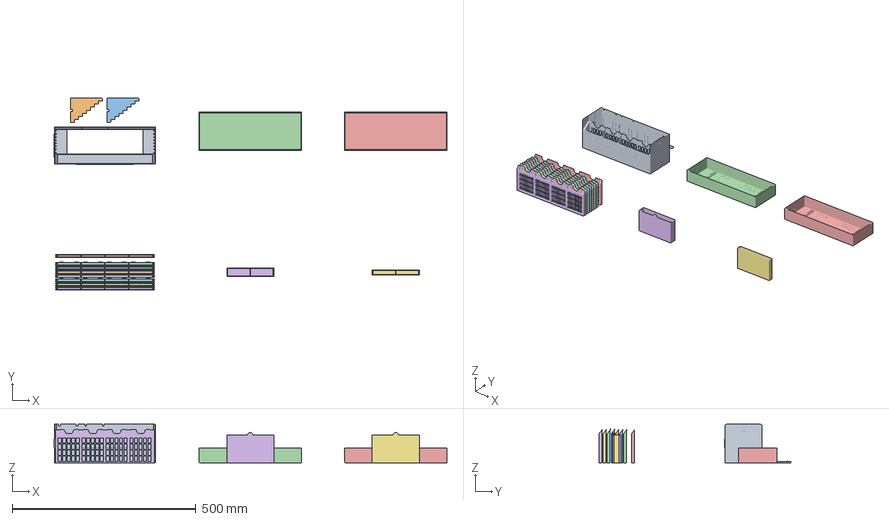
[picture p204: CAD file, 2026-09-14]
cascades/Dominion/Dominion 400 Card (Mat) Sleeved (M8.40.10.62-Sl).3mf
1069.9 x 522.8 x 105.0 mm
Pusher x 2
Lid 400S
Lid 400S Unmarked
Holder x 7
RearHolder
TokenHolder
HalfTokenHolder
