amertner/cardcascade/cascades/Dominion/labels/Menagerie Labels.3mf

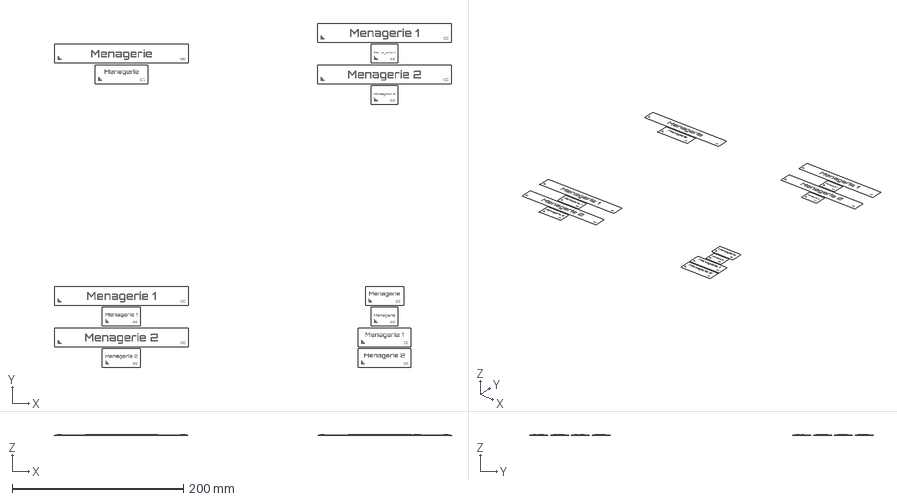
[picture p205: CAD file, 2026-08-16]
cascades/Dominion/labels/Menagerie Labels.3mf
463.6 x 402.0 x 1.20 mm
Menagerie_156.4mm
Menagerie_62mm
Menagerie_1_156.4mm x 2
Menagerie_1_32mm
Menagerie_2_156.4mm x 2
Menagerie_2_32mm
Menagerie_1_45mm
Menagerie_2_45mm
Menagerie_45mm
Menagerie_32mm
Menagerie_1_62mm
Menagerie_2_62mm
