amertner/cardcascade/cascades/FCM/FCM Milestones 1U (144 Card M5-6-6-20-Un).3mf

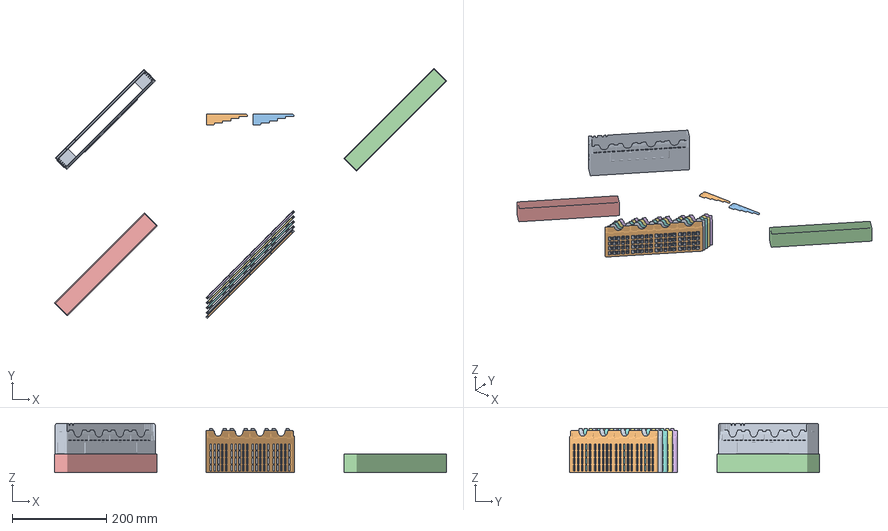
[picture p206: CAD file, 2026-09-14]
cascades/FCM/FCM Milestones 1U (144 Card M5-6-6-20-Un).3mf
832.3 x 531.2 x 105.0 mm
Pusher x 2
Lid 144U
Lid 144U Unmarked
Holder x 4
RearHolder
