amertner/cardcascade/cascades/FCM/labels/Occupations Labels.3mf

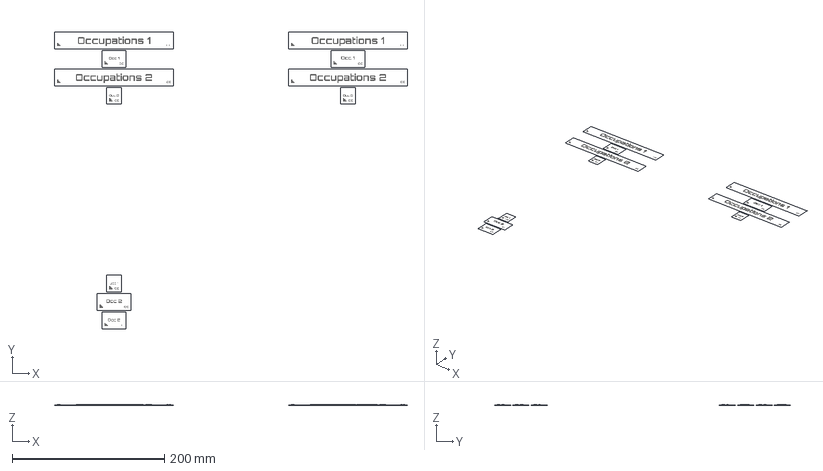
[picture p207: CAD file, 2026-08-16]
cascades/FCM/labels/Occupations Labels.3mf
463.6 x 389.9 x 1.20 mm
Occupations_1_156.4mm x 2
Occ_1_32mm
Occupations_2_156.4mm x 2
Occ_2_20mm x 2
Occ_1_45mm
Occ_1_20mm
Occ_2_45mm
Occ_2_32mm
