amertner/cardcascade/cascades/Innovation/Innovation 3 Later Ages 5 Expansions Unsleeved (S5.10.10.32-Un).3mf

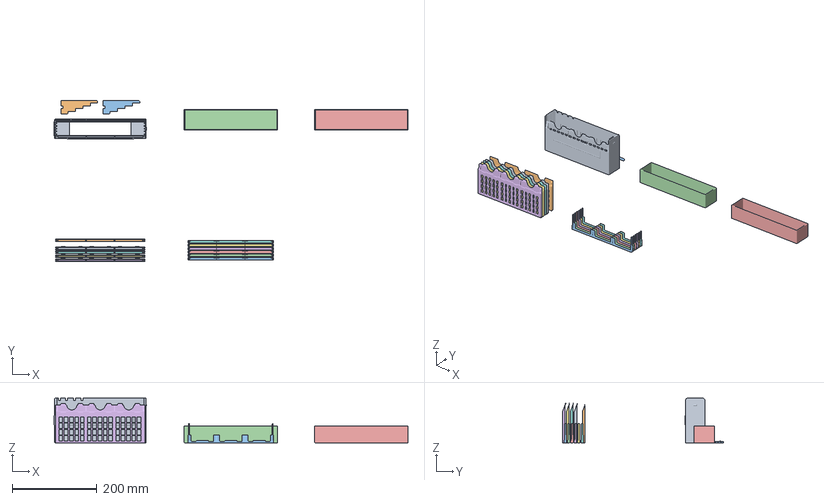
[picture p208: CAD file, 2026-09-14]
cascades/Innovation/Innovation 3 Later Ages 5 Expansions Unsleeved (S5.10.10.32-Un).3mf
833.3 x 378.9 x 105.0 mm
Pusher x 2
Lid 180U
Lid 180U Unmarked
Holder x 4
RearHolder
Topper Blank
Topper Artifacts
Topper Cities
Topper Echoes
Topper Figures
Topper Unseen
