amertner/cardcascade/cascades/Innovation/labels/Single Set Labels.3mf

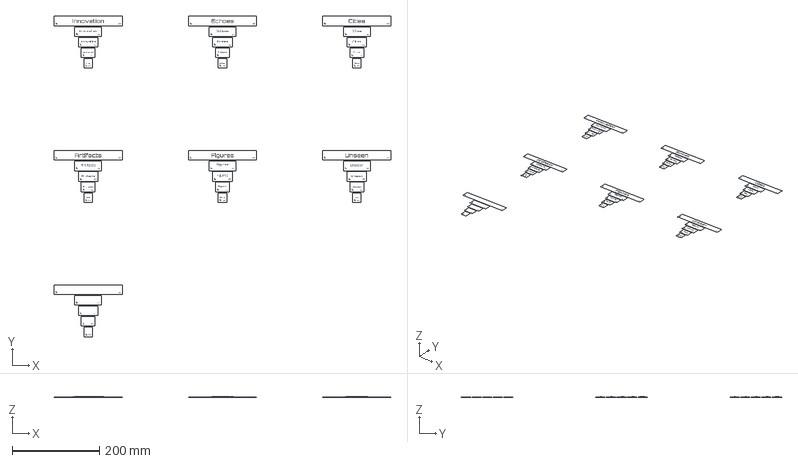
[picture p209: CAD file, 2026-08-31]
cascades/Innovation/labels/Single Set Labels.3mf
770.8 x 733.4 x 1.20 mm
Innovation_156.4mm
Innovation_62mm
Innovation_45mm
Innovation_32mm
Inno_20mm
Echoes_156.4mm
Echoes_62mm
Echoes_45mm
Echoes_32mm
Echoes_20mm
Cities_156.4mm
Cities_62mm
Cities_45mm
Cities_32mm
Cities_20mm
Artifacts_156.4mm
Artifacts_62mm
Artifacts_45mm
Artifacts_32mm
Artif_20mm
Figures_156.4mm
Figures_62mm
Figures_45mm
Figures_32mm
Figures_20mm
Unseen_156.4mm
Unseen_62mm
Unseen_45mm
Unseen_32mm
Unseen_20mm
Blank_156.4mm
Blank_62mm
Blank_45mm
Blank_32mm
Blank_20mm
