amertner/cardcascade/cascades/MiniCards/Mini Cards 120 Card Unsleeved (86-XS5.10.10.32-Un).3mf

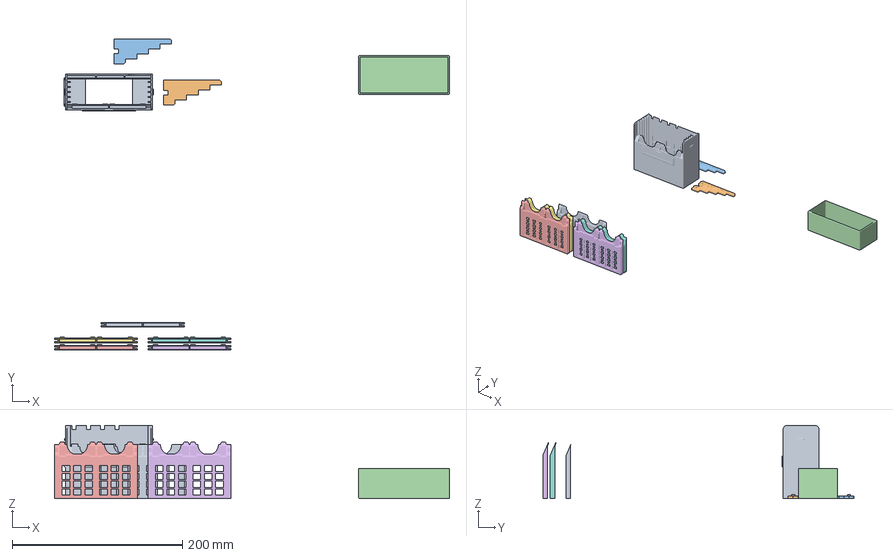
[picture p210: CAD file, 2026-09-22]
cascades/MiniCards/Mini Cards 120 Card Unsleeved (86-XS5.10.10.32-Un).3mf
464.4 x 366.2 x 86.0 mm
Pusher x 2
Lid 120U Unmarked
Holder x 4
RearHolder
