amertner/cardcascade/individual/Compile/Box S4.7.7.32-Sl.3mf

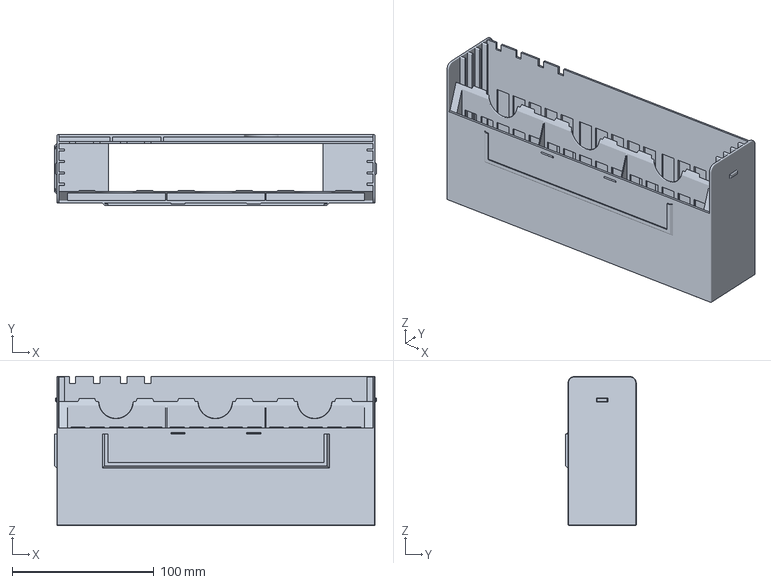
[picture p211: CAD file, 2026-09-05]
individual/Compile/Box S4.7.7.32-Sl.3mf
226.9 x 49.7 x 105.0 mm
