amertner/cardcascade/individual/Dominion/Lid S2.40.12-30.45-Sl.3mf

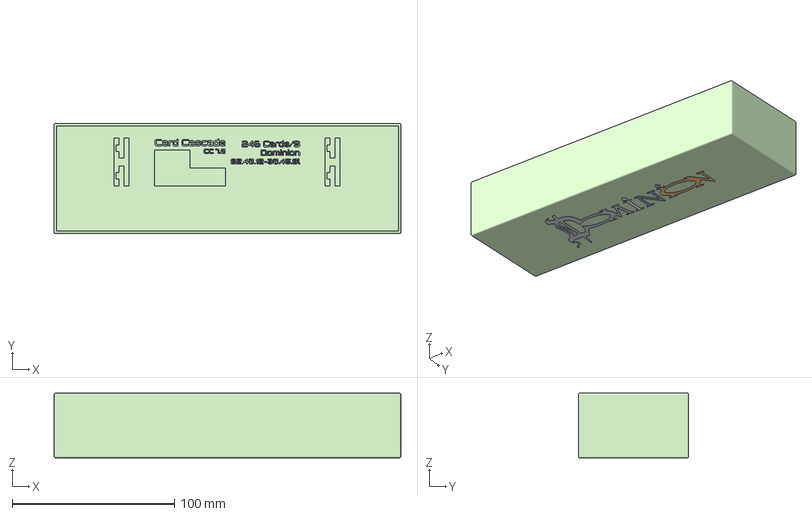
[picture p212: CAD file, 2026-09-05]
individual/Dominion/Lid S2.40.12-30.45-Sl.3mf
213.9 x 68.1 x 40.0 mm
Lid
