amertner/cardcascade/individual/FCM/Pusher 5x6-Sl.3mf

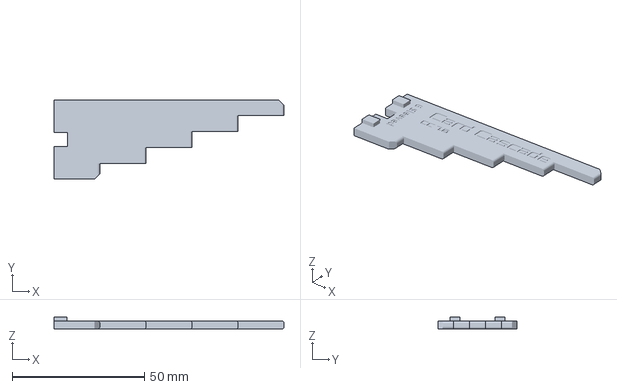
[picture p213: CAD file, 2026-09-05]
individual/FCM/Pusher 5x6-Sl.3mf
87.0 x 30.0 x 4.50 mm
