amertner/cardcascade/individual/Innovation/Lid M5.15.15.62-Sl.3mf

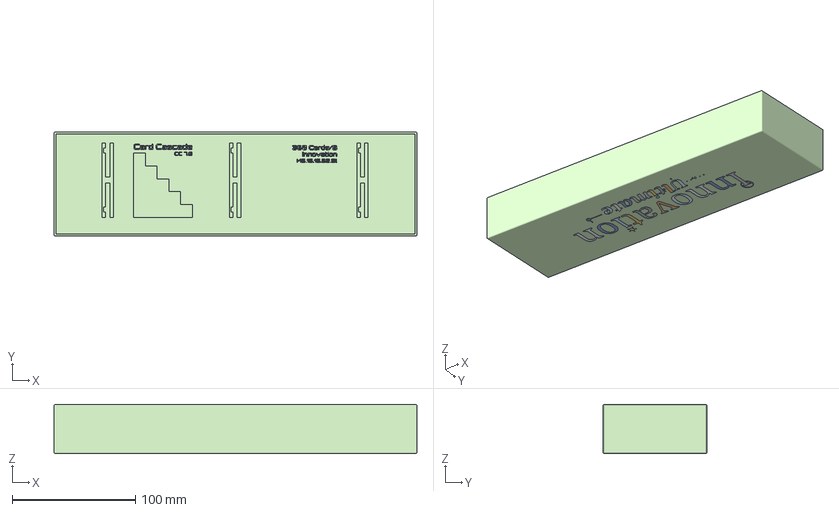
[picture p214: CAD file, 2026-09-03]
individual/Innovation/Lid M5.15.15.62-Sl.3mf
294.9 x 84.6 x 40.0 mm
Lid
