amertner/cardcascade/logos/Compile/compile_logo_clean.dxf

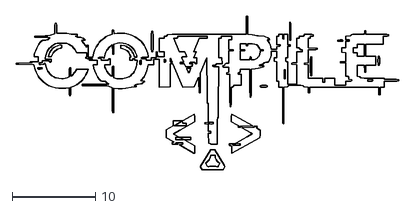
[picture p215: CAD file, 2026-08-15]
logos/Compile/compile_logo_clean.dxf
46.0 x 18.5
