amertner/cardcascade/logos/Innovation/lid_logo_plain.dxf

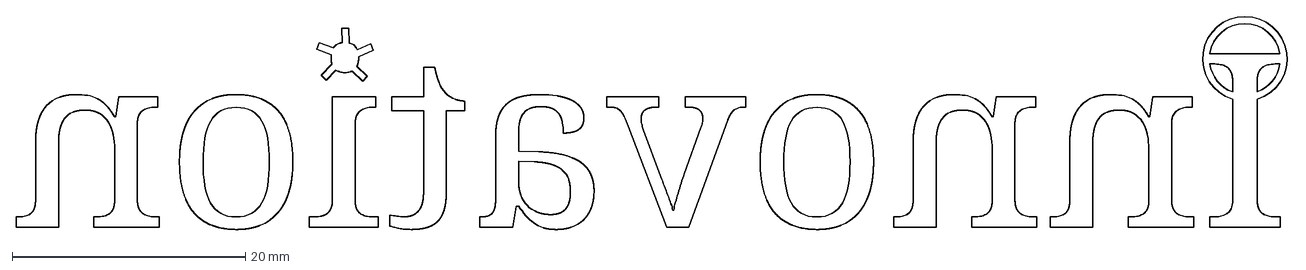
[picture p216: CAD file, 2026-09-02]
logos/Innovation/lid_logo_plain.dxf
109.3 x 18.3 mm
