amertner/cardcascade/spec/reference/shipped-7.0/Compile/Compile 210 Card Sleeved (L5.7.7.45-Sl).3mf

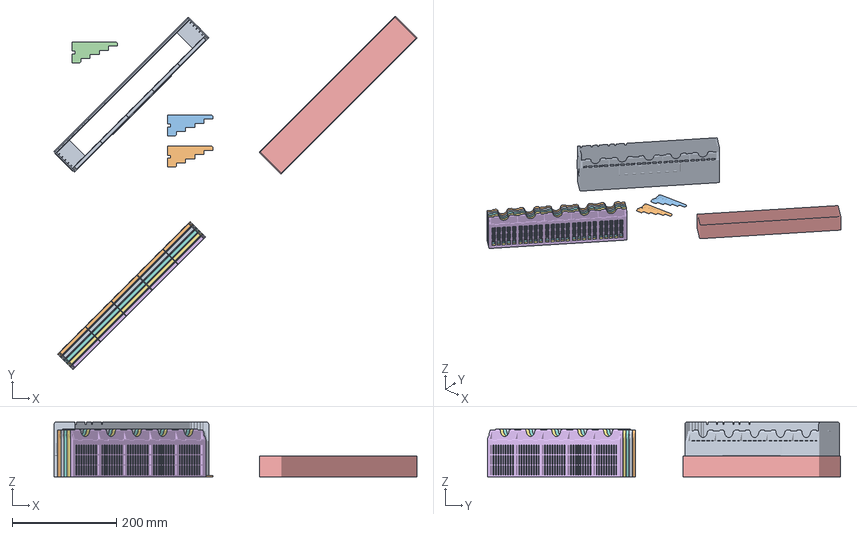
[picture p217: CAD file, 2026-09-05]
spec/reference/shipped-7.0/Compile/Compile 210 Card Sleeved (L5.7.7.45-Sl).3mf
695.9 x 677.5 x 105.0 mm
Pusher x 3
Lid 210S
Holder x 5
