amertner/cardcascade/spec/reference/shipped-7.0/Dominion/Dominion 246 Card Sleeved (S2.40.12-30.45-Sl).3mf

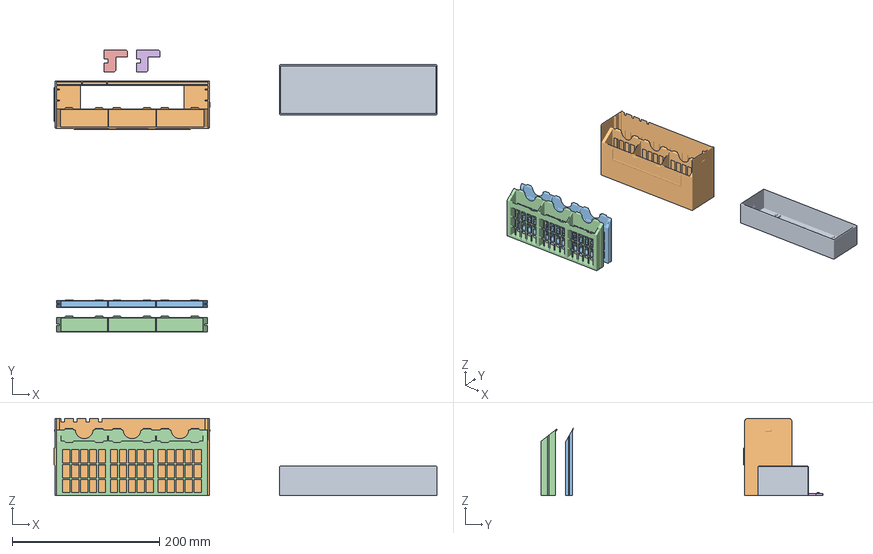
[picture p218: CAD file, 2026-09-05]
spec/reference/shipped-7.0/Dominion/Dominion 246 Card Sleeved (S2.40.12-30.45-Sl).3mf
520.1 x 383.0 x 105.0 mm
Lid 246S
Holder
FirstHolder
Pusher x 2
