amertner/cardcascade/spec/reference/shipped-7.0/FCM/FCM Occ 1U (264 Card M4-18-12-32-Un).3mf

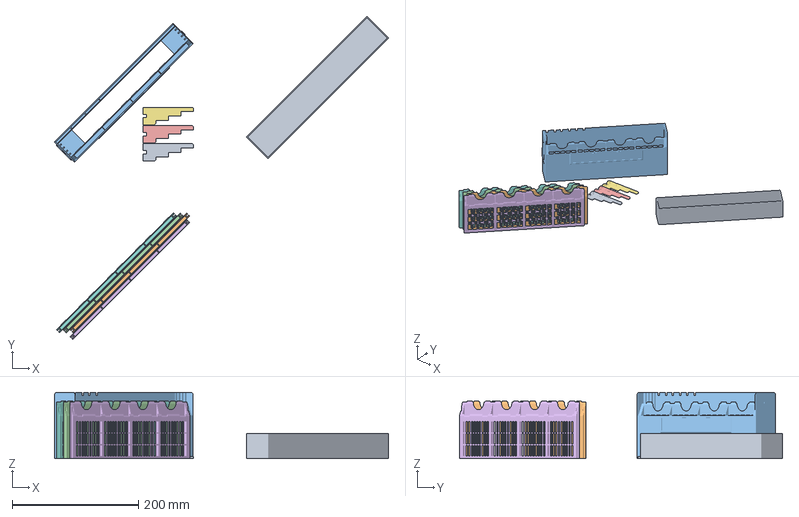
[picture p219: CAD file, 2026-09-05]
spec/reference/shipped-7.0/FCM/FCM Occ 1U (264 Card M4-18-12-32-Un).3mf
529.5 x 512.0 x 105.0 mm
Lid 264U
Holder x 4
Pusher x 3
