amertner/cardcascade/spec/reference/shipped-7.0/Innovation/Innovation 3 Ages 5 Expansions Sleeved (S5.15.15.62-Sl).3mf

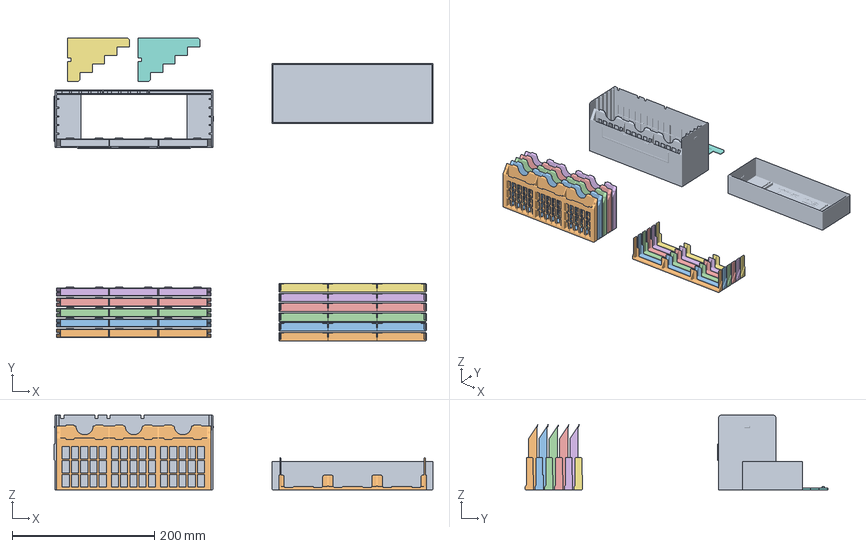
[picture p220: CAD file, 2026-09-03]
spec/reference/shipped-7.0/Innovation/Innovation 3 Ages 5 Expansions Sleeved (S5.15.15.62-Sl).3mf
532.1 x 425.1 x 105.0 mm
Holder x 5
Pusher x 2
Lid 270S
Topper
Topper Echoes S-Sl
Topper Artifacts S-Sl
Topper Cities S-Sl
Topper Figures S-Sl
Topper Unseen S-Sl
