amertner/cardcascade/spec/reference/Text right-aligned sample.step

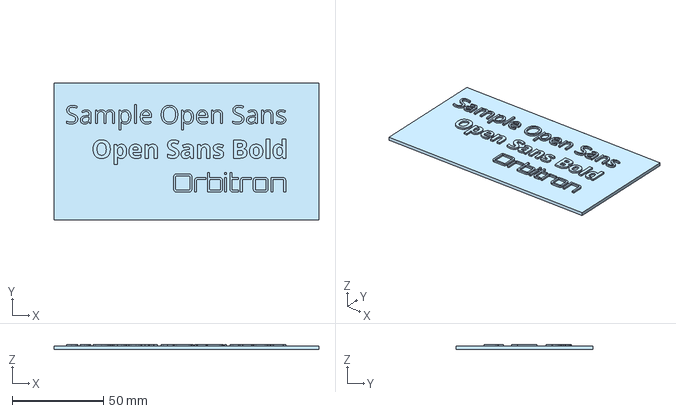
[picture p221: CAD file, 2026-09-04]
spec/reference/Text right-aligned sample.step
145.0 x 74.8 x 3.00 mm
