amertner/cardcascade/cascades/Compile/Compile 126 Card Sleeved (S5.7.7.45-Sl).3mf

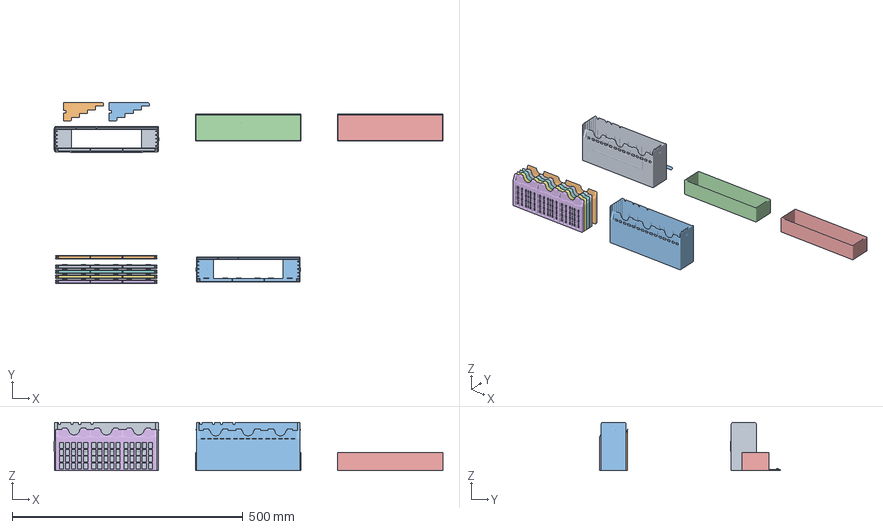
[picture p222: CAD file, 2026-09-14]
cascades/Compile/Compile 126 Card Sleeved (S5.7.7.45-Sl).3mf
842.3 x 391.8 x 105.0 mm
Pusher x 2
Lid 126S
Lid 126S Unmarked
Holder x 4
RearHolder
PlainBox
