amertner/cardcascade/cascades/Dominion/Dominion 324 Card Unsleeved (M6.21.10.45-Un).3mf

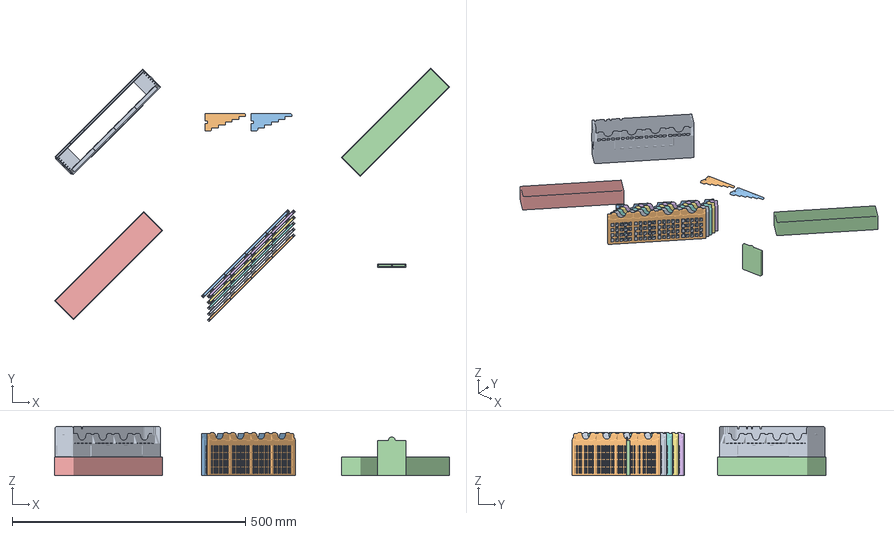
[picture p223: CAD file, 2026-09-14]
cascades/Dominion/Dominion 324 Card Unsleeved (M6.21.10.45-Un).3mf
846.1 x 543.5 x 105.0 mm
Pusher x 2
Lid 324U
Lid 324U Unmarked
Holder x 5
RearHolder
TokenHolder
