amertner/cardcascade/cascades/Dominion/labels/Base Set Labels.3mf

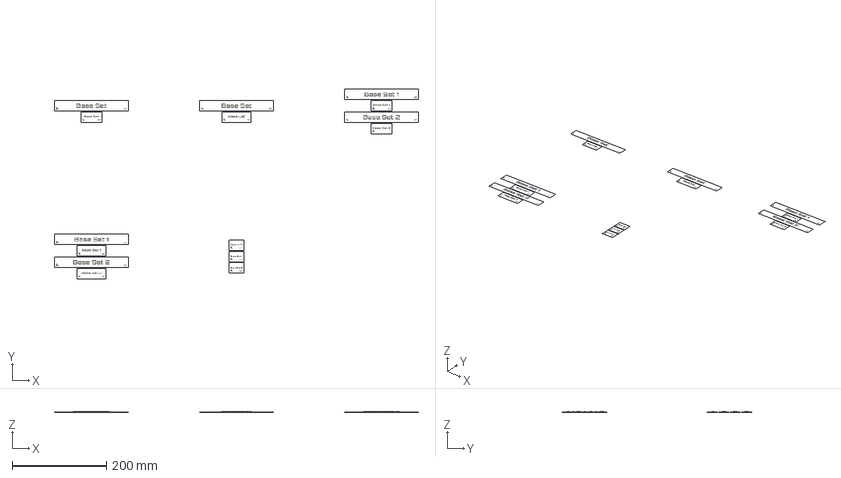
[picture p224: CAD file, 2026-08-16]
cascades/Dominion/labels/Base Set Labels.3mf
770.8 x 402.0 x 1.20 mm
Base_Set_156.4mm x 2
Base_Set_45mm
Base_Set_62mm
Base_Set_1_156.4mm x 2
Base_Set_1_45mm
Base_Set_2_156.4mm x 2
Base_Set_2_45mm
Base_Set_1_62mm
Base_Set_2_62mm
Base_Set_32mm
Base_Set_1_32mm
Base_Set_2_32mm
