amertner/cardcascade/cascades/FCM/FCM Occ 1S (264 Card M4-18-12-45-Sl).3mf

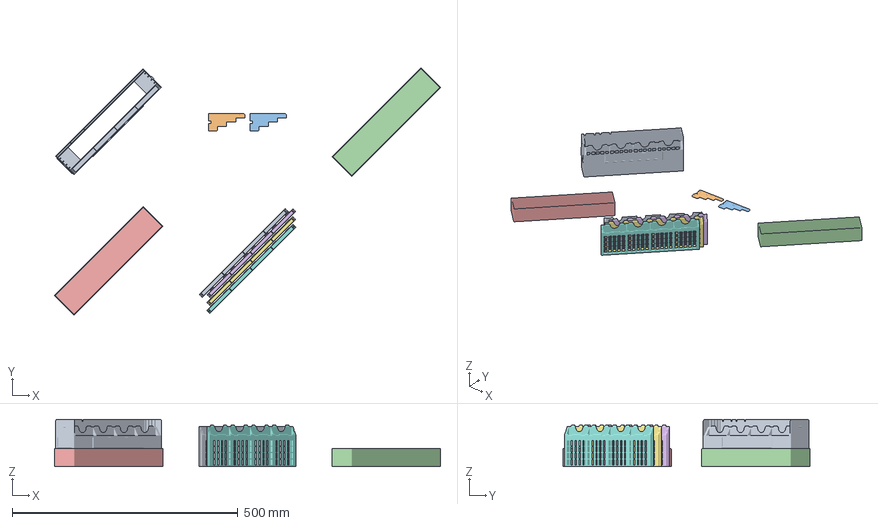
[picture p225: CAD file, 2026-09-14]
cascades/FCM/FCM Occ 1S (264 Card M4-18-12-45-Sl).3mf
854.6 x 547.4 x 105.0 mm
Pusher x 2
Lid 264S
Lid 264S Unmarked
Holder x 3
RearHolder
