amertner/cardcascade/cascades/Innovation/Innovation 4 Later Ages 5 Expansions Unsleeved (M5.10.10.32-Un).3mf

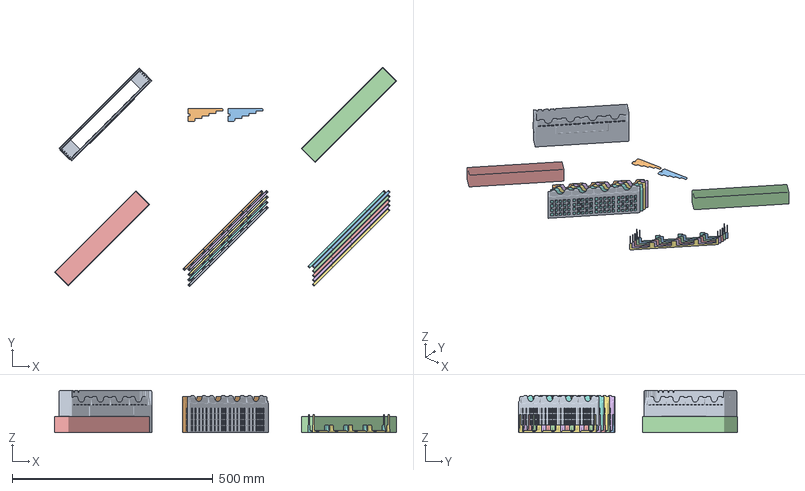
[picture p226: CAD file, 2026-09-14]
cascades/Innovation/Innovation 4 Later Ages 5 Expansions Unsleeved (M5.10.10.32-Un).3mf
850.9 x 545.7 x 105.0 mm
Pusher x 2
Lid 240U
Lid 240U Unmarked
Holder x 4
RearHolder
Topper Blank
Topper Artifacts
Topper Cities
Topper Echoes
Topper Figures
Topper Unseen
