amertner/cardcascade/cascades/Innovation/labels/Innovation 3-Age Cascades Labels.3mf

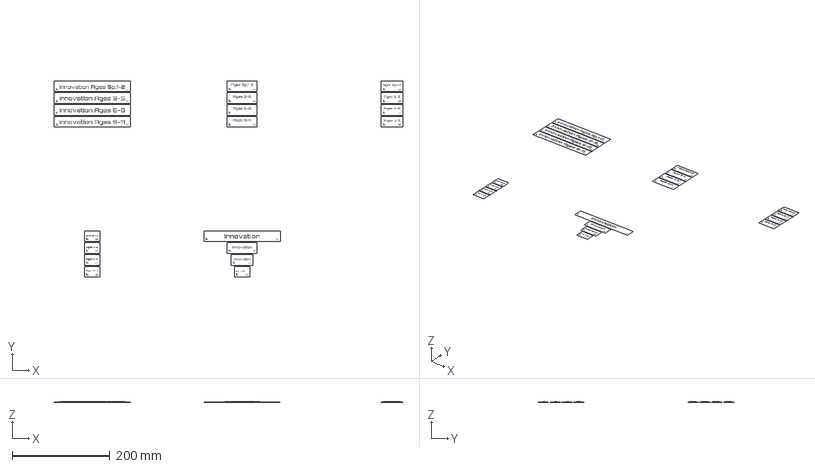
[picture p227: CAD file, 2026-08-31]
cascades/Innovation/labels/Innovation 3-Age Cascades Labels.3mf
715.1 x 402.0 x 1.20 mm
Innovation_Ages_Sp_1-2_156.4mm
Innovation_Ages_3-5_156.4mm
Innovation_Ages_6-8_156.4mm
Innovation_Ages_9-11_156.4mm
Ages_Sp_1-2_62mm
Ages_3-5_62mm
Ages_6-8_62mm
Ages_9-11_62mm
Ages_Sp_1-2_45mm
Ages_3-5_45mm
Ages_6-8_45mm
Ages_9-11_45mm
Ages_Sp_1-2_32mm
Ages_3-5_32mm
Ages_6-8_32mm
Ages_9-11_32mm
Innovation_156.4mm
Innovation_62mm
Innovation_45mm
Innovation_32mm
