amertner/cardcascade/cascades/MiniCards/Mini Cards 350 Card Sleeved (86-L6.10.10.45-Sl).3mf

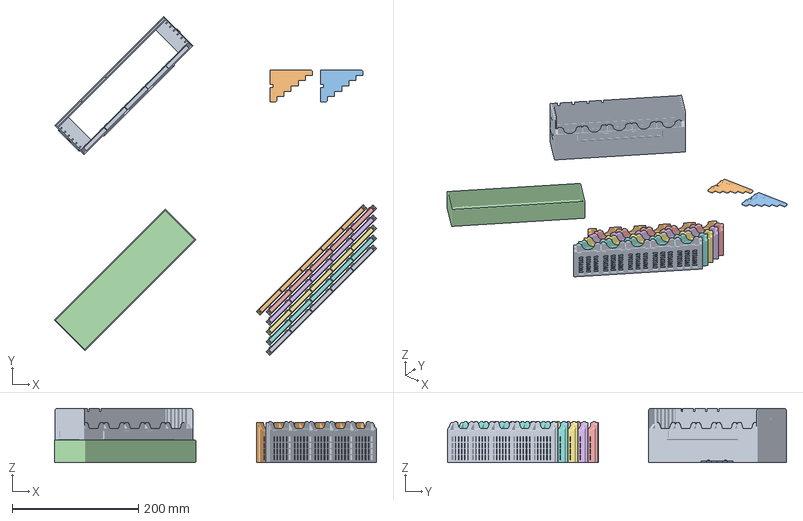
[picture p228: CAD file, 2026-09-22]
cascades/MiniCards/Mini Cards 350 Card Sleeved (86-L6.10.10.45-Sl).3mf
510.6 x 537.0 x 86.0 mm
Pusher x 2
Lid 350S Unmarked
Holder x 5
RearHolder
