amertner/cardcascade/individual/Compile/Lid S4.7.7.32-Sl.3mf

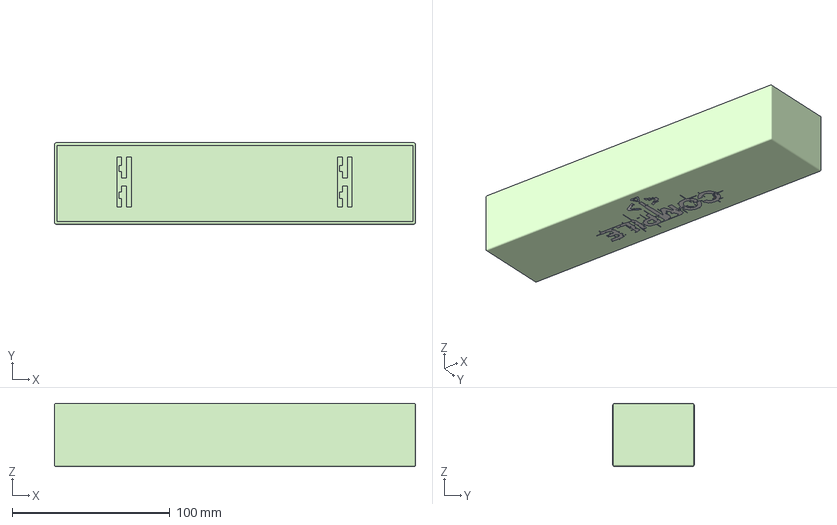
[picture p229: CAD file, 2026-09-05]
individual/Compile/Lid S4.7.7.32-Sl.3mf
228.9 x 51.7 x 40.0 mm
Lid
