amertner/cardcascade/individual/Dominion/Box S2.40.12-30.45-Sl.3mf

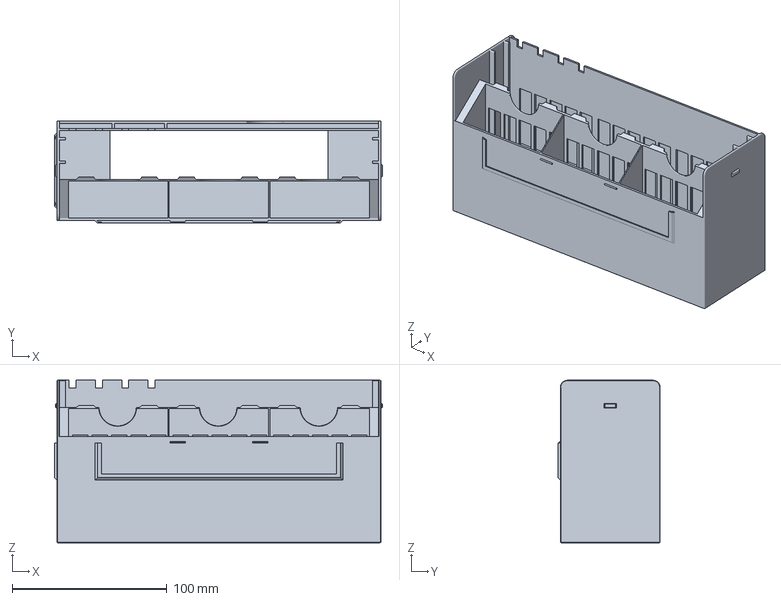
[picture p230: CAD file, 2026-09-05]
individual/Dominion/Box S2.40.12-30.45-Sl.3mf
211.9 x 66.1 x 105.0 mm
