amertner/cardcascade/individual/FCM/Lid M4.18.12.45-Sl.3mf

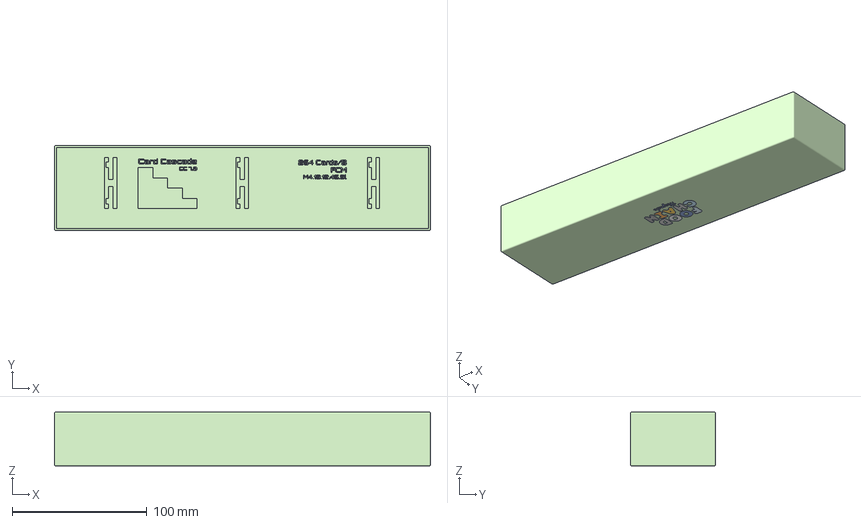
[picture p231: CAD file, 2026-09-05]
individual/FCM/Lid M4.18.12.45-Sl.3mf
278.9 x 63.3 x 40.0 mm
Lid
