amertner/cardcascade/individual/Innovation/Box M5.15.15.45-Un.3mf

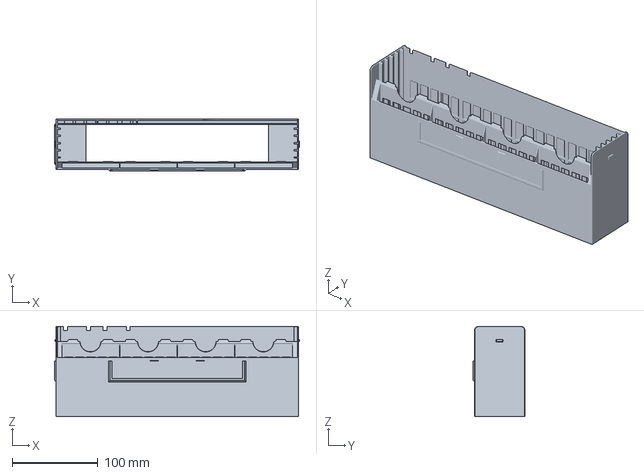
[picture p232: CAD file, 2026-09-03]
individual/Innovation/Box M5.15.15.45-Un.3mf
284.9 x 60.1 x 105.0 mm
