amertner/cardcascade/logos/Compile/Compile.dxf

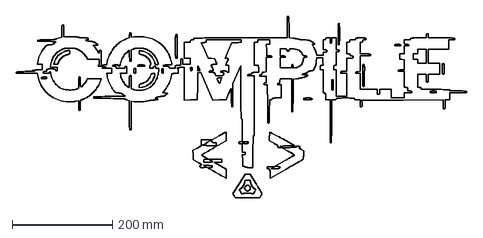
[picture p233: CAD file, 2026-07-10]
logos/Compile/Compile.dxf
899.9 x 362.0 mm
