amertner/cardcascade/logos/Innovation/lid_logo.dxf

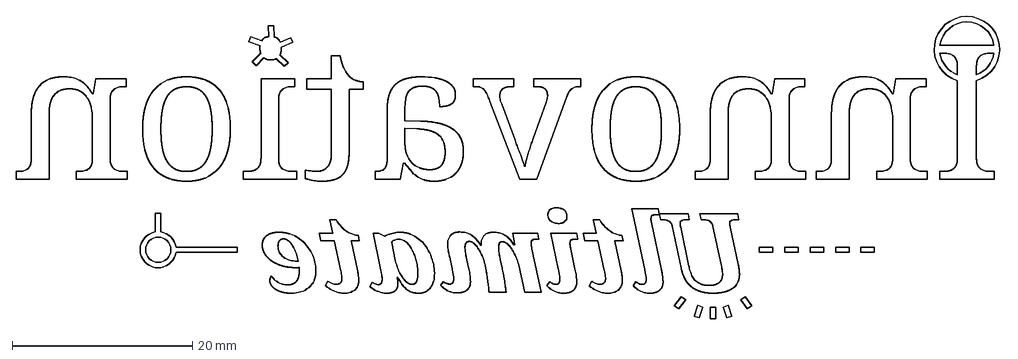
[picture p234: CAD file, 2026-09-02]
logos/Innovation/lid_logo.dxf
109.3 x 33.5 mm
