amertner/cardcascade/spec/reference/Box Innovation S5.15.15.62-Sl without label holders.step

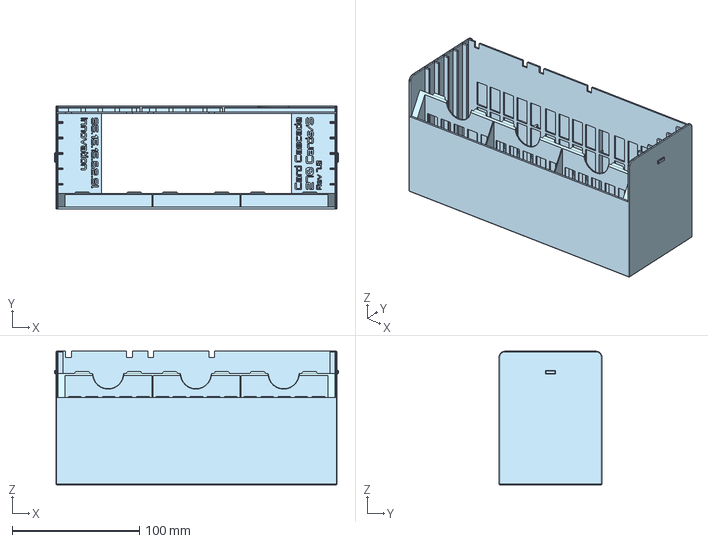
[picture p235: CAD file, 2026-09-04]
spec/reference/Box Innovation S5.15.15.62-Sl without label holders.step
223.3 x 81.0 x 105.0 mm
