amertner/cardcascade/spec/reference/shipped-7.0/Compile/Compile 105 Card Sleeved (S4.7.7.32-Sl).3mf

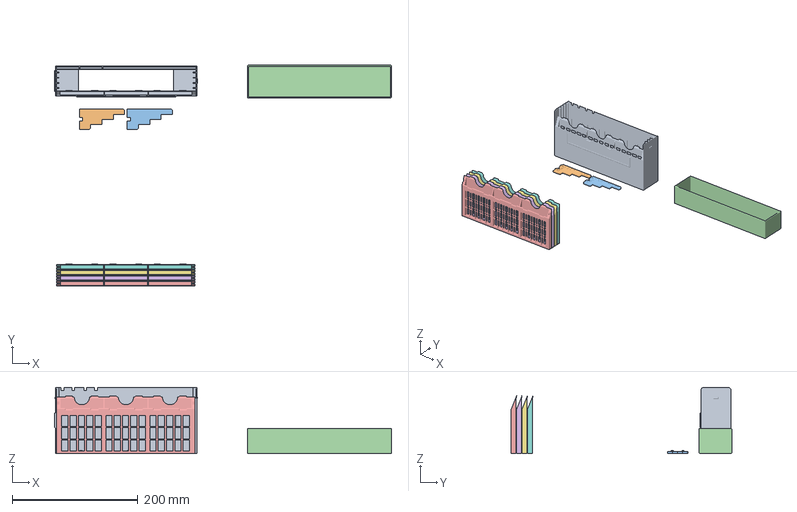
[picture p236: CAD file, 2026-09-05]
spec/reference/shipped-7.0/Compile/Compile 105 Card Sleeved (S4.7.7.32-Sl).3mf
535.1 x 350.1 x 105.0 mm
Pusher x 2
Lid 105S
Holder x 4
