amertner/cardcascade/spec/reference/shipped-7.0/Dominion/Dominion 168 Card Unsleeved (S4.16.10.32-Un).3mf

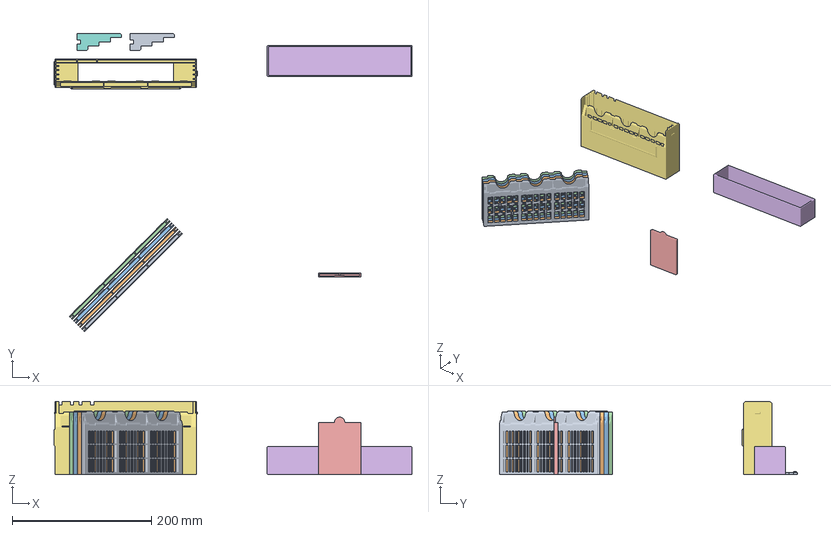
[picture p237: CAD file, 2026-09-05]
spec/reference/shipped-7.0/Dominion/Dominion 168 Card Unsleeved (S4.16.10.32-Un).3mf
514.1 x 428.5 x 105.0 mm
Holder x 4
TokenHolder
Lid 168U
Pusher x 2
