amertner/cardcascade/spec/reference/shipped-7.0/FCM/FCM Alt U (198 Card S4-18-12-32-Un).3mf

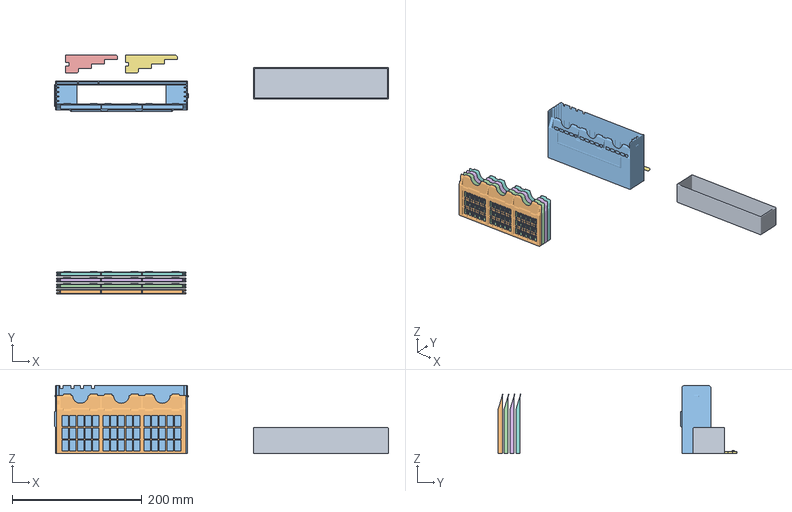
[picture p238: CAD file, 2026-09-05]
spec/reference/shipped-7.0/FCM/FCM Alt U (198 Card S4-18-12-32-Un).3mf
514.1 x 367.8 x 105.0 mm
Lid 198U
Holder x 4
Pusher x 2
