amertner/cardcascade/spec/reference/shipped-7.0/Innovation/Innovation 4 Later Ages 5 Expansions Unsleeved (M5.10.10.32-Un).3mf

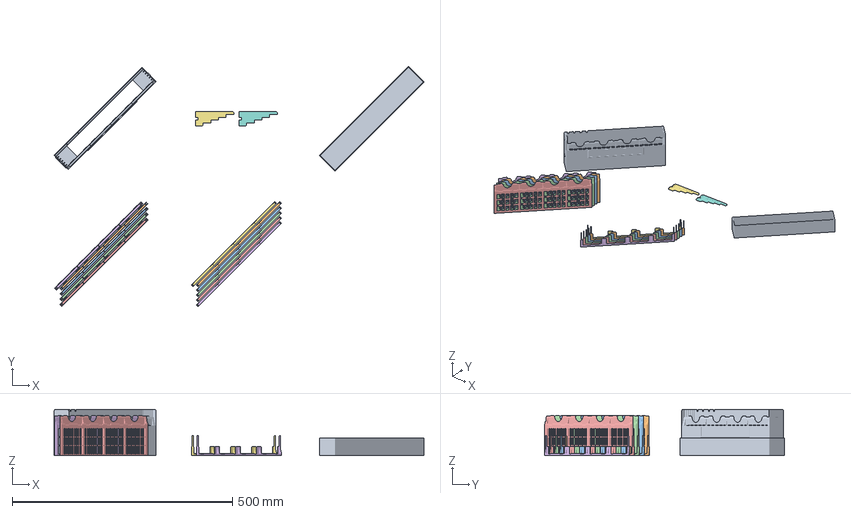
[picture p239: CAD file, 2026-09-03]
spec/reference/shipped-7.0/Innovation/Innovation 4 Later Ages 5 Expansions Unsleeved (M5.10.10.32-Un).3mf
840.3 x 545.1 x 105.0 mm
Holder x 5
Pusher x 2
Lid 240U
Topper Blank M10-Un
Topper Echoes M10-Un
Topper Artifacts M10-Un
Topper Cities M10-Un
Topper Figures M10-Un
Topper Unseen M10-Un
