amertner/cardcascade/cascades/Compile/Compile 105 Card Sleeved (S4.7.7.32-Sl).3mf

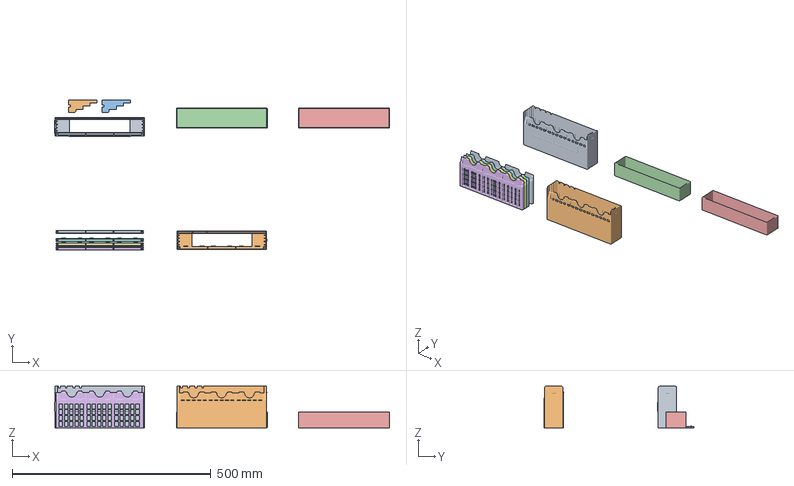
[picture p240: CAD file, 2026-09-14]
cascades/Compile/Compile 105 Card Sleeved (S4.7.7.32-Sl).3mf
842.3 x 378.4 x 105.0 mm
Pusher x 2
Lid 105S
Lid 105S Unmarked
Holder x 3
RearHolder
PlainBox
