amertner/cardcascade/cascades/Dominion/Dominion 244 Card Unsleeved (M4.21.10.32-Un).3mf

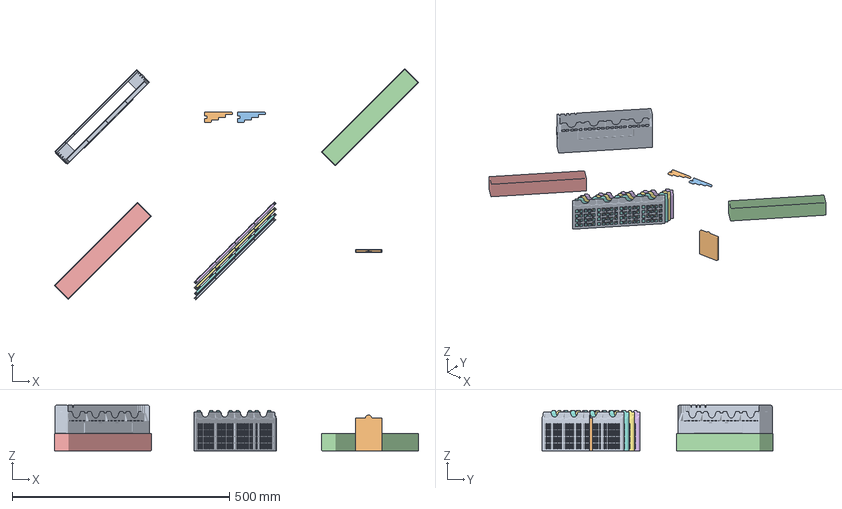
[picture p241: CAD file, 2026-09-14]
cascades/Dominion/Dominion 244 Card Unsleeved (M4.21.10.32-Un).3mf
837.3 x 532.1 x 105.0 mm
Pusher x 2
Lid 244U
Lid 244U Unmarked
Holder x 3
RearHolder
TokenHolder
