amertner/cardcascade/cascades/Dominion/labels/Dark Ages Labels.3mf

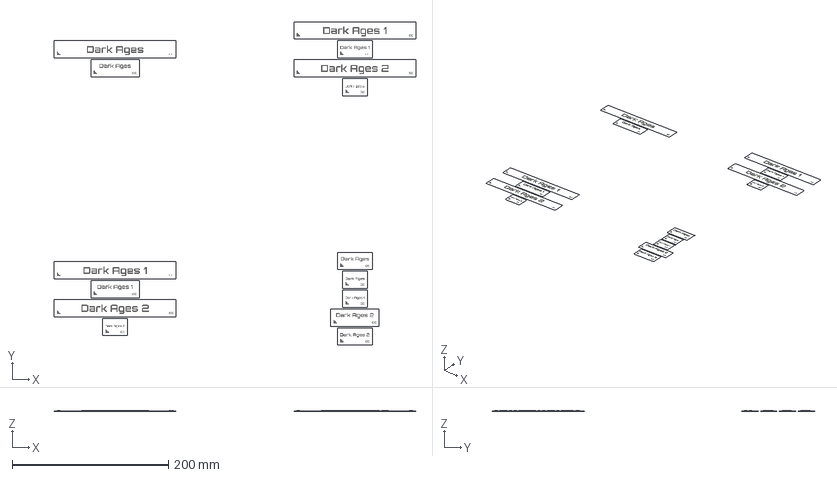
[picture p242: CAD file, 2026-08-16]
cascades/Dominion/labels/Dark Ages Labels.3mf
463.6 x 414.1 x 1.20 mm
Dark_Ages_156.4mm
Dark_Ages_62mm
Dark_Ages_1_156.4mm x 2
Dark_Ages_1_45mm
Dark_Ages_2_156.4mm x 2
Dark_Ages_2_32mm x 2
Dark_Ages_1_62mm
Dark_Ages_45mm
Dark_Ages_32mm
Dark_Ages_1_32mm
Dark_Ages_2_62mm
Dark_Ages_2_45mm
