amertner/cardcascade/cascades/FCM/FCM Occ 2U (180 Card L3-18-6-20-Un).3mf

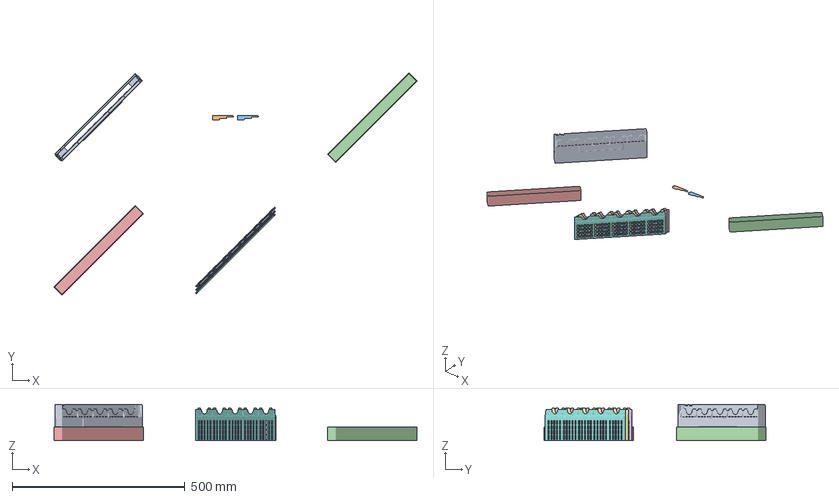
[picture p243: CAD file, 2026-09-14]
cascades/FCM/FCM Occ 2U (180 Card L3-18-6-20-Un).3mf
1051.0 x 643.0 x 105.0 mm
Pusher x 2
Lid 180U
Lid 180U Unmarked
Holder x 2
RearHolder
