amertner/cardcascade/cascades/Innovation/Innovation Single Set Sleeved (S3.15.10.32-Sl).3mf

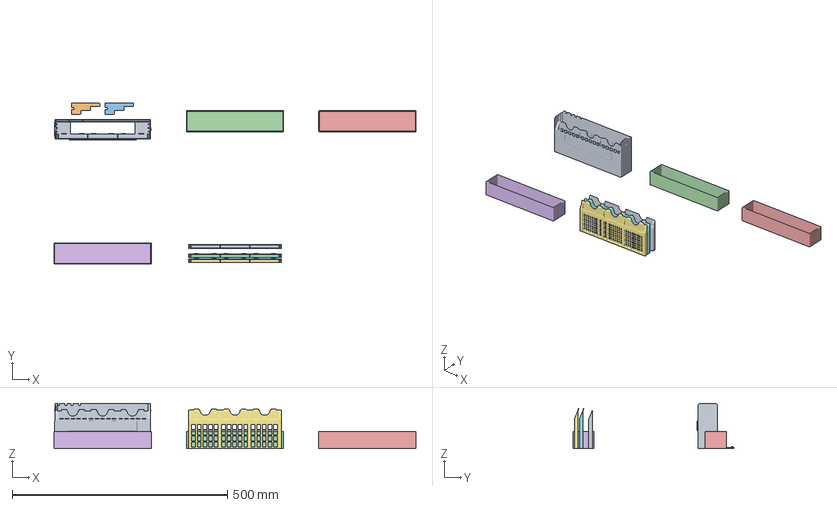
[picture p244: CAD file, 2026-09-14]
cascades/Innovation/Innovation Single Set Sleeved (S3.15.10.32-Sl).3mf
840.3 x 374.7 x 105.0 mm
Pusher x 2
Lid 135S
Lid 135S Ultimate
Lid 135S Unmarked
Holder x 2
RearHolder
