amertner/cardcascade/cascades/Innovation/labels/Innovation 4-Age Cascades Labels.3mf

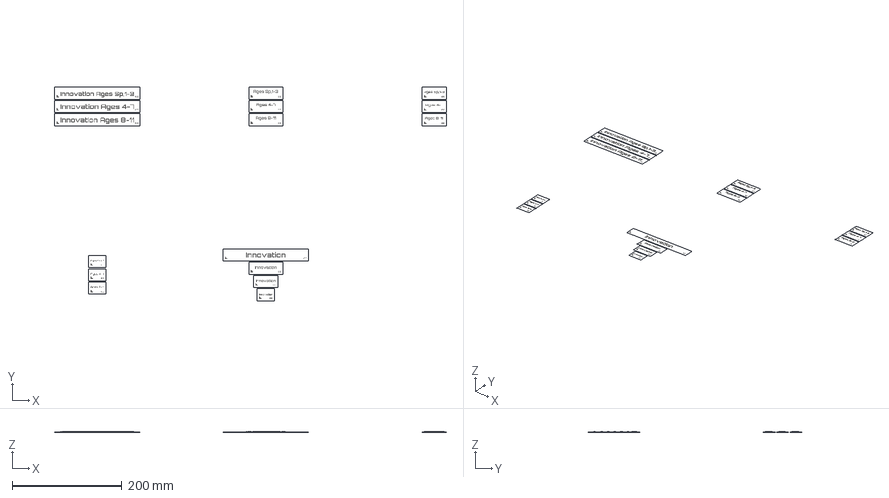
[picture p245: CAD file, 2026-08-31]
cascades/Innovation/labels/Innovation 4-Age Cascades Labels.3mf
715.1 x 389.9 x 1.20 mm
Innovation_Ages_Sp_1-3_156.4mm
Innovation_Ages_4-7_156.4mm
Innovation_Ages_8-11_156.4mm
Ages_Sp_1-3_62mm
Ages_4-7_62mm
Ages_8-11_62mm
Ages_Sp_1-3_45mm
Ages_4-7_45mm
Ages_8-11_45mm
Ages_Sp_1-3_32mm
Ages_4-7_32mm
Ages_8-11_32mm
Innovation_156.4mm
Innovation_62mm
Innovation_45mm
Innovation_32mm
