amertner/cardcascade/cascades/MiniCards/Mini Cards 120 Card Sleeved (86-XS5.10.10.45-Sl).3mf

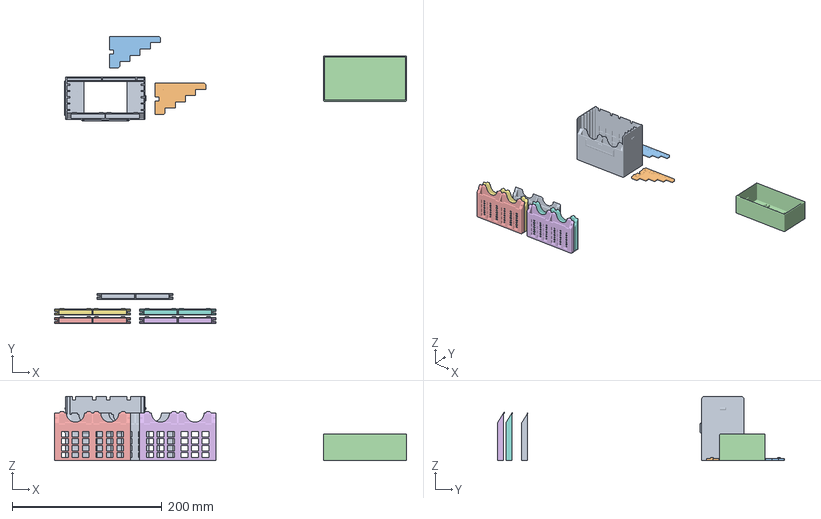
[picture p246: CAD file, 2026-09-22]
cascades/MiniCards/Mini Cards 120 Card Sleeved (86-XS5.10.10.45-Sl).3mf
470.4 x 383.8 x 86.0 mm
Pusher x 2
Lid 120S Unmarked
Holder x 4
RearHolder
