amertner/cardcascade/individual/Compile/Pusher 4x7-Sl.3mf

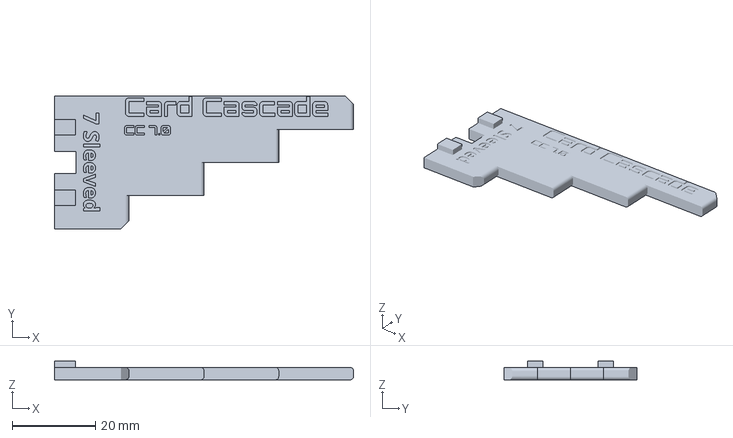
[picture p247: CAD file, 2026-09-05]
individual/Compile/Pusher 4x7-Sl.3mf
72.0 x 32.0 x 4.50 mm
