amertner/cardcascade/individual/Dominion/Pusher 2x12-Sl.3mf

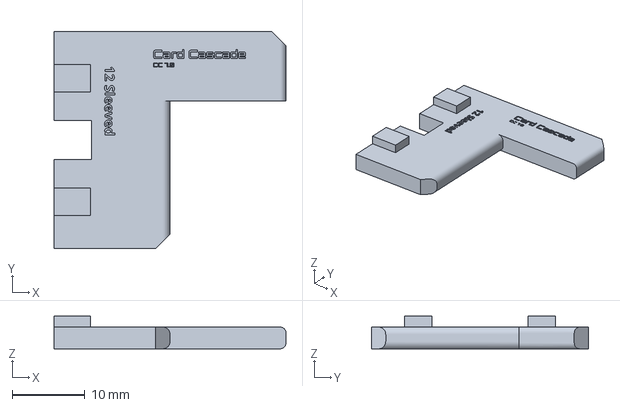
[picture p248: CAD file, 2026-09-05]
individual/Dominion/Pusher 2x12-Sl.3mf
32.0 x 30.0 x 4.50 mm
