amertner/cardcascade/individual/FCM/Pusher 4x12-Un.3mf

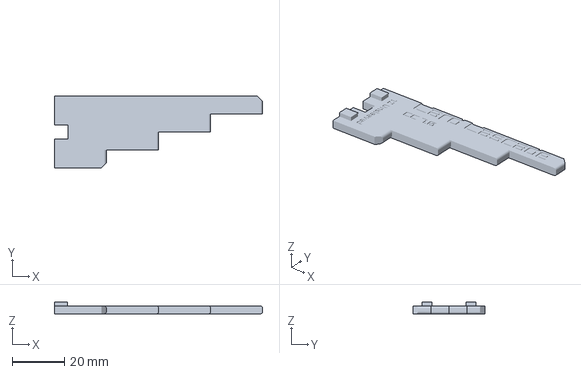
[picture p249: CAD file, 2026-09-05]
individual/FCM/Pusher 4x12-Un.3mf
80.0 x 27.8 x 4.50 mm
