amertner/cardcascade/individual/Innovation/Box M5.10.10.32-Un.3mf

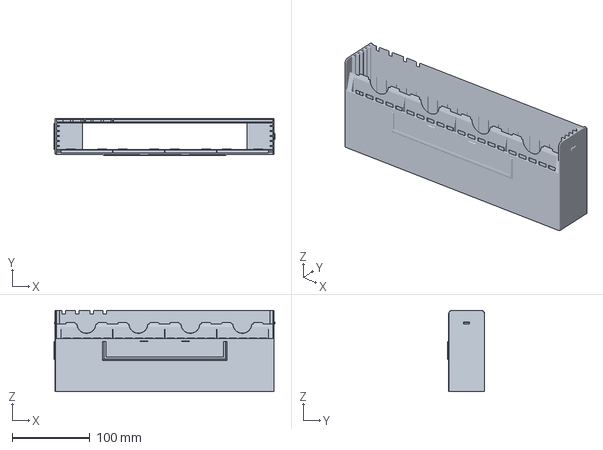
[picture p250: CAD file, 2026-09-03]
individual/Innovation/Box M5.10.10.32-Un.3mf
284.9 x 48.1 x 105.0 mm
