amertner/cardcascade/spec/reference/shipped-7.0/Compile/Compile 126 Card Unsleeved (S5.7.7.20-Un).3mf

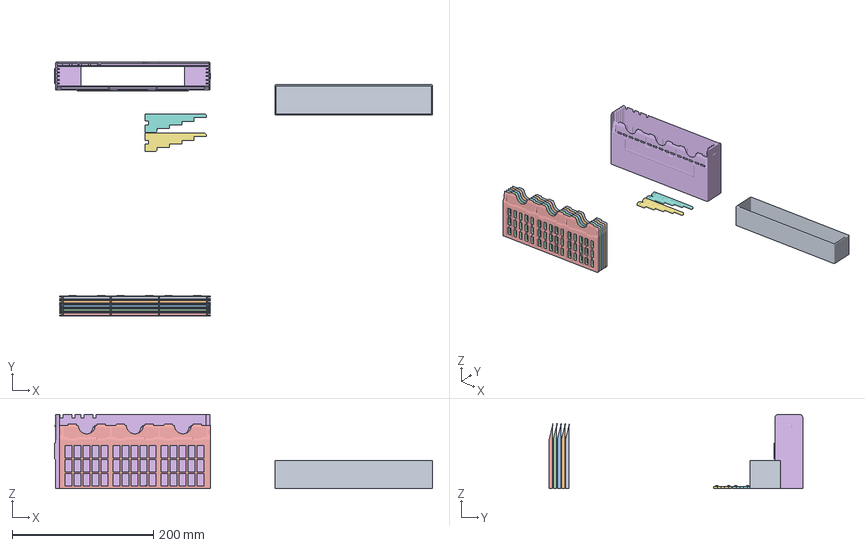
[picture p251: CAD file, 2026-08-31]
spec/reference/shipped-7.0/Compile/Compile 126 Card Unsleeved (S5.7.7.20-Un).3mf
534.9 x 358.9 x 105.0 mm
Holder x 5
Pusher x 2
Lid CmpU
