amertner/cardcascade/spec/reference/shipped-7.0/Dominion/Dominion 202 Card (Mat) Unsleeved (M4.21.10.32-Un).3mf

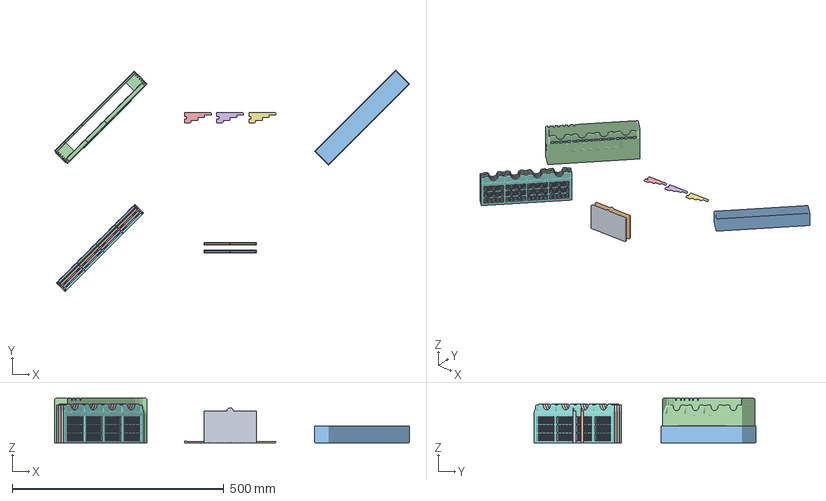
[picture p252: CAD file, 2026-09-05]
spec/reference/shipped-7.0/Dominion/Dominion 202 Card (Mat) Unsleeved (M4.21.10.32-Un).3mf
837.3 x 522.6 x 105.0 mm
TokenHolder Full
TokenHolder Half
Lid 202U
Pusher x 3
Holder x 4
