amertner/cardcascade/spec/reference/shipped-7.0/FCM/FCM Milestones 1S (144 Card M5-6-6-32-Sl).3mf

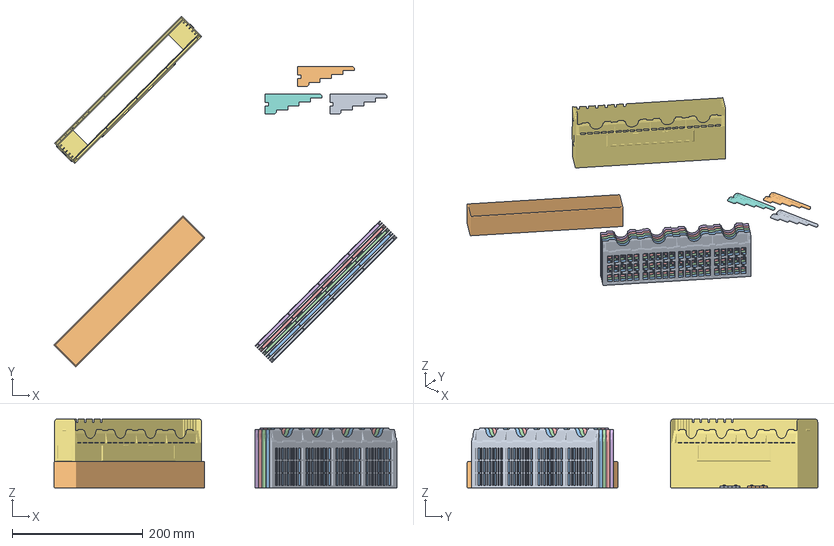
[picture p253: CAD file, 2026-09-05]
spec/reference/shipped-7.0/FCM/FCM Milestones 1S (144 Card M5-6-6-32-Sl).3mf
523.9 x 535.4 x 105.0 mm
Holder x 5
Lid 144S
Pusher x 3
