amertner/cardcascade/spec/reference/shipped-7.0/Innovation/Innovation 3 Later Ages 5 Expansions Unsleeved (S5.10.10.32-Un).3mf

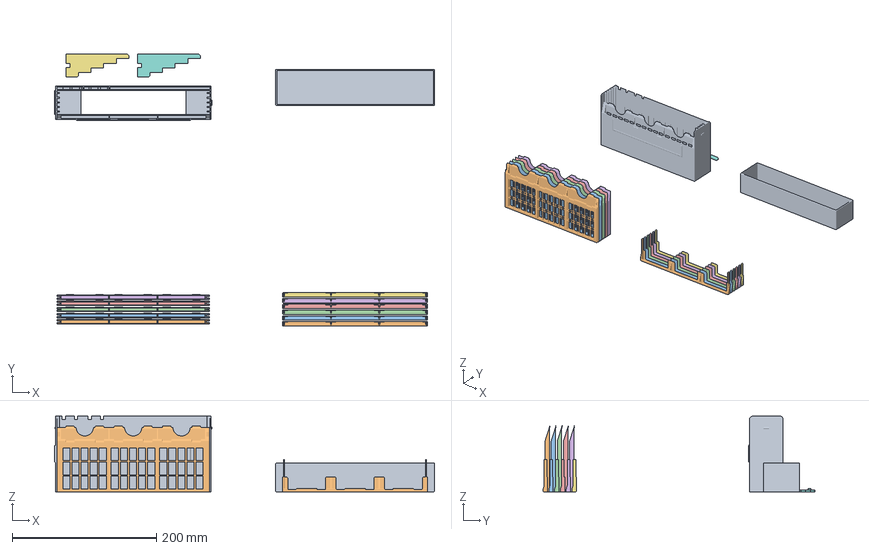
[picture p254: CAD file, 2026-09-03]
spec/reference/shipped-7.0/Innovation/Innovation 3 Later Ages 5 Expansions Unsleeved (S5.10.10.32-Un).3mf
526.1 x 376.2 x 105.0 mm
Holder x 5
Pusher x 2
Lid 180U
Topper Blank S10-Un
Topper Echoes S10-Un
Topper Artifacts S10-Un
Topper Cities S10-Un
Topper Figures S10-Un
Topper Unseen S10-Un
