amertner/cardcascade/spec/reference/Topper Cities S5.15.15.62-Sl.step

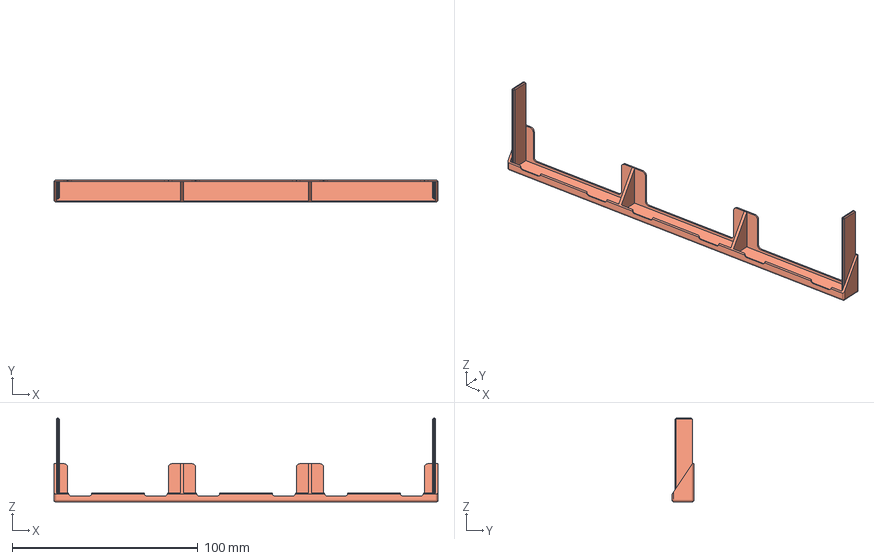
[picture p255: CAD file, 2026-09-04]
spec/reference/Topper Cities S5.15.15.62-Sl.step
207.0 x 11.8 x 45.2 mm
