amertner/cardcascade/cascades/Compile/Compile 210 Card Sleeved (L5.7.7.45-Sl).3mf

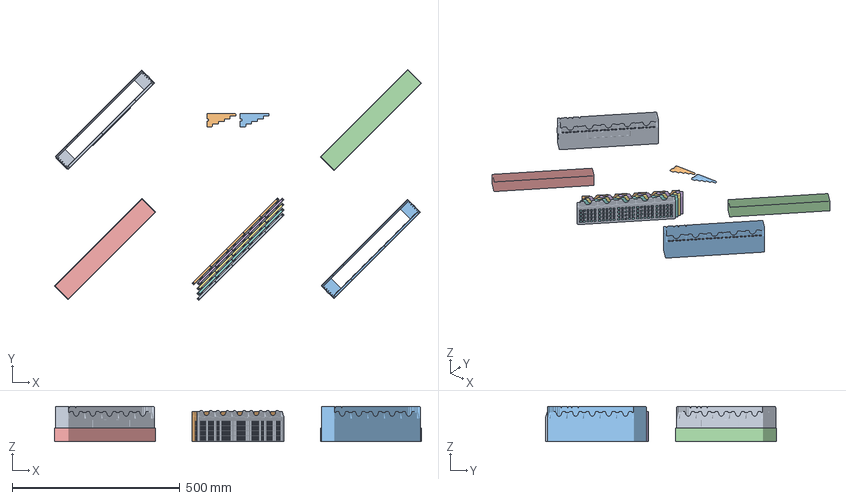
[picture p256: CAD file, 2026-09-14]
cascades/Compile/Compile 210 Card Sleeved (L5.7.7.45-Sl).3mf
1093.2 x 687.9 x 105.0 mm
Pusher x 2
Lid 210S
Lid 210S Unmarked
Holder x 4
RearHolder
PlainBox
