amertner/cardcascade/cascades/Dominion/Dominion 300 Card Unsleeved (S5.40.12.45-Un).3mf

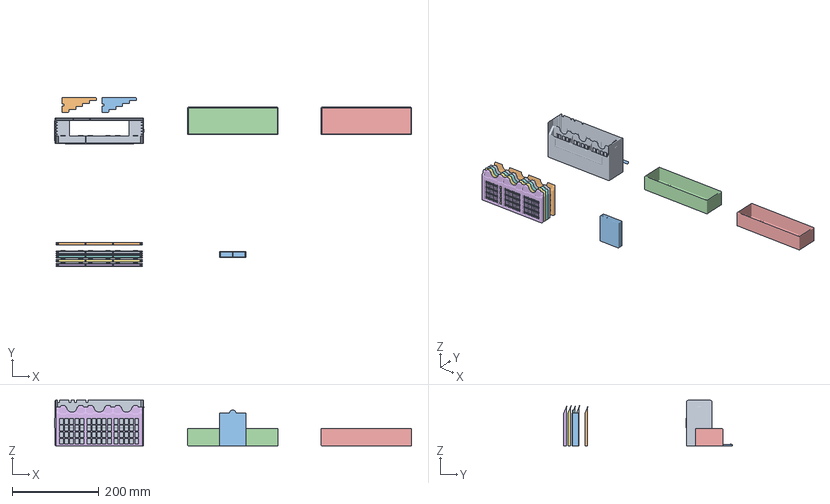
[picture p257: CAD file, 2026-09-14]
cascades/Dominion/Dominion 300 Card Unsleeved (S5.40.12.45-Un).3mf
821.3 x 388.8 x 105.0 mm
Pusher x 2
Lid 300U
Lid 300U Unmarked
Holder x 4
RearHolder
TokenHolder
