amertner/cardcascade/cascades/Dominion/labels/Prosperity Labels.3mf

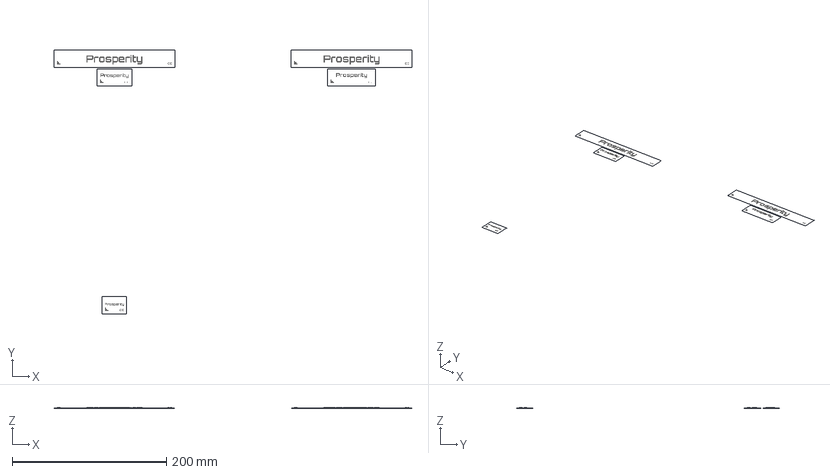
[picture p258: CAD file, 2026-08-16]
cascades/Dominion/labels/Prosperity Labels.3mf
463.6 x 341.5 x 1.20 mm
Prosperity_156.4mm x 2
Prosperity_45mm
Prosperity_62mm
Prosperity_32mm
