amertner/cardcascade/cascades/FCM/FCM Milestones 1S (144 Card M5-6-6-32-Sl).3mf

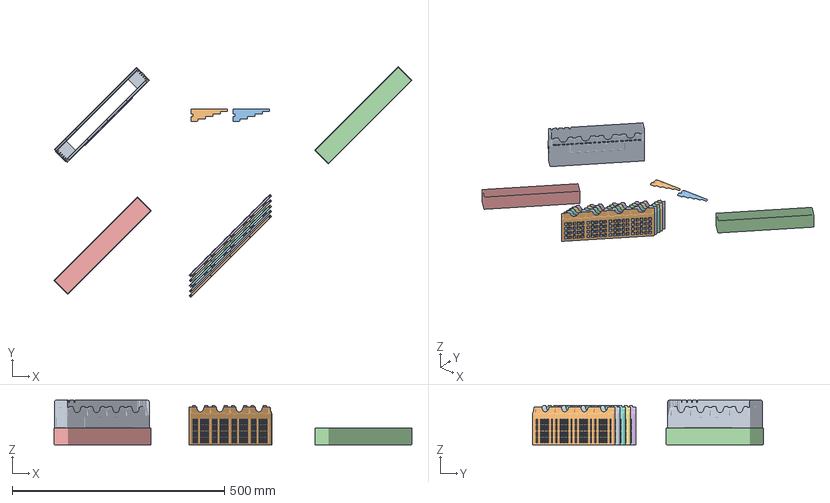
[picture p259: CAD file, 2026-09-14]
cascades/FCM/FCM Milestones 1S (144 Card M5-6-6-32-Sl).3mf
843.5 x 543.8 x 105.0 mm
Pusher x 2
Lid 144S
Lid 144S Unmarked
Holder x 4
RearHolder
