amertner/cardcascade/cascades/Innovation/Innovation Three Expansions Unsleeved (M8.16.10-16.45-Un).3mf

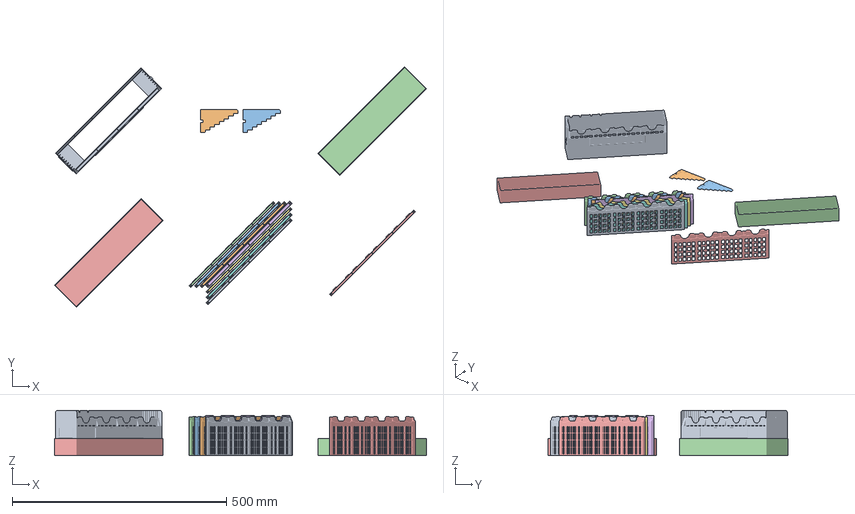
[picture p260: CAD file, 2026-09-14]
cascades/Innovation/Innovation Three Expansions Unsleeved (M8.16.10-16.45-Un).3mf
867.8 x 560.6 x 105.0 mm
Pusher x 2
Lid 408U
Lid 408U Unmarked
RearHolder
Holder x 7
