amertner/cardcascade/cascades/MiniCards/Mini Cards 216 Card Sleeved (86-S5.12.12.45-Sl).3mf

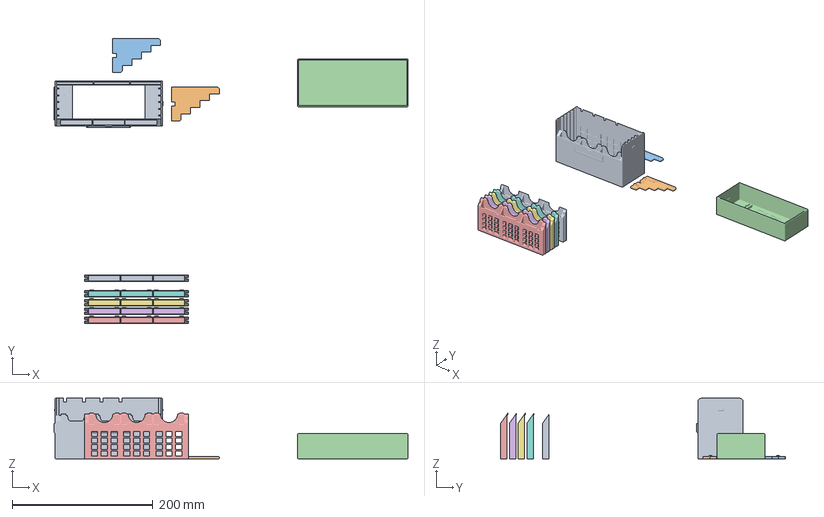
[picture p261: CAD file, 2026-09-22]
cascades/MiniCards/Mini Cards 216 Card Sleeved (86-S5.12.12.45-Sl).3mf
503.1 x 404.5 x 86.0 mm
Pusher x 2
Lid 216S Unmarked
Holder x 4
RearHolder
