amertner/cardcascade/individual/Compile/_raw/Lid S5.7.7.45-Sl.3mf

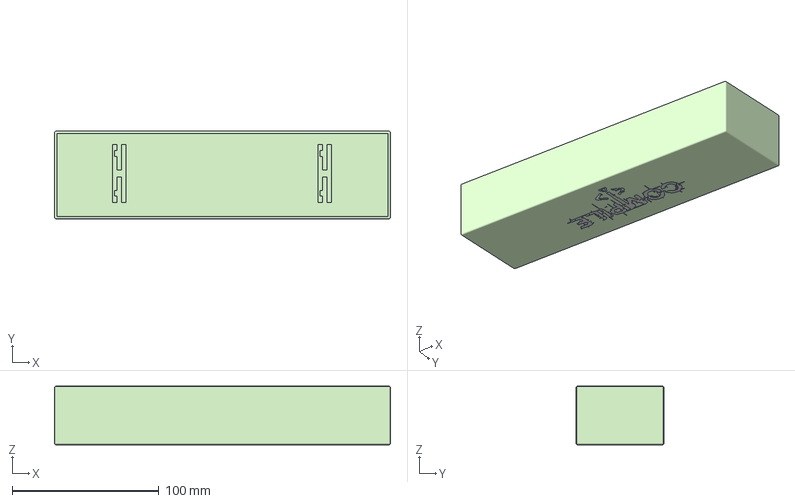
[picture p262: CAD file, 2026-08-31]
individual/Compile/_raw/Lid S5.7.7.45-Sl.3mf
228.9 x 59.7 x 40.0 mm
Lid
