amertner/cardcascade/individual/Compile/Lid L5.7.7.20-Un.3mf

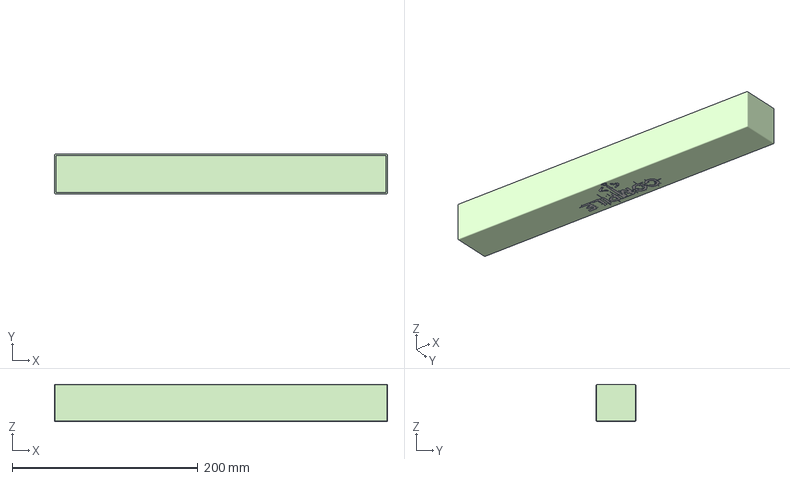
[picture p263: CAD file, 2026-09-05]
individual/Compile/Lid L5.7.7.20-Un.3mf
358.9 x 42.9 x 40.0 mm
Lid
