amertner/cardcascade/individual/Dominion/Lid S2.40.12-30.32-Un.3mf

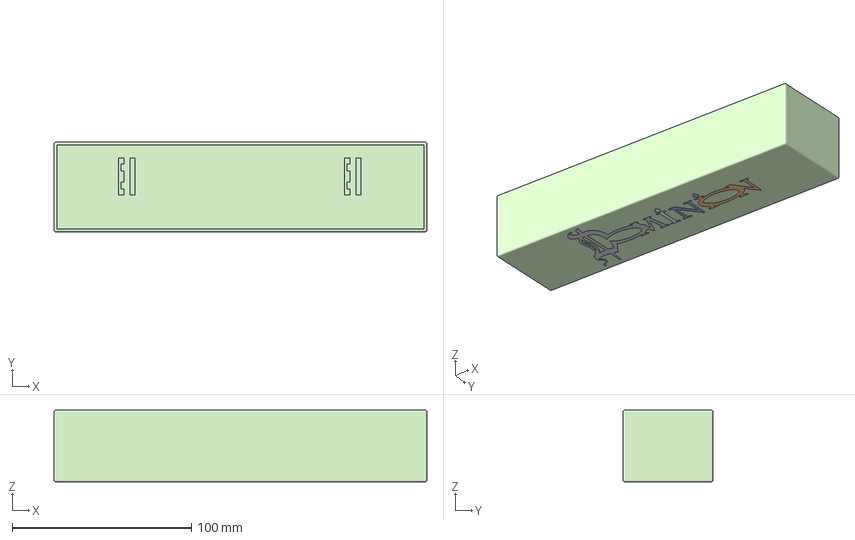
[picture p264: CAD file, 2026-09-05]
individual/Dominion/Lid S2.40.12-30.32-Un.3mf
207.9 x 50.1 x 40.0 mm
Lid
