amertner/cardcascade/individual/FCM/Box M4.18.12.45-Sl.3mf

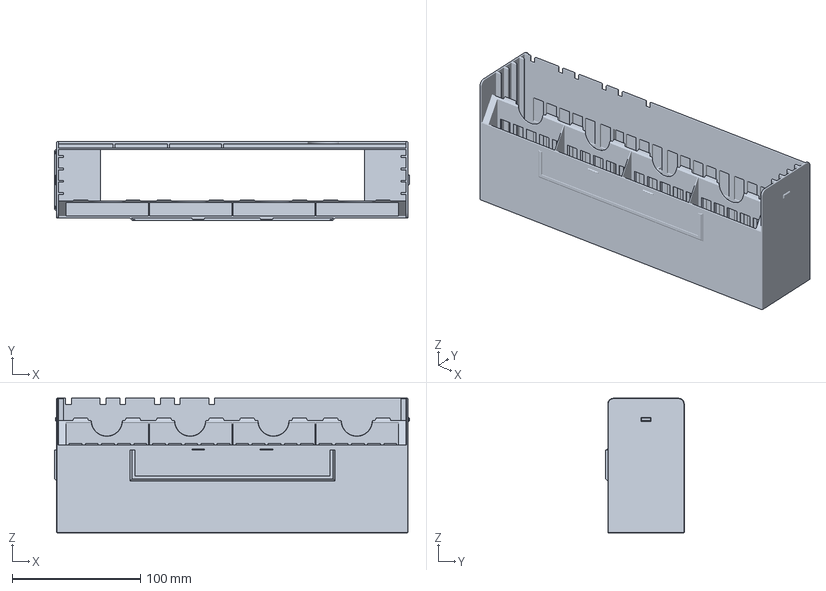
[picture p265: CAD file, 2026-09-05]
individual/FCM/Box M4.18.12.45-Sl.3mf
276.9 x 61.3 x 105.0 mm
