amertner/cardcascade/individual/Innovation/Lid S5.15.15.62-Sl.3mf

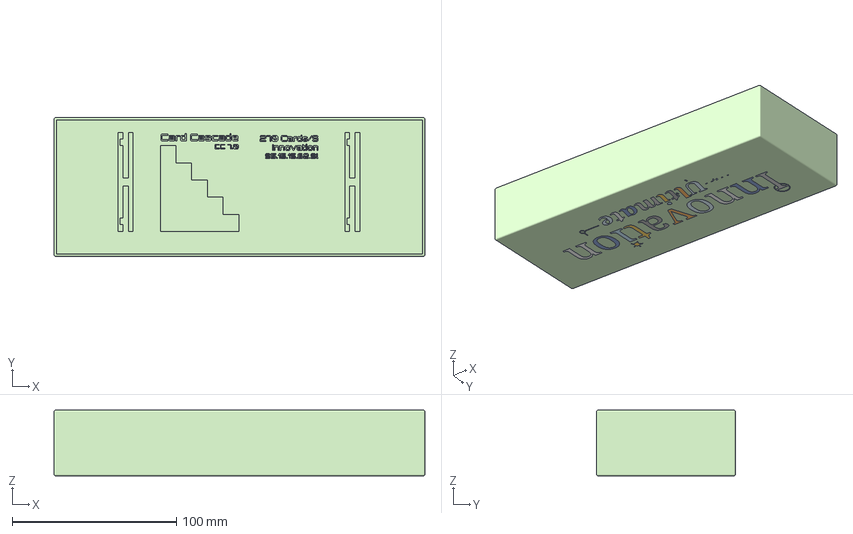
[picture p266: CAD file, 2026-09-03]
individual/Innovation/Lid S5.15.15.62-Sl.3mf
225.9 x 84.6 x 40.0 mm
Lid
