amertner/cardcascade/spec/reference/Lid Innovation M5.15.15.45-Un with logo.step

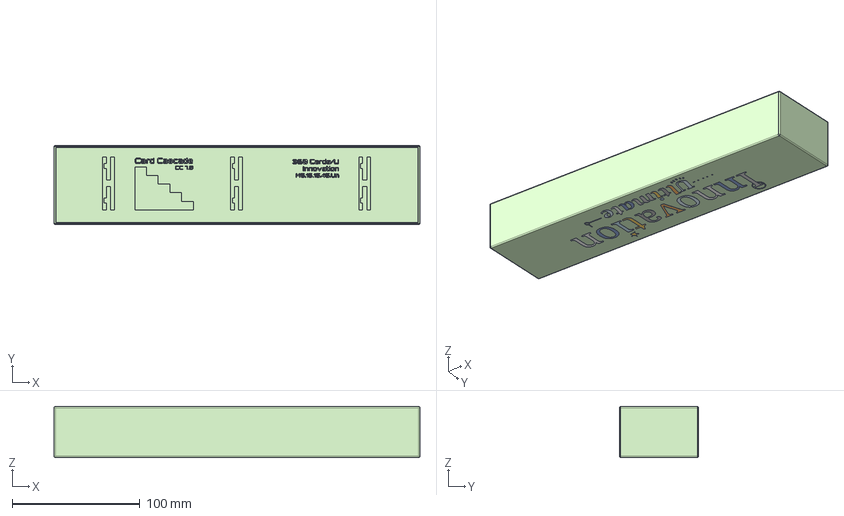
[picture p267: CAD file, 2026-09-04]
spec/reference/Lid Innovation M5.15.15.45-Un with logo.step
286.9 x 62.1 x 40.0 mm
