amertner/cardcascade/spec/reference/shipped-7.0/Compile/Compile 105 Card Unsleeved (S4.7.7.20-Un).3mf

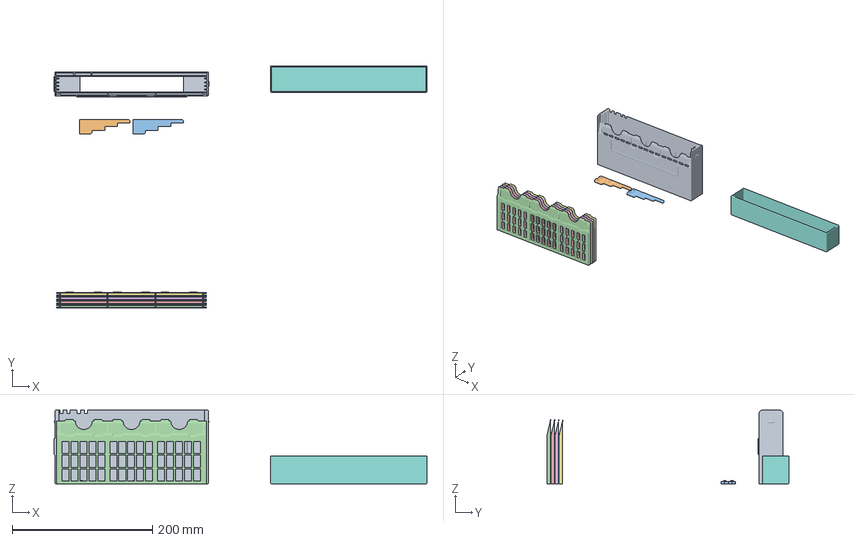
[picture p268: CAD file, 2026-08-31]
spec/reference/shipped-7.0/Compile/Compile 105 Card Unsleeved (S4.7.7.20-Un).3mf
531.5 x 345.1 x 105.0 mm
Pusher x 2
Holder x 4
Lid 105U
