amertner/cardcascade/spec/reference/shipped-7.0/Dominion/Dominion 324 Card Unsleeved (M6.21.10.45-Un).3mf

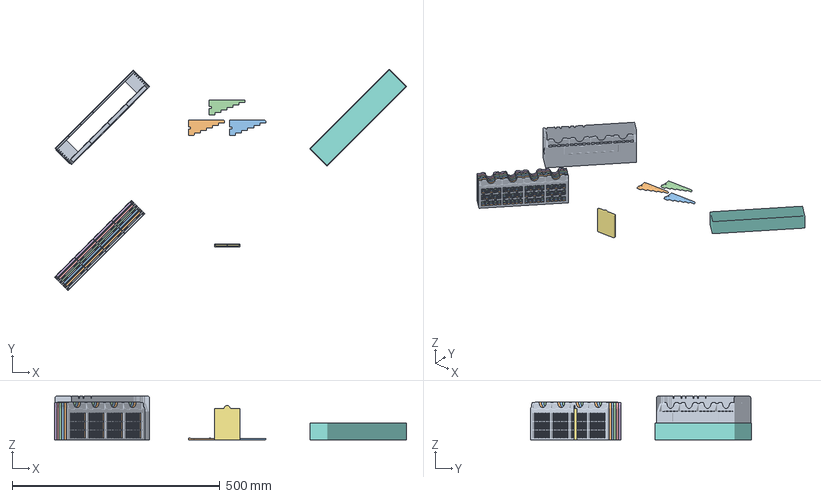
[picture p269: CAD file, 2026-09-05]
spec/reference/shipped-7.0/Dominion/Dominion 324 Card Unsleeved (M6.21.10.45-Un).3mf
847.5 x 532.6 x 105.0 mm
Holder x 6
TokenHolder
Lid 324U
Pusher x 3
