amertner/cardcascade/spec/reference/shipped-7.0/FCM/FCM Occ 1S (264 Card M4-18-12-45-Sl).3mf

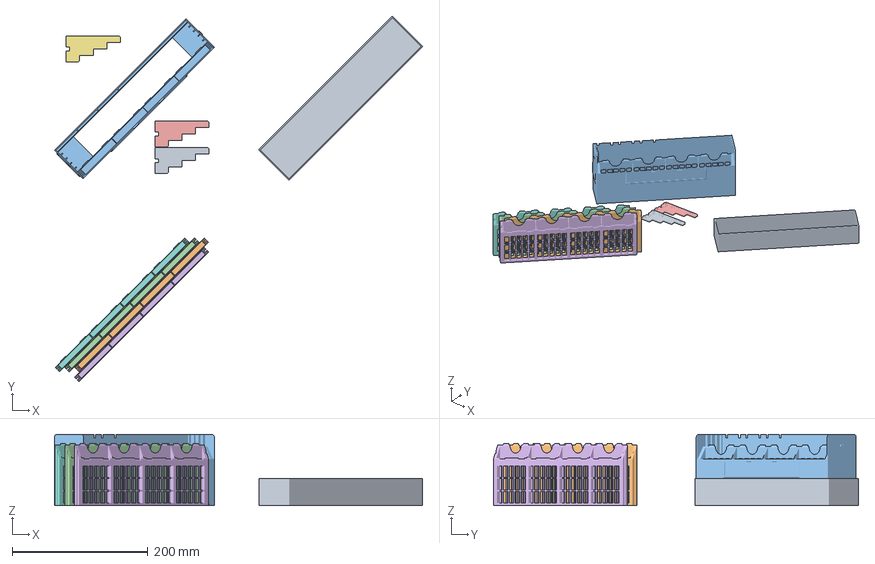
[picture p270: CAD file, 2026-09-05]
spec/reference/shipped-7.0/FCM/FCM Occ 1S (264 Card M4-18-12-45-Sl).3mf
542.3 x 538.3 x 105.0 mm
Lid 264S
Holder x 4
Pusher x 3
