amertner/cardcascade/spec/reference/shipped-7.0/Innovation/Innovation 3 Ages 5 Expansions Unsleeved (S5.15.15.45-Un).3mf

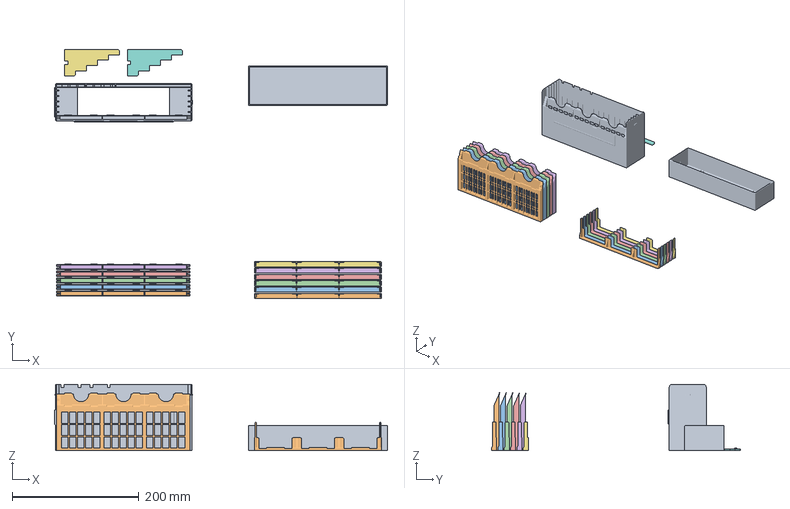
[picture p271: CAD file, 2026-09-03]
spec/reference/shipped-7.0/Innovation/Innovation 3 Ages 5 Expansions Unsleeved (S5.15.15.45-Un).3mf
526.1 x 393.2 x 105.0 mm
Holder x 5
Pusher x 2
Lid 270U
Topper
Topper Echoes S-Un
Topper Artifacts S-Un
Topper Cities S-Un
Topper Figures S-Un
Topper Unseen S-Un
