amertner/cardcascade/cascades/Compile/Compile 126 Card Unsleeved (S5.7.7.20-Un).3mf

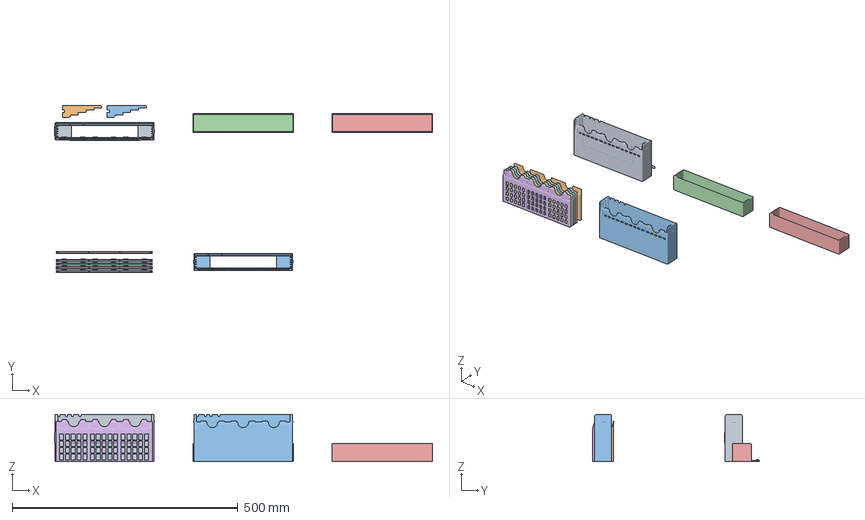
[picture p272: CAD file, 2026-09-14]
cascades/Compile/Compile 126 Card Unsleeved (S5.7.7.20-Un).3mf
836.3 x 369.4 x 105.0 mm
Pusher x 2
Lid 126U
Lid 126U Unmarked
Holder x 4
RearHolder
PlainBox
