amertner/cardcascade/cascades/Dominion/Dominion 290 Card (Mat) Sleeved (M6.21.10-12.0-Sl).3mf

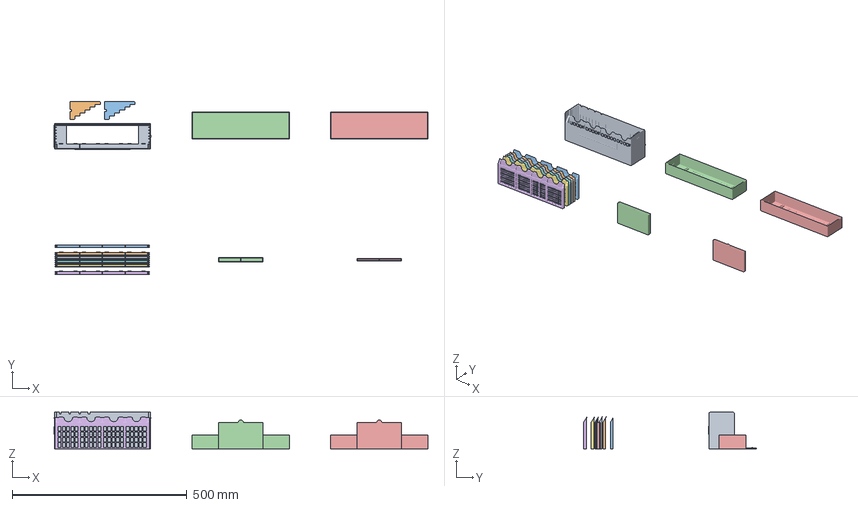
[picture p273: CAD file, 2026-09-14]
cascades/Dominion/Dominion 290 Card (Mat) Sleeved (M6.21.10-12.0-Sl).3mf
1069.9 x 495.8 x 105.0 mm
Pusher x 2
Lid 290S
Lid 290S Unmarked
FirstHolder
Holder x 4
RearHolder
TokenHolder
HalfTokenHolder
