amertner/cardcascade/cascades/Dominion/labels/Plunder Labels.3mf

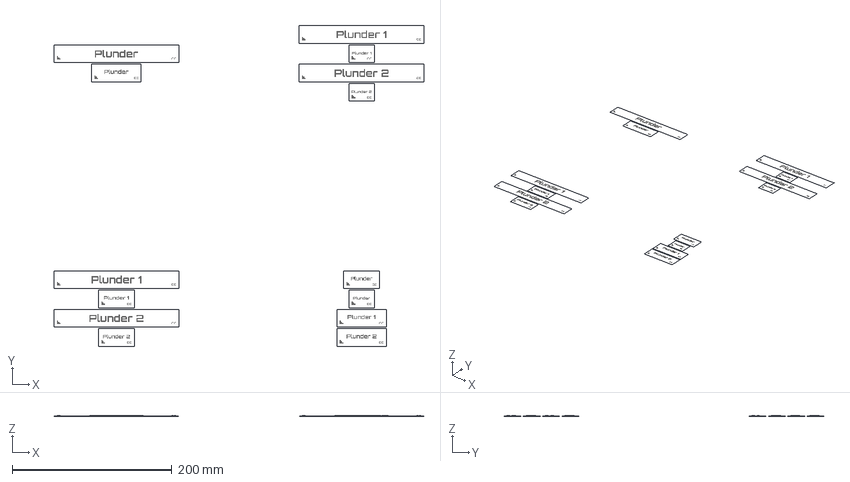
[picture p274: CAD file, 2026-08-16]
cascades/Dominion/labels/Plunder Labels.3mf
463.6 x 402.0 x 1.20 mm
Plunder_156.4mm
Plunder_62mm
Plunder_1_156.4mm x 2
Plunder_1_32mm
Plunder_2_156.4mm x 2
Plunder_2_32mm
Plunder_1_45mm
Plunder_2_45mm
Plunder_45mm
Plunder_32mm
Plunder_1_62mm
Plunder_2_62mm
