amertner/cardcascade/cascades/FCM/FCM Alt U (198 Card S4-18-12-32-Un).3mf

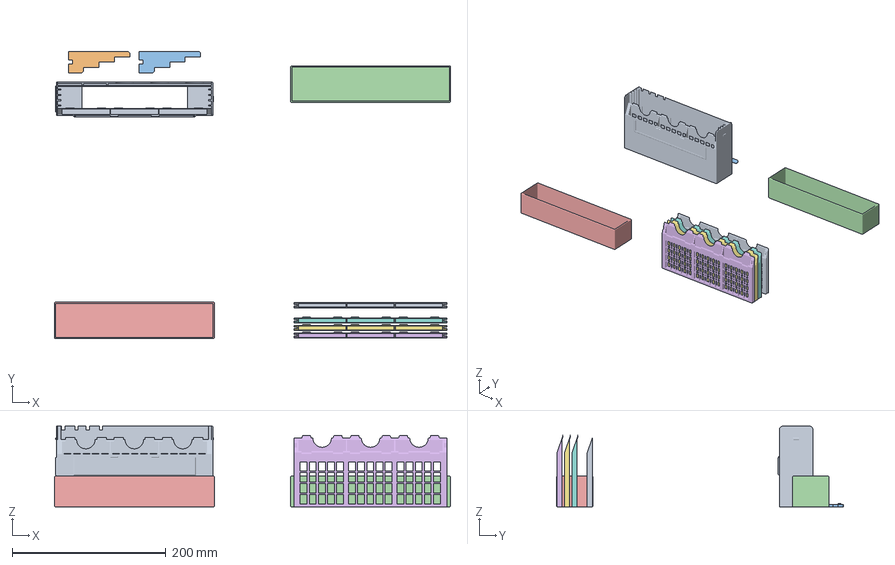
[picture p275: CAD file, 2026-09-14]
cascades/FCM/FCM Alt U (198 Card S4-18-12-32-Un).3mf
515.1 x 373.5 x 105.0 mm
Pusher x 2
Lid 198U
Lid 198U Unmarked
Holder x 3
RearHolder
