amertner/cardcascade/cascades/Innovation/Innovation Single Mini Unsleeved (XS5.15.10.32-Un).3mf

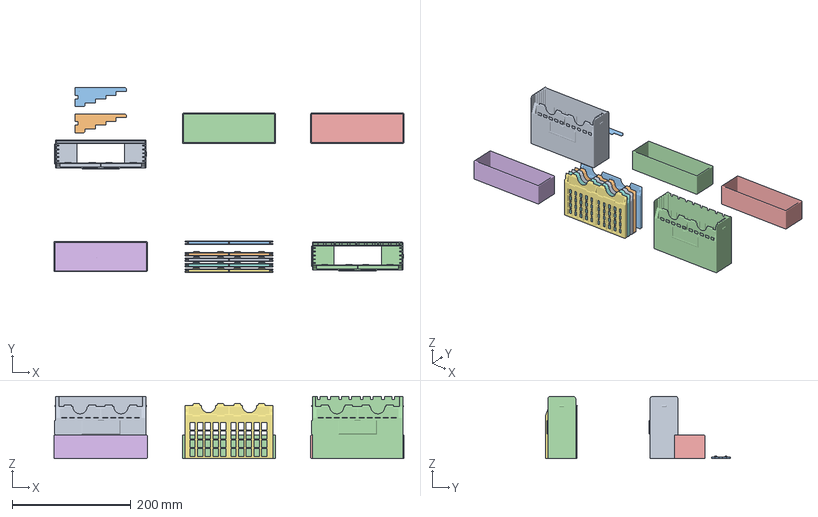
[picture p276: CAD file, 2026-09-14]
cascades/Innovation/Innovation Single Mini Unsleeved (XS5.15.10.32-Un).3mf
588.9 x 310.8 x 105.0 mm
Pusher x 2
Lid 130U
Lid 130U Ultimate
Lid 130U Unmarked
Holder x 4
RearHolder
NotchedBox
