amertner/cardcascade/cascades/Dominion/Pictures/IMG_0968.jpeg

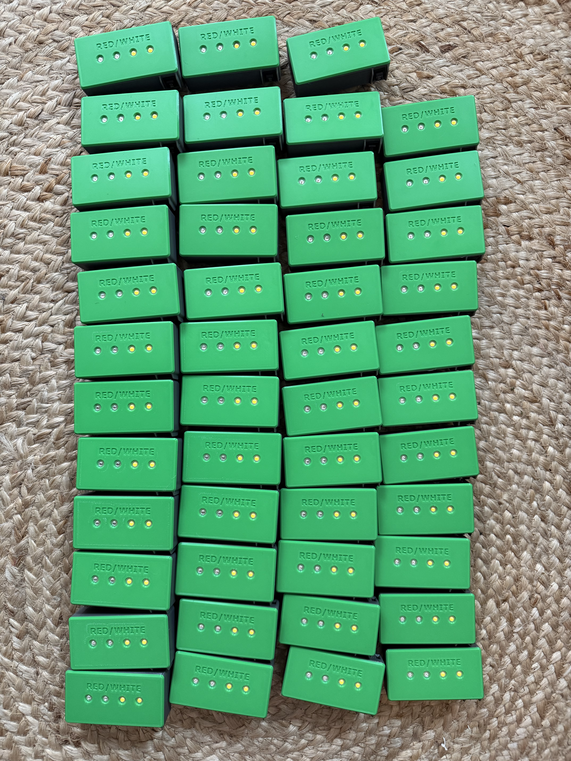
cascades/Dominion/Pictures/IMG_0968.jpeg
