amertner/cardcascade/cascades/Innovation/Photos/v7/3 angled with Echoes topper off.png

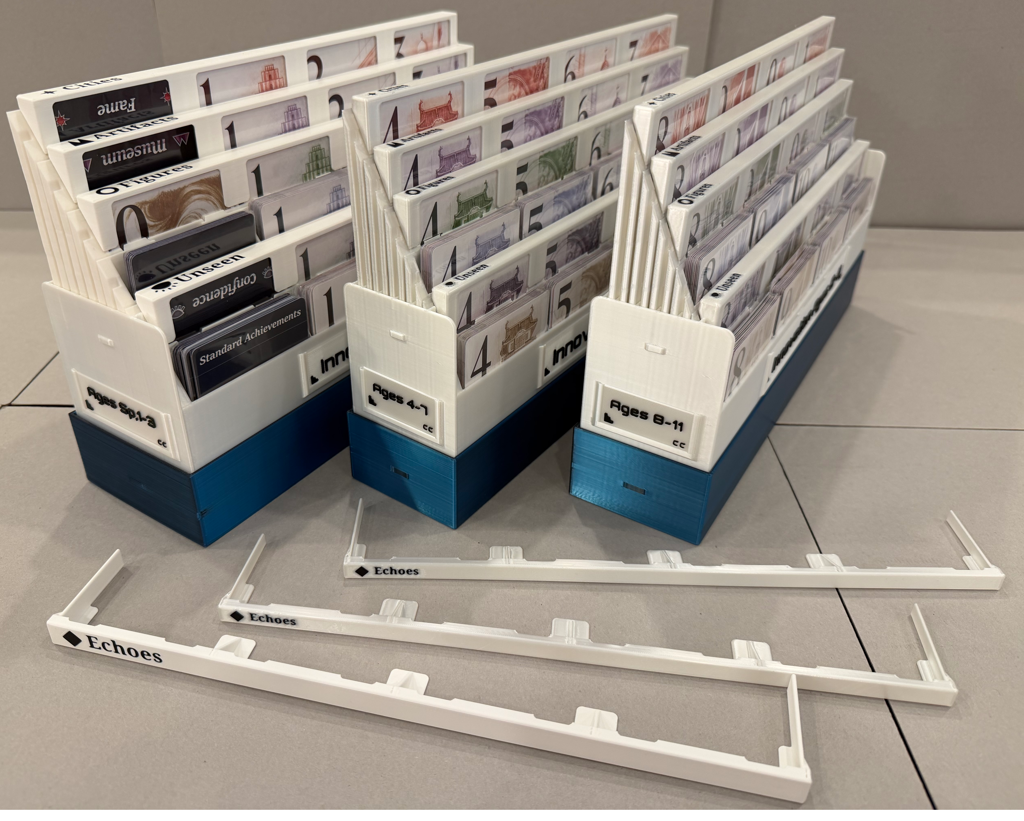
cascades/Innovation/Photos/v7/3 angled with Echoes topper off.png
