amertner/cardcascade/cascades/Photos/IMG_1422.jpeg

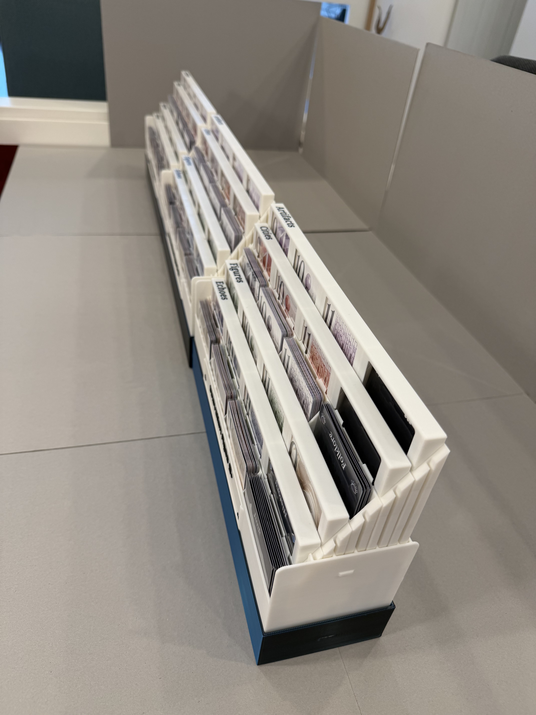
cascades/Photos/IMG_1422.jpeg
